kaanow/volthium_reader/hardware/datasheets/manifest.md

# Datasheet manifest

Local datasheet store for **every active BOM part** (CP1 gate, decisions D32).
Fetched via the parts-sourcing API `/datasheet` proxy where reachable; the rest
pulled manually. Read + interface-verified per D32.

| MPN | file | provider | source | sha256 (12) |
|-----|---|---|---|---|
| 0215001.MXP | 0215001.MXP.pdf (763K) | manual | user download 2026-07-01 | 6ea4fed8f791 |
| MSTBA 2,5/2-G-5,08 (1757242, J1 board header) | 1757242.pdf (1.4M) | parts-API datasheet endpoint | re-fetched 2026-07-30 (replaces the 2026-07-01 user download of the same Phoenix catalog PDF — catalog regeneration changes the hash; dims re-verified p.3: pitch 5.08, pin 1x1, hole 1.4) | 7a342188f10c |
| 2N7002LT1G (onsemi) | 2N7002_onsemi.pdf (2N7002L-D Rev 11) | digikey via API proxy 2026-07-17 | https://www.onsemi.com/pub/Collateral/2N7002L-D.PDF — **F51 fix: the prior 2N7002.pdf was Diotec's (wrong manufacturer for the ordered onsemi SKU); part re-pinned to the exact orderable 2N7002LT1G** (Mouser 863-2N7002LT1G, 76k stock, API 2026-07-17; DK LT1G variants zero-stock same query). IDSS ≤1.0 µA @ TJ=25 °C / ≤500 µA @ TJ=125 °C (60 V, VGS=0) — **25 °C is a test point, not a full-range max** | 11eb3cde5ed5 |
| 615008145521 | 615008145521.pdf (844K) | digikey | https://www.we-online.com/components/products/datasheet/615008145521.pdf | da03e4ed6257 |
| AP2112K-3.3TRG1 | AP2112K-3.3TRG1.pdf (737K) | digikey | https://www.diodes.com/assets/Datasheets/AP2112.pdf | ef8d376f2ec3 |
| B8B-PH-K-S | B8B-PH-K-S.pdf (100K) | digikey | https://www.jst-mfg.com/product/pdf/eng/ePH.pdf | 447624f4f2f7 |
| ESP32-S3-WROOM-1-N16R8 | ESP32-S3-WROOM-1-N16R8.pdf (1250K) | digikey | https://www.espressif.com/sites/default/files/documentation/esp32-s3-wroom-1_wroom-1u_datasheet_en.pdf | 27d71971da07 |
| LM5166YDRCR | LM5166YDRCR.pdf (3436K) | digikey | https://www.ti.com/lit/ds/symlink/lm5166.pdf?ts=1782455459808&ref_url=https%253A%252F%252Fwww.ti.com | 1817a5b4f779 |
| MF-R025 | MF-R025.pdf (1059K) | digikey | https://www.bourns.com/docs/product-datasheets/mf-r.pdf | ad20425ca080 |
| R-78E3.3-0.5 | R-78E3.3-0.5.pdf (628K) | digikey | https://recom-power.com/pdf/Innoline/R-78E-0.5.pdf | d3855b950078 |
| R-78HB12-0.5 | R-78HB12-0.5.pdf (1836K) | digikey | https://recom-power.com/pdf/Innoline/R-78HB-0.5.pdf | 457ccbb2825f |
| RJHSE-5380 | RJHSE-5380.pdf (102K) | digikey | https://cdn.amphenol-cs.com/media/wysiwyg/files/drawing/rjhsex380.pdf | 3254d85eaaa6 |
| RV-3028-C7 | RV-3028-C7.pdf (830K) | manual | user download 2026-07-01 | fb5a01874b3e |
| SMAJ12CA-13-F | SMAJ_Diodes.pdf (116K) | mouser (API proxy) | https://www.mouser.com/catalog/specsheets/ds19005.pdf — Diodes DS19005; p.1 ordering row names SMAJxxx(C)A-13-F (iter-23 F20: non-F variants Obsolete); p.2 device table VC 19.9 V @ 20.1 A | 70bd31105424 |
| SMAJ15A-13-F | SMAJ_Diodes.pdf (same file) | " | " — p.2 device table VC 24.4 V @ 16.4 A, matches D19/DR-15 coordination | 70bd31105424 |
| SMAJ33CA-13-F | SMAJ_Diodes.pdf (same file) | " | " — p.2 device table VC 53.3 V @ 7.5 A, matches the ~53 V clamp coordination (SS26 60 V, R-78HB12 72 V) | 70bd31105424 |
| THVD1400DR | THVD1400DR.pdf (1447K) | digikey | https://www.ti.com/lit/ds/symlink/thvd1400.pdf | 5ba9785d9fb8 |
| SS26-E3/52T | SS26-E3_52T.pdf (151K) | digikey | https://www.vishay.com/docs/88748/ss22.pdf | 4bcd8bc129f3 |
| TPS2116DRLR | TPS2116DRLR.pdf (2855K) | digikey | https://www.ti.com/lit/ds/symlink/tps2116.pdf | 5babd88afb84 |
| TPS3808G01DBVR | TPS3808G01DBVR.pdf (2034K) | digikey | https://www.ti.com/lit/ds/symlink/tps3808.pdf | 682abbc06a0c |
| USBLC6-2SC6Y | USBLC6-2SC6Y.pdf (117K) | manual | user download 2026-07-01 | c0352261dede |
| USB4085-GF-A | USB4085-GF-A.pdf (371K) | API proxy 2026-07-27 (display CP2 — battery J3 + display J-USB USB-C pinned to this GCT SKU) | https://gct.co/files/specs/usb4085-spec.pdf — **FAMILY-level product spec** (electrical/mechanical performance; contains no ordering grid, so it does NOT establish the -GF-A object by itself — F13; see the drawing row below for exact-object identity). VBUS = A4/A9/B4/B9 (5 A collective), GND = A1/A12/B1/B12 — matches the USB_C_16P symbol map | e5e6f4f67cca |
| USB4085-GF-A (exact drawing) | USB4085_drawing.pdf (197K, 3 pp) | direct fetch 2026-07-28 (F13 — browser-UA curl; gct.co serves HTML to bare curl) | https://gct.co/files/drawings/usb4085.pdf — GCT official part drawing WITH ordering grid: **"Dip Type, PCB Top Mount" (through-hole — the BOM's earlier "SMD" cell was wrong, F13), suffix decode GF = Gold Flash (Standard), A = Tape & Reel** → USB4085-GF-A fully identified. Matches the KiCad footprint (20 THT pads, 0 SMD) | 39afb82c5104 |
| NTR4171PT1G | NTR4171P_onsemi.pdf (NTR4171P/D Rev 3, Feb 2026) | digikey via API proxy 2026-07-17 | https://www.onsemi.com/pdf/datasheet/ntr4171p-d.pdf — **3V3-domain switches ×3 (2× channel + Q_exp; F61 replacement: DMG3415U was NRND)**: −30 V, −2.2 A; **RDS(on) max 150 mΩ @ −2.5 V / 75 mΩ @ −10 V** (the −2.5 V guaranteed row qualifies the direct 3.3 V GPIO drive); **VGS ±12 V** (≫ our 3.3 V drive); VGS(th) −0.7…−1.15 V; **IDSS ≤1 µA @ 25 °C / ≤5 µA @ 85 °C** (VDS −24 V — has an elevated-temp row, pessimistic at our −3.3 V). Lifecycle: onsemi page shows **Active** (WebSearch of the mfr page 2026-07-17; onsemi.com WAF-blocks the fetcher — Rev 3 Feb-2026 datasheet + onsemi-channel stock 11k/30k corroborate) | 9ce711ff393d |
| AQY212EH | AQY212EH_Panasonic.pdf (Panasonic GE DIP4 1-Form-A catalog, doc ASCTB126E, 2026.1) | **user upload 2026-07-18 (manufacturer-direct — replaced the octopart mirror; Panasonic host WAF-blocks the proxy)** | Panasonic Industry GE DIP4 1 Form A | — **Display-feed load switch SSR (F76)**: 1-Form-A, **load 60 V / 550 mA**, 5000 Vrms I/O isolation, Ron **0.85 Ω typ / 2.5 Ω max** (AQY212EH row, corrected iter-50 F79 — 0.25 Ω was the AQY211EH sibling), **off-state leakage ≤1 µA @ 25 °C only** (datasheet publishes NO hot max — 85 °C is an engineering estimate gated by a State-4 acceptance test, F83; non-amplifying), LED operate 1.2 mA typ / 3 mA max / turn-off min 0.4 mA, peak load 1.5 A/100 ms one-shot, rated −40…+85 °C. **AQY212EH = through-hole DIP4** (AQY212EHA is the SMD variant). DK 255-2963-ND / Mouser 769-AQY212EH, Active | d329b9729322 |
| MSTB 2,5/2-ST-5,08 (1757019) | 1757019.pdf (2400K) | manual | user upload 2026-07-01 | d849479aae64 |
| LCD1 Waveshare 4.2" e-Paper Module (B) | Waveshare-4.2-ePaper-B.pdf (3.9M — **subordinate bare-panel V2 manual only**, sha 32b126146869: SPI timing, panel specs, active area 84.8×63.6 mm; its p.7 shows the raw 24-contact FPC panel, not the ordered Module). **Module-object evidence (iter-23 F21):** Waveshare-42B-Module-productpage-2026-07-14.html (sha 077451eb4f2f, captured 2026-07-14 from https://www.waveshare.com/4.2inch-e-paper-module-b.htm — "What's on board" + box-contents list **"PH2.0 20cm 8Pin x1"**) + Waveshare-42B-Module-wiki-2026-07-14.html (sha e861c86f6e9f, captured 2026-07-14 from https://www.waveshare.com/wiki/4.2inch_e-Paper_Module_(B)_Manual — 8PIN pin-correspondence tables **VCC/GND/DIN/CLK/CS/DC/RST/BUSY**; FAQ caps cable extension at 20 cm). **Verify at ordering:** the in-box PH2.0 cable's far-end termination — the PH↔PH module↔board cable is a separate BOM purchase (ASPHSPH24K102-class) | 077451eb4f2f / e861c86f6e9f / 32b126146869 |
| 8125SHZBE (BTN1 battery override) | CK_8020_series.pdf (29 pp) | littelfuse via API proxy | https://www.littelfuse.com/assetdocs/littelfuse-c-k-pushbutton-8020-series-datasheet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 — Contact Rating: "B contact material (8X25 Models): 0.4 VA max. @ 20 V AC or DC maximum"; function table 8125 = ON MOM., terminals 1-3 rest / 1-2 pressed; S=plunger, H=0.250" flat bushing, Z=solder lug, E=epoxy seal | 8e748f0b8502 |
| 3517 | Keystone_3517.pdf (170K) | manual | https://www.keyelco.com/userAssets/file/K75p52.pdf | 441b810381ac |
| 970050354 | Wurth_970050354_standoff.pdf | digikey (API proxy) | https://www.we-online.com/components/products/datasheet/970050354.pdf — WA-SBRII brass spacer stud, M3 inner thread, L 5 mm, SW5, nickel | 5530b6984184 |
| 53398-0871 | Molex_53398-0871_PicoBlade_vert.pdf | molex (API proxy) | https://www.molex.com/pdm_docs/sd/533980871_sd.pdf — PicoBlade 1.25 mm, 8-ckt, SMT vertical, tin. **The drawing carries no current rating** — rating comes from the header-system product spec **PS-51021-024** (row below; F53 fix — PS-51021-009 is the wire-to-wire sibling and does not list 53398). R/A alt 53261-0871 (Molex_53261-0871_PicoBlade_RA.pdf, sha 6e1b0968c9ed) | 642bc09ea605 |
| 53398/53261 + 51021/50079/50058 system | Molex_PS-51021-024_PicoBlade_WB_system_spec.pdf (Rev AD, 2022-06-03) | user upload 2026-07-17 | official URL (F59, full): https://www.molex.com/content/dam/molex/molex-dot-com/products/automated/en-us/productspecificationpdf/510/51021/PS-51021-024-001.pdf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 (reviewer-opened iter-35; direct fetch WAF-blocked from this host, hence owner upload) — **PRODUCT SPECIFICATION FOR PICOBLADE 1.25 W/B SMT** (F53): scope p.1 lists terminals 500588\*00/500798\*00, housing 51021\*\*00, **vertical headers 53398\*\*71** (natural; ours) /\*\*76, r/a 53261\*\*71/\*\*27. Ratings p.2: **1.0 A max AWG 26/28/30, 0.8 A AWG 32; 125 V; −40…+105 °C**; 8-ckt derating reference 1.5 A (AWG 26/28) / 1.0 A (AWG 30/32) @ 30 °C rise, marked REFERENCE ONLY | b7d3ec9b74b9 |
| CRCW120675R0FKEAHP | Vishay_CRCW_HP.pdf (150K, doc 20043 rev 17-Mar-2026) | vishay (API proxy 2026-07-19) | https://www.vishay.com/docs/20043/crcwhpe3.pdf — **Pulse-Proof, High Power** thick-film chip R. p.1: 1206-HP rated **P70 = 0.75 W** (the separate 1.5 W is only at terminal-part temp 105 °C), Umax 200 V. p.8 **§8.1 short-term-overload uses P70**: 2.5·√(P70·R)/5 s → **4.69 W/5 s** guaranteed. p.5 single-pulse curve. **R_inrush = 2× 75 Ω in series (F86): 2.87 W each < 4.69 W** (a single 150 Ω 1206-HP would see 5.74 W). | bdd4e4b9b924 |
| 0451.080MRL | Littelfuse_451_453.pdf (480K, rev 12/01/25) | littelfuse (API proxy 2026-07-19) | https://www.littelfuse.com/assetdocs/littelfuse-fuse-451-453-datasheet — 451/453 Nano2® SMF **Very-Fast-Acting** fuse. p.1: 200%→**5 s max** opening. p.2 (**.080 row**): **125 V**, **50 A @125 VDC** interrupt, Rcold 4.05 Ω, **nominal melting I²t 3.3e-4 A²s**. **F2 switched-branch fault clear (80 mA, F87 — 62 mA's pulse I²t ratio was too high).** | 399d3cc9da99 |

## Still needed (CP1 datasheet gate)

**Gate re-opened 2026-07-14 (user audit): the 2026-07-01 "CLOSED — every
active part" claim was false.** RP3502MABLK (BTN1) had no stored
datasheet; when fetched and read it exposed the dry-circuit gap that
reviewer iter-23 F22 then escalated — the part is **superseded by C&K
8125SHZBE** (gold contacts, published 0.4 VA @ 20 V logic-level rating;
see the active-table row). D-OPEN-13 is moot with the supersession
(unsealed accepted for the IP5x indoor enclosure).

Remaining gaps (parts with a chosen MPN but no stored datasheet): none.

- ~~5×20 mm fuse clip~~ — **resolved 2026-07-14 (user-caught).** The BOM's
  SKUs "DK F1465-ND / Mouser 530-31MJ005H" were **phantoms** — zero hits on
  Mouser, DigiKey *and* Octopart via the parts API, and nothing on the
  retailers' own sites (user check). Replaced with **Keystone 3517**
  (5 mm/3AG PC-mount snap-in clip w/ end stops, tin-plated brass,
  UL E354010): DK **36-3517-ND** (85,711 in stock, Active) / Mouser
  **534-3517** (54,324 in stock), ~CA$0.48 ea. Datasheet fetched, read,
  verified: 5 mm fuse diameter ✓ (fits the 5×20 0215001.MXP body), THT
  snap-in legs, end stops (with-end-stop parts are the UL-recognized
  ones), rated ≥ 6.3 A ≫ 1 A fuse. Optional cover = 3517C.

Parts still at `_verify_` (MPN not yet chosen — D32 applies when chosen):
L1 buck inductor, USB-C receptacles (J3 battery / J-USB display),
display tactile buttons BTN1–3 (plunger height locked at CP3/CP5).

## Proposed CP1-delta additions (D36/D37) — datasheets on file, fold into the active table at CP2

Not yet in the active table above (these parts are in the RS-485 /
expansion design docs, pending the CP1-delta review; they move to the
active table + `cp1_bom.md` when CP2 folds them in). Datasheets stored,
read, and interface-verified now so the D32 gate closes when they land.

| MPN | file | provider | source | sha256 (12) | read-verified |
|-----|---|---|---|---|---|
| ADM2587EBRWZ | ADM2582E_2587E.pdf (1291K) | user upload 2026-07-16 | analog.com/media/en/technical-documentation/data-sheets/adm2582e-2587e.pdf (Rev H) | 77a52a9e6036 | 2500 Vrms iso (1 min); CMTI >25 kV/µs; ±15 kV ESD on bus pins; open/short fail-safe RX (external bias unnecessary, p.15); 3.3 V op; **ADM2587E = 500 kbps** slew-limited; **ICC 90 mA @ 3.3 V/100 Ω** (72 mA is the 5 V row — iter-30 F28 fix); supplies ~15 mA on VISOO; isoPower support net p.8/p.17 → design §3 |
| SM712.TCT (Semtech) | SM712_Semtech.pdf (557K) | user upload 2026-07-16 | Semtech SM712 Final Rev 6.0 (semtech.com) | 6deb75310ebe | **F29 CLOSED 2026-07-16 — correct-manufacturer Semtech doc** (was briefly SMC's, wrong mfr). VRWM 12/7 V; VBR 13.3/7.5 V; **VC 20 V/10 V @ 5 A** (26 V @ 21 A); SOT-23, asymmetric RS-485 (−7/+12). Matches ordered 947-SM712.TCT / SM712CT-ND. **DNP — port intentionally unprotected (F44):** VC 20 V > ADM2587E +14 V abs-max and no published injection rating exists to size a series R against; no coordinated network is claimed |
| 51021 wire-to-wire system (scope: 51021 housing + 50079/50058 terminals + 51047 plug — **does NOT list 53398**) | Molex_PS-51021-009_PicoBlade_product_spec.pdf (393K) | digikey via API proxy 2026-07-16 | https://www.molex.com/pdm_docs/ps/PS-51021-009.pdf | 1213f6f54215 | **Wire-to-WIRE product spec** (F53 scoping: retained only for what it covers — the 51021/50079 mate side as used in cable assemblies; the header-system claims cite PS-51021-024 above). §3 ratings 1.0 A max (AWG 26/28/30), 0.8 A (AWG 32), 125 V, −40…+85 °C |
| TCAN332DR | TCAN332.pdf (1645K, SLLSEQ7F Rev May 2025) | parts-API /datasheet proxy 2026-07-22 | https://www.ti.com/lit/ds/symlink/tcan332.pdf | aeda66d5fca9 | U7 Xanbus CAN transceiver (DR-31); pinout + supply-current + unpowered-high-Z interface-verified (pp.1/4/6); **p.5 abs-max V(BUS) ±14 V + on-chip bus ESD ±25 kV HBM / ±12 kV IEC contact (F03 basis)** |
| NUP2105LT1G (onsemi) | NUP2105L_onsemi.pdf (13 pp, Rev 12 June 2026) | parts-API /datasheet proxy 2026-07-24 | https://www.onsemi.com/pdf/datasheet/nup2105l-d.pdf | bf93369469d4 | D2 candidate CAN TVS, **now DNP (CP2 F03)**: p.2 V_RWM 24 V, V_BR 26.2–32 V, V_C 40/44 V max @5/8 A — cannot bracket TCAN332's ±14 V; kept on file as the evidence for the DNP call. (Note: the bare "NUP2105L" MPN resolves to a Diotec second-source PDF at DigiKey — query the orderable NUP2105LT1G for the onsemi doc) |
| ESP-Prog (tool, not BOM) | ESP-Prog_SCH_V2.1.pdf (609K, SCH_ESP32-PROG_V2.1_20190709) | espressif direct 2026-07-24 | https://dl.espressif.com/dl/schematics/SCH_ESP32-PROG_V2.1_20190709.pdf | ab1f074c7b6c | J5 Program-pinout ground truth (F01): J3/J5 2×3 = 1 ESP_EN / 2 VDD / 3 ESP_TXD0 / 4 GND / 5 ESP_RXD0 / 6 ESP_IO0; **FT_TXD→0R→ESP_RXD0, FT_RXD→0R→ESP_TXD0** (names are target-perspective — pin 3 takes the target's TXD) |
| MPZ2012S601AT000 | TDK_MPZ2012S601AT000.pdf (MPZ2012 type catalog, 20190424) | parts-API /datasheet proxy 2026-07-24 | https://product.tdk.com/system/files/dam/doc/product/emc/emc/beads/catalog/beads_commercial_power_mpz2012_en.pdf | c8b428baaacf | L10–L13 iso beads. p.1 table: S601A = 600 Ω ±25 % @100 MHz, DCR 0.100 Ω max, **rated 2 A** (derates above 85 °C). p.2 Z/f curve (S601A): **~600 Ω near the 150–200 MHz peak, falling to ~300–400 Ω by ~400 MHz** — DR-30 bead-impedance data: no MPZ2012 reaches the ADM2587E p.17 "~2 kΩ" guidance (family max = S102A 1 kΩ/1.5 A/0.15 Ω, an available same-size step-up at BOM-lock) |
| C1206C102KDGACTU | KEMET_C1206C102KDGACTU.pdf (KEM_C1009 C0G HV SMD, 12/16/2024) | parts-API /datasheet proxy 2026-07-24 | https://yageogroup.com/content/datasheet/asset/file/KEM_C1009_C0G_HV_SMD | 46031e2efdb6 | C28/C38 C_stitch. High-Voltage C0G series doc: 500 V–10 kV DC ratings incl. **1 kV 1206**, −55…+125 °C, ±30 ppm/°C — the 1 kV/C0G claims in the BOM row are this doc's |
| 61200621621 | Wurth_61200621621.pdf (WR-BHD male box header drawing, rev 002.001 2026-07-07) | parts-API /datasheet proxy 2026-07-24 | https://www.we-online.com/components/products/datasheet/61200621621.pdf | 6474a7ec48fc | J5 ESP-Prog Program header (F01): 6-pin 2.54 mm shrouded/keyed box header, **standard IDC odd/even numbering (1/3/5 one row, 2/4/6 other — matches Conn_02x03_Odd_Even + the ESP-Prog ribbon 1:1)**, THT, hole pattern p.1. **CP3 note: set key-notch orientation at placement so ribbon pin 1 = our pin 1** |

## Retired (in store history, not used)

- SI2309CDS_Vishay.pdf (feb0974dd371), MMBT5551_onsemi.pdf (3ae47cf6f802),
  BZX84C12LT1G.pdf (f9818d9dfc03) — retired iter-48 (F76): the discrete
  Q1 P-FET + Q2 BJT gate-driver + Zener were replaced wholesale by the
  AQY212EH PhotoMOS SSR (no discrete driver could be datasheet-guaranteed
  OFF at temperature — see decisions.md D19). PDFs kept as F57/F68/F72
  evidence; can be removed at the next housekeeping pass.

- ZXMP6A13FTA.pdf (bb474f827be4) — retired iter-38 (F56/F57): part NRND,
  no guaranteed RDS(on) at a 3.3 V gate drive → Si2309CDS (Q1) +
  DMG3415U (3V3 switches).
- DMG3415U_Diodes.pdf (3863b974014c) — retired iter-40 (F61): Diodes
  marks it **NRND** despite live distributor stock (the distributor
  "Active" field is stale — G3 lesson) → onsemi **NTR4171P** for the
  three 3V3-domain switches. Q1's Si2309CDS is unaffected.

- **RP3502MABLK** (BTN1) — retired at reviewer iter-23 F22 (2026-07-14):
  AC power switch (3 A @ 120 VAC) with **no published dry-circuit /
  minimum-load rating**; unqualifiable for the 3.3 V/µA override input,
  and the C11 100 nF discharge (0.54 µJ) is not a vendor wetting
  qualification. Superseded by **C&K 8125SHZBE** (explicit "0.4 VA max
  @ 20 V" low-level rating, gold contacts). PDF removed.

- **SMAJ12CA.pdf (Bourns) / SMAJ15A.pdf + SMAJ33CA.pdf (one Littelfuse
  family PDF stored under two names — identical sha)** — retired
  2026-07-14 audit: the datasheets on file were from manufacturers we
  don't order (BOM DK SKUs are **Diodes Inc** SMAJxxCA-13). Replaced by
  the single Diodes DS19005 family datasheet matching the orderable
  parts; per-variant VC values re-read from it and confirmed identical
  to the values used in the D19 coordination analysis. PDFs removed.

- **1727010** (Phoenix MKDS 1/2-3,81) — was mistakenly specced as the J1 plug; it's a 3.81 mm board-mount screw terminal, wrong series/pitch. Replaced by 1757019 (2026-07-01, D32 catch). PDF removed.
- **TPS389030DSER** (U4 UVLO supervisor) — WSON 1.5×1.5 leadless; repackaged to **TPS3808G01DBVR (SOT-23-6, leaded)** for hand-assembly (2026-07-01, D33/DR-24). Functional superset at ~same Iq. PDF removed.
- **SN65HVD3082EDR** (U2/U3 RS-485 transceiver) — was a 5 V part being run outside its recommended VCC = 4.5–5.5 V window on V3V3 (reviewer iter-8 F05). Superseded by **THVD1400DR** (D34, revised iter-10 F08). PDF retained temporarily in `hardware/datasheets/SN65HVD3082EDR.pdf` as the record of the F05 evidence — can be removed at the next housekeeping pass once the review record is archived.
- **ISL3175EIBZ** (U2/U3 RS-485 transceiver) — iter-8 first-cut replacement for SN65HVD3082E, but iter-10 F08 correctly caught that its 10 nA shutdown Iq was *typical* and the maximum is 12 µA (1200× higher). Superseded by **THVD1400DR** on max-to-max comparison. PDF retained temporarily in `hardware/datasheets/ISL3175EIBZ.pdf` as the record of the iter-10 max-to-max evidence — can be removed once the review record is archived.
