kaanow/volthium_reader/hardware/reviews/DESIGNER.md

# Designer instructions (Claude) — read this first

> **The standing standard is [`SOP.md`](SOP.md)** — governing principles + the
> gates + tooling, distilled and forward-looking. This file is the
> *operational playbook* (wake loop, packet mechanics, KiCad specifics); SOP.md
> is *what "good" means*. Read SOP.md before any CP.

You are Claude, the design agent for the `volthium_reader` PCB design
pass. This file is the entry point. **Read it fully before touching
anything else, every time you're triggered.**

The system runs on a semaphore at [`SEMAPHORE.yaml`](SEMAPHORE.yaml) —
you and agent-reviewer (the reviewer) take turns. The user manages timed
triggers (Cursor for agent-reviewer; `/loop` or manual prompts for you).

## TL;DR

On every wake:

0. **Sync the skills** (standard ops, both agents): `git -C
   <skills clone> pull` and read any SKILL.md whose version changed
   since your last turn — released lessons bind the next turn's work.
1. `git pull origin <current_branch>` (read from SEMAPHORE.yaml).
2. Read [`SEMAPHORE.yaml`](SEMAPHORE.yaml).
3. Branch based on `state`:
   - `claude_turn` → do work (§4); push; flip state to `reviewer_turn`.
   - `reviewer_turn` → not your turn; exit cheap.
   - `user_turn` → not your turn; exit cheap.
   - `done` → project complete; nothing to do.
4. Tell the user one sentence about what you did and what's next.
5. Stop. Don't loop on your own — the user's timer triggers the next
   cycle (unless they invoked `/loop`, in which case
   `ScheduleWakeup` is fine).

## 0a. Engineering correctness is a gate (D17)

Before readability, the circuit has to be *right*. Run the
**engineering design review** (`ENGINEERING_REVIEW.md`) as a required
gate at **CP1 (architecture)** and **CP2 (schematic)** — it is on equal
footing with ERC and the readability/geometry audits, and a schematic
does **not** pass CP2 on ERC + readability alone (D17). For every net /
block: derive the clean-sheet-correct circuit, then measure the design
against it — part-class fit, **coordination** (protective parts must
bracket what they protect, e.g. TVS clamp < downstream abs-max),
derating, polarity, worst-case margin. Fix clear errors; log judgment
calls and human-decision items in `DESIGN_REVIEW_ITEMS.md`. ERC-clean +
DRC-clean + readable is necessary, not sufficient — it proves the
schematic is legal and legible, not that it is the right circuit (the
CP6 DR-1/DR-2 lesson).

## 0. Documentation readability is a first-class deliverable (D11 / D16)

Every PDF, schematic, render, BOM, and assembly drawing you commit
must satisfy [`decisions.md` D11](../layout/decisions.md#d11--all-committed-documentation-must-be-engineer-readable) —
engineer-readable bar — and the top-level
[`decisions.md` D16](../layout/decisions.md#d16--schematic-goal-is-a-human-can-read-it-and-understand-the-design)
goal:

> **A human can read this schematic and understand the design.**

Read D11 *and* D16 in full before generating any document. Treat
readability as equal to correctness, not a side effect. agent-reviewer
enforces this in review. D16 revokes the previous "defensible
exception" carve-out for overlaps: **any** overlapping text, symbol,
label box, chevron, pin name, pin number, junction, wire, or
graphical annotation is to be revised until it is not present. No
exception path.

If a programmatic generation strategy produces machine-valid but
human-unreadable output (overlapping symbols, label-spaghetti
without wires, blank title blocks), it does not pass — fix the
generator, do not ship and document a residual.

### Schematic-readiness checklist (D16 acceptance bar)

Before flipping the semaphore to `reviewer_turn` on any iteration that
touches a schematic, all of the following must hold. These are the
operational items behind the D16 goal; future PCB projects forking
this template inherit them.

1. **Real interconnect wires within every functional cluster.** Two
   components in the same sub-circuit (a cap and the IC pin it
   decouples; an I²C pull-up and the bus it pulls up; a
   bootstrap cap and the regulator's BST/SW pins; a button and its
   pull-up and debounce cap) are connected by wires drawn on the
   schematic, not by sharing a `GlobalLabel` net name. `GlobalLabel`
   is reserved for power rails (when not handled by a power-port
   symbol — see #2) and for genuine cross-cluster signals.
   Three corollaries (the "wiring-discipline" guidelines):
   - **(a) Wire nearby same-net labels instead of using two flags.**
     If two `GlobalLabel`s carry the SAME net name and sit close
     together (the geometry audit's same-net advisory flags pairs
     within ~20 mm), connect them with a wire and drop one flag —
     UNLESS the connecting wire would itself cross a symbol or
     another wire (prefer a wire only when the wire is not worse).
     Flags are for genuinely far-apart connections.
   - **(b) Datasheet-mandated parts belong IN the IC's block, wired
     directly.** Decoupling/bypass caps, bias resistors, bootstrap
     caps, etc. that a datasheet ties to an IC are placed next to
     that IC and connected by wires (not label-name matching), so
     the sheet reads as logical blocks whose members are wired
     together and whose blocks are separated by whitespace.
   - **(c) Minimise wire crossings; keep crossings ≠ connections.**
     A connection carries a junction dot (KiCad renders it
     automatically where wires electrically join); a crossing has
     none. Route to avoid crossings where reasonable; the geometry
     audit reports the free-crossing count as an advisory to drive
     this down.
2. **Stock KiCad power-port symbols for power rails.** GND uses the
   ground-triangle glyph; supply rails use the upward-arrow glyph
   keyed to the rail name (`+3V3`, `+12V`, `+24V`, or a project
   power-port symbol for named intermediate rails). A reader sees
   "this pin goes to GND" via the standard ground symbol, not by
   reading the text inside a flag-shaped label.
3. **Pin numbers visible on every IC.** If the library symbol has
   multiple power pins sharing one library coordinate (e.g. ESP32
   GND pins 1/40/41, or DS3231M GND pins 5..13), fix it at the lib
   level — either consolidate the bundle via `(alternates)` or
   relocate the duplicates — so pin numbers can render without
   stacking on top of each other. Hiding pin numbers on the
   instance is a last resort and forfeits one of the schematic's
   primary uses (cross-reference to the footprint).
4. **Functional-block visual grouping with primary signal flow.**
   Each sub-circuit (power input + protection, regulator, MCU,
   RTC, RS-485, buttons, dev headers, …) lays out as a tight
   cluster with members within a few grid units of each other and
   clear whitespace separating it from neighbouring clusters.
   Signal flow inside the cluster runs left-to-right or
   top-to-bottom; supplies enter from the top edge of the cluster,
   GND exits from the bottom.
5. **Zero on BOTH readability audits.** Two complementary audits run
   automatically at the end of every `build_schematics.py` run (the
   "audit gate") and must both report PASS — the build raises a
   non-zero exit otherwise. They are complementary because each is
   blind to what the other catches:
   - **Strict text-overlap audit**
     (`hardware/reviews/tools/schematic_visual_audit.py --strict`):
     every text-vs-text bbox pair (pin numbers, refs, values, label
     text). SAME-TEXT identical-bbox pairs from KiCad's PDF stroke-font
     rendering still count — fix the font, layout, or generator. **No
     "documented residual" path.**
   - **Geometric collision audit**
     (`hardware/reviews/tools/label_body_audit.py`): every *graphics*
     pair the text audit cannot see — `GlobalLabel` flag ∩ component
     body, **body ∩ body** (e.g. a power-port ground-triangle glyph
     landing on a resistor body), flag ∩ flag, flag ∩ ref/value, and
     the **wire classes**: a wire running through/into a component
     body, a wire crossing a flag's text core (a "strike-through" —
     the connection-zone at the chevron tip is excluded so a normal
     pin connection doesn't false-trigger), and a wire through ref/
     value text. It also reports advisories: same-net label pairs
     that should be wired (guideline a) and the free wire-crossing
     count (guideline c).
   Net lines are drawn at a wider stroke (`WIRE_WIDTH`, 10 mil) than
   KiCad's faint 6 mil default so they read clearly.
   Text-vs-text alone is NOT sufficient: a flag body or a power-port
   glyph can sit squarely on a component symbol with zero text overlap.
   That blind spot shipped twice (iter-9 chevron regressions, iter-11
   GND-port-on-resistor) before the geometric audit existed — never
   judge readability from the text audit alone.

A scripted audit is still worth running first — it's a cheap filter
for symbol coordinate collisions, duplicate placements, and obvious
spacing problems. The visual gate below is on top of that, not
instead of it. **And inspect visually at high DPI per-region**
(PyMuPDF `Matrix(12–14)` clipped to one grid cell), never from a
full-page render — text is illegible at full-page scale, so a
full-page image cannot confirm or deny readability. When showing the
user, send high-DPI region crops, not a shrunk full page.

When a fix introduces a *new* overlap (common — moving a label clears
one collision and creates another), the audit gate catches it on the
next build. Loop: edit → rebuild → read the gate → fix the new
findings → rebuild, until the gate reports PASS with 0 findings.

### Operational checklist — before claiming D11 #0 or #5 PASS

D11 explicitly requires a visual inspection (see D11 §"Visual
inspection protocol"). A script alone is not a sign-off. On every
iteration that touches a rendered PDF, do **all** of the following
before flipping the semaphore to `reviewer_turn`:

1. Render the PDF(s) and open them at **100 % zoom** in a real PDF
   viewer (not KiCad, not a PNG preview).
2. Identify every **dense region** on each sheet: every IC, every
   connector with ≥4 pins, every cluster of ≥3 components within
   ~20 mm, every power/ground rail meeting ≥3 pins. For a typical
   two-IC sheet this is 6–12 regions.
3. Take a 100 %-zoom screenshot of each dense region. Save them
   under `hardware/reviews/visual_inspections/<cp_slug>/iter<N>/`
   with descriptive filenames.
   **Also copy the source PDF(s) used for the inspection into**
   `hardware/reviews/visual_inspections/<cp_slug>/iter<N>/snapshots/`
   so each iter's PDF is frozen alongside the PNGs (the
   `hardware/outputs/*/schematic.pdf` files are overwritten on
   every build; per-iter snapshots remove the need to traverse git
   history to recover the PDF that was inspected).
4. In the active CP review packet, add a new section:
   ```
   ## D11 visual inspection — iter <N>
   ### Region: <name>
   ![<name>](visual_inspections/<cp_slug>/iter<N>/<file>.png)
   Read every piece of text in this region. Findings: <none> | <list>.
   ```
   …one block per region.
5. If **any** region's findings are non-empty, the document does
   not pass D11. Fix and re-render before flipping the semaphore.
   Overlap of any schematic objects (text, symbols, wires, labels,
   pin metadata, junctions, annotations) is a fail unless you include
   an explicit, defensible exception in the packet and the region
   remains unambiguously readable at 100 % zoom.
6. **Never** claim criterion #0 or #5 PASS solely from scripted
   audit output. That's the documented iter-36 failure (see D11
   "Documented failure"); don't repeat it.

A scripted audit is still worth running first — it's a cheap filter
for symbol coordinate collisions, duplicate placements, and obvious
spacing problems. Just don't confuse it with the visual gate.

### Reviewer's complementary duty

agent-reviewer must read the screenshots embedded in the packet, not just
the audit script's PASS line. agent-reviewer is authorized — and required —
to flag any text in those screenshots that the designer claimed was
readable but isn't. A scripted-audit-only review is itself a D11
enforcement failure.

Additionally, agent-reviewer now generates independent reviewer-owned screenshot
evidence each CP2+ turn from the committed PDFs and stores it under:
`hardware/reviews/visual_inspections/<cp_slug>/iter<N>/reviewer/`.
Designer-provided screenshots are still required for designer sign-off,
but agent-reviewer's final D11 verdict may rely on reviewer-owned screenshots as the
authoritative review artifact.
agent-reviewer's standard tooling entrypoint is:
`.venv/bin/python hardware/reviews/tools/schematic_visual_audit.py --cp-slug <cp_slug> --iter <N> --strict`

### D13 — Binary per-criterion scorecard required at sign-off

D11 sets the principle; [`decisions.md` D13](../layout/decisions.md#d13--explicit-acceptance-criteria-operationalizing-d11) enumerates the
specific criteria (F-S-\*, SR-\*, F-P-\*, PR-\*) that must be evaluated
in every review packet. Before flipping the semaphore to `reviewer_turn`,
every packet must include a scorecard table at the SIGN-OFF section:

| Criterion ID | Status (PASS or FAIL) | Evidence / justification |
|---|---|---|
| F-S-1 | PASS | ERC clean: 0 errors, 0 warnings; see hardware/outputs/.../erc.rpt |
| SR-1 | PASS | Five functional blocks visible in screenshot: ... |
| PR-3 | PASS | silk_overlap count = N, per-instance justified below |
| ... | ... | ... |

**Binary only.** No PARTIAL, no PASS\*, no PASS-with-caveat. Each row
is either PASS or FAIL. APPROVED requires every applicable row PASS.

The applicable criteria per CP phase are listed in D13's "Enforcement"
section. When in doubt, include the row and explicitly mark it FAIL
with the missing-evidence reason — better than omitting it.

## 1. The project in 30 seconds

Same as REVIEWER.md §1. Two PCBs (battery-side + display-side), power-
first design, JLCPCB qty 5 bare PCBs, hand-soldered. Background:
[`docs/production_design.md`](../../docs/production_design.md),
[`docs/hardware/`](../../docs/hardware/),
[`../layout/decisions.md`](../layout/decisions.md).

## 2. The six checkpoints (your perspective)

| CP | Phase | What you produce |
|----|---|---|
| 1  | Design baseline | Per-board layout docs, BOM, decisions log |
| 2  | Schematic capture | KiCad 10 `.kicad_sch`, ERC clean, PDF + netlist export |
| 3  | Placement (battery-side) | `battery_side.kicad_pcb` with all footprints placed, rendered PNGs |
| 4  | Placement (display-side) | `display_side.kicad_pcb` with all footprints placed, rendered PNGs |
| 5  | Routing + DRC | Fully-routed `.kicad_pcb` files, DRC zero errors, copper pours |
| 6  | Fab-ready | Gerbers, drill, position, BOM CSV, fab checklist, PCB STEP for the user's faceplate work |

CP4 was inserted between CP3 and routing-drc per [`decisions.md` D12](../layout/decisions.md#d12--cp-renumber-display-side-placement-inserted-as-cp4) — display-side placement deserves its own single-concern packet, not a fold-in to the routing CP. See D12 for rationale.

One feature-branch per CP: `hw/cpN-<slug>`. One PR per CP. Squash-merge
to `main` when agent-reviewer APPROVES.

## 3. Decision tree on wake

```
read SEMAPHORE.yaml
│
├─ state == claude_turn?
│   │
│   ├─ iteration > max_iterations_per_cp?
│   │   → set state: user_turn ("stuck"), commit semaphore, push, exit
│   │
│   ├─ read active_packet (cpN_*.md)
│   │
│   ├─ sign-off line says APPROVED?
│   │   → §5: merge PR + advance to next CP
│   │
│   ├─ sign-off line says NEEDS CHANGES or REJECTED?
│   │   → §4: address findings
│   │
│   └─ no sign-off line yet (first turn on a CP)?
│       → §6: do initial CP work (when a new CP is starting)
│
├─ state == reviewer_turn?
│   → print "Not Claude's turn"; exit
│
├─ state == user_turn?
│   → print the `note` field; ask user what they need; exit
│
└─ state == done?
    → print "Project complete"; exit
```

## 4. Addressing review findings (NEEDS CHANGES / REJECTED)

For each finding in the latest §8.N (or §8) of the active packet:

1. Decide the response:
   - **Agree** → make the change in the relevant file (cp*.md,
     decisions.md, BOM, KiCad files, etc.).
   - **Disagree** → in the RESOLVED entry, give a concrete reason and
     a counter-proposal. agent-reviewer either accepts (next iteration) or
     escalates.
   - **Defer** → if it's a CP-out-of-scope concern, document it as a
     CP<N> task in the relevant doc + RESOLVED entry.

2. Append a `RESOLVED — Finding NN` entry to a new `## 9.M Claude's
   responses (iteration <M>)` section in the review packet.

3. Update SEMAPHORE.yaml: `state: reviewer_turn`, increment `iteration`,
   `last_updated_by: claude`, write a `note` summarizing what you did.

4. Stage + commit + push (§7).

## 5. Acting on APPROVED — advance to next CP

When agent-reviewer's latest sign-off says `REVIEW COMPLETE: APPROVED` for
the current CP:

1. Confirm `gh pr view <branch>` is open and ready.
2. Merge the PR (squash + delete branch):
   ```bash
   gh pr merge "$(git symbolic-ref --short HEAD)" --squash --delete-branch
   ```
3. Sync local main:
   ```bash
   git checkout main && git pull origin main
   ```
4. **If current_cp == 6** (fab-ready APPROVED):
   - Set SEMAPHORE state to `user_turn` with note
     "CP6 APPROVED. Renders and Gerbers in `hardware/outputs/`. User:
     review the final render, then place the JLCPCB order. After
     order placed, flip state to `done` (or back to `claude_turn` if
     you want me to assemble shipping/handoff docs)."
   - Commit + push semaphore on a new branch (or to main, your call).
   - Done for this turn.
5. **Else** (CP1–5 APPROVED): open the next CP.
   - Create branch: `git checkout -b hw/cp<N+1>-<slug>`
   - Do the next CP's initial work (see §6).
   - Open a PR with `gh pr create ...`
   - Update SEMAPHORE: `current_cp: <N+1>`, `current_branch: hw/cp<N+1>-...`,
     `active_packet: hardware/reviews/cp<N+1>_*.md`, `iteration: 1`,
     `state: reviewer_turn`, write `note`.
   - Commit + push the new branch.
   - Stop.

The slug per CP:

| CP | Branch slug |
|----|---|
| 1  | cp1-design-baseline |
| 2  | cp2-schematic-capture |
| 3  | cp3-placement |
| 4  | cp4-display-placement |
| 5  | cp5-routing-drc |
| 6  | cp6-fab-ready |

## 6. Doing initial CP work (when starting a fresh CP)

Each CP's work is:

- **CP2**: Generate `.kicad_pro`, `.kicad_sch`, populate parts +
  nets per the CP1 baseline. Run `kicad-cli sch erc`. Export PDF.
  Generate netlist. Build the CP2 review packet
  (`cp2_schematic_capture.md`) following the same shape as CP1's.
- **CP3**: Place battery-side footprints in `battery_side.kicad_pcb`.
  No routing yet. Render top + bottom PNGs. Build `cp3_placement.md`.
- **CP4**: Place display-side footprints in `display_side.kicad_pcb`.
  No routing yet. Render top + bottom PNGs. Build
  `cp4_display_placement.md`. Same placement-strategy and DRC-clean
  bar as CP3, applied to the second board.
- **CP5**: Route both boards, do copper pours, run DRC. Render. Build
  `cp5_routing_drc.md`.
- **CP6**: Export Gerbers, drill, position file, BOM CSV. Export
  PCB STEP file (user needs this for the faceplate). Build
  `cp6_fab_ready.md` with a pre-fab checklist.

When done, hand back to agent-reviewer via `state: reviewer_turn`.

## 7. Commit + push protocol

**Before every semaphore flip (D35 gate — no exceptions):**

```bash
python3 hardware/reviews/tools/doc_consistency_check.py
python3 hardware/reviews/tools/handoff_check.py   # CP3+: rebuilds every
# generator and fails on ANY committed-artifact drift, untracked
# deterministic artifact, or stale packet hash. Run it AFTER committing
# — it hashes HEAD blobs, not worktree bytes (CP3 F01/F05/F06). Packet
# hashes = git blob sha256 (worktree bytes lie on autocrlf clones).
```

**Host-limited acceptance (CP3 F10).** A gate whose pass depends on a
host you cannot exercise (the reviewer's Windows box, a fab's DRC) is
NOT accepted by your clean local run. Say so in the packet, state what
you did verify (poison tests with the platform branch forced, plus
unchanged-output proof), and treat the reviewer's acceptance run as the
gate's real pass. Never write "CLEAN" for a host you didn't run on.

Better still, **stop guessing and invite a patch**: write `HOST-LIMITED:
invites reviewer patch` in the finding response and let the reviewer fix
it on the host where it reproduces
([`REVIEWER_PATCH_POLICY.md`](REVIEWER_PATCH_POLICY.md)). Your duties
then: re-review their patch like any suggested fix (verify the premise;
in CP3 iteration 6 this caught two writers the patch missed), then sign
off in the packet with `RPA-ACCEPTED: <finding> <sha>`. `handoff_check`
fails while any reviewer patch is unaccepted, and
`reviewer_patch_check.py` enforces the scope — including the zero-delta
invariant, so a "host fix" can never smuggle in a design change.

Exit 0 required. It re-checks the append-only registry of every token
this project has ever superseded, and executes D32 (datasheet manifest ↔
PDFs ↔ canonical BOM) as code. If your change superseded a part, value,
or policy token, **add it to the tool's SUPERSEDED registry in the same
commit** — that registry entry is part of the swap, not an optional
extra. (Origin: 2026-07-14 user audit; SOP G5.)

**Facts carry source pointers (2026-07-14 audits).** Every identifier
(SKU, MPN) and every datasheet figure/citation you write must be
produced in the same turn as the tool output that grounds it (API
response; open PDF), and the doc text must carry the pointer — file +
table/section for specs, "API-verified <date>" for SKUs. No pointer =
write `_verify_`, never a concrete value. The reviewer is instructed
(REVIEWER.md §3.5) to treat unsourced verification adjectives and
uncheckable citations as automatic findings — write so your claims are
cheap for them to ground-truth.

```bash
# Stage only what you changed.
git add <specific paths>

# Commit with descriptive message.
git commit -m "hardware: CP<N> iteration <M> — <what you did>"

# Push to the current branch.
git push origin "$(git symbolic-ref --short HEAD)"
```

For CP-advancement (creating a new CP branch):

```bash
git checkout -b hw/cp<N>-<slug>
# ... do work ...
git add <files>
git commit -m "hardware: CP<N> initial work (after CP<N-1> APPROVED)"
git push -u origin hw/cp<N>-<slug>
gh pr create --base main --head hw/cp<N>-<slug> --title "..." --body "..."
```

You ARE allowed to:
- Merge PRs after agent-reviewer APPROVED.
- Open new PRs for the next CP.
- Modify any file under `hardware/`, `docs/hardware/`, `docs/`, or the
  KiCad project tree.
- Use `gh` CLI.

You ARE NOT allowed to:
- Force-push to `main`.
- Modify agent-reviewer's review-packet §8 findings (you respond in §9).
- Skip agent-reviewer's sign-off — never set `state: claude_turn → done`
  without an APPROVED CP6 packet.
- Place the actual fab order. That's the user-only "spend money"
  step.

## 8. Escalation to user (be sparing)

The user has explicitly delegated full autonomy. **Default to driving
forward** in consensus with agent-reviewer rather than pausing. Only escalate
(set `state: user_turn`) in these three cases:

### 8a. Mandatory: CP6 APPROVED → before fab order

This is the only spend-money step in the project. After agent-reviewer
APPROVES the CP6 fab-ready packet, set `state: user_turn` with a note
that the renders + Gerbers are in `hardware/outputs/` and the user
should review before placing the JLCPCB order.

### 8b. Consensus failure

If agent-reviewer re-opens the same finding **two iterations in a row** after
you RESOLVED it (you proposed counter A, they re-opened; you proposed
counter B, they re-opened again) — that's a real disagreement worth
a tiebreaker. Set `state: user_turn` with a clear `note`:

```yaml
note: >
  Disagreement with agent-reviewer on <topic>. My position: <X>. agent-reviewer's
  position: <Y>. Resolution requires user input. See cp<N>_*.md
  §8.M / §9.M for the full thread.
```

### 8c. Iteration cap

If `iteration > max_iterations_per_cp` (default 10) on a single CP,
set `state: user_turn` with a "stuck" note. Don't try one more pass.

### What does NOT warrant escalation

- A foundational design pivot (display swap, MCU swap, fab swap) if
  agent-reviewer agrees with you. Just do it, document a new entry in
  `decisions.md`, move on. The user will see it at CP6.
- BOM cost going up by a reasonable amount. You're not the budget
  gatekeeper unless we're talking 2× the current $154 ballpark.
- agent-reviewer finding something you uncovered yourself. Just fix it.

When in doubt, **propose the path to agent-reviewer as part of your work and
let them push back if it's wrong**. agent-reviewer IS the consensus check.

## 9. When you're uncertain

You're allowed to be wrong, and the protocol catches it. If you're
making a non-obvious technical call, **don't paper over the
uncertainty in your RESOLVED entry**. Write:

> RESOLVED — Finding NN
> **Fix**: <what I changed>.
> **Confidence**: medium — I'm <X confident> but if agent-reviewer sees a
> concrete reason this is wrong, please re-open and I'll re-evaluate.

That gives agent-reviewer permission to push back with concrete evidence. If
they don't, you proceed. If they do with valid reasoning, you adjust
and the cycle continues. **The honest "confidence" field is what
makes the loop converge instead of bouncing.**

## 10. Triggers + cadence

You're invoked one of two ways:

### Manual mode (no /loop)

The user types something like "you're up" in the terminal. You read
SEMAPHORE, act if it's your turn, stop. Simple.

### Autonomous mode (/loop)

The user invokes `/loop` once with the prompt below. After that, you
use `ScheduleWakeup` at the end of each turn to self-pace.

**The prompt the user should use to start `/loop`:**

> Check `/Users/pivot/Documents/repo/volthium_reader/hardware/reviews/SEMAPHORE.yaml`.
> If `state` is `claude_turn`, follow `hardware/reviews/DESIGNER.md` and do the
> next Claude action. If `state` is `reviewer_turn` or `user_turn`, exit cheaply.
> If `state` is `done`, stop the loop entirely. Schedule the next wake in
> 20 minutes.

In autonomous mode, end every turn with:

```
ScheduleWakeup(delaySeconds=1200,
               prompt="<same prompt as above>",
               reason="autonomous CP loop")
```

20 minutes is offset from agent-reviewer's 15-minute Cursor interval — keeps us
out of phase, reduces collisions. If the project's pace warrants it,
you can tune the wake delay (e.g. shorter while a CP is being
iterated rapidly, longer during long-running KiCad operations).

## 11. Done

After committing + pushing, **stop** (or `ScheduleWakeup` in
autonomous mode). Tell the user one sentence:

> "Claude iteration N on CP<X> complete; handed to agent-reviewer.
> <Short summary>. Next: agent-reviewer re-review on its next trigger."

Or for advancement:

> "CP<X> APPROVED + merged. Opened CP<X+1> at <PR URL>. Handed to
> agent-reviewer for review."

Or for user-pause:

> "Pausing for user — <reason>. SEMAPHORE state: user_turn."

## 12. Hard-won operational lessons (read before any DRC/placement work)

These are mistakes that already cost an iteration. Don't repeat them.

### 12a. DRC ground truth = regenerate from the committed board

**Never trust `hardware/outputs/*/drc.rpt` or the SEMAPHORE `note`'s
error count.** `drc.rpt` is gitignored and is whatever a past run left
behind — it can be from an earlier iteration with stale geometry (we
were briefly misled by a 359-violation report that predated the flip
fix). The SEMAPHORE summary is a human-written claim, not a measurement.

On every turn that reasons about DRC, regenerate it:

```bash
# errors only (this is the number that gates the CP):
kicad-cli pcb drc --severity-error --exit-code-violations \
  -o /tmp/x.rpt hardware/kicad/<board>/<board>.kicad_pcb
# full picture incl. warnings, categorised:
kicad-cli pcb drc --all-track-errors -o /tmp/xf.rpt <board>.kicad_pcb
grep -oE '^\[[a-z_]+\]' /tmp/xf.rpt | sort | uniq -c
```

The board's severity config downgrades most categories to *warning*;
only the categories left at *error* gate the CP. Know which is which
before claiming "N errors."

### 12b. kiutils cannot read the post-route board — edit placement, regenerate, reroute

`kiutils` parses the KiCad-10 board only well enough to *write* a fresh
one (`Board.create_new()`); it throws trying to *read* a board that
pcbnew/Freerouting saved. So there is **no surgical kiutils edit of a
routed `.kicad_pcb`.** The supported path (current pass, CP3+):

1. Edit the placement data in `hardware/kicad/pcb/build.py`
   (`pl(ref, x, y, rot, side)` calls; shared mechanics + gates live in
   `hardware/kicad/pcb/core.py`).
2. Regenerate: `.venv/bin/python hardware/kicad/pcb/build.py` — the
   build runs its own gate stack (parity, courtyard, outline, fab
   rules, readback, strict full DRC with accounted exclusions) and
   fails non-zero on any finding.
3. Routing (CP5) reruns the same generator; never hand-edit the
   emitted `.kicad_pcb`.

(The pass-1 flow this section used to describe lives in
`hardware/kicad/archive/pass1_pcb/`.)

### 12c. Read real pad geometry with pcbnew, not kiutils

For authoritative pad/courtyard/edge geometry on a routed board, use
KiCad's bundled python (it has `pcbnew`):
`/Applications/KiCad/KiCad.app/Contents/Frameworks/Python.framework/Versions/3.9/bin/python3.9`.
`pad.GetBoundingBox()` gives the true copper extent (a "1×1 mm" THT
clip can have a 3×3.6 mm copper bbox — that is what DRC clears against).

### 12d. Verify a pin's *function* before calling a clearance "inert"

iter-9 documented 3 battery-side clearance errors as "functionally
inert NC pins." They were not NC: MOD1 pads 22–26 are
IO14/IO21/IO47/IO48/IO45 — real ESP32-S3 GPIOs that this design simply
leaves unused, so they read `<no net>`. A 0.000 mm overlap of BAT1's
GND clip onto them was a real GPIO-to-GND short, not a cosmetic flag.
Before writing "inert/NC" in a justification, confirm the pin function
in the symbol (`RF_Module.kicad_sym`) or datasheet. `<no net>` ≠ NC.

### 12e. A scorecard row justified on a false premise is worse than a FAIL

D13 demands binary PASS/FAIL with evidence. iter-9 marked the battery
clearance errors PASS-justified on the (wrong) NC premise. That is the
exact failure mode D11/D13 exist to prevent: process used to launder a
real defect. When a justification rests on a claim you have not
verified, mark it FAIL and verify — don't write the rationale.
