kaanow/volthium_reader/docs/firmware/architecture.md

# Firmware architecture

Two ESP32-S3 firmwares sharing a common-code library. Both built with
ESP-IDF (not Arduino — we want fine-grained light/deep sleep control and
proper FreeRTOS tasking).

## Repo layout (proposed)

```
firmware/
├── common/                 # shared between both nodes
│   ├── volthium_lib/
│   │   ├── ej_bms.{h,c}         # port of volthium/pack.py BMS decoder
│   │   ├── estimator.{h,c}      # port of volthium/estimator.py
│   │   ├── wire_protocol.{h,c}  # port of volthium/wire_protocol.py
│   │   └── crc16.{h,c}
│   └── components/
├── bms-link/               # battery-side firmware (ESP-IDF app)
│   ├── main/
│   │   ├── main.c               # FreeRTOS task setup
│   │   ├── ble_task.c           # BLE central, BMS reads
│   │   ├── tx_task.c            # RS-485 frame transmit
│   │   ├── power_task.c         # SOC-tier state machine, ULP, MOSFET ctrl
│   │   └── adc_task.c           # 24V sense
│   ├── ulp/
│   │   └── voltage_monitor.S    # ULP-RISC-V routine for hard-cut state
│   ├── partitions.csv
│   ├── sdkconfig.defaults
│   └── CMakeLists.txt
└── display/                # display-side firmware (ESP-IDF app)
    ├── main/
    │   ├── main.c
    │   ├── rx_task.c            # RS-485 frame receive + decode
    │   ├── render_task.c        # e-paper rendering
    │   ├── input_task.c         # button handling
    │   └── ble_release.c        # button → RS-485 release command
    ├── components/
    │   └── epd_4in2b_v2/        # Waveshare driver (well-documented)
    ├── partitions.csv
    ├── sdkconfig.defaults
    └── CMakeLists.txt
```

## Battery-side tasks (FreeRTOS)

| Task | Priority | Period / event | Notes |
|---|---|---|---|
| `ble_task` | 5 | event-driven; runs while connected | Holds persistent BLE central to both BMS. Handles polite-disconnect on `release` event from RS-485. |
| `tx_task` | 4 | every 30 s (state 1) / 60 s (state 2) | Builds WireFrame from latest BLE samples, emits RS-485 frame |
| `power_task` | 6 | every 5 s + on SOC threshold crossings | Implements the 4-tier state machine; commands the SSR1 load switch; manages light/deep sleep. **Graceful display shed (D30):** before opening SSR1 at low SOC, send the RS-485 "sleeping" frame, wait ~1 frame for the display to render it, *then* open SSR1 — the e-paper holds the "sleeping" message after power is cut. **Heartbeat (D30):** track the display's RS-485 acks; on heartbeat loss flag "display dead" in the WiFi log-push (D25). |
| `adc_task` | 3 | every 2 s | Reads 24V sense; provides voltage-based SOC fallback when BLE is down |
| `cli_task` | 2 | USB serial available | Optional debug shell over native USB-C (D22) |

Inter-task communication: FreeRTOS queues with the latest `BMSSample`,
`PackReading`, and `Estimate` structs. Queue depth of 1 (mailbox style)
because newer readings supersede older ones.

## Display-side tasks

| Task | Priority | Period / event | Notes |
|---|---|---|---|
| `rx_task` | 5 | RS-485 frame arrived | Validates CRC, parses WireFrame, posts to render queue |
| `render_task` | 4 | on new frame OR button press OR 30 s tick | Decides what to draw, kicks e-paper. **Always renders a "last updated HH:MM" timestamp (D30)** — a frozen e-paper showing a stale time is the primary "display is dead" tell (covers both comms-loss and power-loss, since the bistable image keeps the old time). |
| `input_task` | 3 | GPIO interrupts (debounced) | Maps buttons to events; sends "release BLE" over RS-485 |
| `watchdog_task` | 2 | every 10 s | If no frame in 90 s, draws "LINK DOWN" overlay (D30 mode-a: comms dead, display powered). Also handles the **"sleeping" frame**: on a low-battery/shutdown command from the battery side, render "Monitor sleeping — low battery" so the bistable screen holds that correct message after the battery opens SSR1 (D30 graceful pre-shed). |

## State machine (battery-side `power_task`)

Formal spec with hysteresis tables and SOC-source rules per state is
in **[`docs/firmware/state_machine.md`](state_machine.md)**. Diagram
inlined below for orientation:

```
            ┌──────────┐
            │  NORMAL  │  (>25%)  ── persistent BLE, 30s tx
            └────┬─────┘
                 │ SOC ≤ 25 % for 1 s
                 ▼
            ┌──────────┐
            │   LOW    │  (15-25%)  ── 60s tx, "LOW PACK" flag
            └────┬─────┘
                 │ SOC ≤ 15 % for 1 s    │ SOC ≥ 27 % for 2 min
                 ▼                        ▲
            ┌──────────┐                  │
            │ DEEPSLEEP│  (10-15%)        │
            └────┬─────┘  ── BLE disconnect, ULP wake 10 min
                 │ SOC ≤ 10 %    │ ULP-read SOC ≥ 18 % for 2 consec wakes
                 ▼                ▲
            ┌──────────┐          │
            │ HARDCUT  │          │
            └──────────┘──────────┘
              ULP only; MOSFET off
              wake on ULP voltage threshold or override-button
```

Hysteresis on up-transitions (2 min sustained above the threshold)
prevents flapping when load cycles.

## RS-485 framing (already specified)

See `volthium/wire_protocol.py` (Python reference impl) and
`tests/test_wire_protocol.py` for vectors. C port in
`firmware/common/volthium_lib/wire_protocol.{h,c}` will match byte-for-byte.

CRC-16/CCITT-FALSE test vector: `"123456789"` → `0x29B1`.

**Protocol additions for D30 (display deadness detection):** two new frame
types to add to `wire_protocol` at CP-firmware: (1) a **battery→display
"sleeping"/shutdown** command (triggers the pre-shed render before Q1 opens);
(2) a **display→battery heartbeat/ack** so the battery side can detect a dead
display and surface it via the WiFi push. Both are small additions to the
existing framing; spec the byte layout + add test vectors when the C port
lands.

## Estimator port

The Python `Estimator` (in `volthium/estimator.py`) is ~80 lines of
arithmetic + a `deque(maxlen=20)`. Direct C port: a ring buffer plus
two EMA accumulators. State persists across deep-sleep via NVS so we
don't reset the smoothing when waking.

## BLE flap recovery

See [`ble_flap_recovery.md`](ble_flap_recovery.md) for observed flap
behavior (5 events captured in the first 5 h of dev logging), root
cause hypothesis, expected firmware retry policy (backoff 500 ms →
30 s), telemetry-flag escalation rules, display-side responses by
flap duration, and a regression-test sketch.

## OTA strategy

ESP32-S3 has dual app partitions. Two paths:

1. **USB-C dev port** behind the battery enclosure lid — manually flash
   when the user opens the box. Simplest, manageable for a once-a-year
   update cadence.
2. **Wi-Fi via display-side** — display side enables a temporary Wi-Fi
   AP when both buttons are held (or a hidden menu sequence). User
   browses to it, uploads firmware. Display side validates and pushes
   the new image to battery side over RS-485 in 256-byte chunks.

Recommend path 1 for v1; path 2 as a v2 feature if updates become
frequent.

## Debug visibility

Each board exposes a **keyed 2×3 ESP-Prog "Program" header** on the PCB
(battery J5 per DR-32/F01; display J3 per the display-CP2 DR-32 parity
call — both boards deep-sleep, so recovery must not depend on the USB
stack). One ESP-Prog ribbon serves both boards:

| Pin | Net | Purpose |
|-----|---|---|
| 1 | MCU_EN  | reset / auto-program |
| 2 | V3V3 | target sense |
| 3 | DBG_TXD | ESP-IDF console out (target TXD0) |
| 4 | GND | |
| 5 | DBG_RXD | console in (target RXD0) |
| 6 | BOOT | IO0 — force-download (hold low + blip EN) |

*(CP2 supersedes the original 4-pin GND/TX/RX/RESET# header described in
earlier revisions of this doc.)*

Use any FTDI cable. The console runs at 115200 8N1.

~~Optional onboard LED on GPIO15~~ — **retired (CP1):** D4 removed all
indicator LEDs (power-first), and GPIO15 is now allocated to RS-485 /RE
(D34). Status visibility comes from the e-paper timestamp (D30) and the
UART console.

## Button requirements (user-set, 2026-07-14)

Battery-side **BTN1** (panel-mount, ESP GPIO7, RTC-wake capable,
active-LOW) is a pure GPIO input — every function below is firmware,
no hardware dependency:

| Gesture | Function |
|---|---|
| Short press | Display-power override (existing function; UVLO hardware floor still wins below ~20 V pack) |
| **Long press (hold ≥ 10 s)** | **WiFi config reset to base state** — wipe stored WiFi credentials/config and return to the not-yet-designed provisioning base state. Reset target state TBD when WiFi provisioning is designed; the trigger path is a firm requirement now |

Long-press-from-deep-sleep works: GPIO7 is in the RTC wake mask, so the
press wakes the ESP and firmware then samples hold duration. The 100 ms
debounce RC is irrelevant at these timescales. Display-side BTN1–3
(GPIO12/13/14) remain fully software-defined per D7 — a parallel reset
gesture there needs no hardware change either.
