kaanow/volthium_reader/hardware/reviews/visual_inspections/cp2-schematic/display-iter1/designer/sheet_d_periph.btns.png

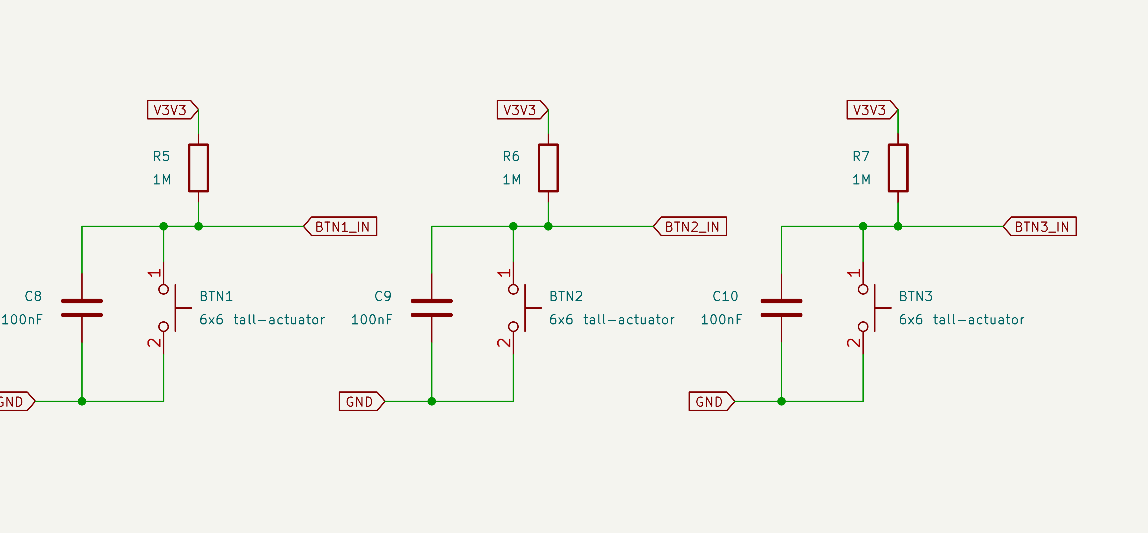
hardware/reviews/visual_inspections/cp2-schematic/display-iter1/designer/sheet_d_periph.btns.png
