kaanow/volthium_reader/hardware/reviews/visual_inspections/cp2-schematic/display-iter1/reviewer/eye_p2_grid_05.png

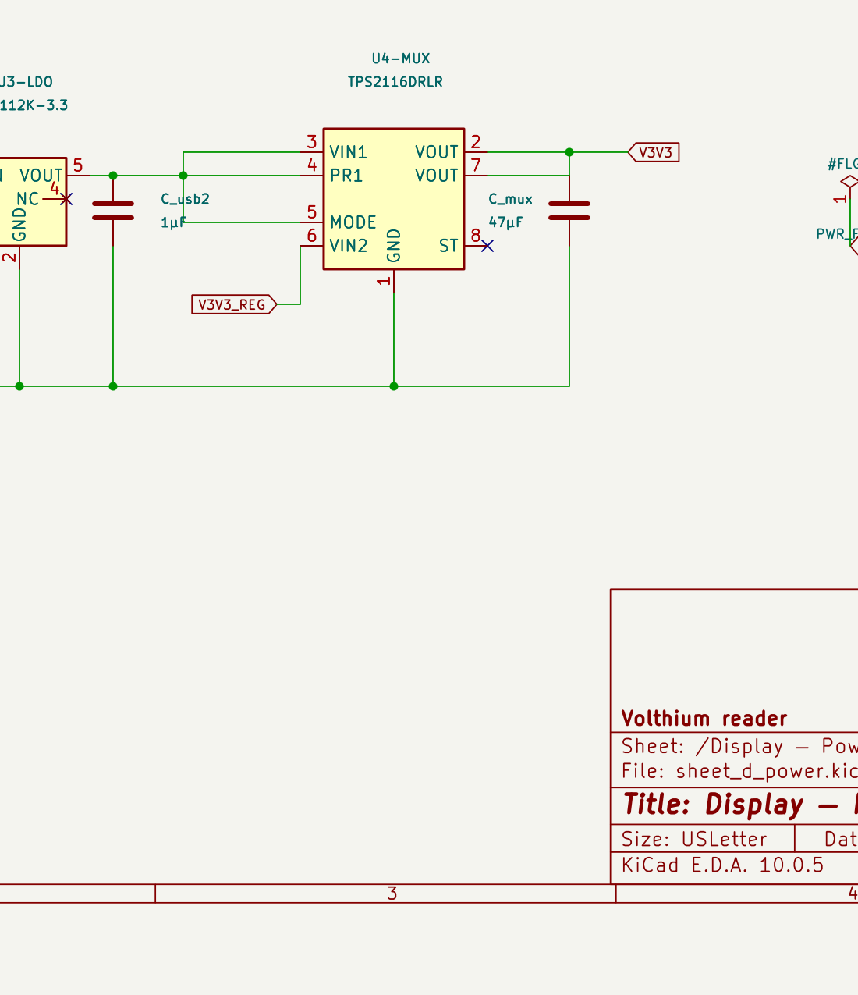
hardware/reviews/visual_inspections/cp2-schematic/display-iter1/reviewer/eye_p2_grid_05.png
