kaanow/volthium_reader/hardware/reviews/visual_inspections/cp2-schematic/display-iter1/reviewer/g9/display/iter1/reviewer/battery_p1_crop_07.png

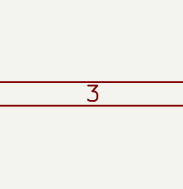
hardware/reviews/visual_inspections/cp2-schematic/display-iter1/reviewer/g9/display/iter1/reviewer/battery_p1_crop_07.png
