kaanow/volthium_reader/hardware/reviews/visual_inspections/cp2-schematic/display-iter1/reviewer/source_spotchecks/thvd1400_p4.png

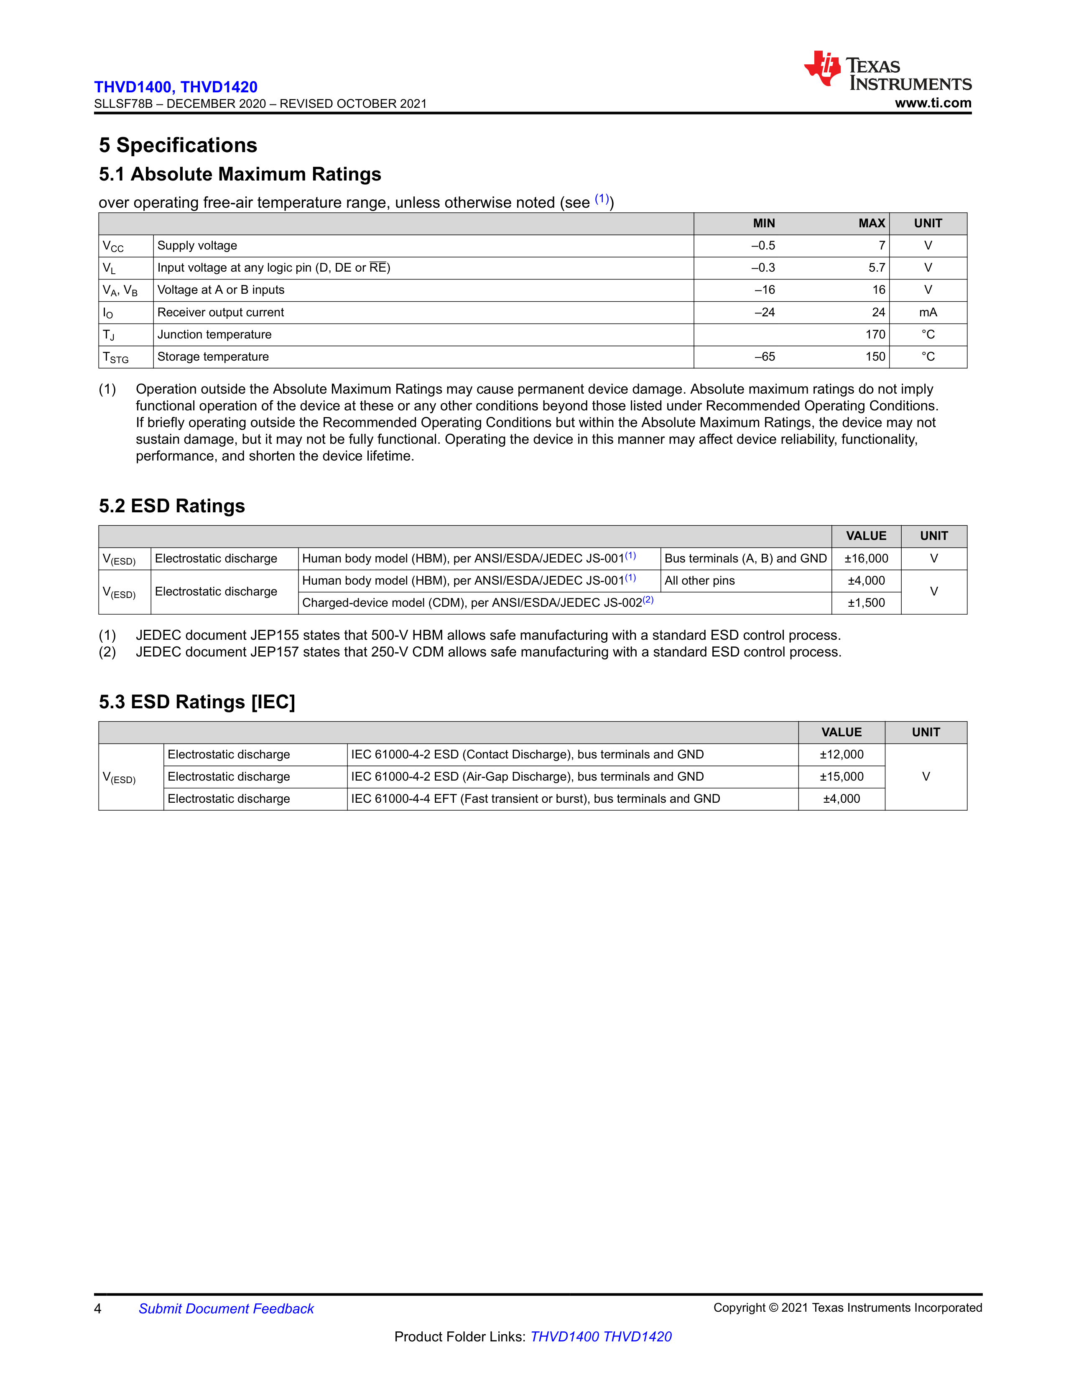
hardware/reviews/visual_inspections/cp2-schematic/display-iter1/reviewer/source_spotchecks/thvd1400_p4.png
