kaanow/volthium_reader/hardware/reviews/visual_inspections/cp2-schematic/display-iter1/reviewer/source_spotchecks/usb4085_family_spec_p2.png

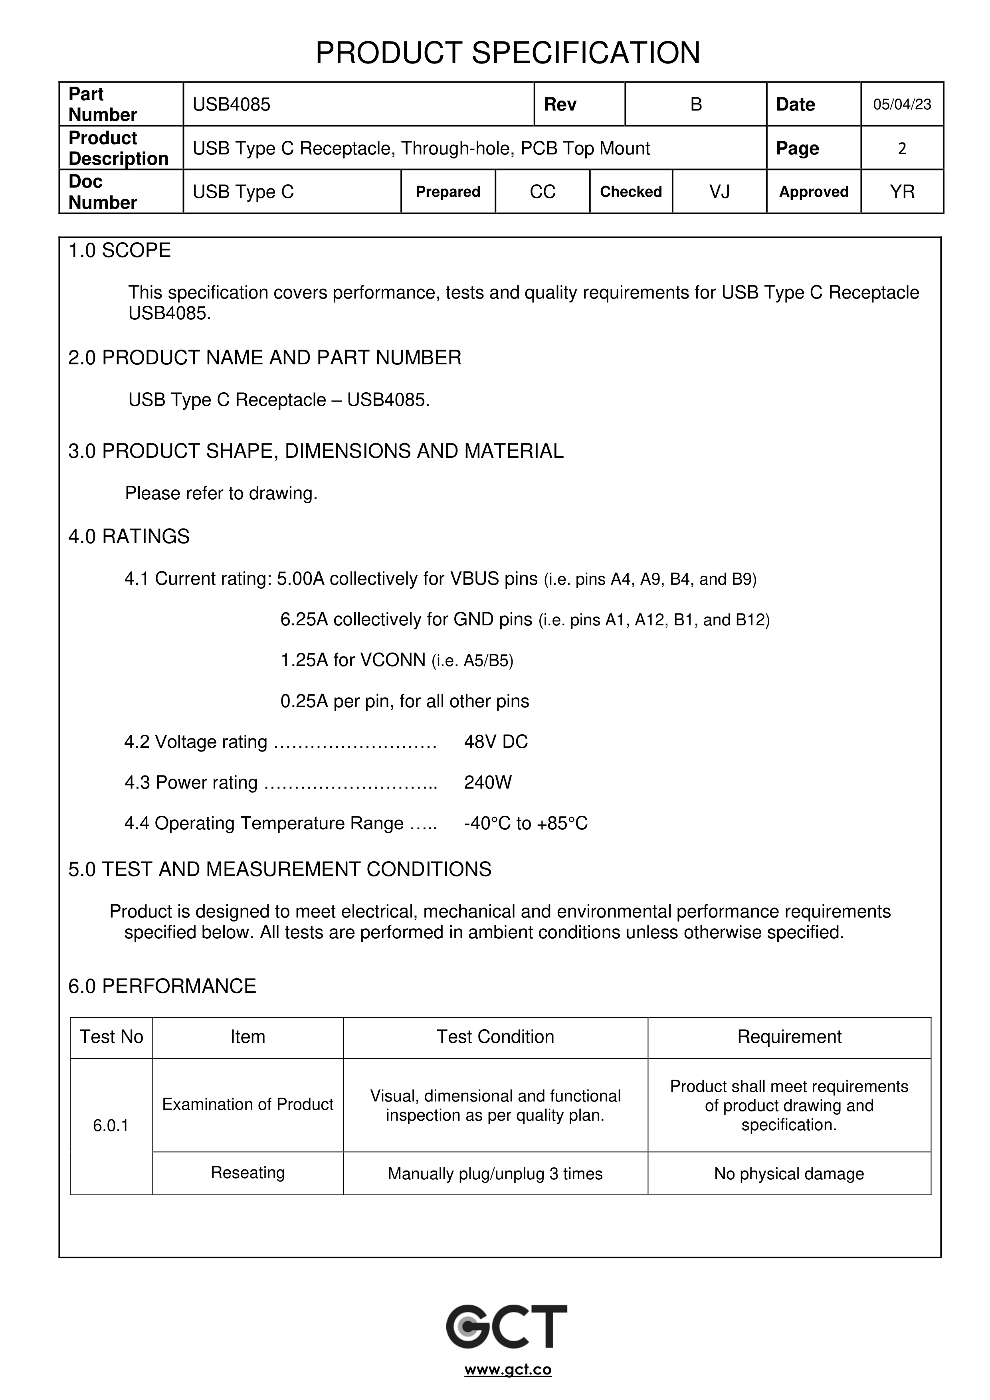
hardware/reviews/visual_inspections/cp2-schematic/display-iter1/reviewer/source_spotchecks/usb4085_family_spec_p2.png
