kaanow/volthium_reader/hardware/reviews/visual_inspections/cp2-schematic/display-iter2/reviewer/g9/cp2-schematic/iter6/reviewer/battery_p2_full_300dpi.png

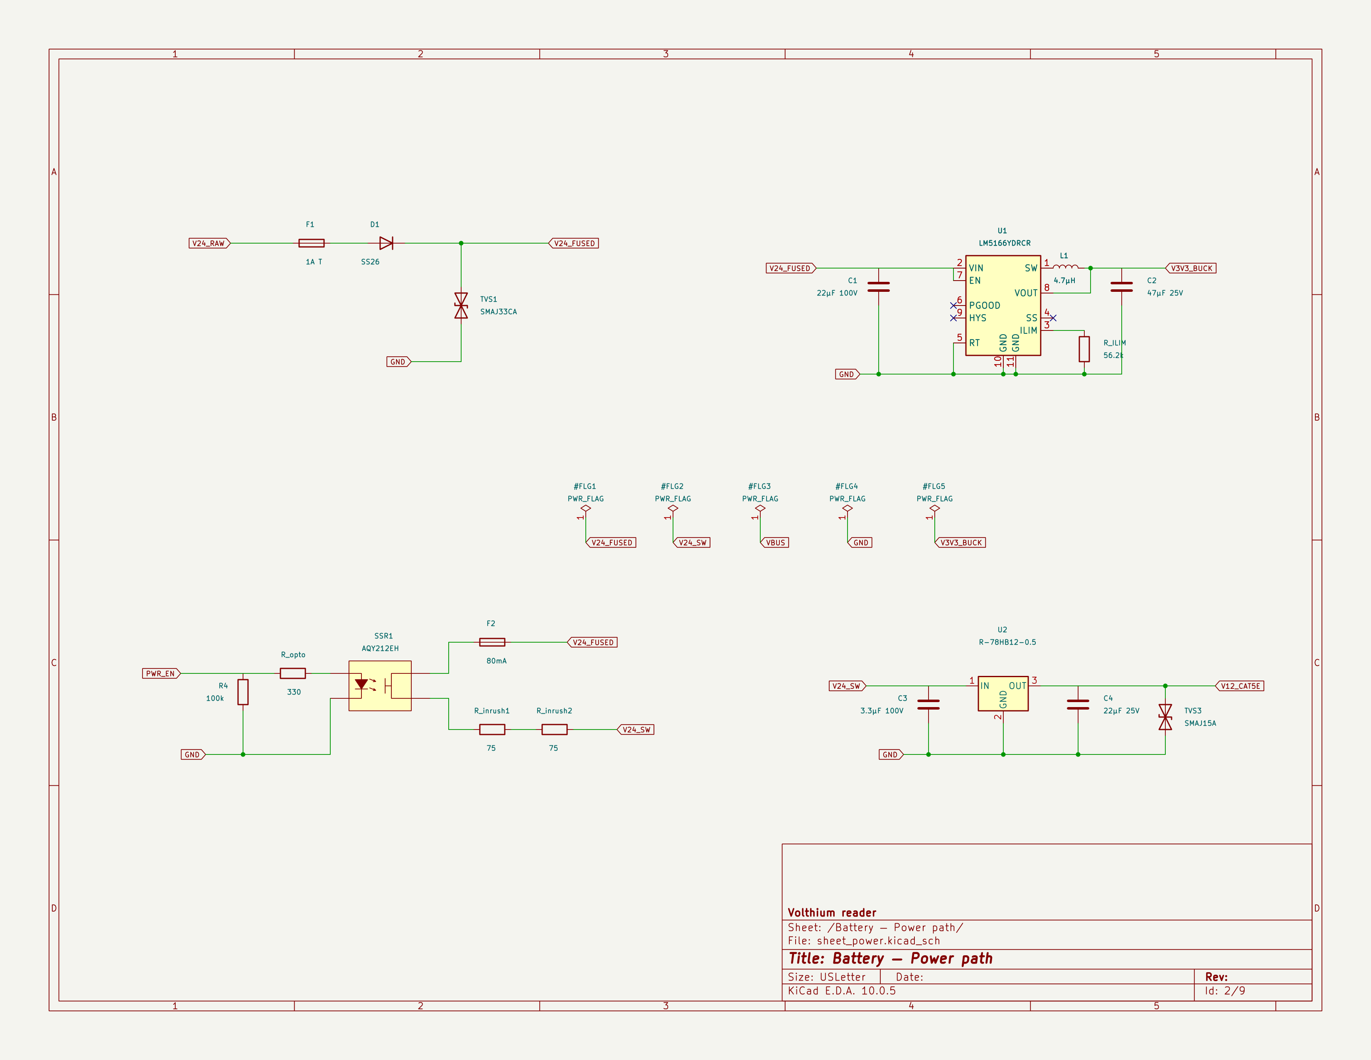
hardware/reviews/visual_inspections/cp2-schematic/display-iter2/reviewer/g9/cp2-schematic/iter6/reviewer/battery_p2_full_300dpi.png
