kaanow/volthium_reader/hardware/reviews/visual_inspections/cp2-schematic/display-iter3/reviewer/g9/cp2-schematic/iter7/reviewer/battery_p8_crop_01.png

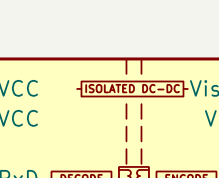
hardware/reviews/visual_inspections/cp2-schematic/display-iter2/reviewer/g9/cp2-schematic/iter6/reviewer/battery_p4_crop_01.png
