kaanow/volthium_reader/hardware/reviews/visual_inspections/cp2-schematic/display-iter4/reviewer/g9/cp2-schematic/iter8/reviewer/battery_p5_crop_05.png

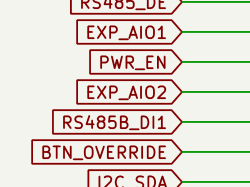
hardware/reviews/visual_inspections/cp2-schematic/display-iter4/reviewer/g9/cp2-schematic/iter8/reviewer/battery_p5_crop_05.png
