kaanow/volthium_reader/hardware/reviews/visual_inspections/cp2-schematic/display-iter4/reviewer/usb4085_drawing_p1.png

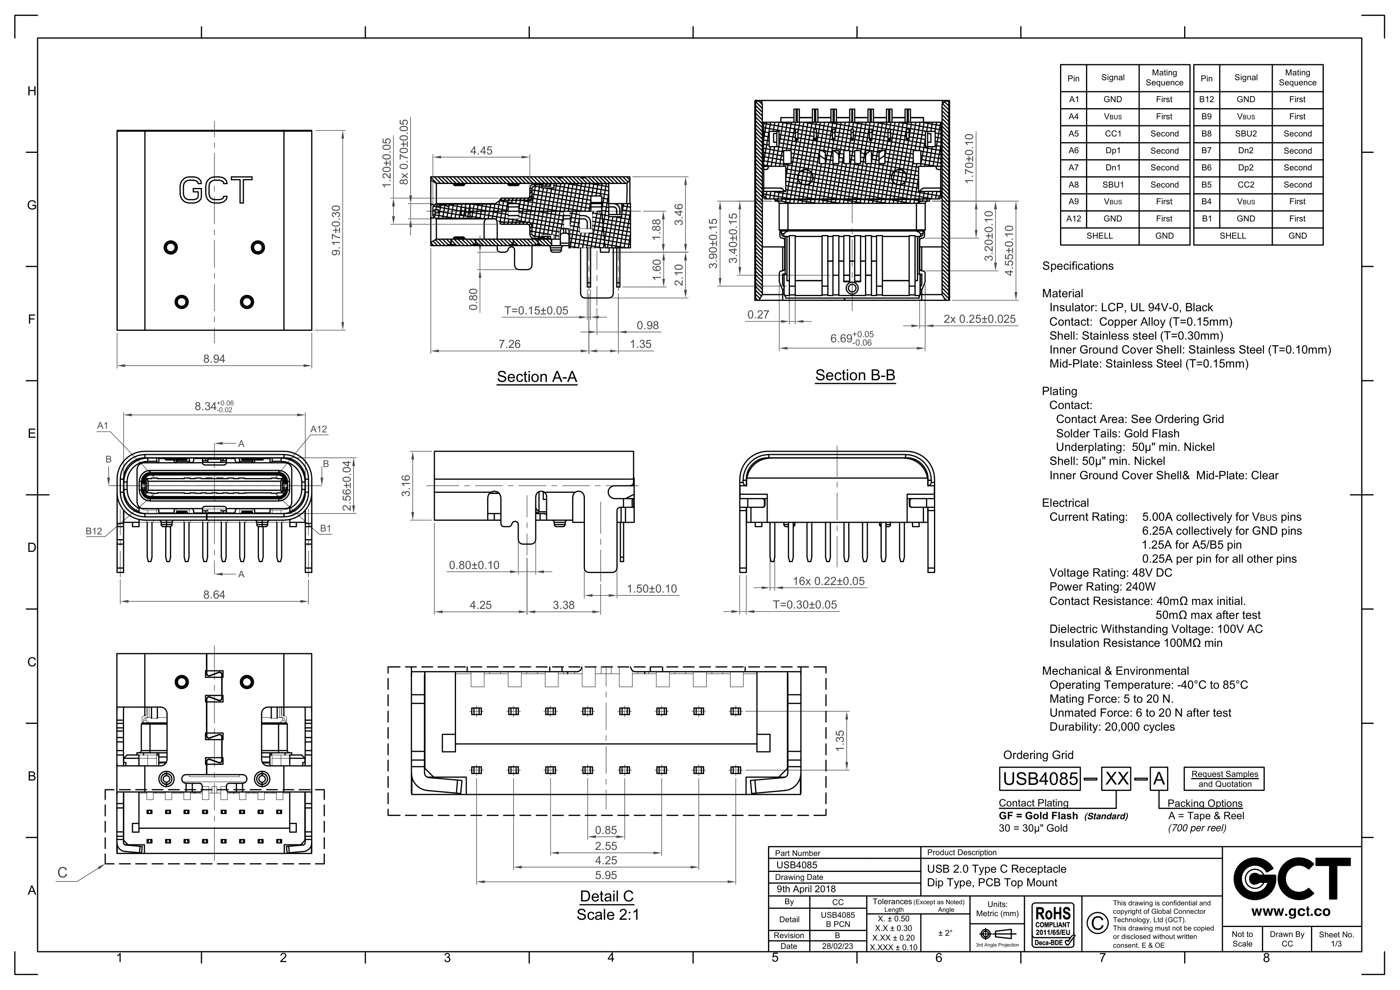
hardware/reviews/visual_inspections/cp2-schematic/display-iter4/reviewer/usb4085_drawing_p1.png
