kaanow/volthium_reader/hardware/reviews/visual_inspections/cp2-schematic/iter1/reviewer/battery_p2_eye_crop_04.png

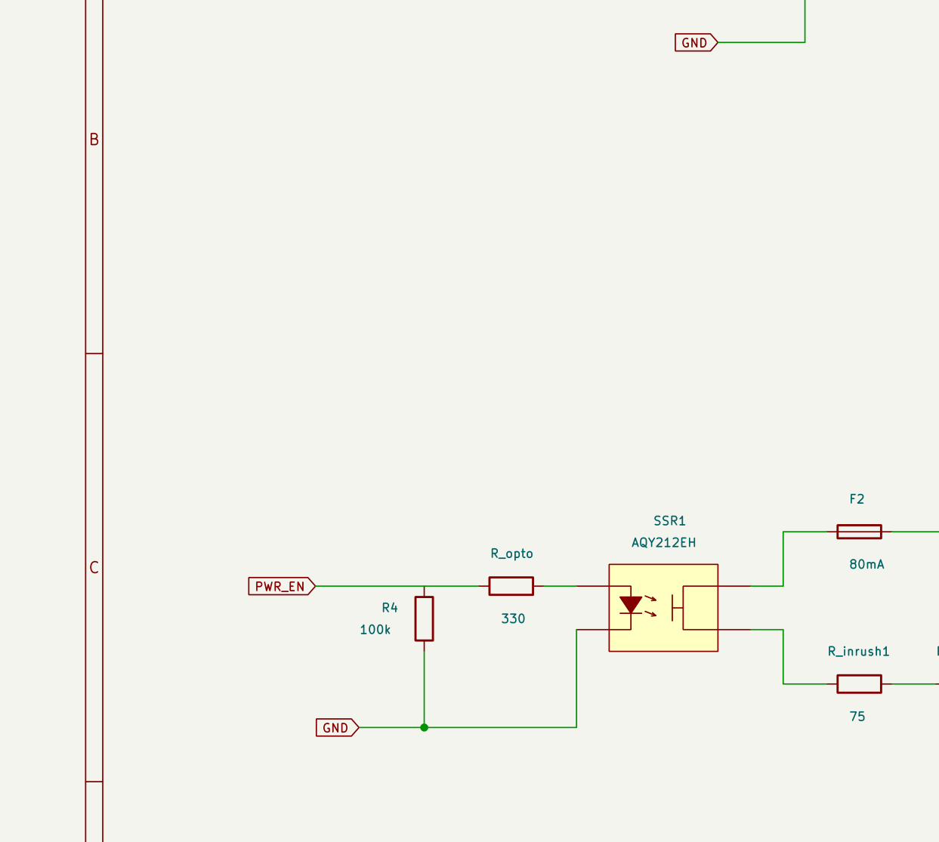
hardware/reviews/visual_inspections/cp2-schematic/iter1/reviewer/battery_p2_eye_crop_04.png
