kaanow/volthium_reader/hardware/reviews/visual_inspections/cp2-schematic/iter1/reviewer/battery_p4_eye_crop_05.png

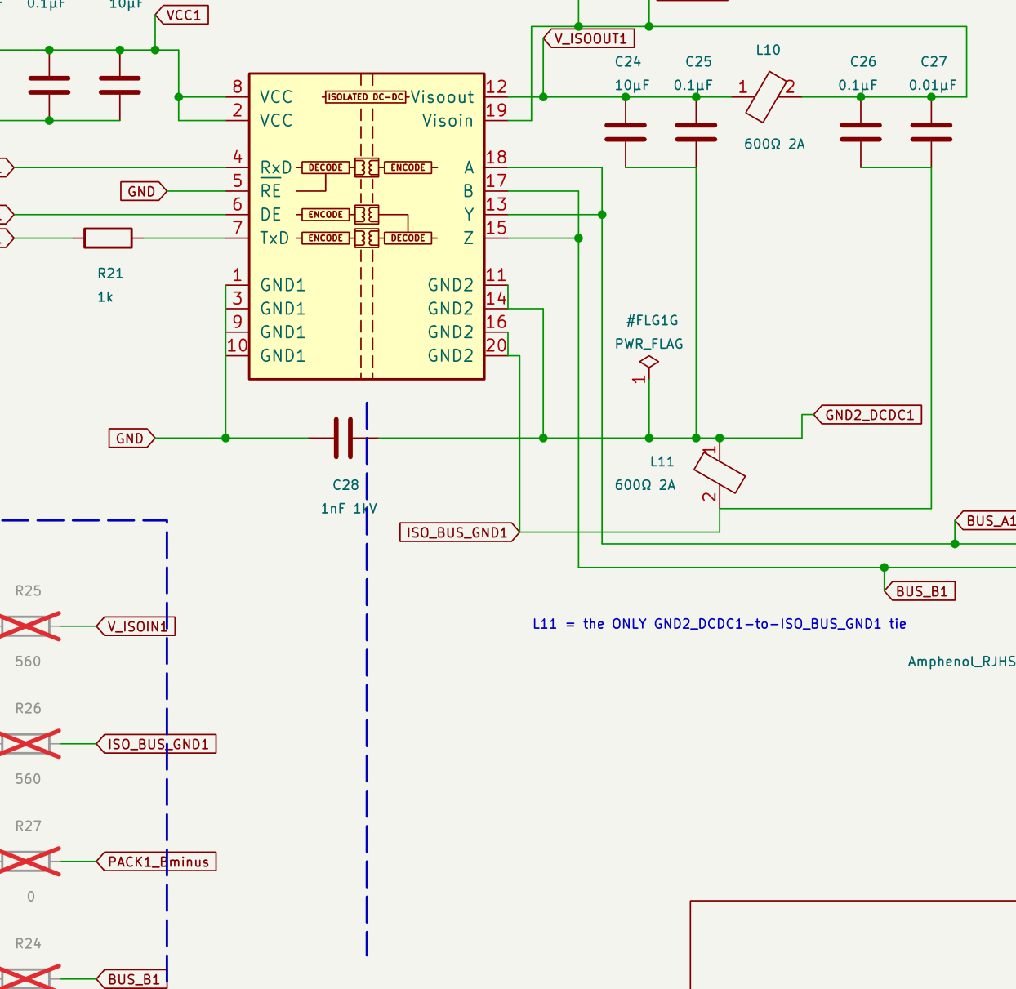
hardware/reviews/visual_inspections/cp2-schematic/iter1/reviewer/battery_p4_eye_crop_05.png
