kaanow/volthium_reader/hardware/reviews/visual_inspections/cp2-schematic/iter1/reviewer/battery_p7_eye_crop_06.png

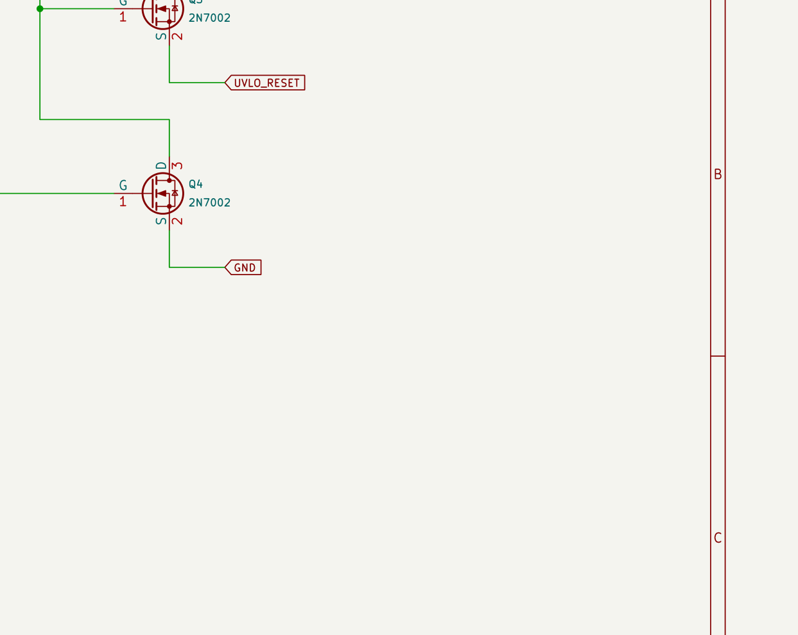
hardware/reviews/visual_inspections/cp2-schematic/iter1/reviewer/battery_p7_eye_crop_06.png
