kaanow/volthium_reader/hardware/reviews/visual_inspections/cp2-schematic/iter1/reviewer/battery_p7_full_300dpi.png

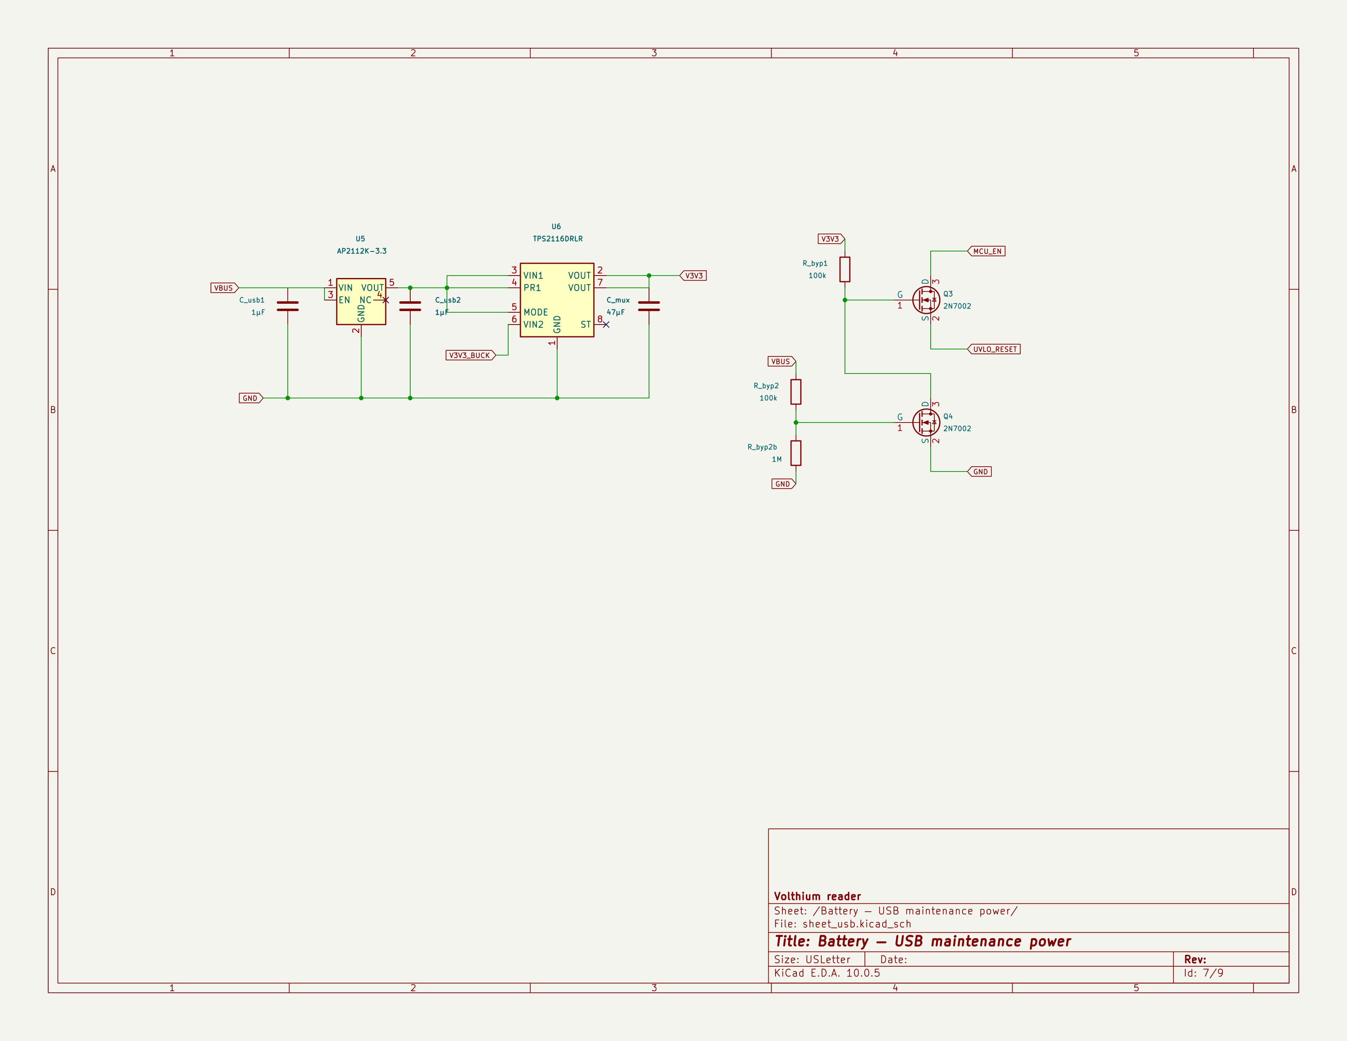
hardware/reviews/visual_inspections/cp2-schematic/iter1/reviewer/battery_p7_full_300dpi.png
