kaanow/volthium_reader/hardware/reviews/visual_inspections/cp2-schematic/iter1/reviewer/source_spotchecks/CK_8020_series_p2.png

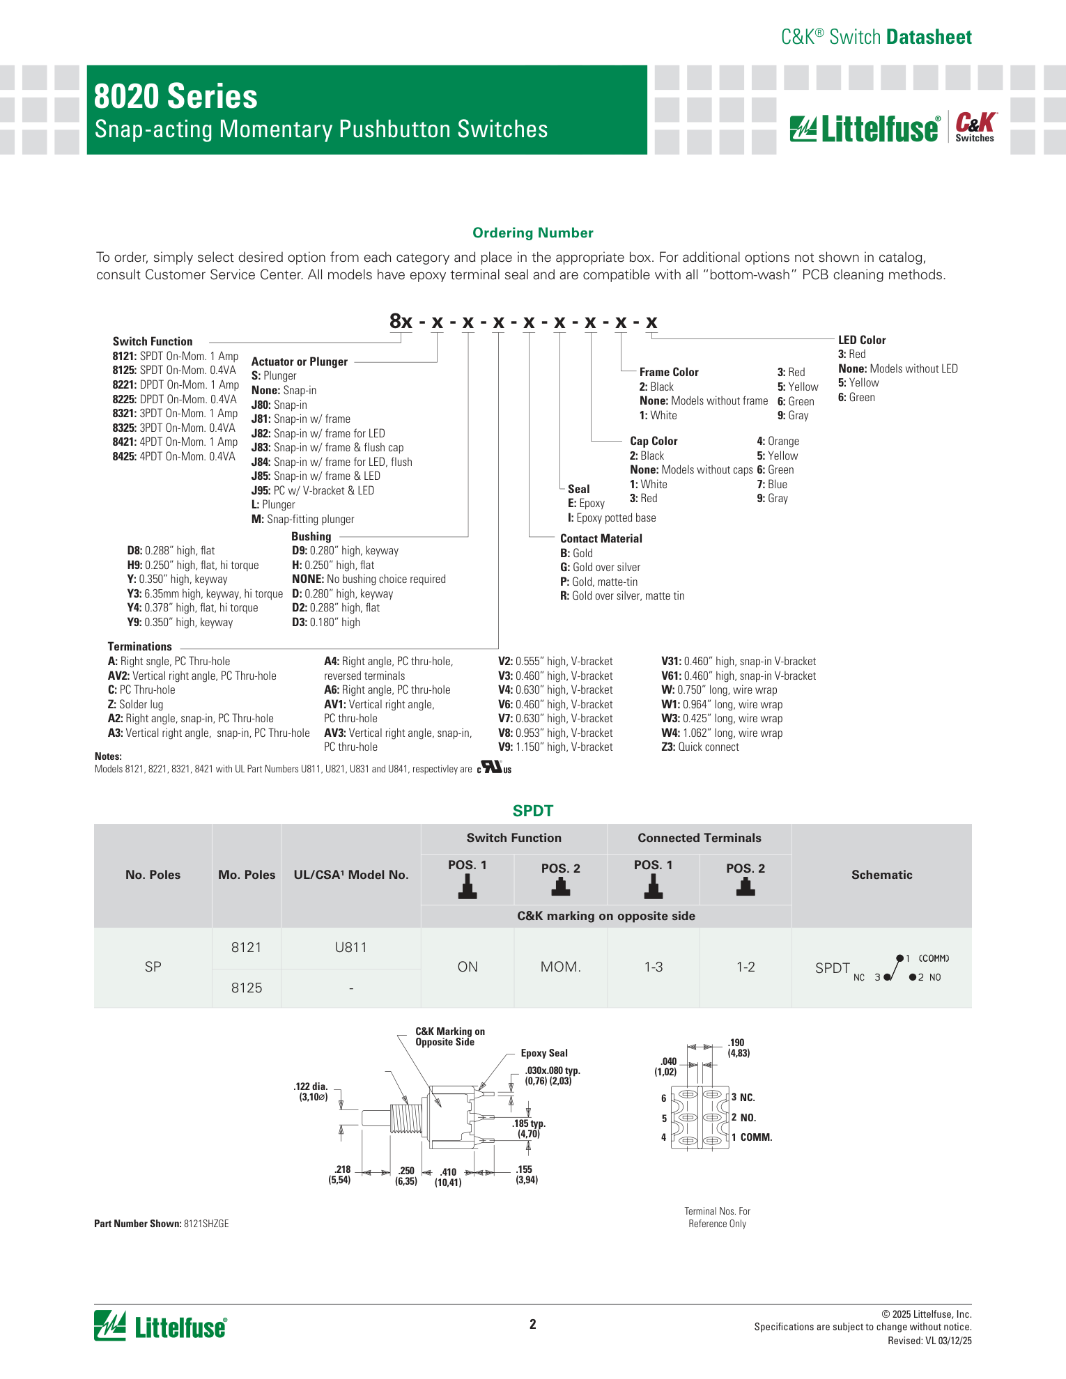
hardware/reviews/visual_inspections/cp2-schematic/iter1/reviewer/source_spotchecks/CK_8020_series_p2.png
