kaanow/volthium_reader/hardware/reviews/visual_inspections/cp2-schematic/iter1/reviewer/source_spotchecks/ESP32-S3-WROOM-1-N16R8_p13.png

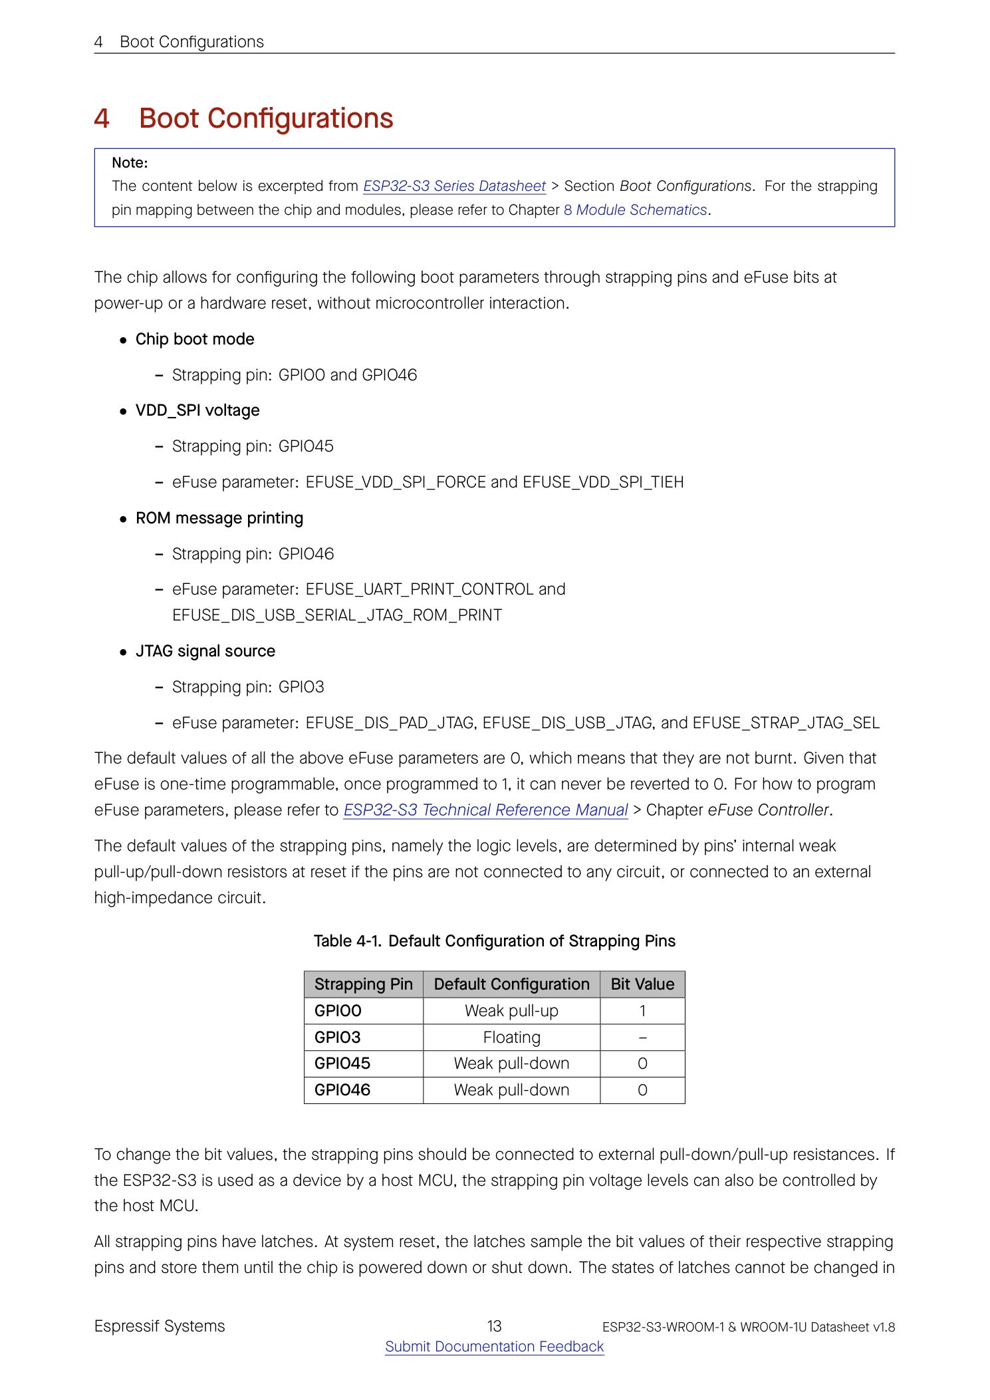
hardware/reviews/visual_inspections/cp2-schematic/iter1/reviewer/source_spotchecks/ESP32-S3-WROOM-1-N16R8_p13.png
