kaanow/volthium_reader/hardware/reviews/visual_inspections/cp2-schematic/iter1/reviewer/source_spotchecks/TCAN332_p4.png

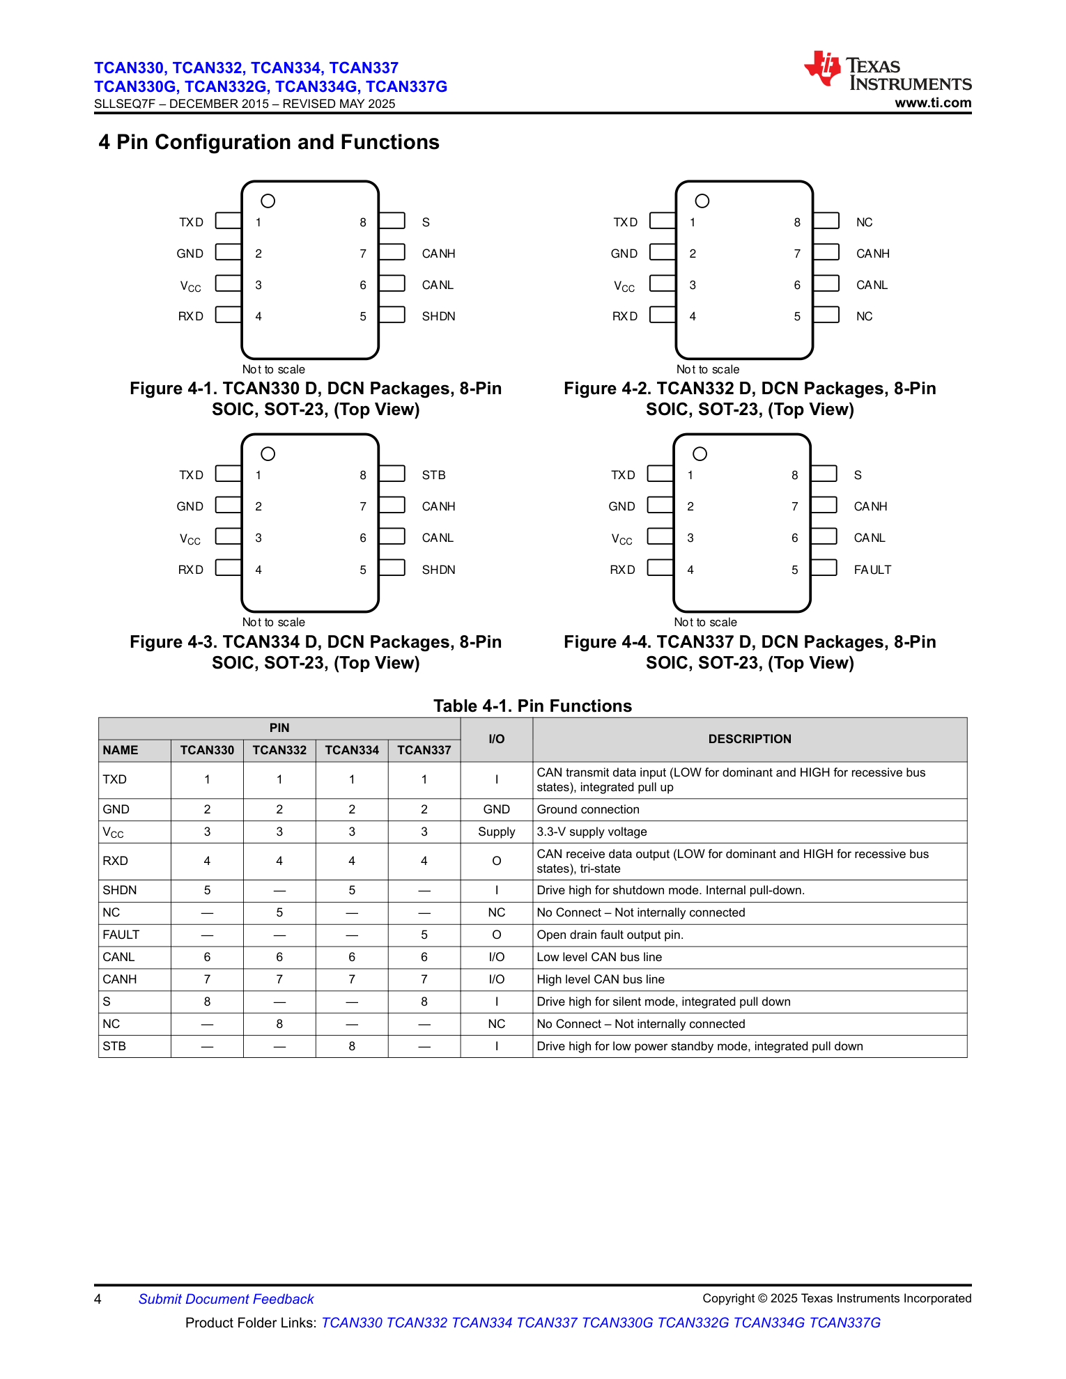
hardware/reviews/visual_inspections/cp2-schematic/iter1/reviewer/source_spotchecks/TCAN332_p4.png
