kaanow/volthium_reader/hardware/reviews/visual_inspections/cp2-schematic/iter2/designer/page-2.png

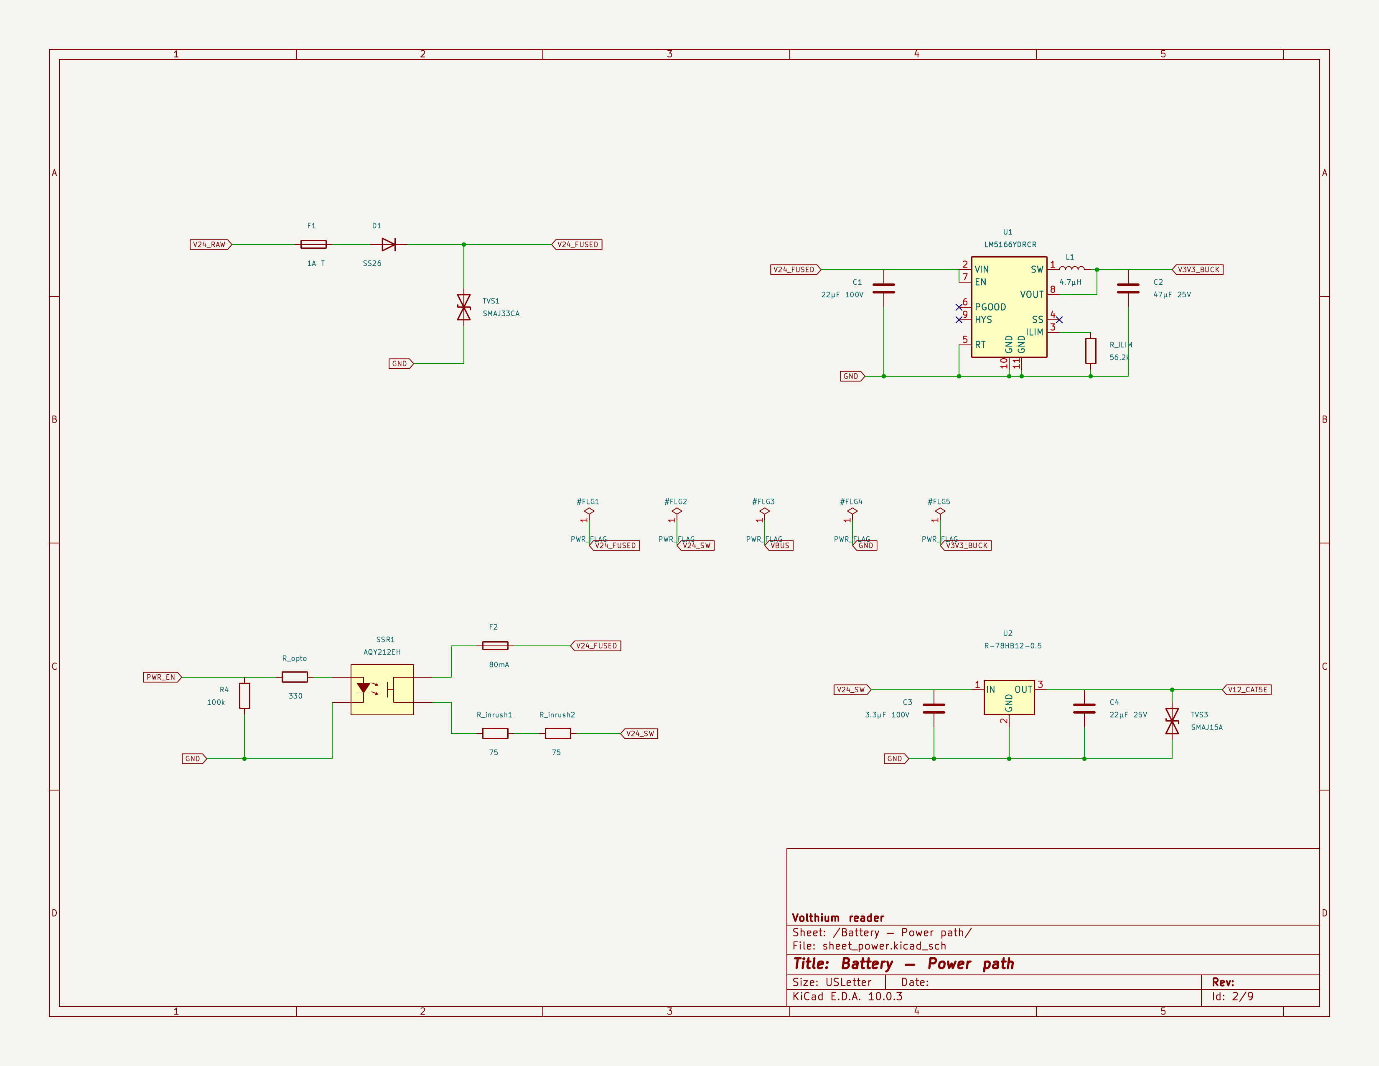
hardware/reviews/visual_inspections/cp2-schematic/iter2/designer/page-2.png
