kaanow/volthium_reader/hardware/reviews/visual_inspections/cp2-schematic/iter2/designer/periph_d2_dnp_crop.png

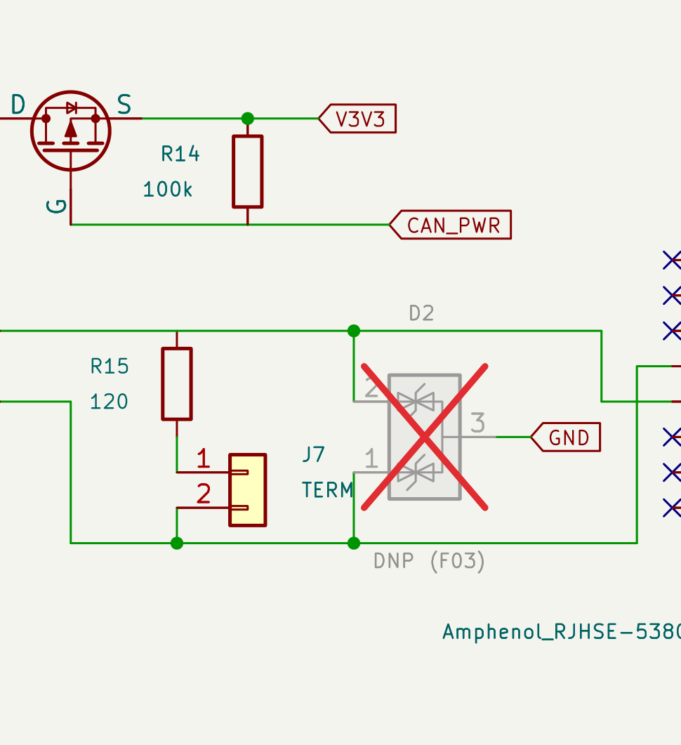
hardware/reviews/visual_inspections/cp2-schematic/iter2/designer/periph_d2_dnp_crop.png
