kaanow/volthium_reader/hardware/reviews/visual_inspections/cp2-schematic/iter2/reviewer/battery_p1_full_300dpi.png

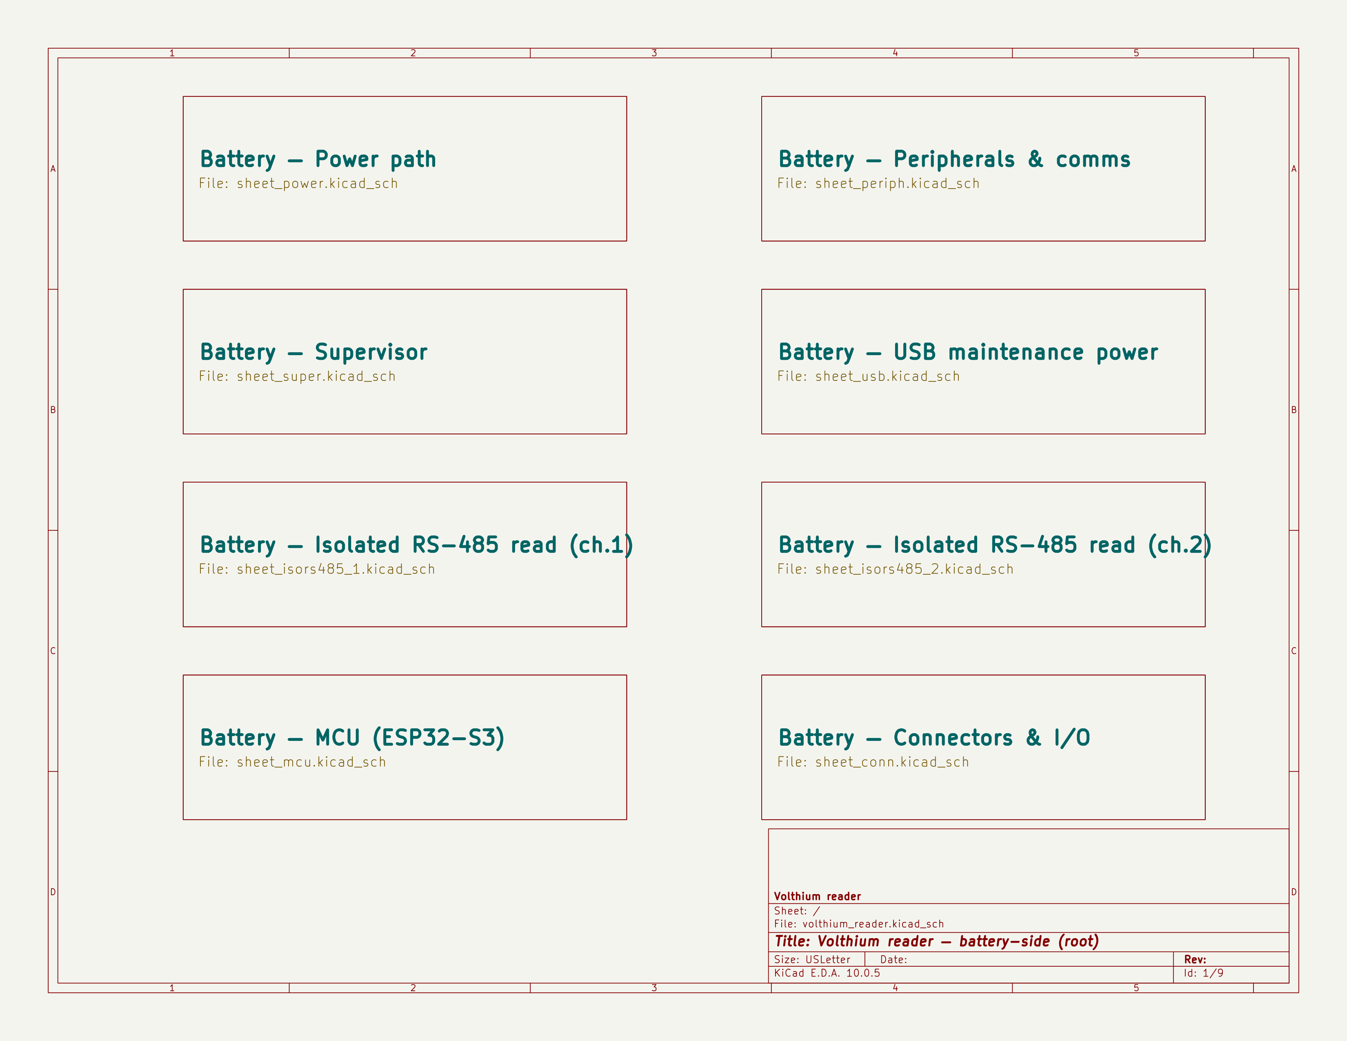
hardware/reviews/visual_inspections/cp2-schematic/iter2/reviewer/battery_p1_full_300dpi.png
