kaanow/volthium_reader/hardware/reviews/visual_inspections/cp2-schematic/iter2/reviewer/battery_p2_eye_crop_01.png

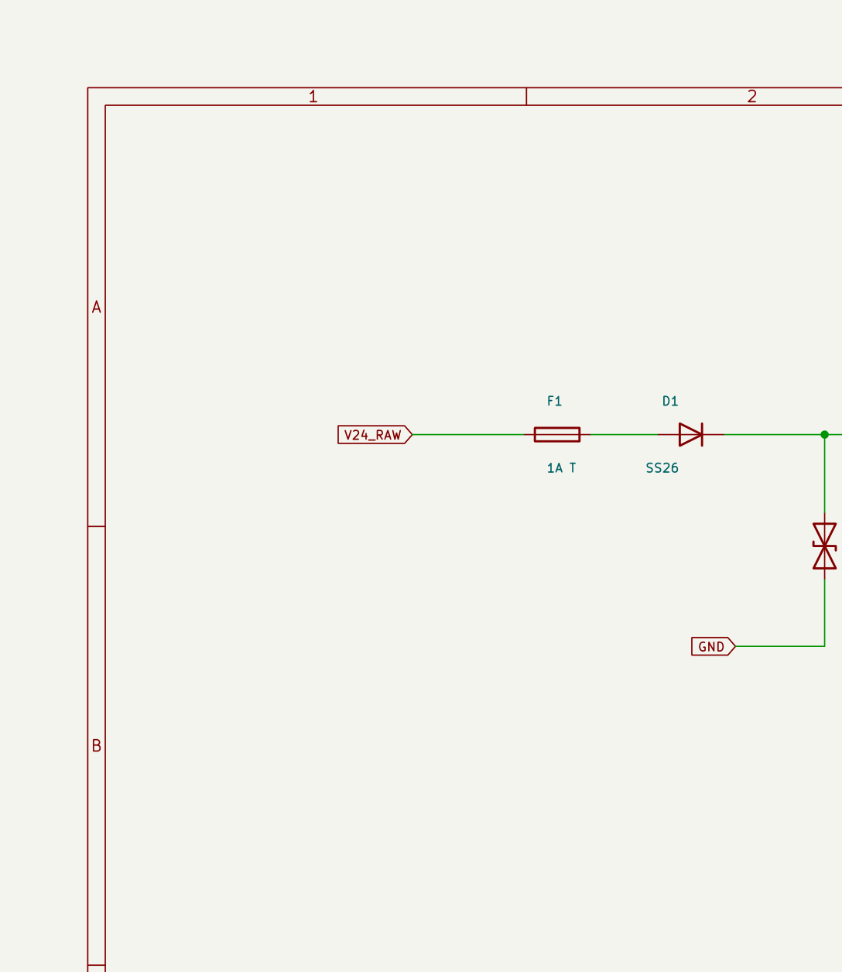
hardware/reviews/visual_inspections/cp2-schematic/iter2/reviewer/battery_p2_eye_crop_01.png
