kaanow/volthium_reader/hardware/reviews/visual_inspections/cp2-schematic/iter2/reviewer/battery_p8_eye_crop_05.png

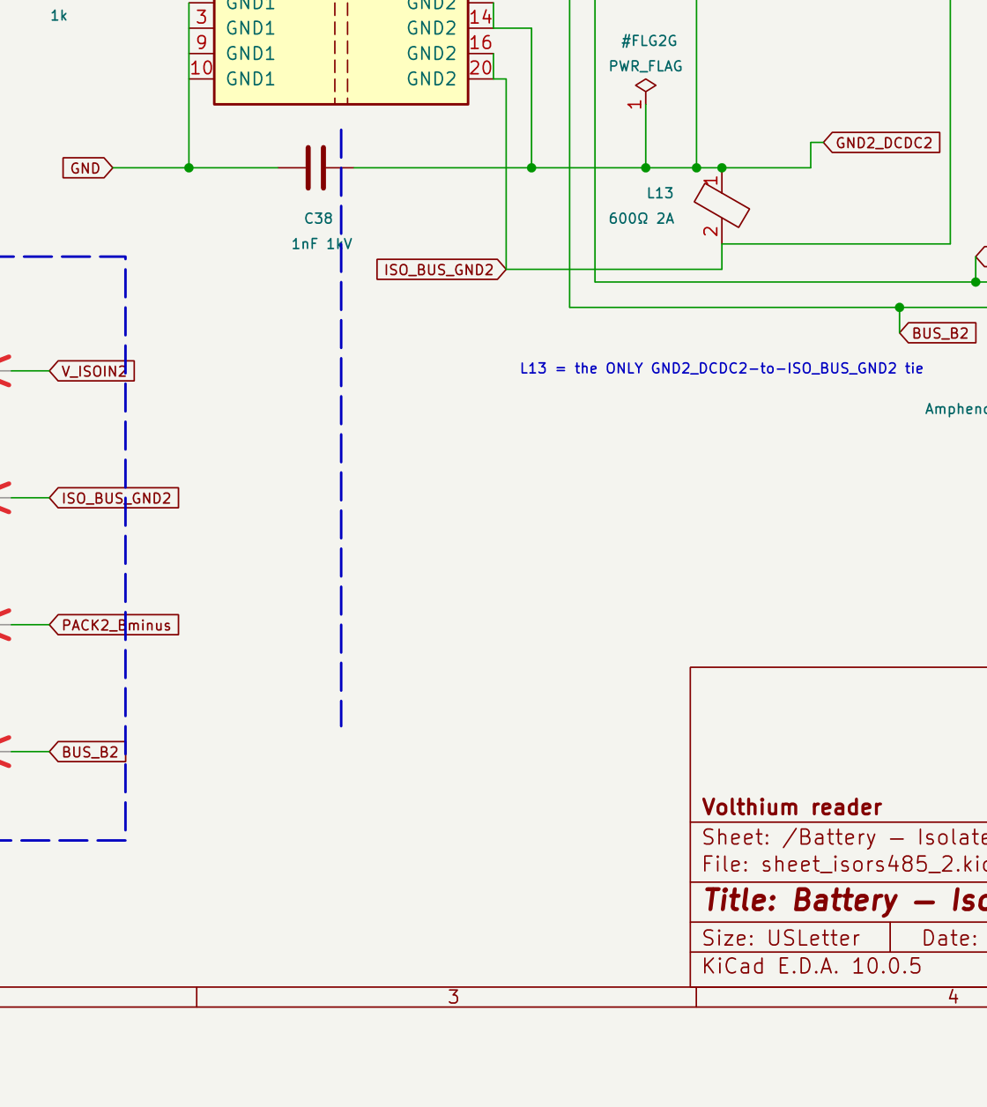
hardware/reviews/visual_inspections/cp2-schematic/iter2/reviewer/battery_p8_eye_crop_05.png
