kaanow/volthium_reader/hardware/reviews/visual_inspections/cp2-schematic/iter2/reviewer/source_spotchecks/NUP2105L_onsemi_p3.png

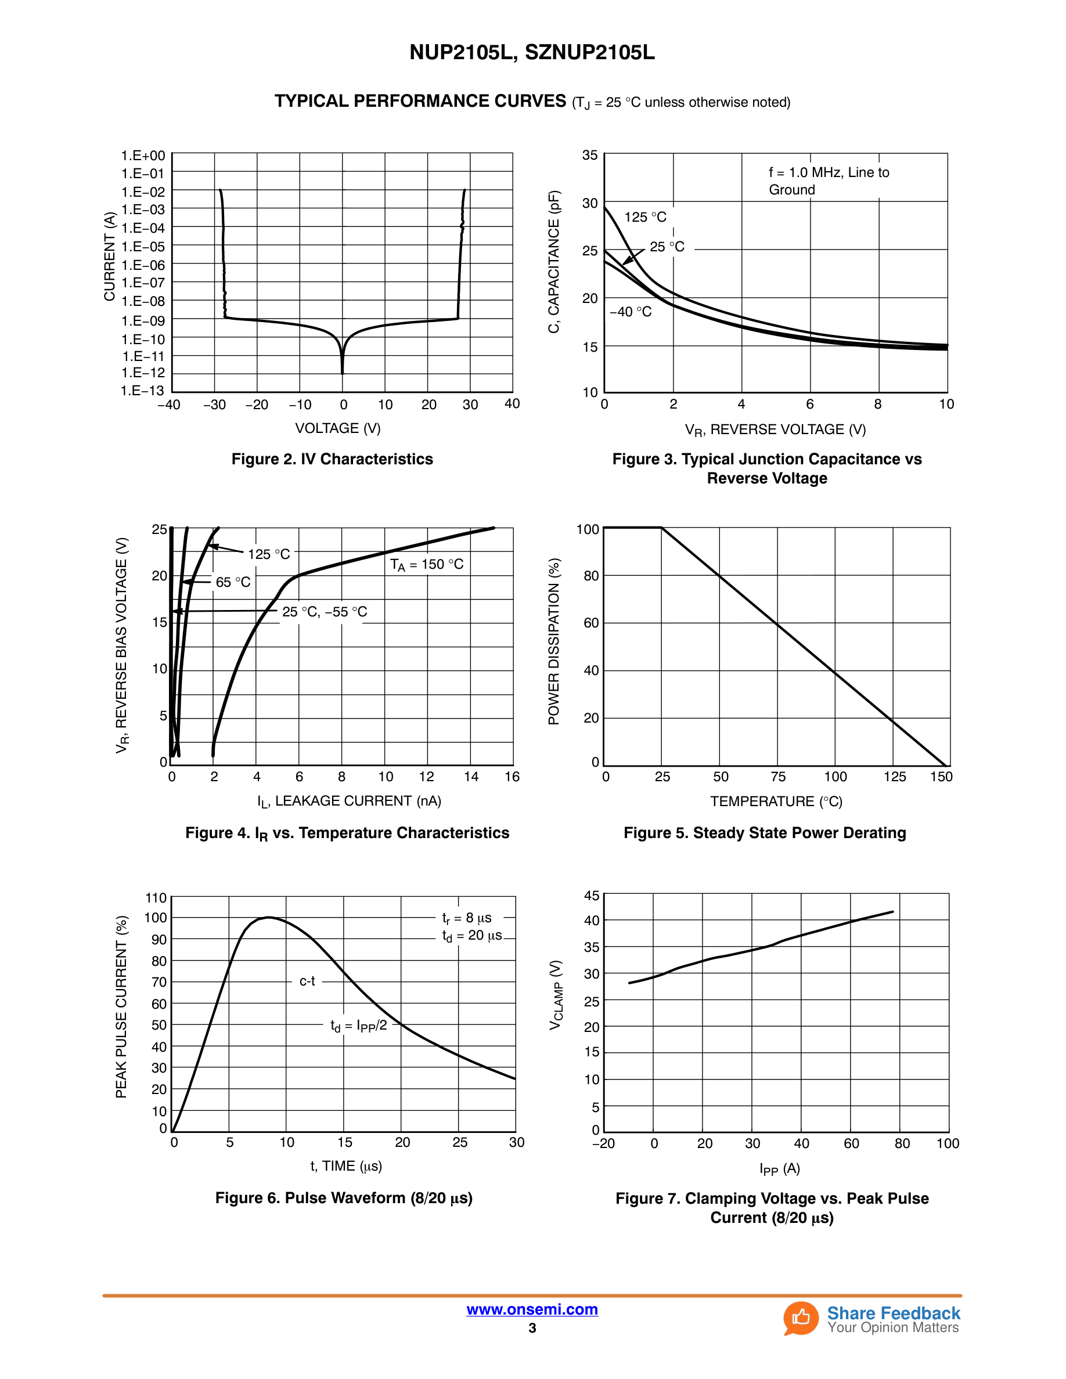
hardware/reviews/visual_inspections/cp2-schematic/iter2/reviewer/source_spotchecks/NUP2105L_onsemi_p3.png
