kaanow/volthium_reader/hardware/reviews/visual_inspections/cp2-schematic/iter2/reviewer/source_spotchecks/TCAN332_p5.png

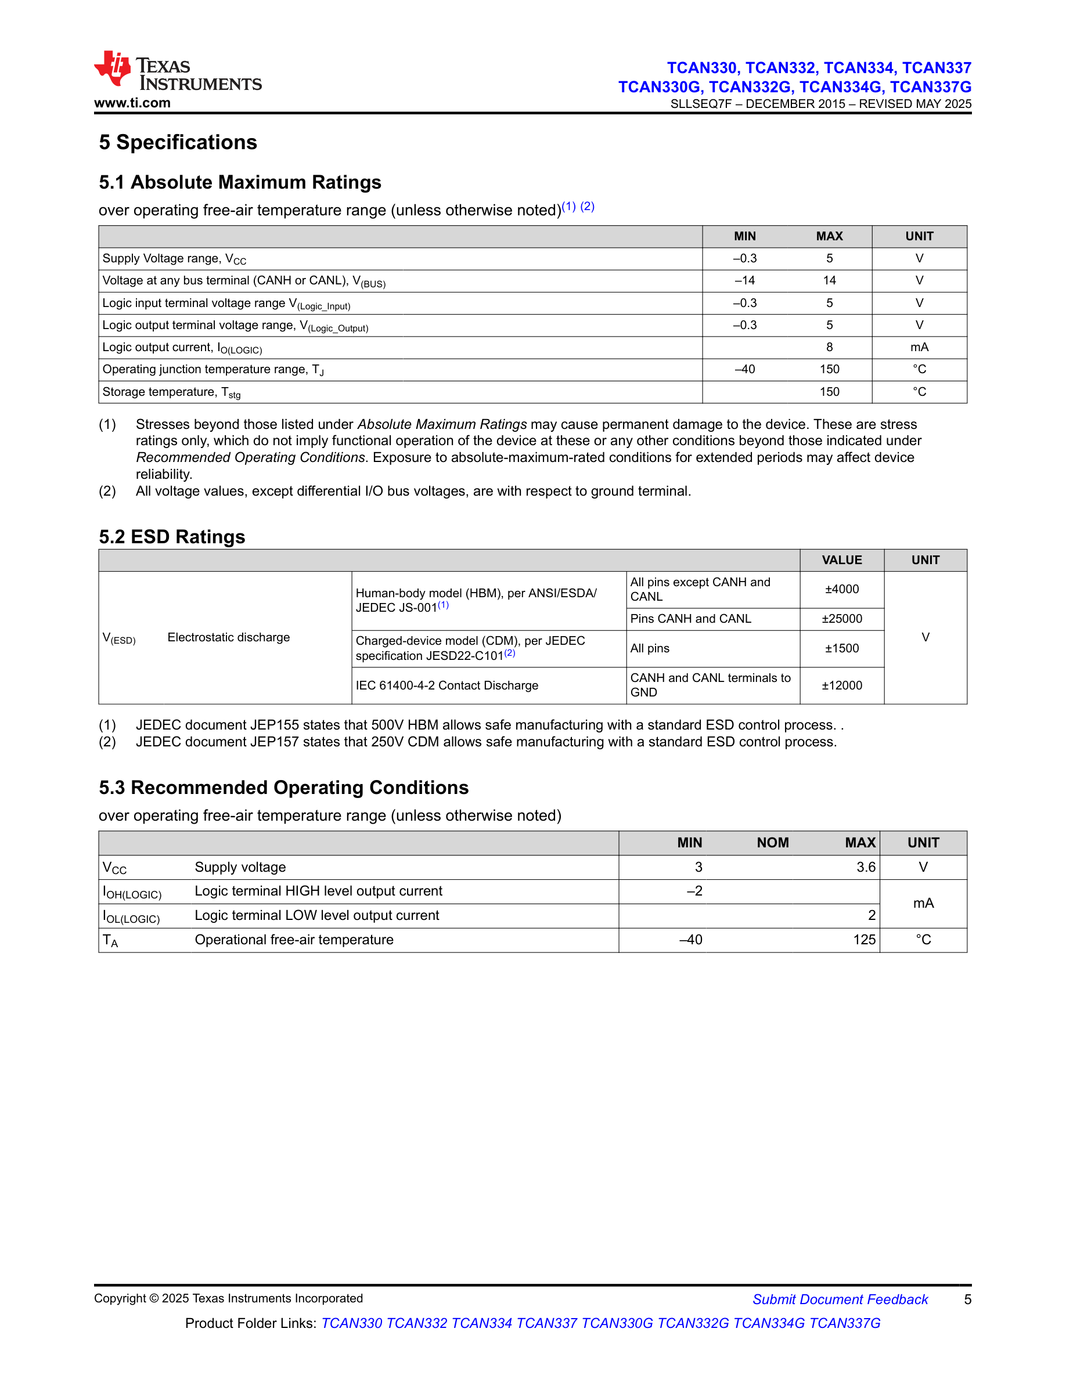
hardware/reviews/visual_inspections/cp2-schematic/iter2/reviewer/source_spotchecks/TCAN332_p5.png
