kaanow/volthium_reader/hardware/reviews/visual_inspections/cp2-schematic/iter2/reviewer/source_spotchecks/Wurth_61200621621_p1.png

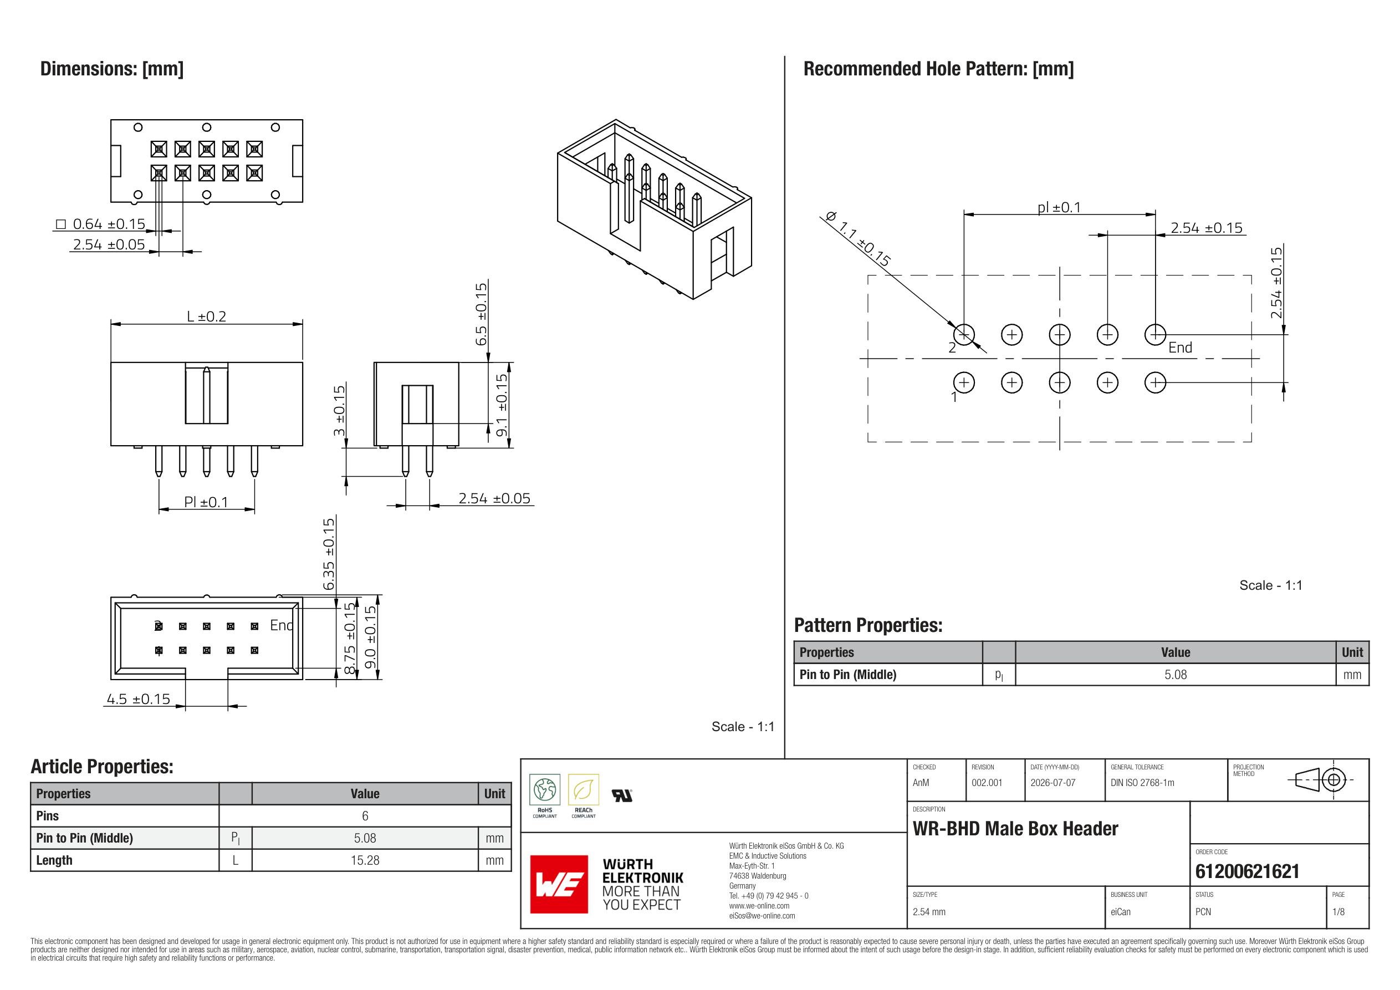
hardware/reviews/visual_inspections/cp2-schematic/iter2/reviewer/source_spotchecks/Wurth_61200621621_p1.png
