kaanow/volthium_reader/hardware/reviews/visual_inspections/cp2-schematic/iter3/designer/conn_j2_rjhse5380_crop.png

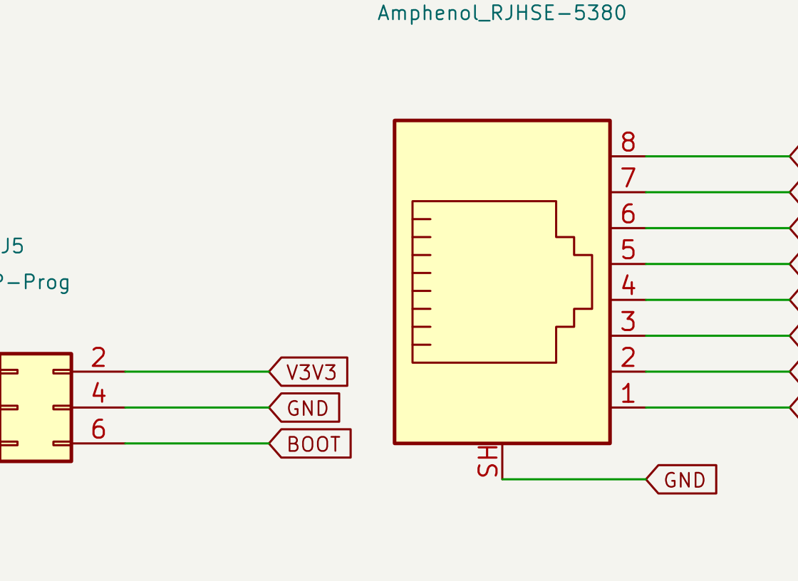
hardware/reviews/visual_inspections/cp2-schematic/iter3/designer/conn_j2_rjhse5380_crop.png
