kaanow/volthium_reader/hardware/reviews/visual_inspections/cp2-schematic/iter3/reviewer/battery_p1_eye_crop_01.png

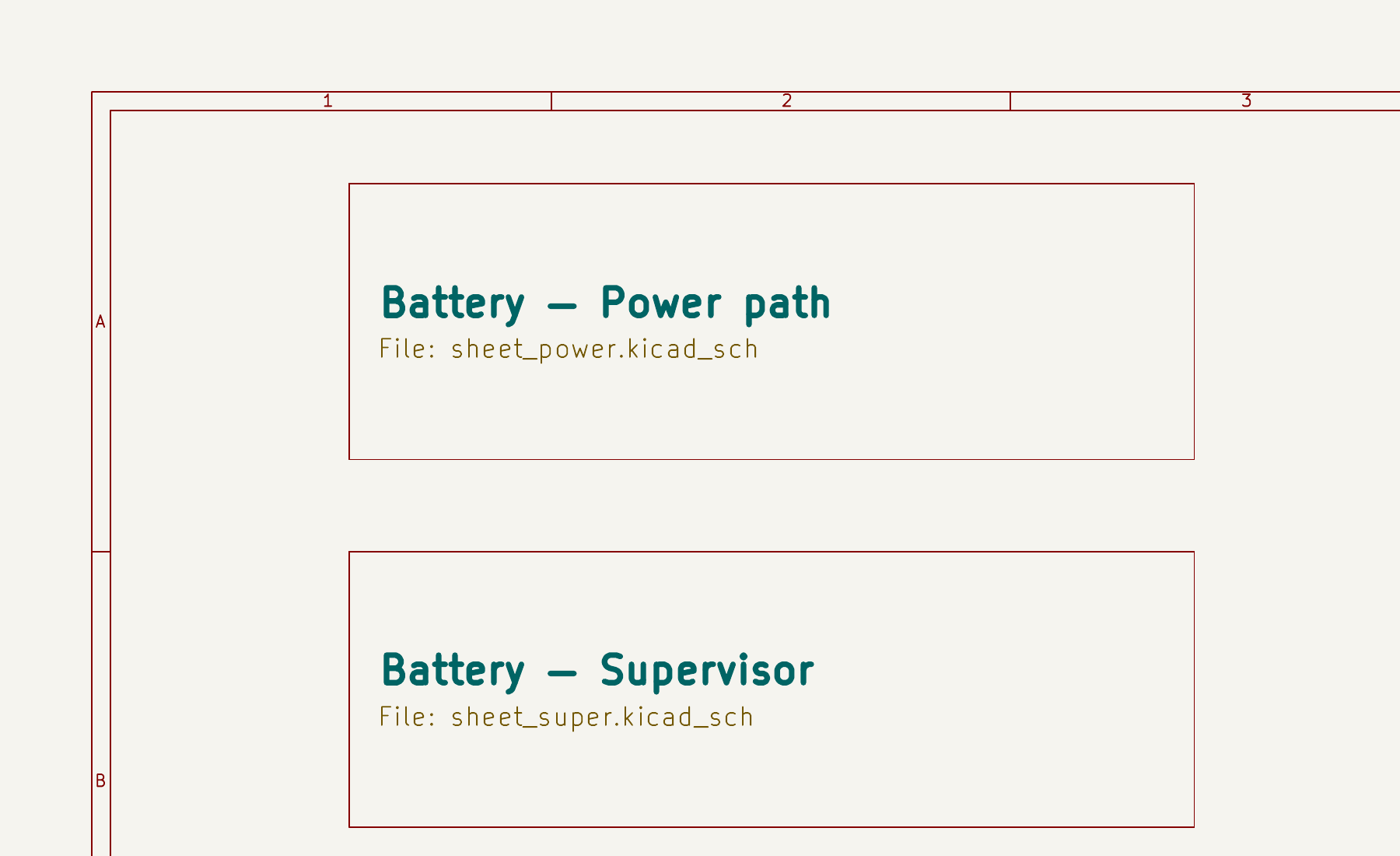
hardware/reviews/visual_inspections/cp2-schematic/iter3/reviewer/battery_p1_eye_crop_01.png
