kaanow/volthium_reader/hardware/reviews/visual_inspections/cp2-schematic/iter3/reviewer/battery_p4_full_300dpi.png

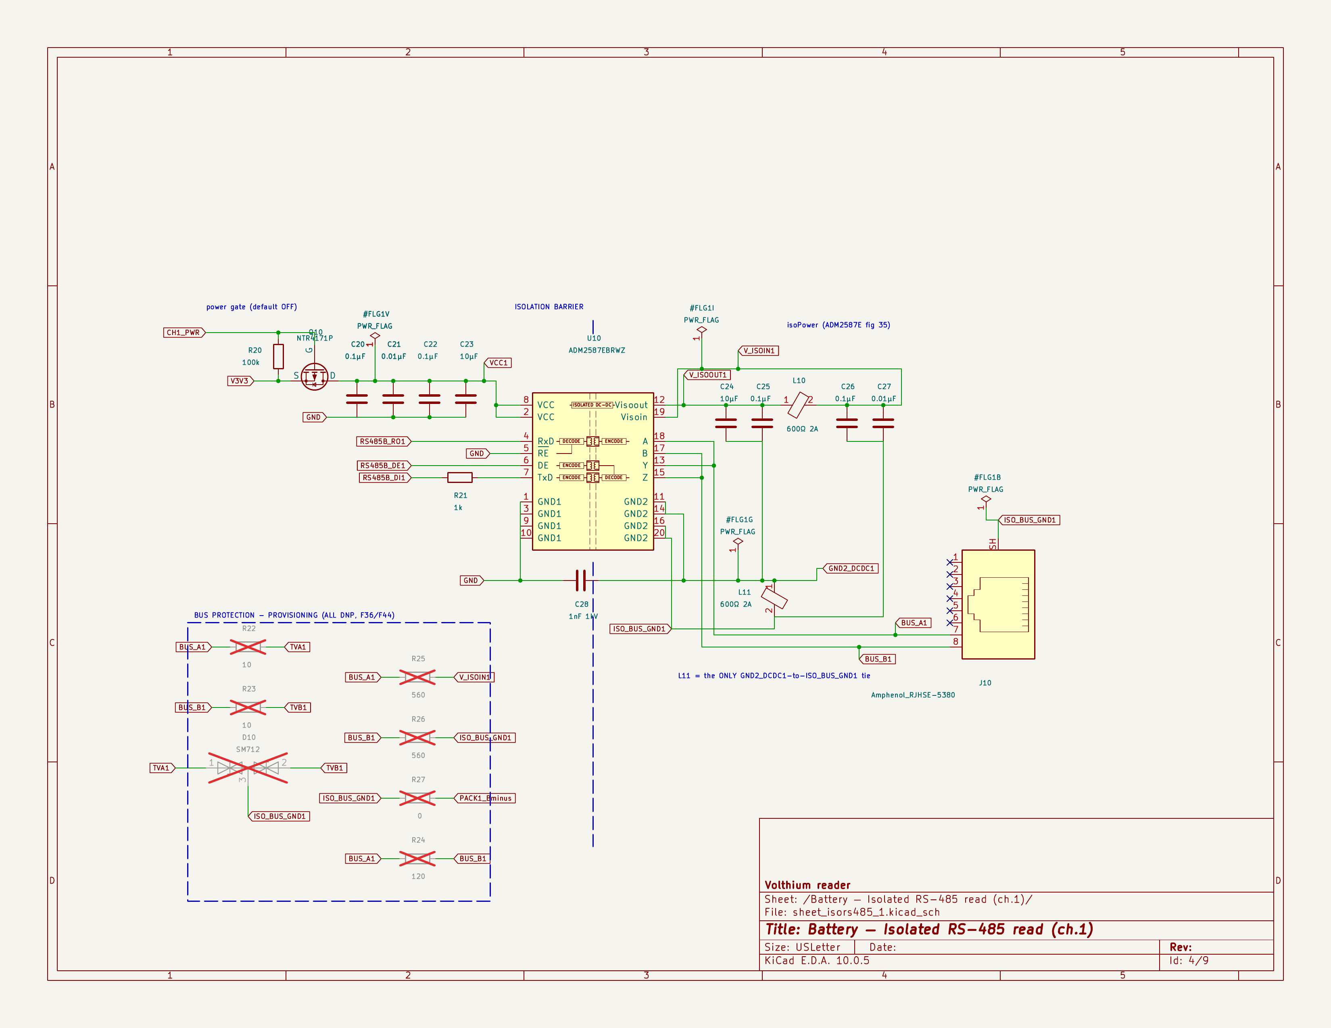
hardware/reviews/visual_inspections/cp2-schematic/iter3/reviewer/battery_p4_full_300dpi.png
