kaanow/volthium_reader/hardware/reviews/visual_inspections/cp2-schematic/iter3/reviewer/battery_p5_eye_crop_03.png

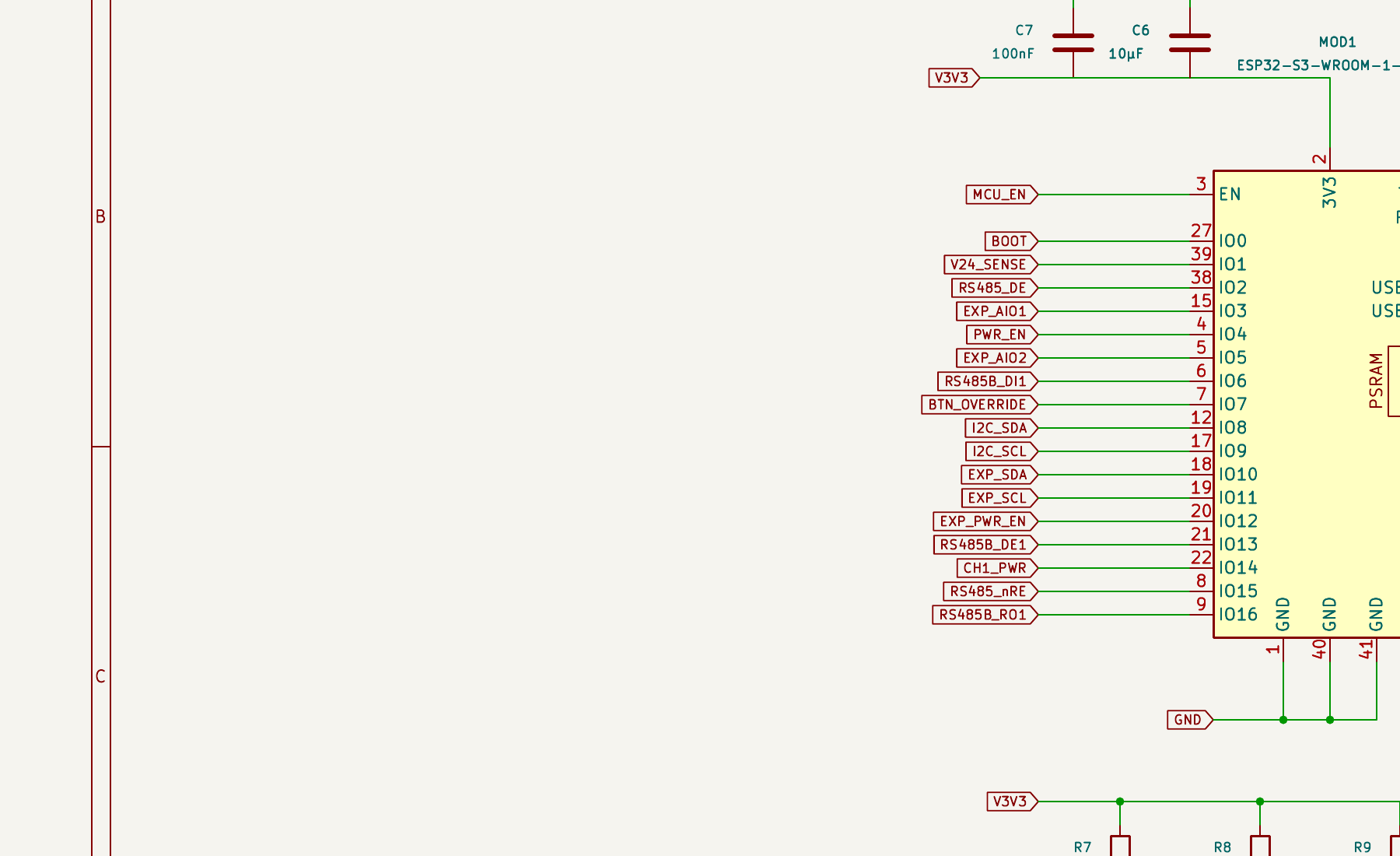
hardware/reviews/visual_inspections/cp2-schematic/iter3/reviewer/battery_p5_eye_crop_03.png
