kaanow/volthium_reader/hardware/reviews/visual_inspections/cp2-schematic/iter3/reviewer/battery_p9_eye_crop_06.png

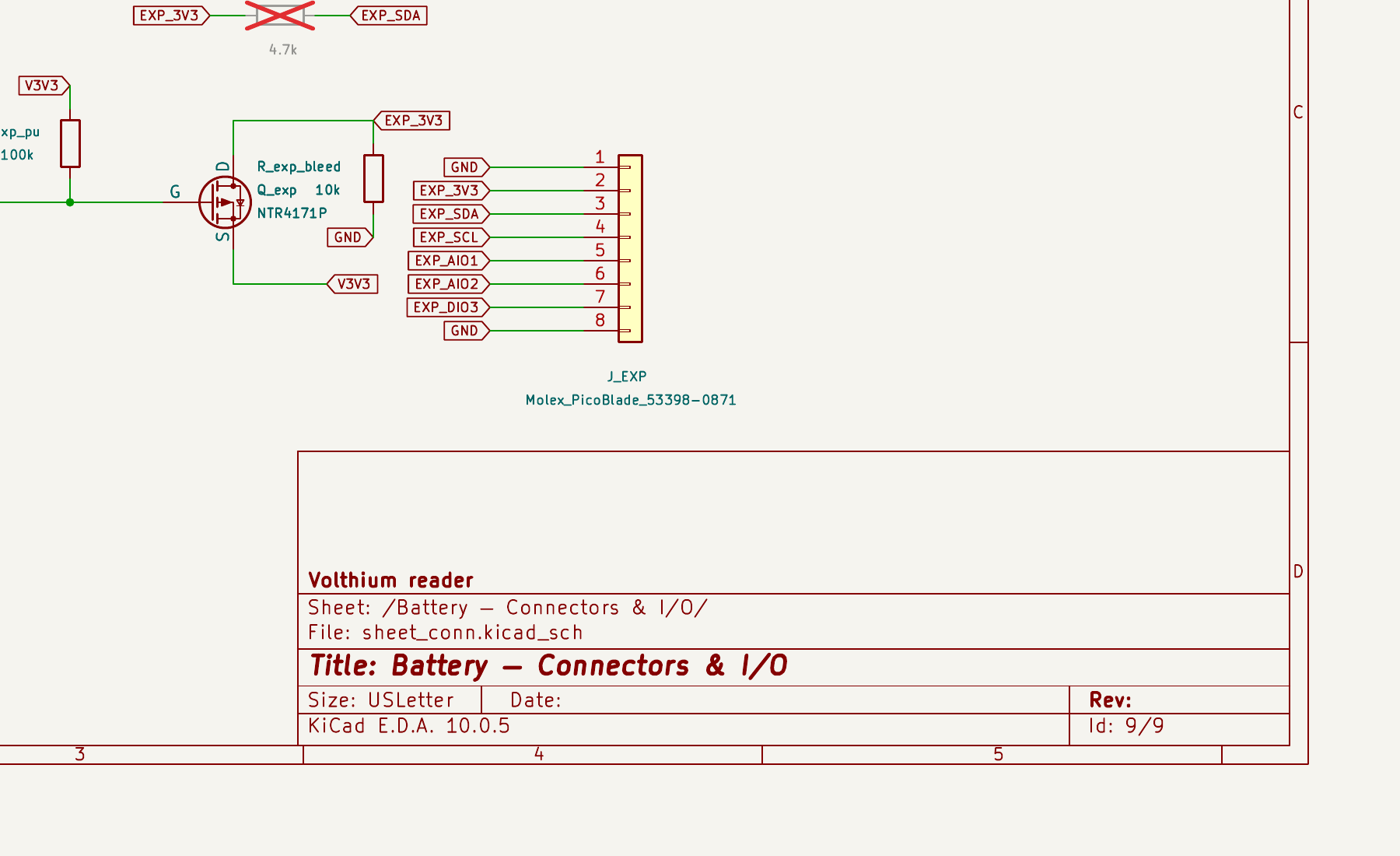
hardware/reviews/visual_inspections/cp2-schematic/iter3/reviewer/battery_p9_eye_crop_06.png
