kaanow/volthium_reader/hardware/reviews/visual_inspections/cp2-schematic/iter3/reviewer/source_spotchecks/xanbus_pdf_page_18.png

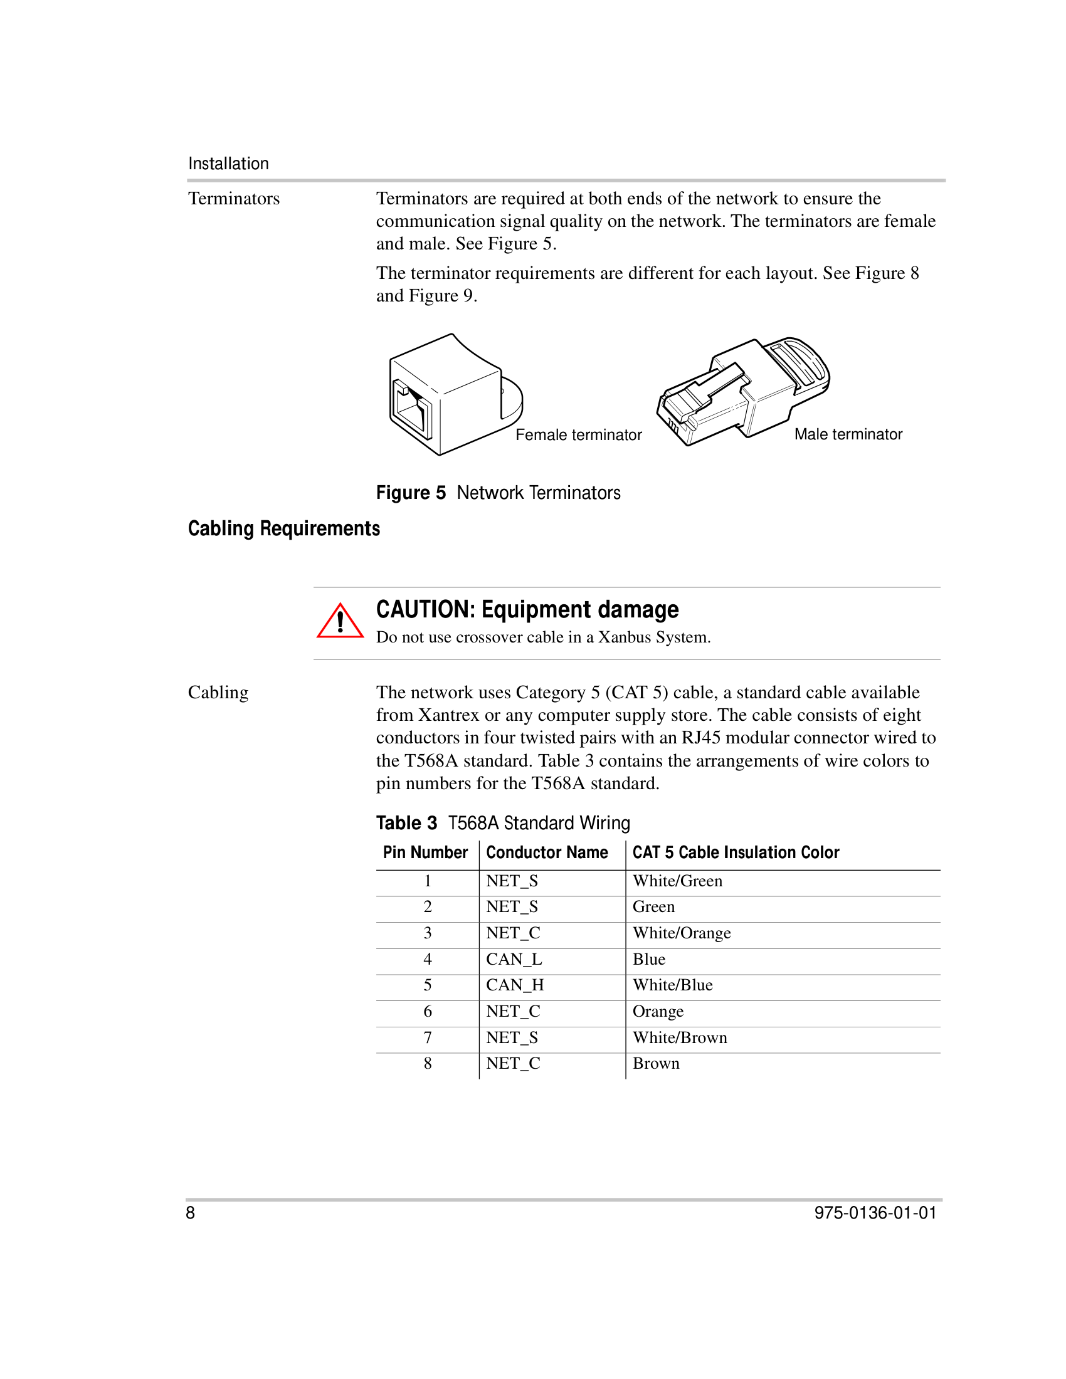
hardware/reviews/visual_inspections/cp2-schematic/iter3/reviewer/source_spotchecks/xanbus_pdf_page_18.png
