kaanow/volthium_reader/hardware/reviews/visual_inspections/cp2-schematic/iter4/reviewer/battery_p3_eye_crop_06.png

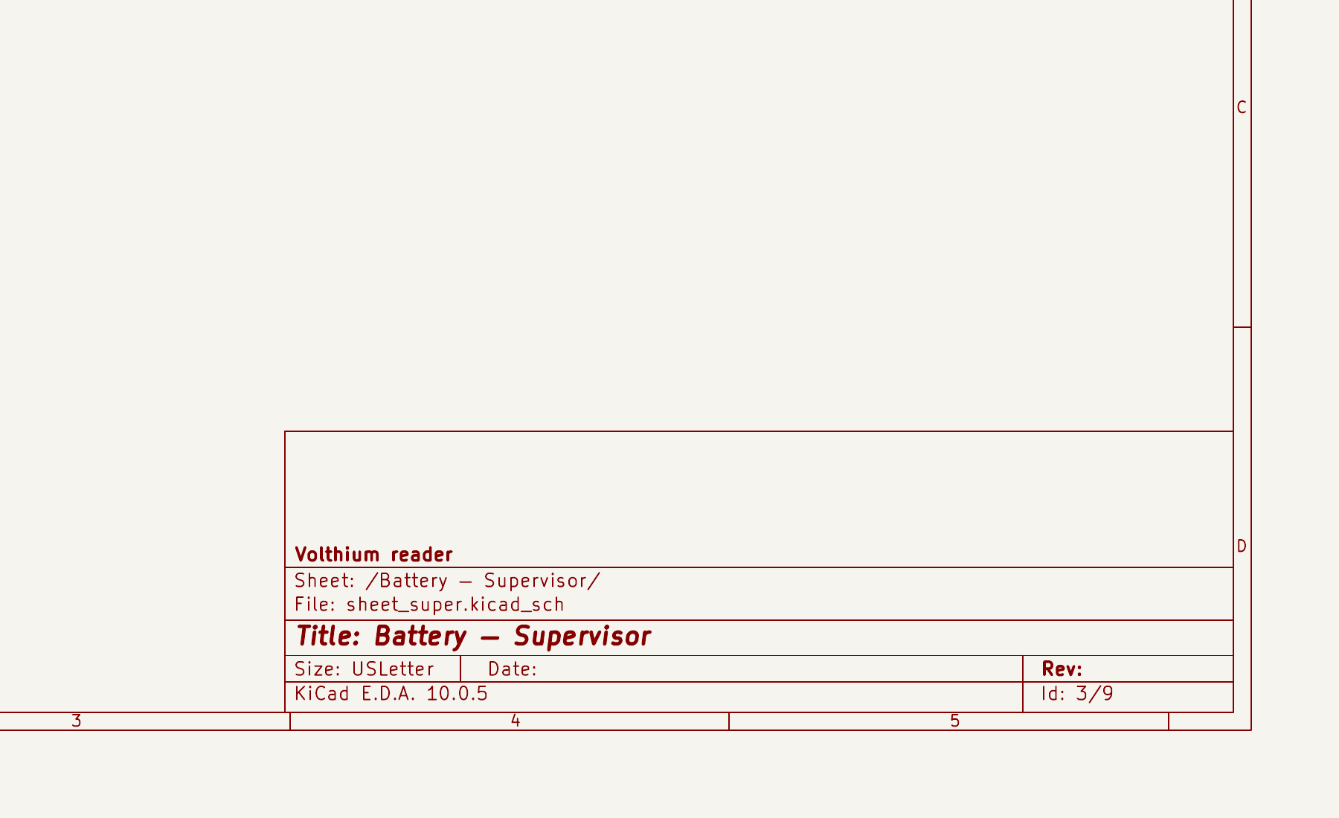
hardware/reviews/visual_inspections/cp2-schematic/iter4/reviewer/battery_p3_eye_crop_06.png
