kaanow/volthium_reader/hardware/reviews/visual_inspections/cp2-schematic/iter4/reviewer/battery_p4_eye_crop_03.png

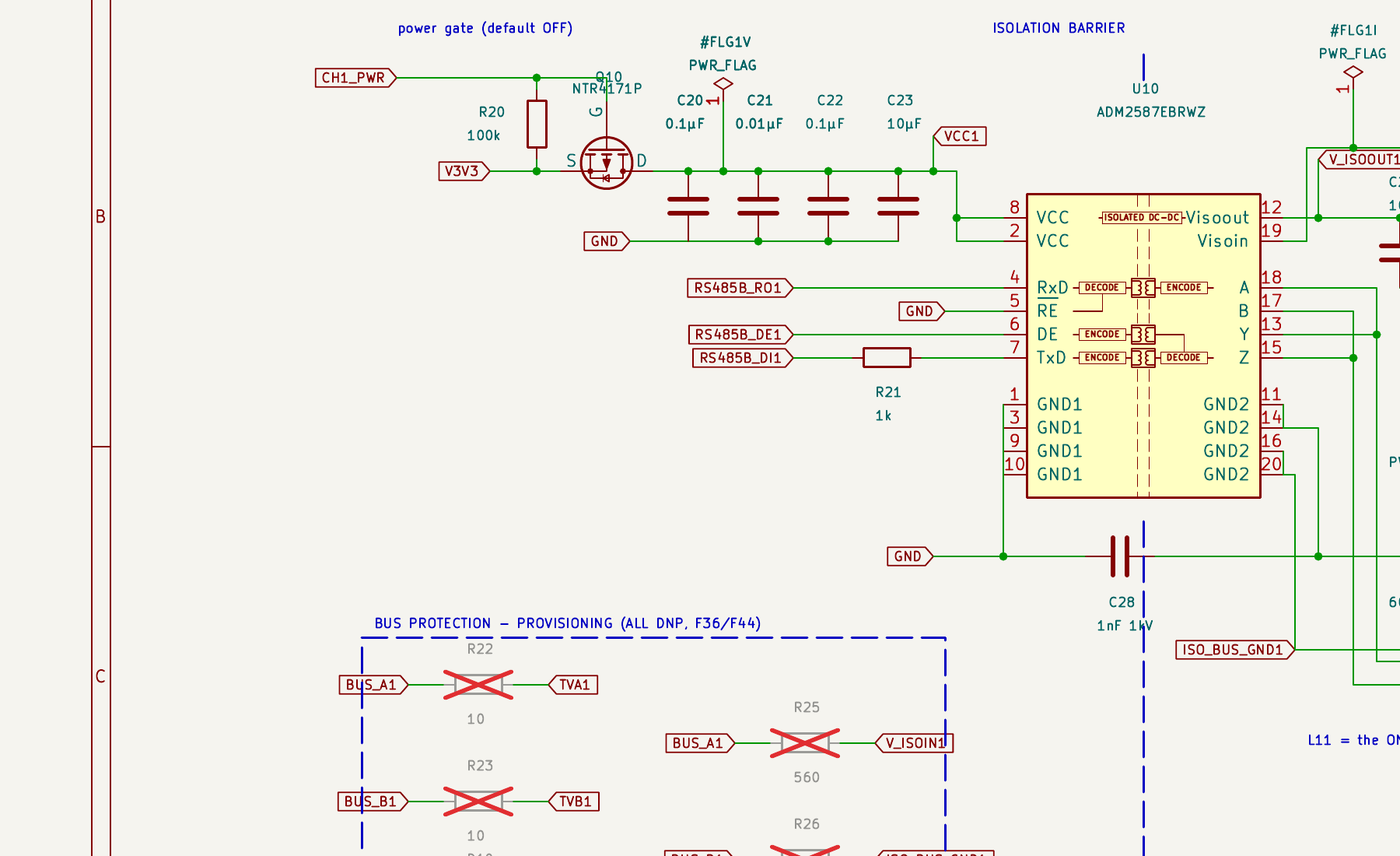
hardware/reviews/visual_inspections/cp2-schematic/iter4/reviewer/battery_p4_eye_crop_03.png
