kaanow/volthium_reader/hardware/reviews/visual_inspections/cp2-schematic/iter4/reviewer/battery_p5_eye_crop_01.png

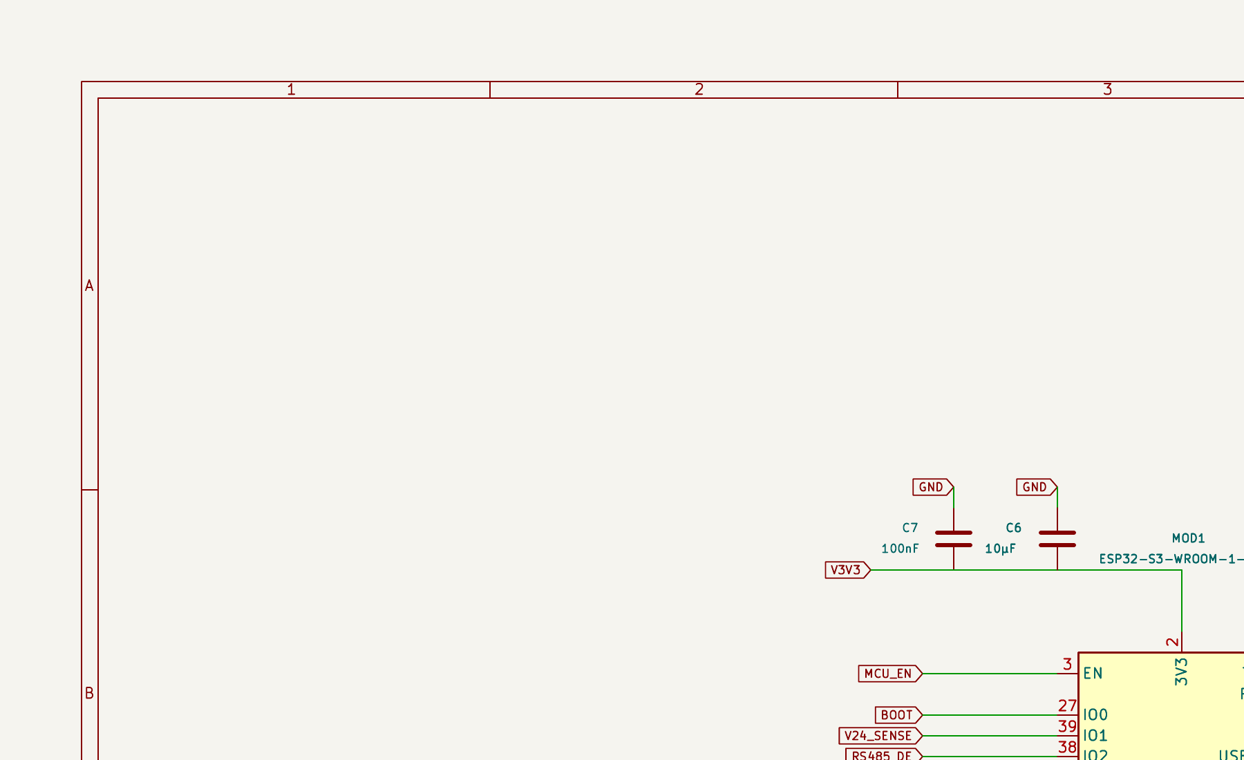
hardware/reviews/visual_inspections/cp2-schematic/iter4/reviewer/battery_p5_eye_crop_01.png
