kaanow/volthium_reader/hardware/reviews/visual_inspections/cp2-schematic/iter4/reviewer/battery_p6_eye_crop_02.png

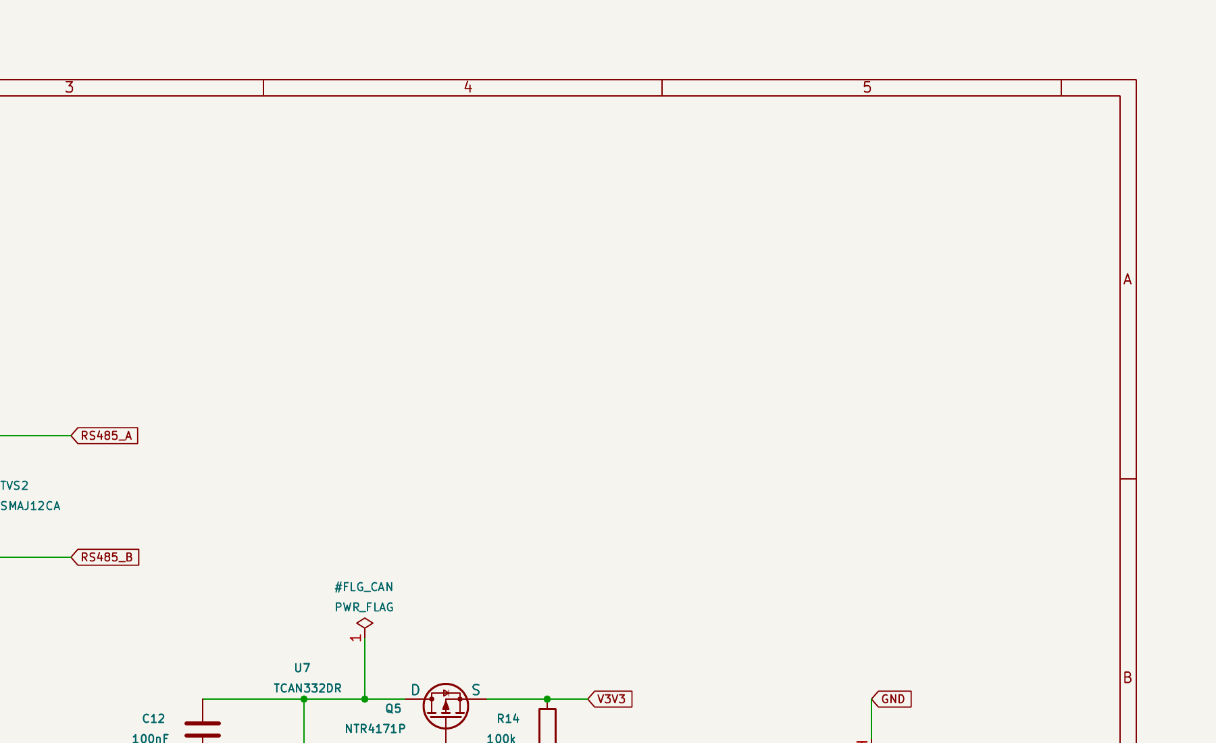
hardware/reviews/visual_inspections/cp2-schematic/iter4/reviewer/battery_p6_eye_crop_02.png
