kaanow/volthium_reader/hardware/reviews/visual_inspections/cp3-placement/iter1/reviewer/crop_iso_ch2.png

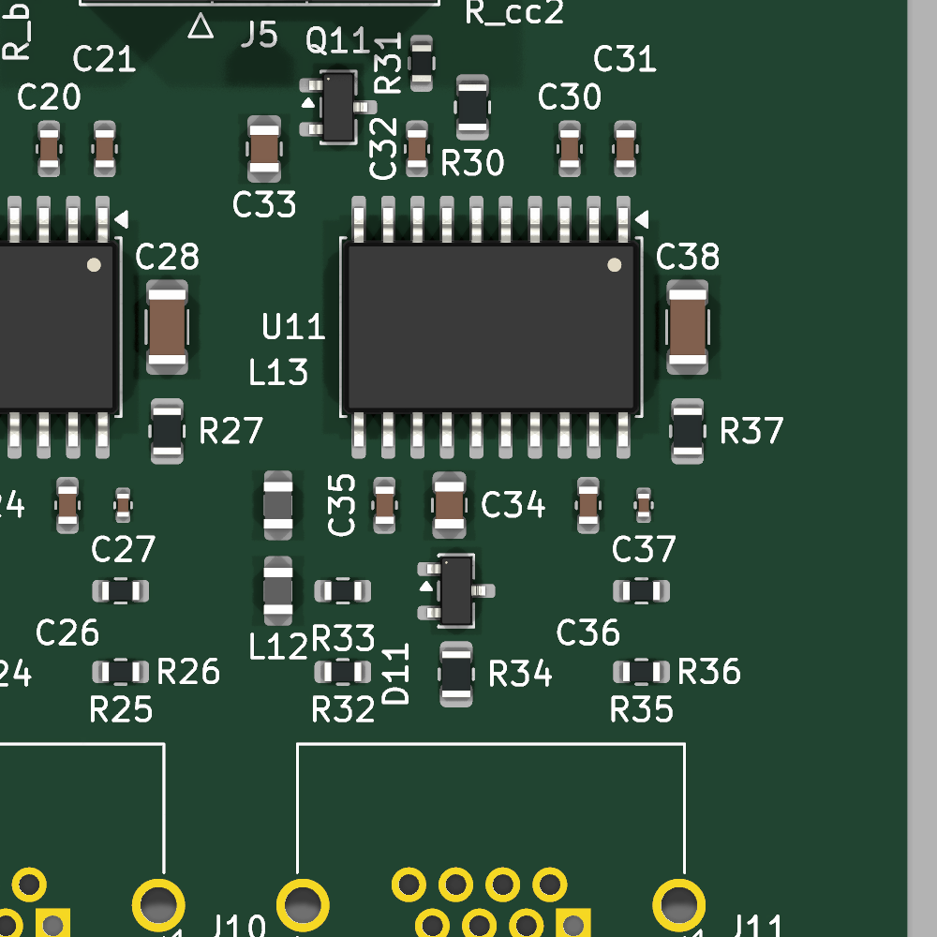
hardware/reviews/visual_inspections/cp3-placement/iter1/reviewer/crop_iso_ch2.png
