kaanow/volthium_reader/hardware/reviews/visual_inspections/cp3-placement/iter1/reviewer/crop_service_center.png

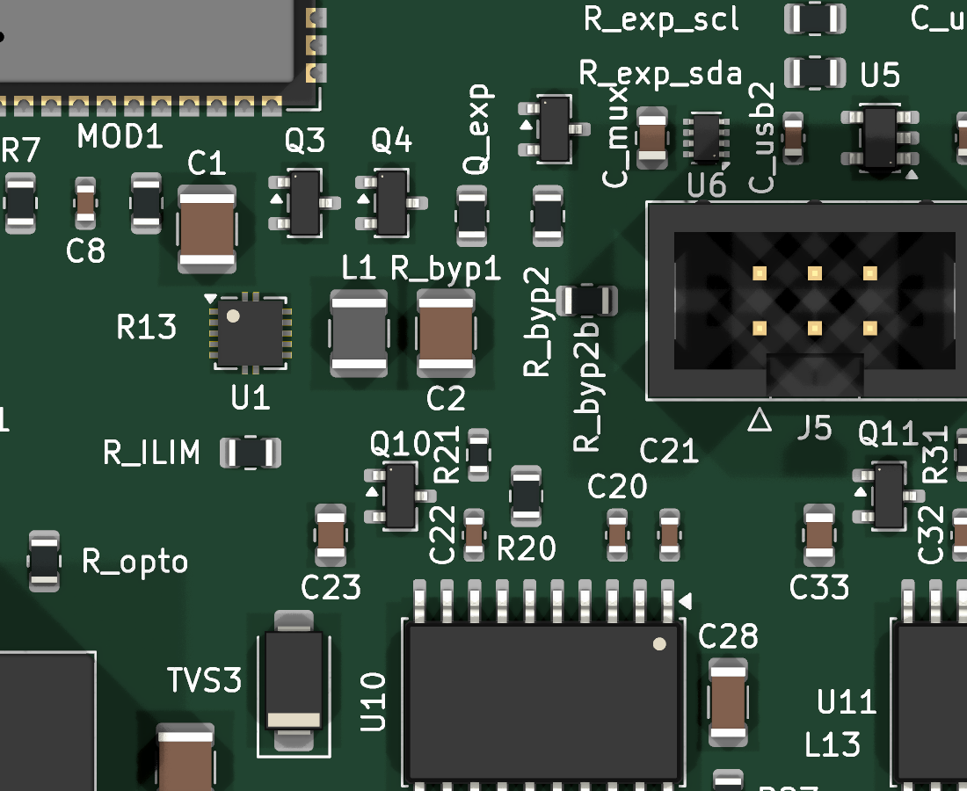
hardware/reviews/visual_inspections/cp3-placement/iter1/reviewer/crop_service_center.png
