kaanow/volthium_reader/hardware/reviews/visual_inspections/cp3-placement/iter1/snapshots/render_bottom.png

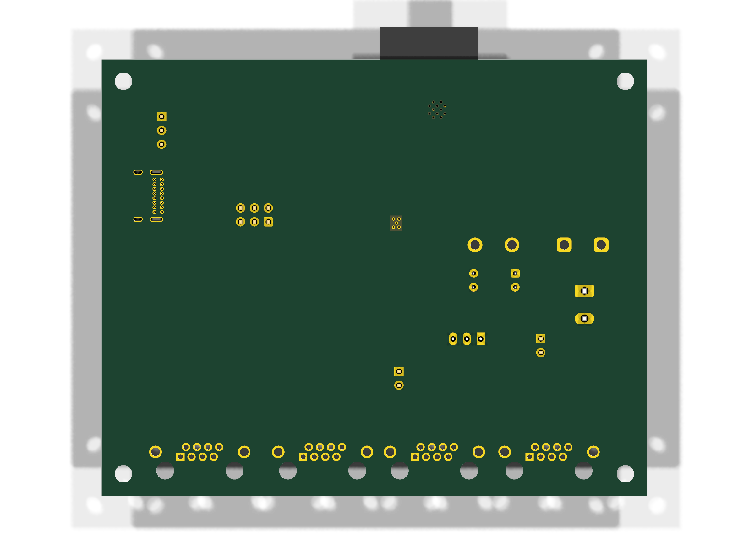
hardware/reviews/visual_inspections/cp3-placement/iter1/snapshots/render_bottom.png
