kaanow/volthium_reader/hardware/reviews/visual_inspections/cp3-placement/iter3/reviewer/crop_power_entry.png

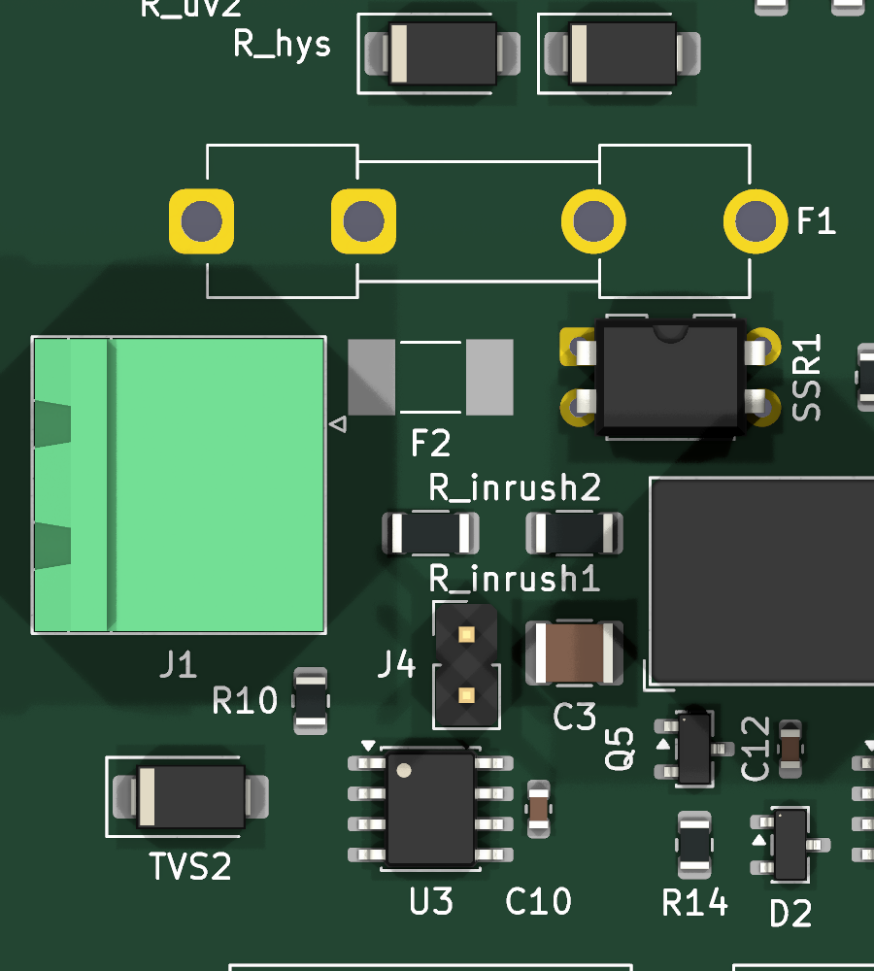
hardware/reviews/visual_inspections/cp3-placement/iter3/reviewer/crop_power_entry.png
