kaanow/volthium_reader/hardware/reviews/visual_inspections/cp3-placement/iter4/iso_ch1.png

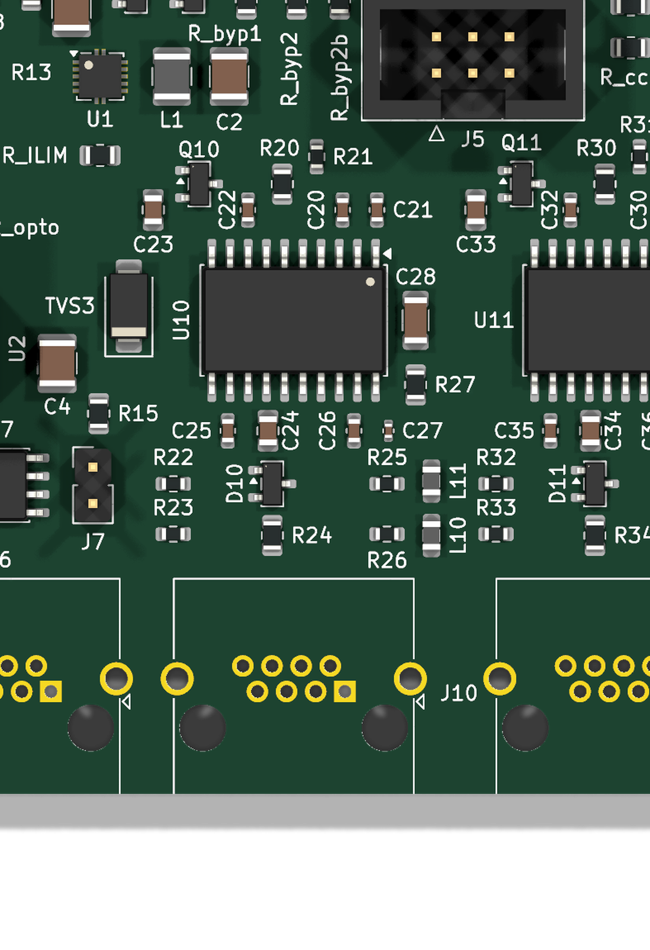
hardware/reviews/visual_inspections/cp3-placement/iter4/iso_ch1.png
