kaanow/volthium_reader/hardware/reviews/visual_inspections/cp3-placement/iter4/mod1_rtc.png

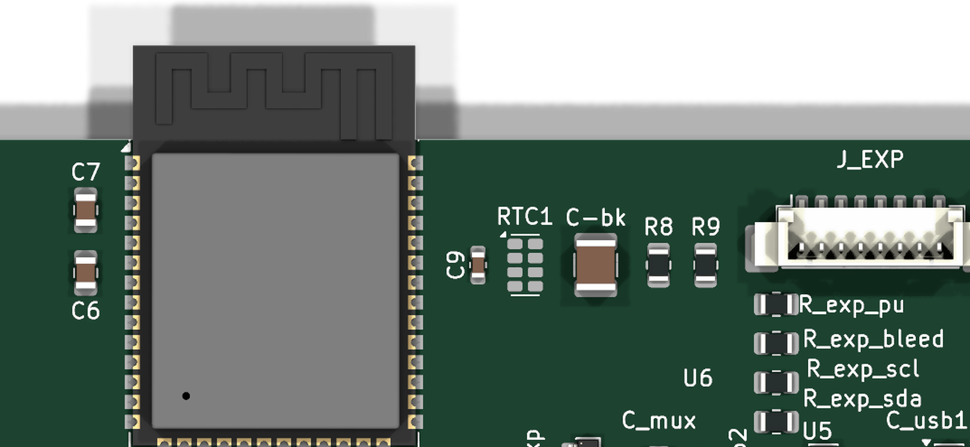
hardware/reviews/visual_inspections/cp3-placement/iter4/mod1_rtc.png
