kaanow/volthium_reader/hardware/reviews/visual_inspections/cp3-placement/iter4/usb_east.png

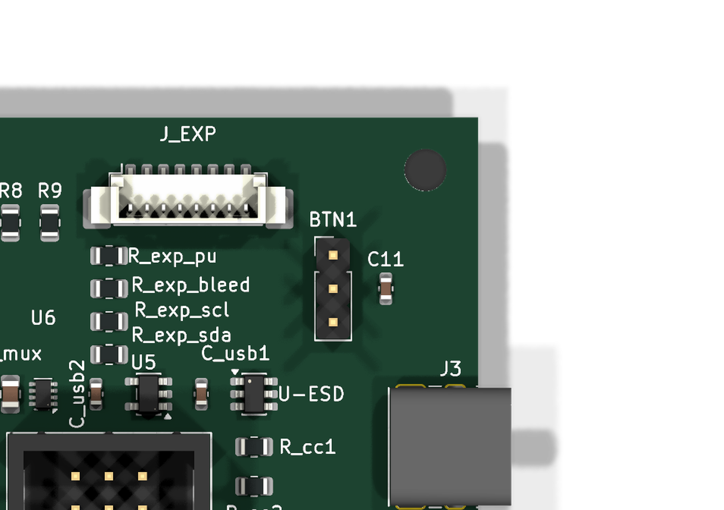
hardware/reviews/visual_inspections/cp3-placement/iter4/usb_east.png
