kaanow/volthium_reader/hardware/reviews/visual_inspections/cp3-placement/iter4/w_power_entry.png

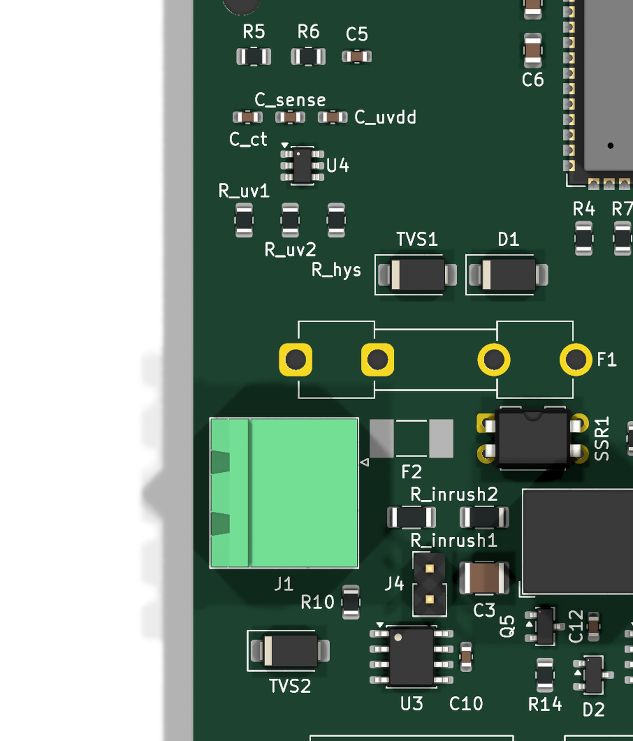
hardware/reviews/visual_inspections/cp3-placement/iter4/w_power_entry.png
