kaanow/volthium_reader/hardware/reviews/visual_inspections/cp3-placement/iter5/reviewer/crop_region_05.png

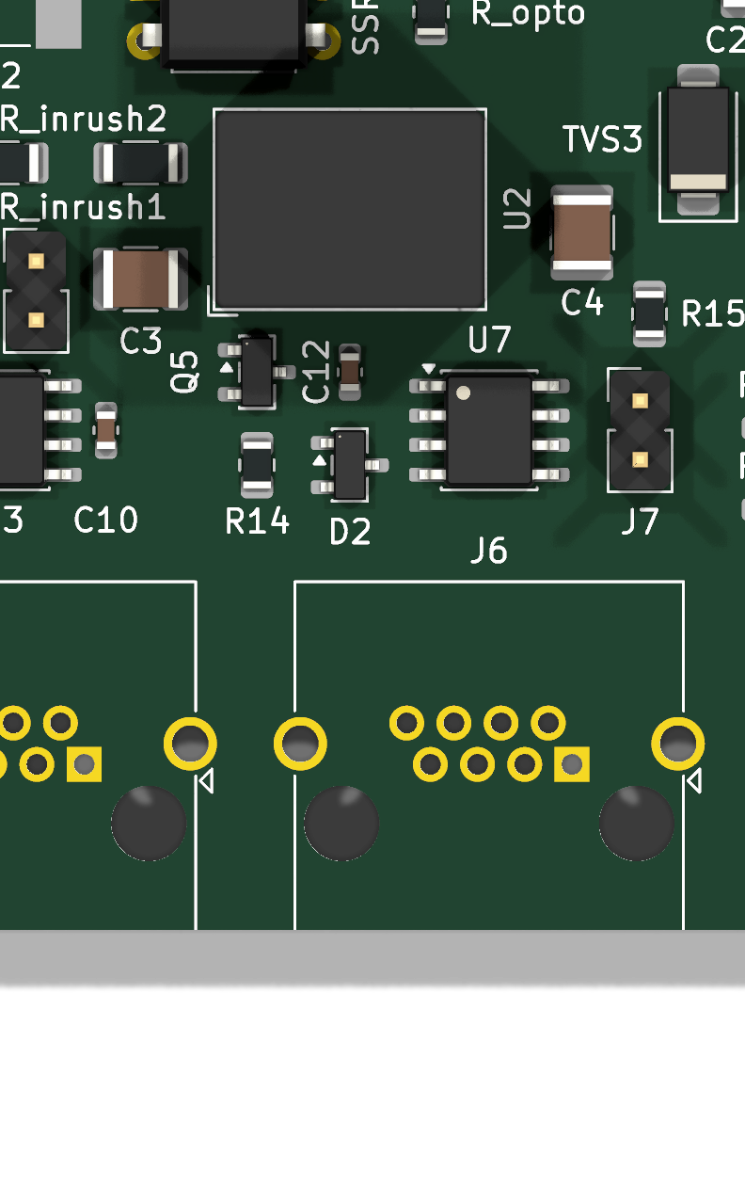
hardware/reviews/visual_inspections/cp3-placement/iter5/reviewer/crop_region_05.png
