kaanow/volthium_reader/hardware/reviews/visual_inspections/cp3-placement/iter5/reviewer/full_bottom_3d.png

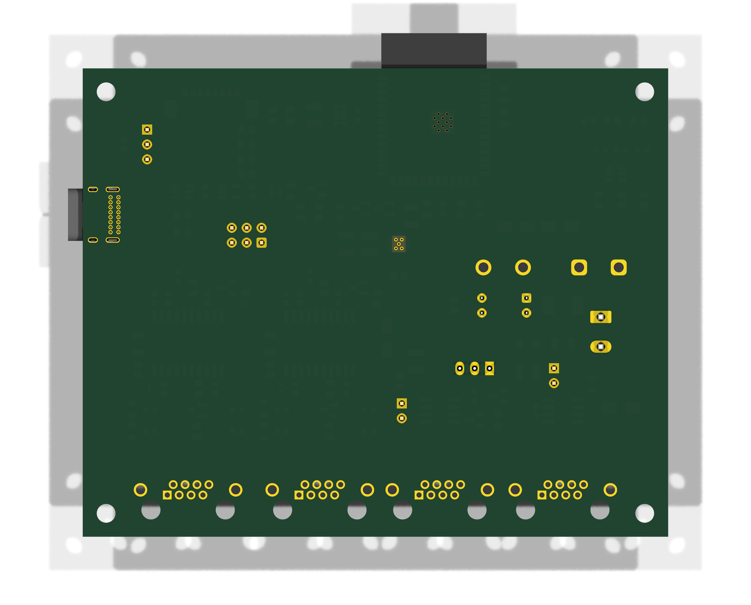
hardware/reviews/visual_inspections/cp3-placement/iter5/reviewer/full_bottom_3d.png
