kaanow/volthium_reader/hardware/reviews/visual_inspections/cp3-placement/iter9/reviewer/crop_region_01.png

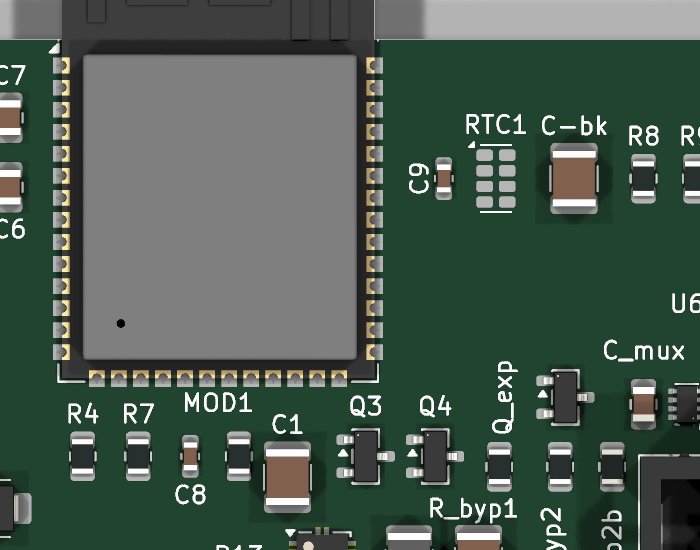
hardware/reviews/visual_inspections/cp3-placement/iter9/reviewer/crop_region_01.png
