kaanow/volthium_reader/hardware/reviews/visual_inspections/cp3-placement/iter13/reviewer/crop_contact_sheet.png

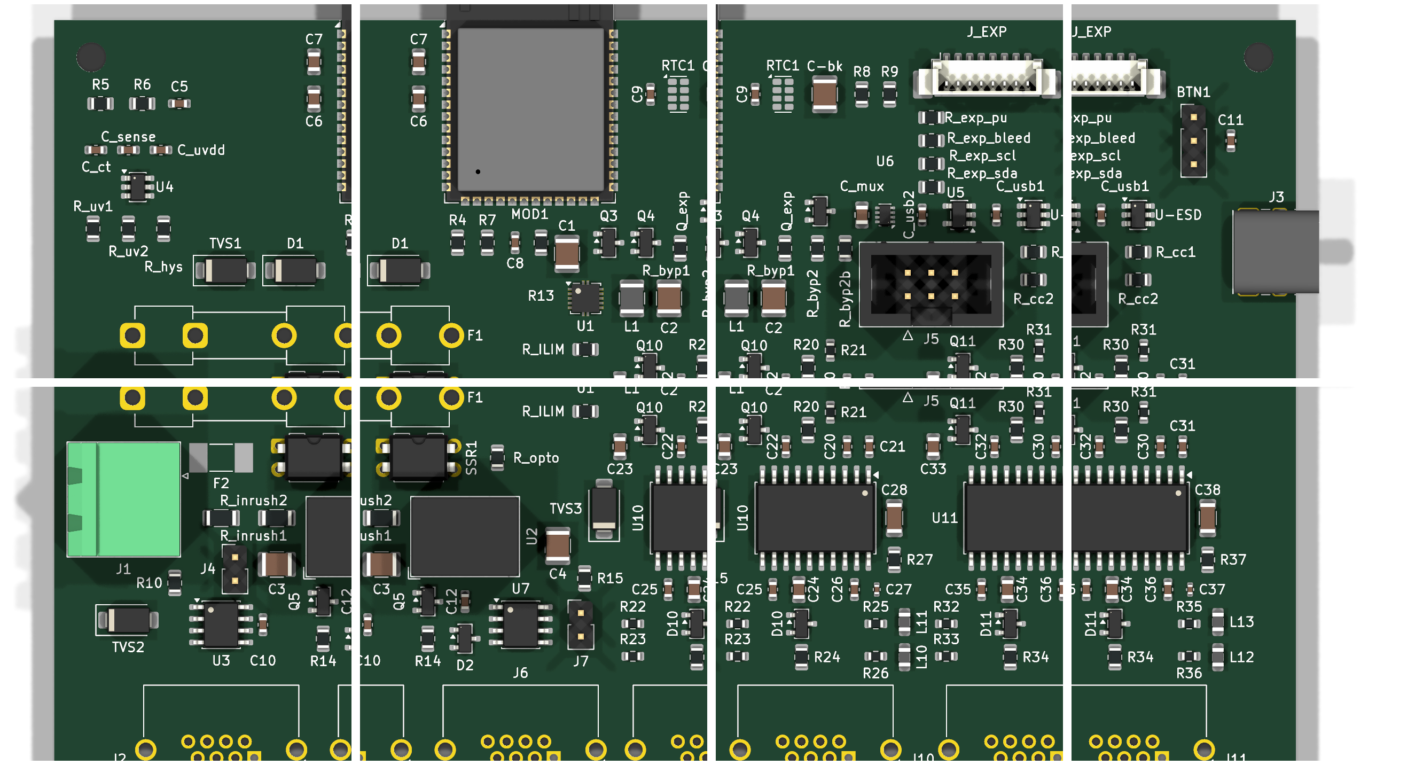
hardware/reviews/visual_inspections/cp3-placement/iter13/reviewer/crop_contact_sheet.png
