kaanow/volthium_reader/hardware/reviews/visual_inspections/cp3-placement/iter13/reviewer/crop_region_02.png

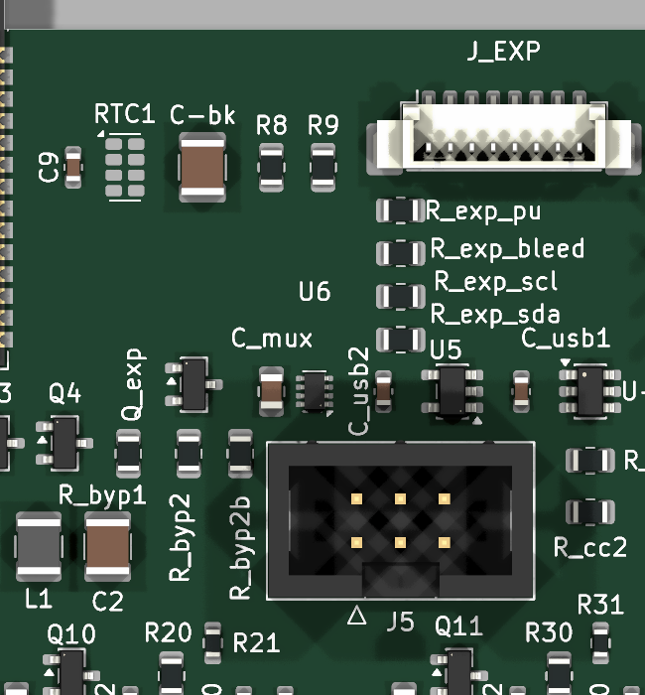
hardware/reviews/visual_inspections/cp3-placement/iter13/reviewer/crop_region_02.png
