kaanow/volthium_reader/hardware/reviews/visual_inspections/cp3-placement/iter15/reviewer/full_top_3d.png

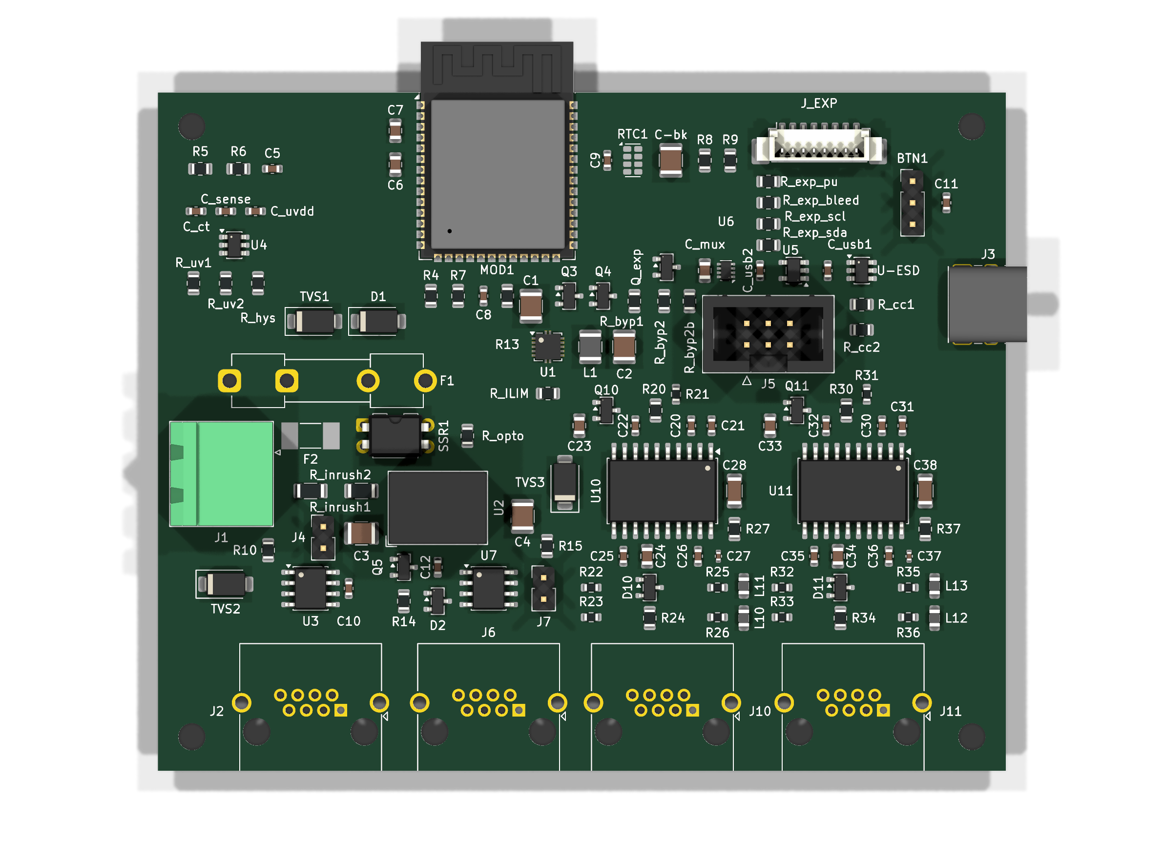
hardware/reviews/visual_inspections/cp3-placement/iter15/reviewer/full_top_3d.png
