kaanow/volthium_reader/hardware/reviews/visual_inspections/cp4-display-placement/iter2/bottom_4k.png

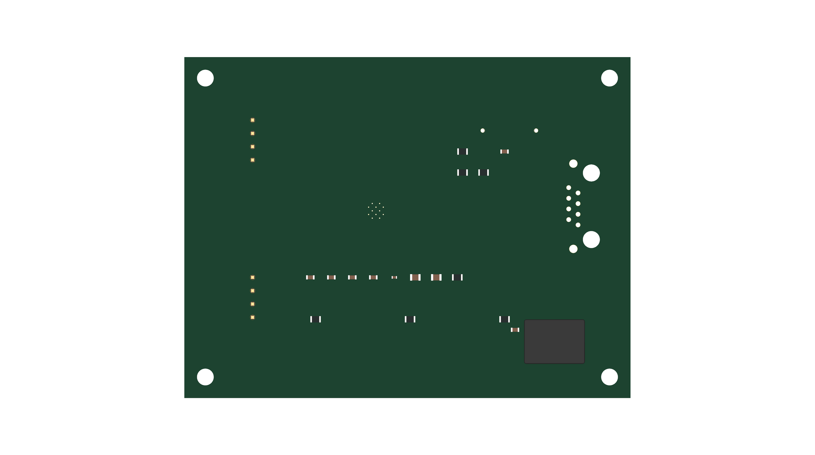
hardware/reviews/visual_inspections/cp4-display-placement/iter2/bottom_4k.png
