kaanow/volthium_reader/hardware/reviews/visual_inspections/cp4-display-placement/iter2/region_j2_ffc.png

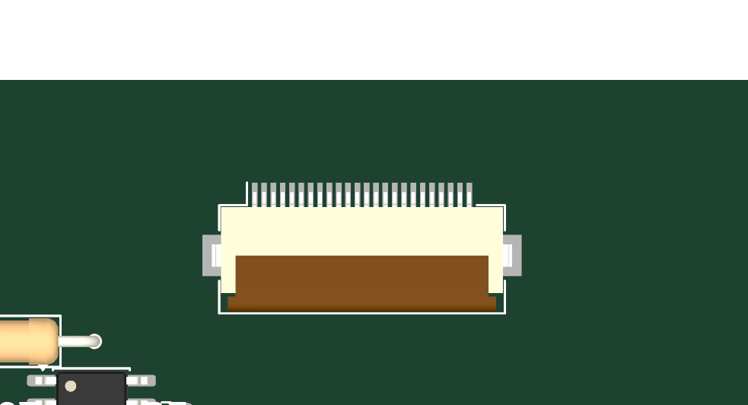
hardware/reviews/visual_inspections/cp4-display-placement/iter2/region_j2_ffc.png
