kaanow/volthium_reader/hardware/reviews/visual_inspections/cp4-display-placement/iter2/region_u1_back.png

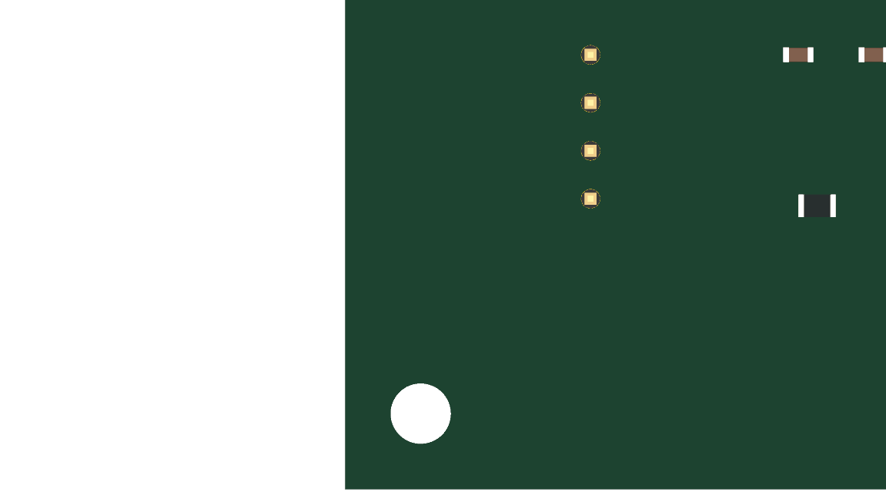
hardware/reviews/visual_inspections/cp4-display-placement/iter2/region_u1_back.png
