kaanow/volthium_reader/hardware/reviews/visual_inspections/cp4-display-placement/iter4/snapshots/top_4k.png

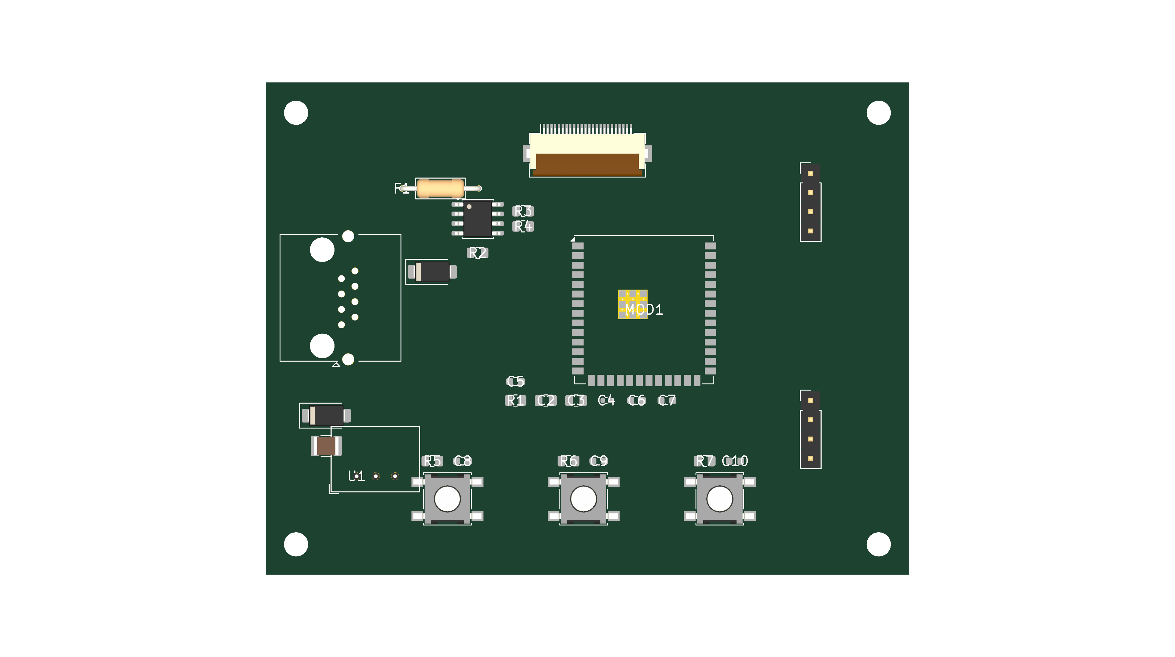
hardware/reviews/visual_inspections/cp4-display-placement/iter4/snapshots/top_4k.png
