kaanow/volthium_reader/hardware/reviews/visual_inspections/cp4-display-placement/iter6/region_btn_back.png

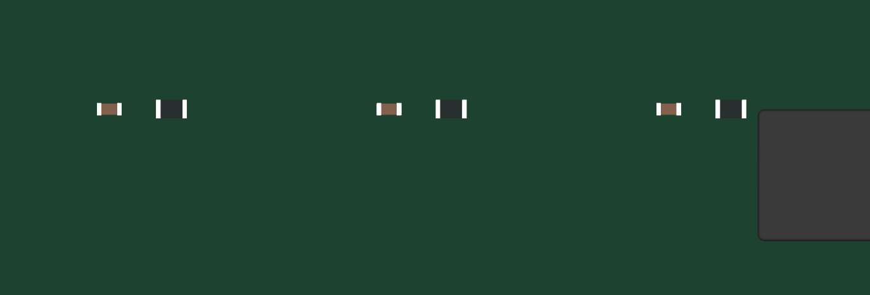
hardware/reviews/visual_inspections/cp4-display-placement/iter6/region_btn_back.png
