kaanow/volthium_reader/hardware/reviews/visual_inspections/cp4-display-placement/iter6/region_j1_rj45.png

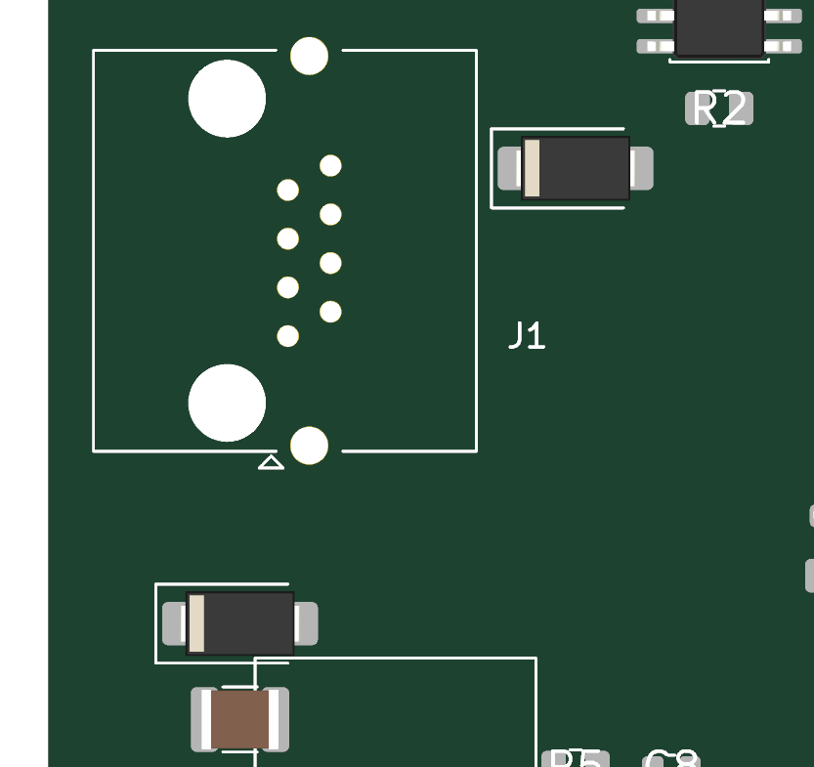
hardware/reviews/visual_inspections/cp4-display-placement/iter6/region_j1_rj45.png
