kaanow/volthium_reader/hardware/reviews/visual_inspections/cp5-routing-drc/iter11/display_bottom_4k.png

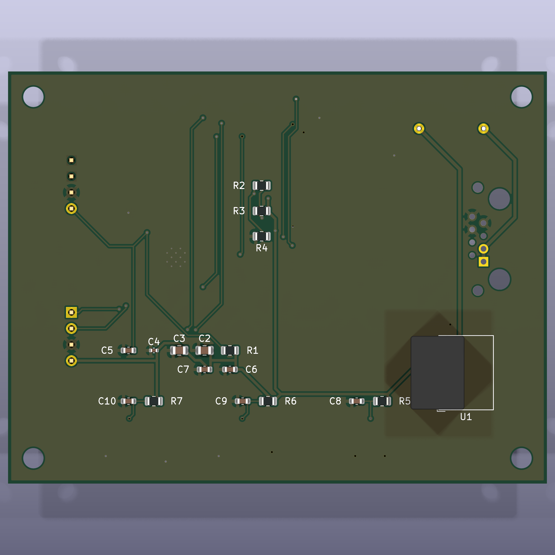
hardware/reviews/visual_inspections/cp5-routing-drc/iter11/display_bottom_4k.png
