kaanow/volthium_reader/hardware/reviews/visual_inspections/cp5-routing-drc/iter13/battery_crop_01_power_input_chain.png

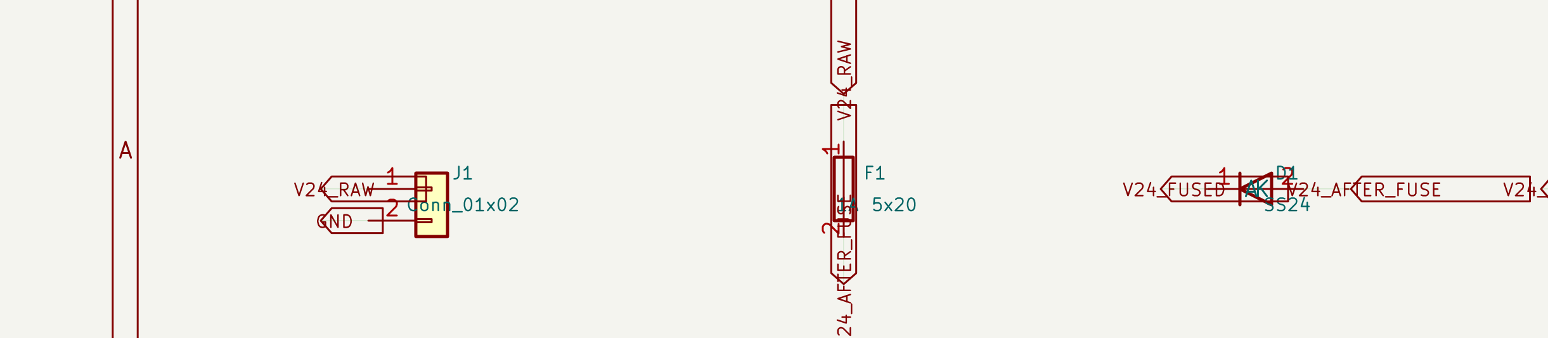
hardware/reviews/visual_inspections/cp5-routing-drc/iter13/battery_crop_01_power_input_chain.png
