kaanow/volthium_reader/hardware/reviews/visual_inspections/cp5-routing-drc/iter13/battery_crop_04_hard_cut_MOSFETs.png

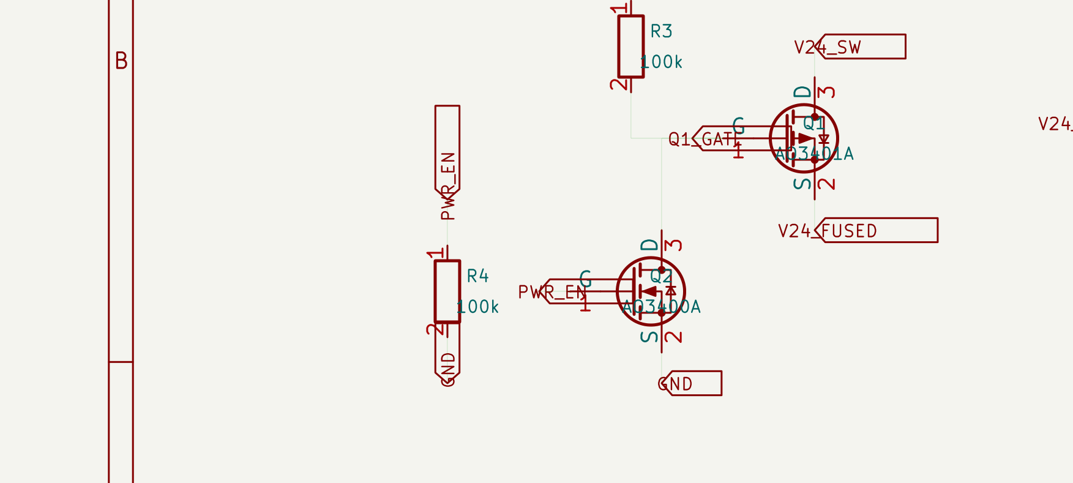
hardware/reviews/visual_inspections/cp5-routing-drc/iter13/battery_crop_04_hard_cut_MOSFETs.png
