kaanow/volthium_reader/hardware/reviews/visual_inspections/cp5-routing-drc/iter13/battery_crop_06_MOD1_left_pins.png

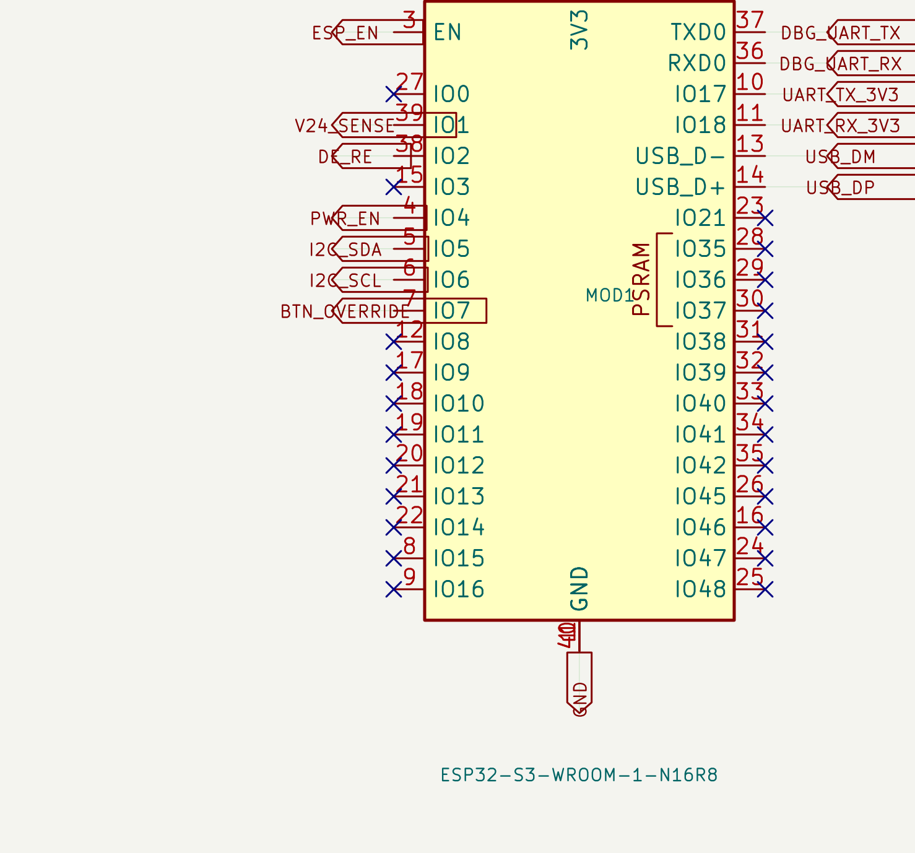
hardware/reviews/visual_inspections/cp5-routing-drc/iter13/battery_crop_06_MOD1_left_pins.png
