kaanow/volthium_reader/hardware/reviews/visual_inspections/cp5-routing-drc/iter13/battery_crop_08_MOD1_support_caps.png

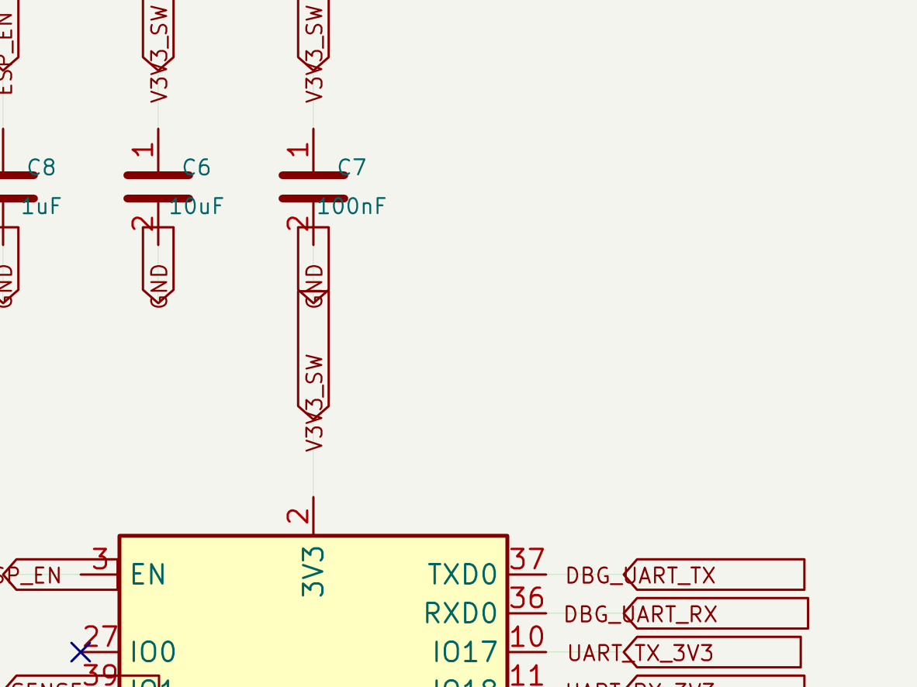
hardware/reviews/visual_inspections/cp5-routing-drc/iter13/battery_crop_08_MOD1_support_caps.png
