kaanow/volthium_reader/hardware/reviews/visual_inspections/cp5-routing-drc/iter13/display_crop_03_RS485_U2_cluster.png

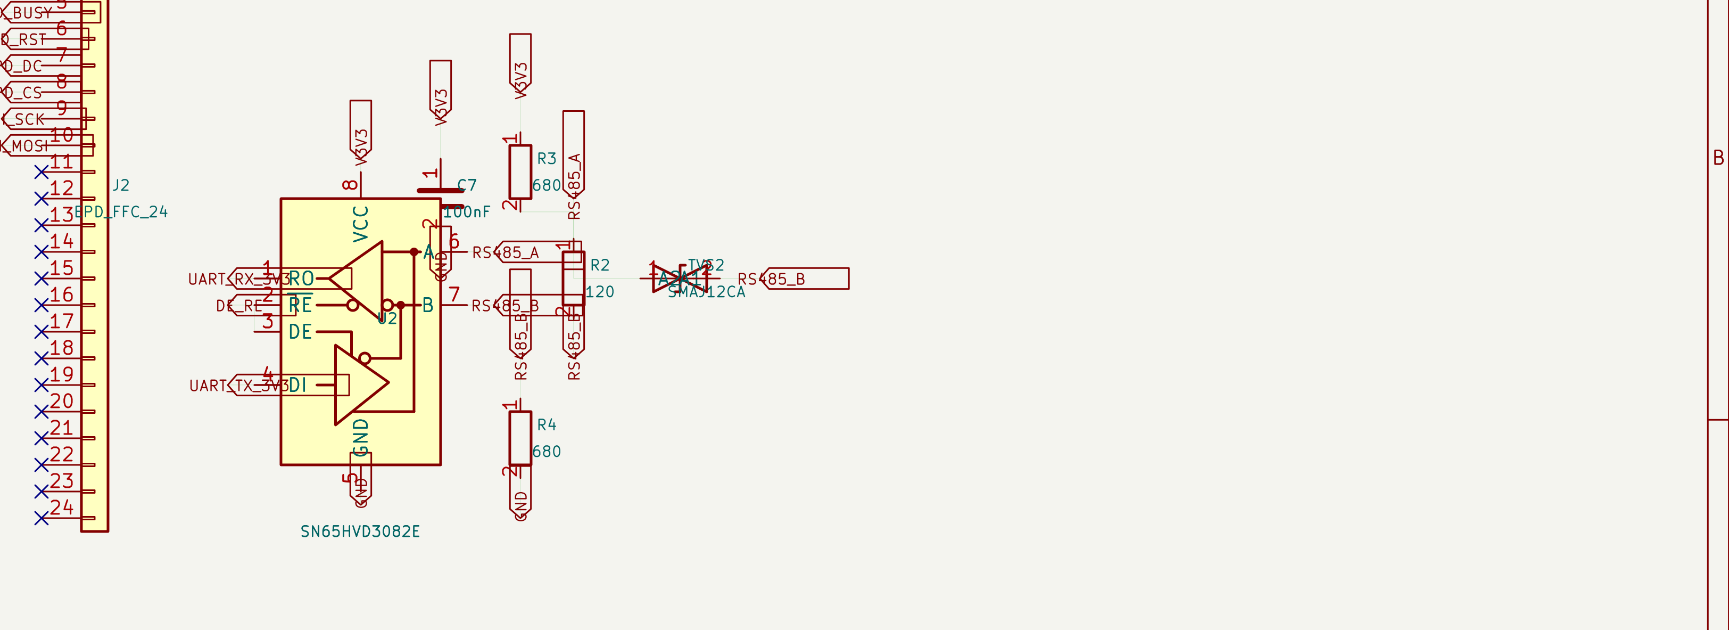
hardware/reviews/visual_inspections/cp5-routing-drc/iter13/display_crop_03_RS485_U2_cluster.png
