kaanow/volthium_reader/hardware/reviews/visual_inspections/cp5-routing-drc/iter13/display_crop_05_MOD1_right_pins.png

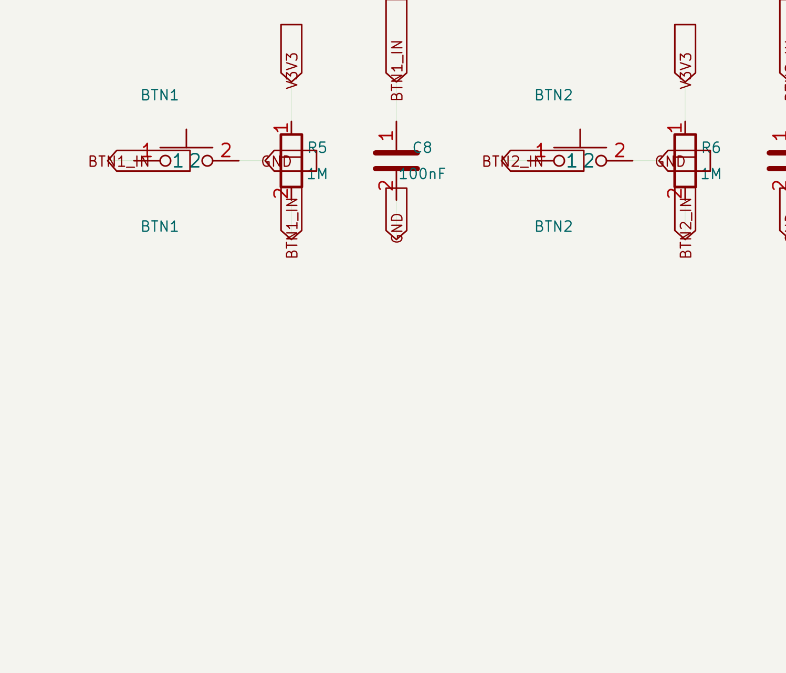
hardware/reviews/visual_inspections/cp5-routing-drc/iter13/display_crop_05_MOD1_right_pins.png
