kaanow/volthium_reader/hardware/reviews/visual_inspections/cp6-fab-ready/iter6/display_full_300dpi.png

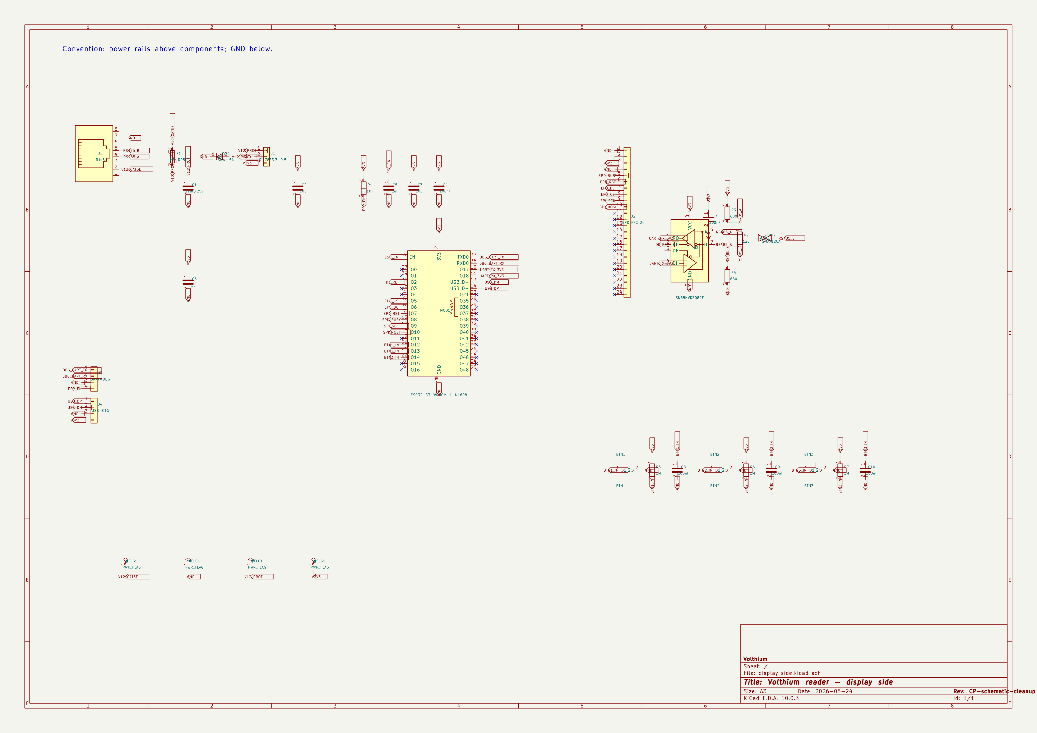
hardware/reviews/visual_inspections/cp6-fab-ready/iter6/display_full_300dpi.png
