kaanow/volthium_reader/hardware/reviews/visual_inspections/cp6-fab-ready/iter6/display_zoom_BTN_R6_C9.png

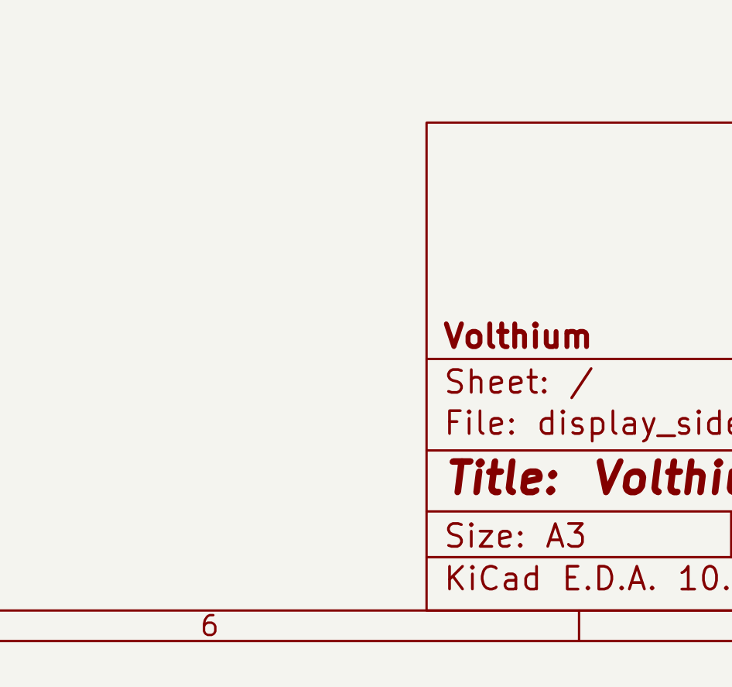
hardware/reviews/visual_inspections/cp6-fab-ready/iter6/display_zoom_BTN_R6_C9.png
