kaanow/volthium_reader/hardware/reviews/visual_inspections/cp6-fab-ready/iter7/dsp_U2_RS485_after.png

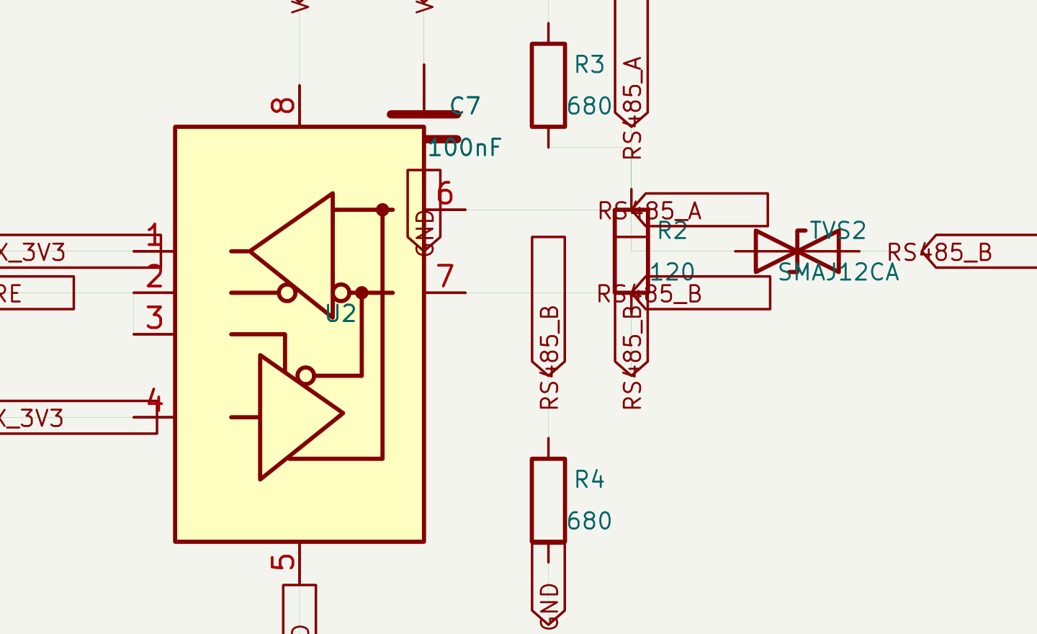
hardware/reviews/visual_inspections/cp6-fab-ready/iter7/dsp_U2_RS485_after.png
