kaanow/volthium_reader/hardware/reviews/visual_inspections/cp_schematic_cleanup/iter37/battery_side/02_power_input_row_J1_F1_D1_TVS1.png

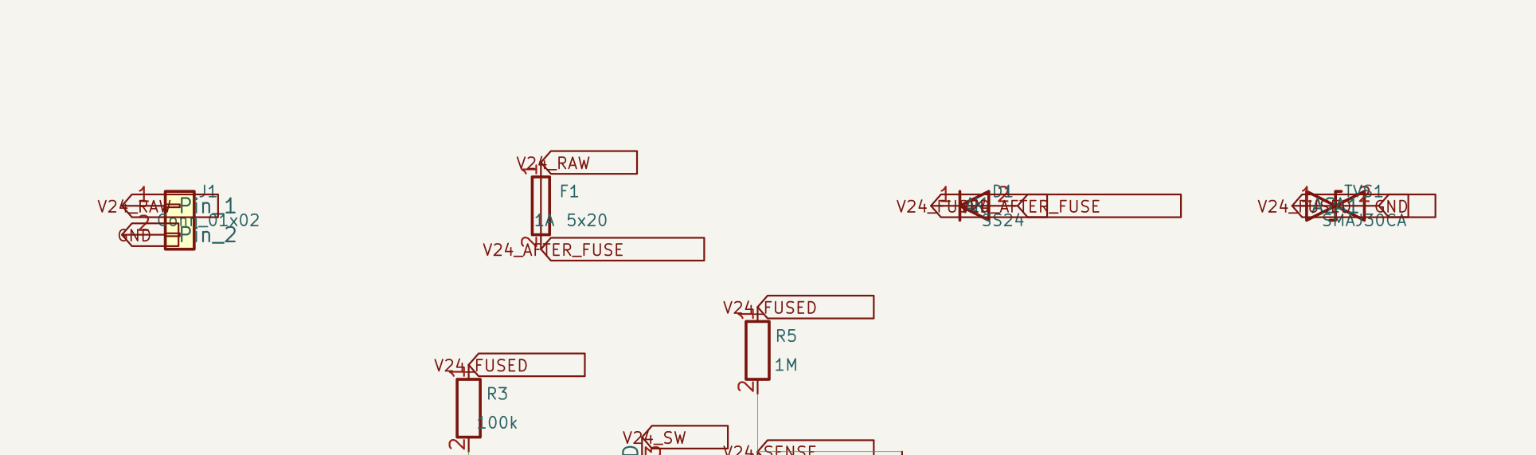
hardware/reviews/visual_inspections/cp_schematic_cleanup/iter37/battery_side/02_power_input_row_J1_F1_D1_TVS1.png
