kaanow/volthium_reader/hardware/reviews/visual_inspections/cp_schematic_cleanup/iter37/battery_side/03_sense_divider_R5_R6_C5.png

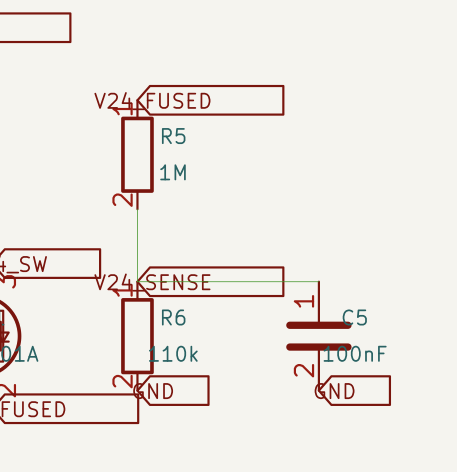
hardware/reviews/visual_inspections/cp_schematic_cleanup/iter37/battery_side/03_sense_divider_R5_R6_C5.png
