kaanow/volthium_reader/hardware/reviews/visual_inspections/cp_schematic_cleanup/iter37/battery_side/08_esp32_decoupling_row.png

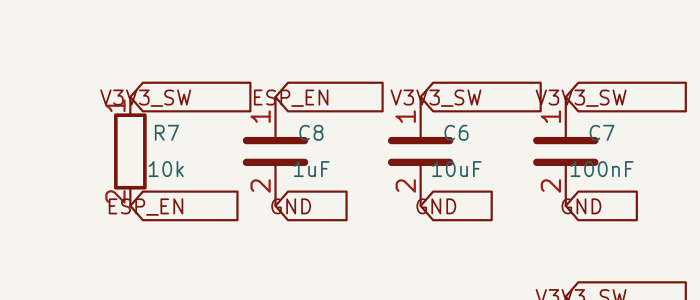
hardware/reviews/visual_inspections/cp_schematic_cleanup/iter37/battery_side/08_esp32_decoupling_row.png
