kaanow/volthium_reader/hardware/reviews/visual_inspections/cp_schematic_cleanup/iter37/display_side/09_left_edge_conns_J3_J4.png

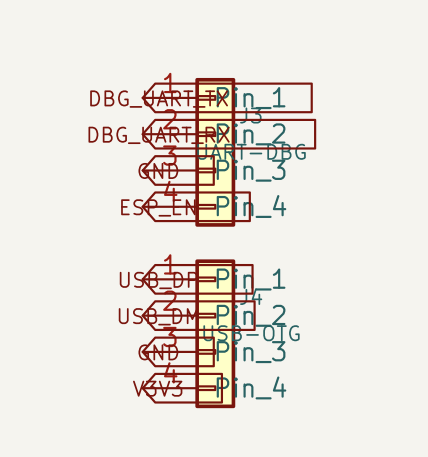
hardware/reviews/visual_inspections/cp_schematic_cleanup/iter37/display_side/09_left_edge_conns_J3_J4.png
