kaanow/volthium_reader/hardware/reviews/visual_inspections/cp_schematic_cleanup/iter40/battery_side/13_right_edge_conns_J3_J5.png

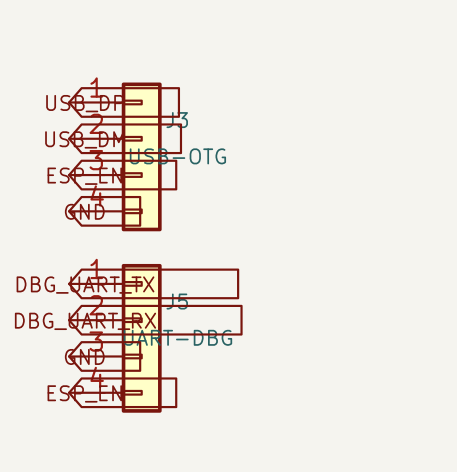
hardware/reviews/visual_inspections/cp_schematic_cleanup/iter40/battery_side/13_right_edge_conns_J3_J5.png
