kaanow/volthium_reader/hardware/reviews/visual_inspections/cp_schematic_cleanup/iter49/battery_side/10_rtc_coin_cell.png

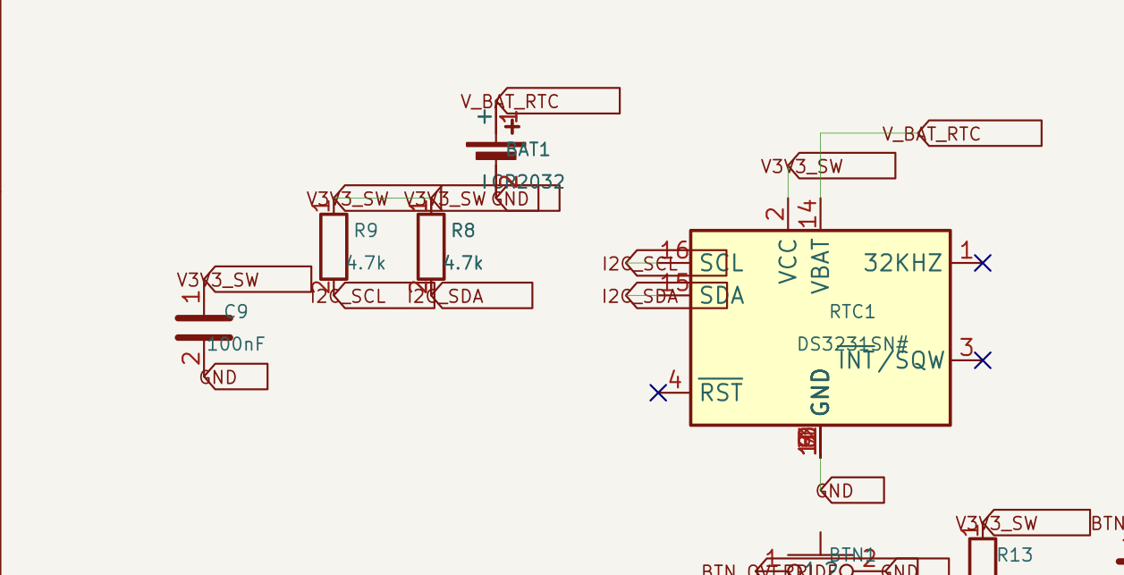
hardware/reviews/visual_inspections/cp_schematic_cleanup/iter49/battery_side/10_rtc_coin_cell.png
