kaanow/volthium_reader/hardware/reviews/visual_inspections/cp_schematic_cleanup/iter51/display_side/08_u2_rs485_transceiver.png

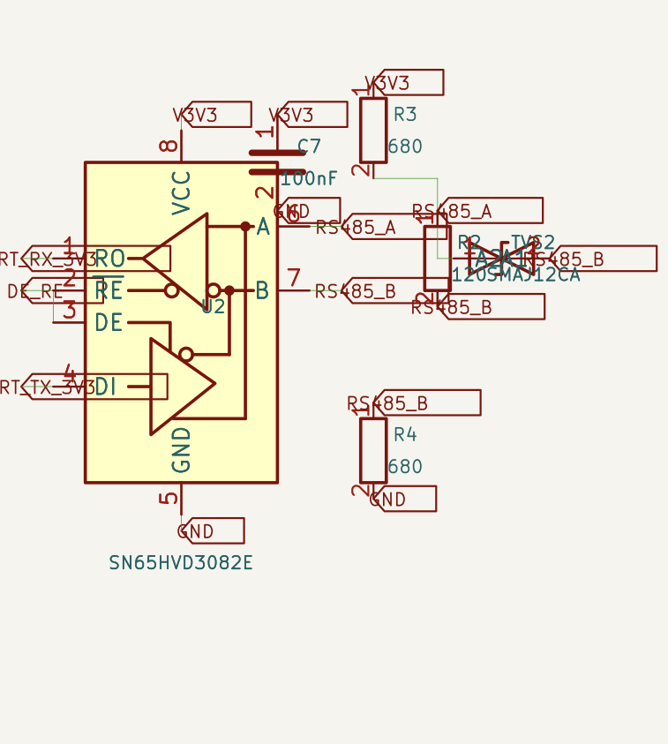
hardware/reviews/visual_inspections/cp_schematic_cleanup/iter51/display_side/08_u2_rs485_transceiver.png
