kaanow/volthium_reader/hardware/reviews/visual_inspections/cp_schematic_cleanup/iter53/battery_side/04_q1q2_hardcut.png

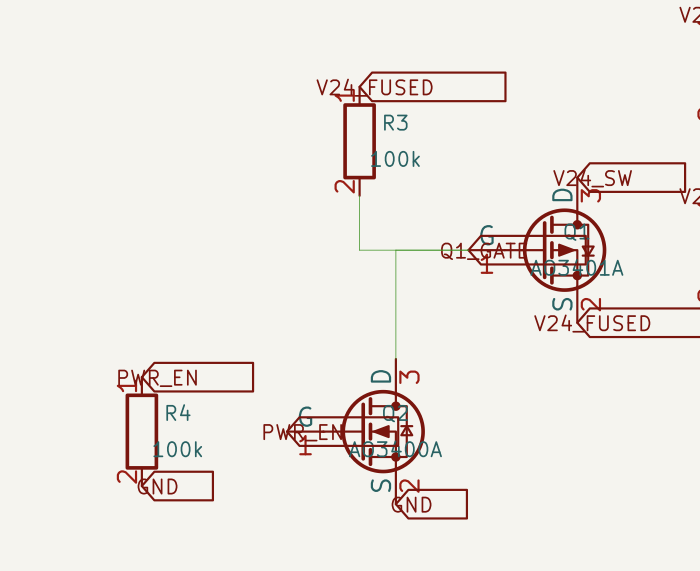
hardware/reviews/visual_inspections/cp_schematic_cleanup/iter53/battery_side/04_q1q2_hardcut.png
