kaanow/volthium_reader/hardware/reviews/visual_inspections/cp_schematic_cleanup/iter53/battery_side/05_u1_buck_U1_L1_C1_C2_CBST.png

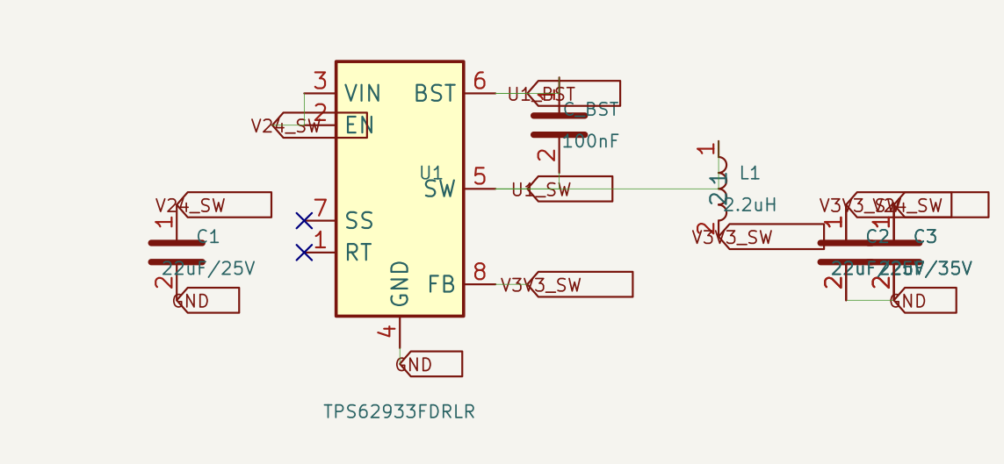
hardware/reviews/visual_inspections/cp_schematic_cleanup/iter53/battery_side/05_u1_buck_U1_L1_C1_C2_CBST.png
