kaanow/volthium_reader/hardware/reviews/visual_inspections/cp_schematic_cleanup/iter53/display_side/06_c6_isolated.png

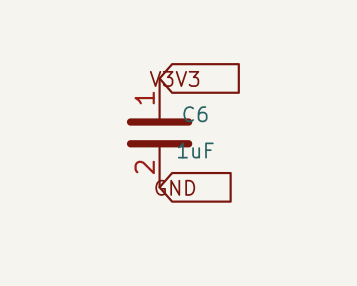
hardware/reviews/visual_inspections/cp_schematic_cleanup/iter53/display_side/06_c6_isolated.png
