kaanow/volthium_reader/hardware/reviews/visual_inspections/cp_schematic_cleanup/iter57/battery_side/06_u2_r78e12_reg.png

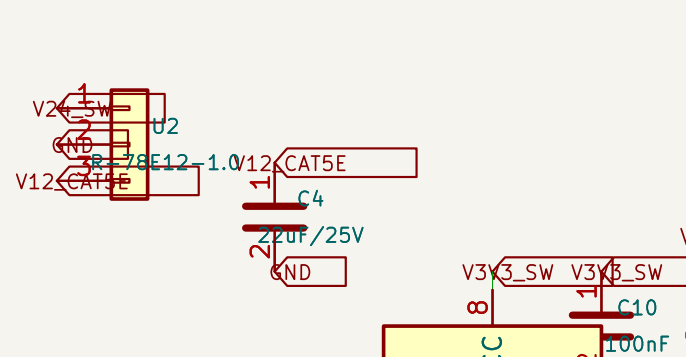
hardware/reviews/visual_inspections/cp_schematic_cleanup/iter57/battery_side/06_u2_r78e12_reg.png
