kaanow/volthium_reader/hardware/reviews/visual_inspections/cp_schematic_cleanup/iter57/battery_side/07_u3_rs485_transceiver.png

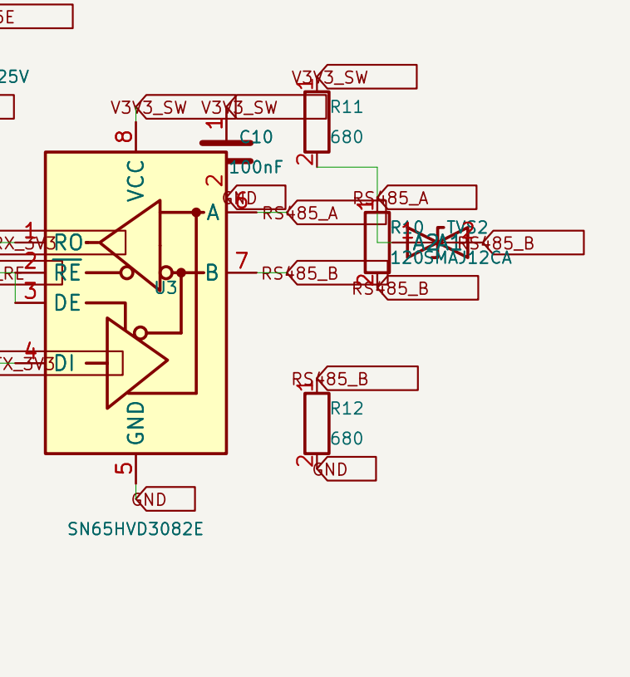
hardware/reviews/visual_inspections/cp_schematic_cleanup/iter57/battery_side/07_u3_rs485_transceiver.png
