kaanow/volthium_reader/hardware/reviews/visual_inspections/cp_schematic_cleanup/iter57/battery_side/09_esp32_mod1.png

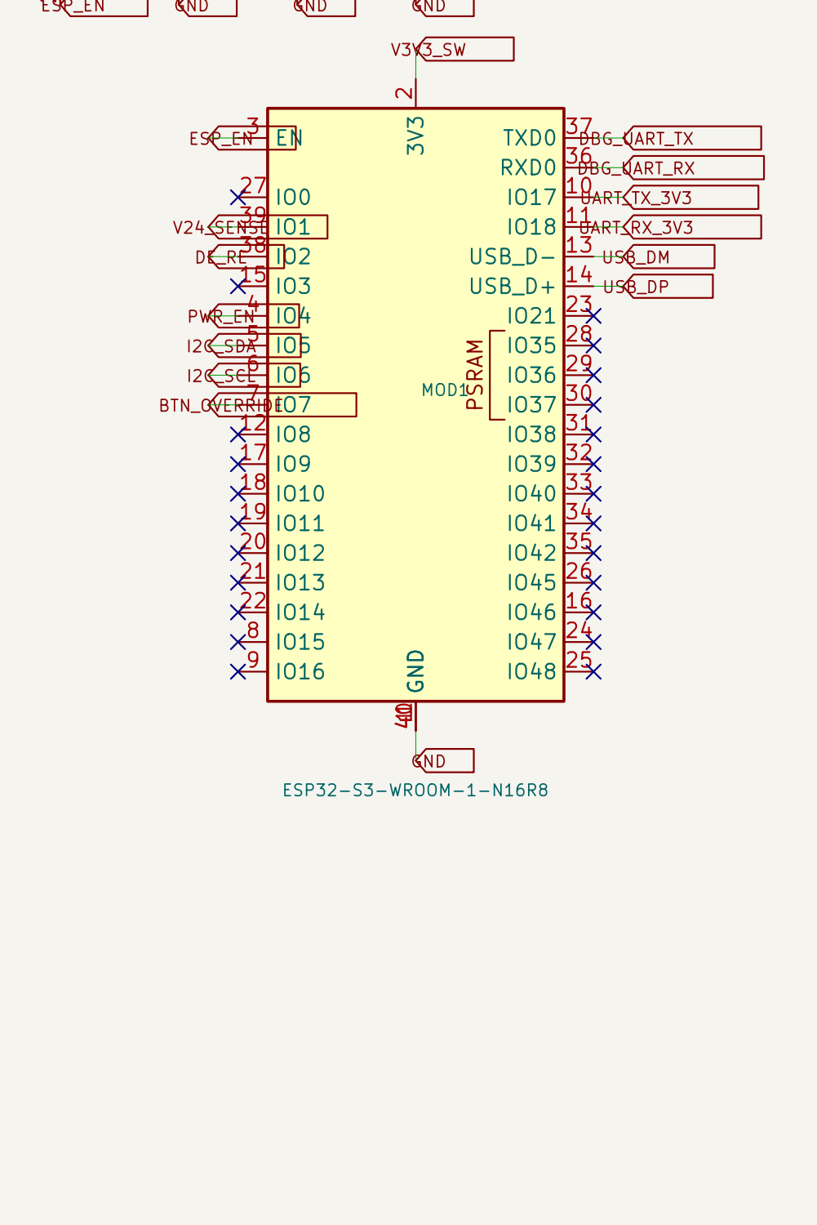
hardware/reviews/visual_inspections/cp_schematic_cleanup/iter57/battery_side/09_esp32_mod1.png
