kaanow/volthium_reader/hardware/reviews/visual_inspections/cp_schematic_cleanup/iter57/display_side/02_rj45_input_J1_F1_TVS1.png

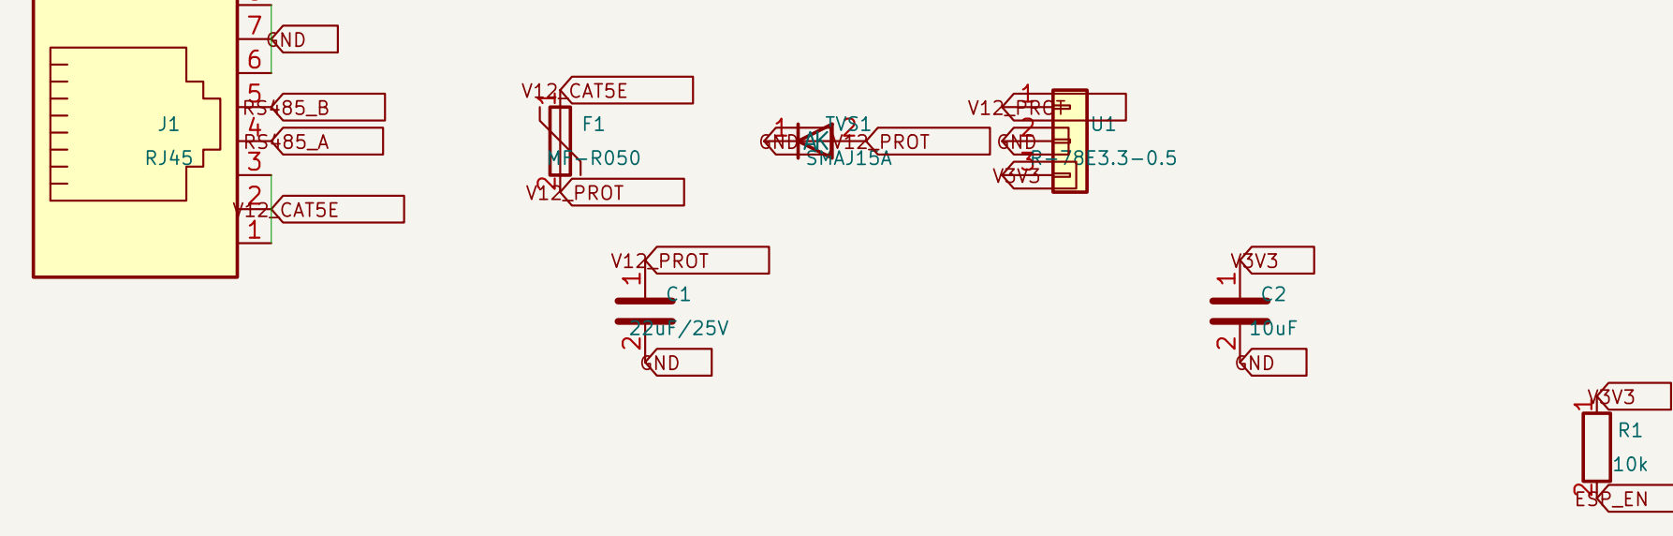
hardware/reviews/visual_inspections/cp_schematic_cleanup/iter57/display_side/02_rj45_input_J1_F1_TVS1.png
