kaanow/volthium_reader/hardware/reviews/visual_inspections/cp_schematic_cleanup/iter57/display_side/03_u1_r78_3v3_reg.png

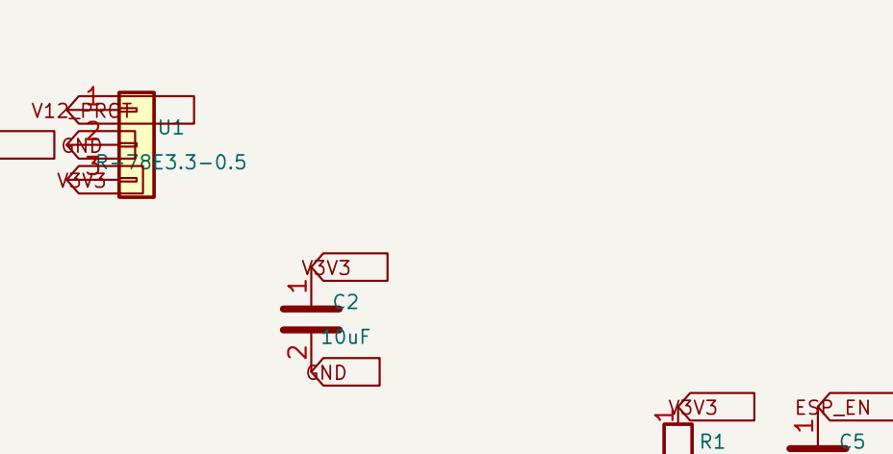
hardware/reviews/visual_inspections/cp_schematic_cleanup/iter57/display_side/03_u1_r78_3v3_reg.png
