kaanow/volthium_reader/hardware/reviews/visual_inspections/cp_schematic_cleanup/iter57/display_side/10_lower_middle_button_zone.png

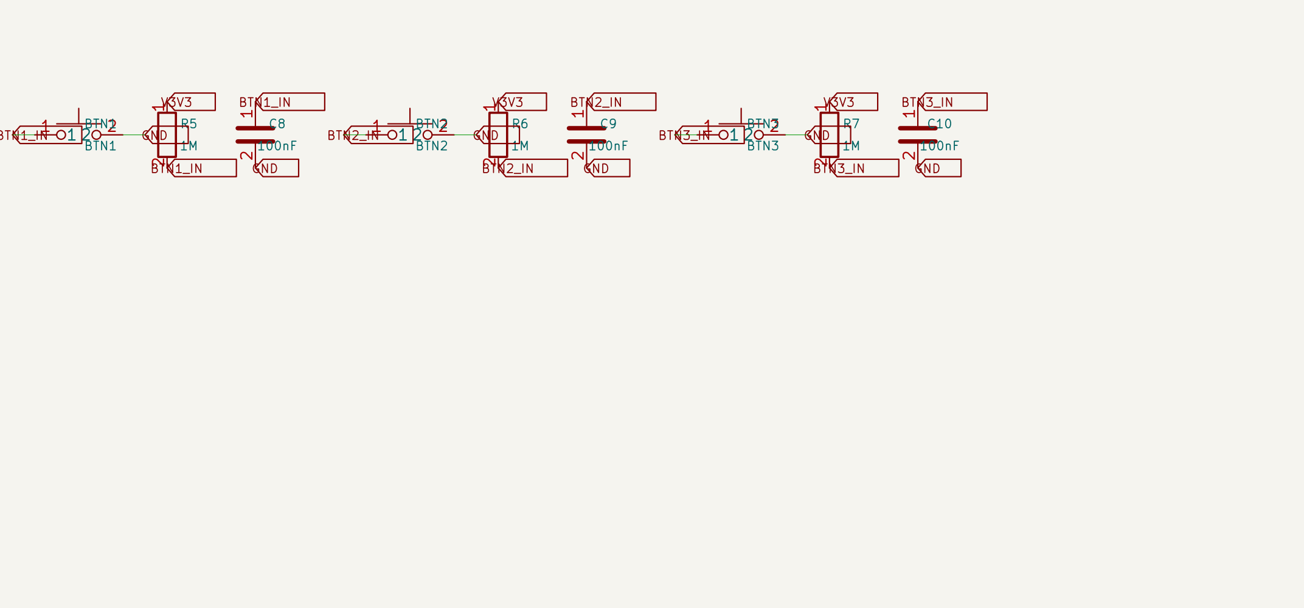
hardware/reviews/visual_inspections/cp_schematic_cleanup/iter57/display_side/10_lower_middle_button_zone.png
