kaanow/volthium_reader/hardware/reviews/visual_inspections/cp2-schematic/display-iter4/reviewer/rebuild_battery.txt

[env] KiCad share: C:\Users\kaanw\AppData\Local/Programs/KiCad/10.0/share/kicad
[env] KiCad CLI: C:\Users\kaanw\AppData\Local\Programs\KiCad\10.0\bin\kicad-cli.exe
[selftest] probing export contract (the next [pdf-export] FAILED line is the INTENTIONAL probe, not a build error):
[pdf-export] FAILED for no_such_schematic.kicad_sch: rc=3, exists=False — stale/absent PDF must not be judged
[selftest] gate self-tests: pdf-text fixtures 2+2, export contract rejects stale — clean
[sheet_power] readability gate: clean
[sheet_power] pdf-text gate: clean
[sheet_power] PNG written
[sheet_periph] readability gate: clean
[sheet_periph] pdf-text gate: clean
[sheet_periph] PNG written
[sheet_super] readability gate: clean
[sheet_super] pdf-text gate: clean
[sheet_super] PNG written
[sheet_usb] readability gate: clean
[sheet_usb] pdf-text gate: clean
[sheet_usb] PNG written
[sheet_isors485_1] readability gate: clean
[sheet_isors485_1] pdf-text gate: clean
[sheet_isors485_1] PNG written
[sheet_isors485_2] readability gate: clean
[sheet_isors485_2] pdf-text gate: clean
[sheet_isors485_2] PNG written
[sheet_mcu] readability gate: clean
[sheet_mcu] pdf-text gate: clean
[sheet_mcu] PNG written
[sheet_conn] readability gate: clean
[sheet_conn] pdf-text gate: clean
[sheet_conn] PNG written
[NETLIST gate] generator intent == kicad-cli netlist: clean
[ROOT ERC strict] rc=5; 2 message(s), 2 accepted (ERC_ACCEPTED), 0 unaccounted
[ROOT] wrote volthium_reader.kicad_sch + .kicad_pro + full volthium_reader.pdf
