kaanow/volthium_reader/hardware/kicad/schematic/build_display/sheet_d_mcu.pdf

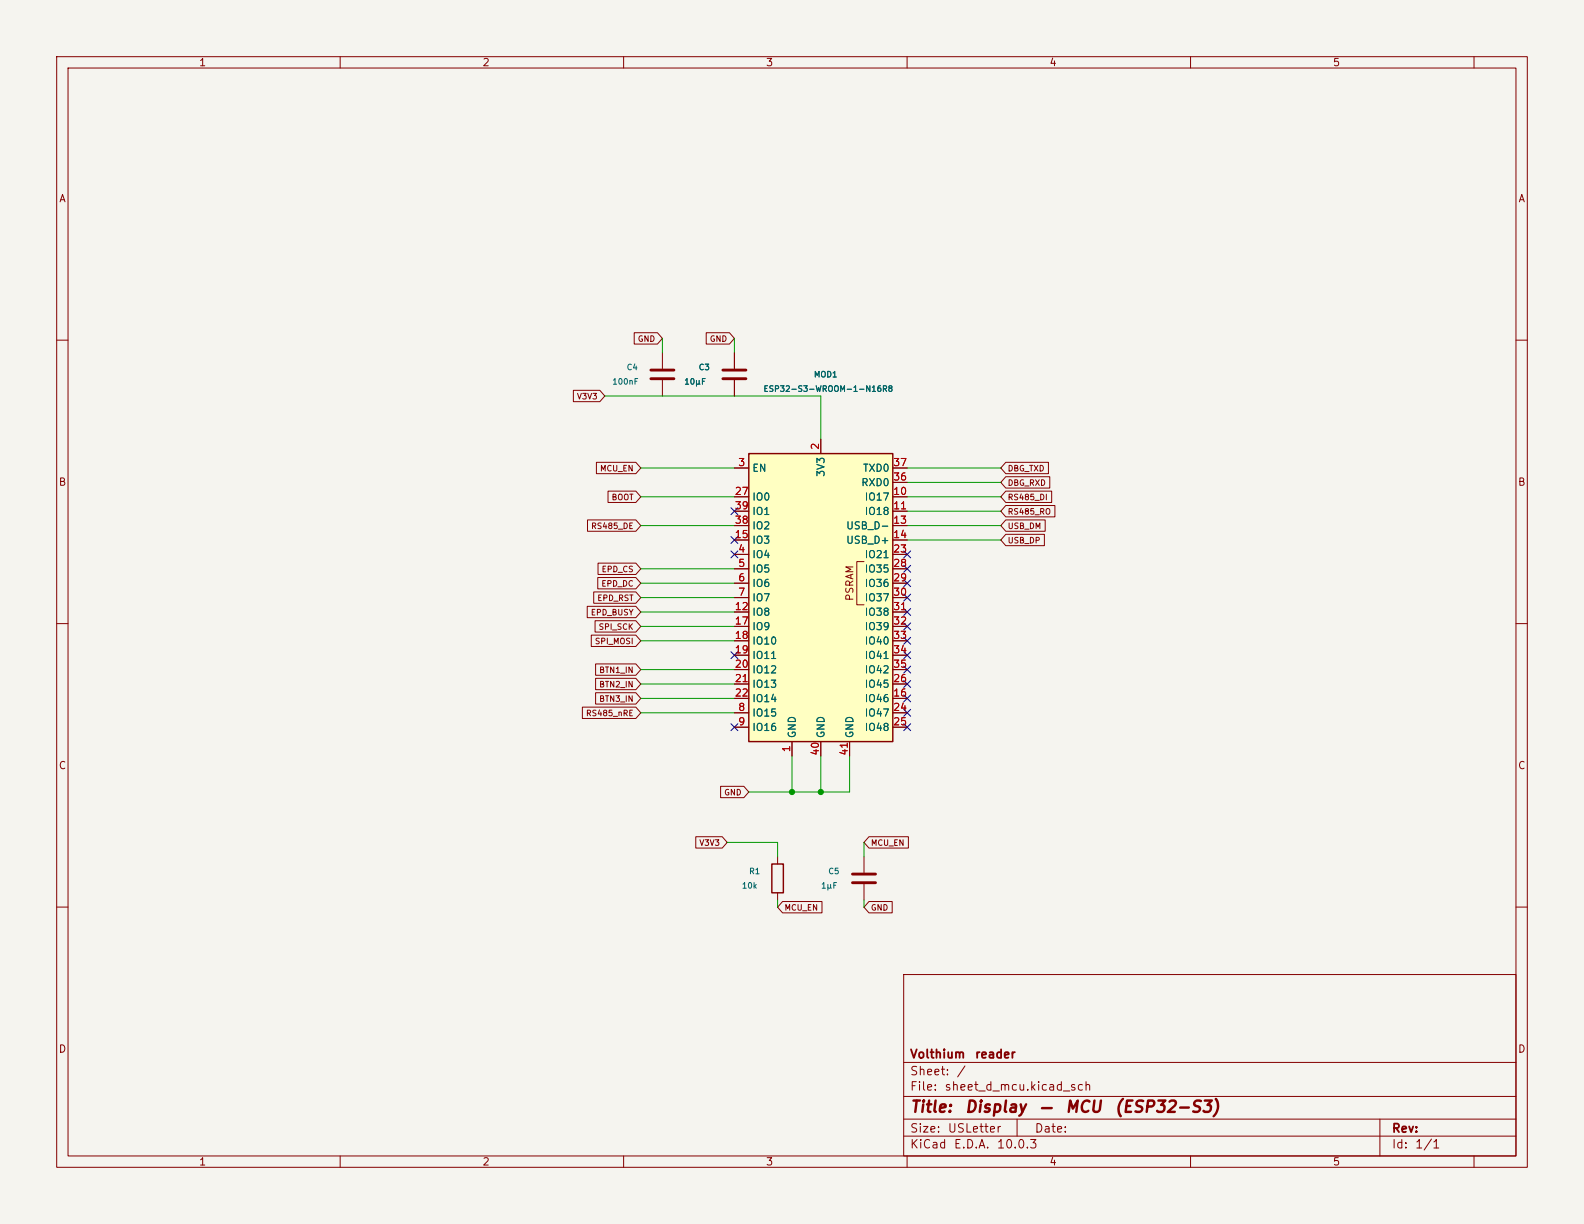
[picture p225: page 1]

Size: USLetter | Rev:
KiCad E.D.A. 10.0.3 | Id: 1/1
