kaanow/volthium_reader/hardware/kicad/schematic/build_display/sheet_d_periph.pdf

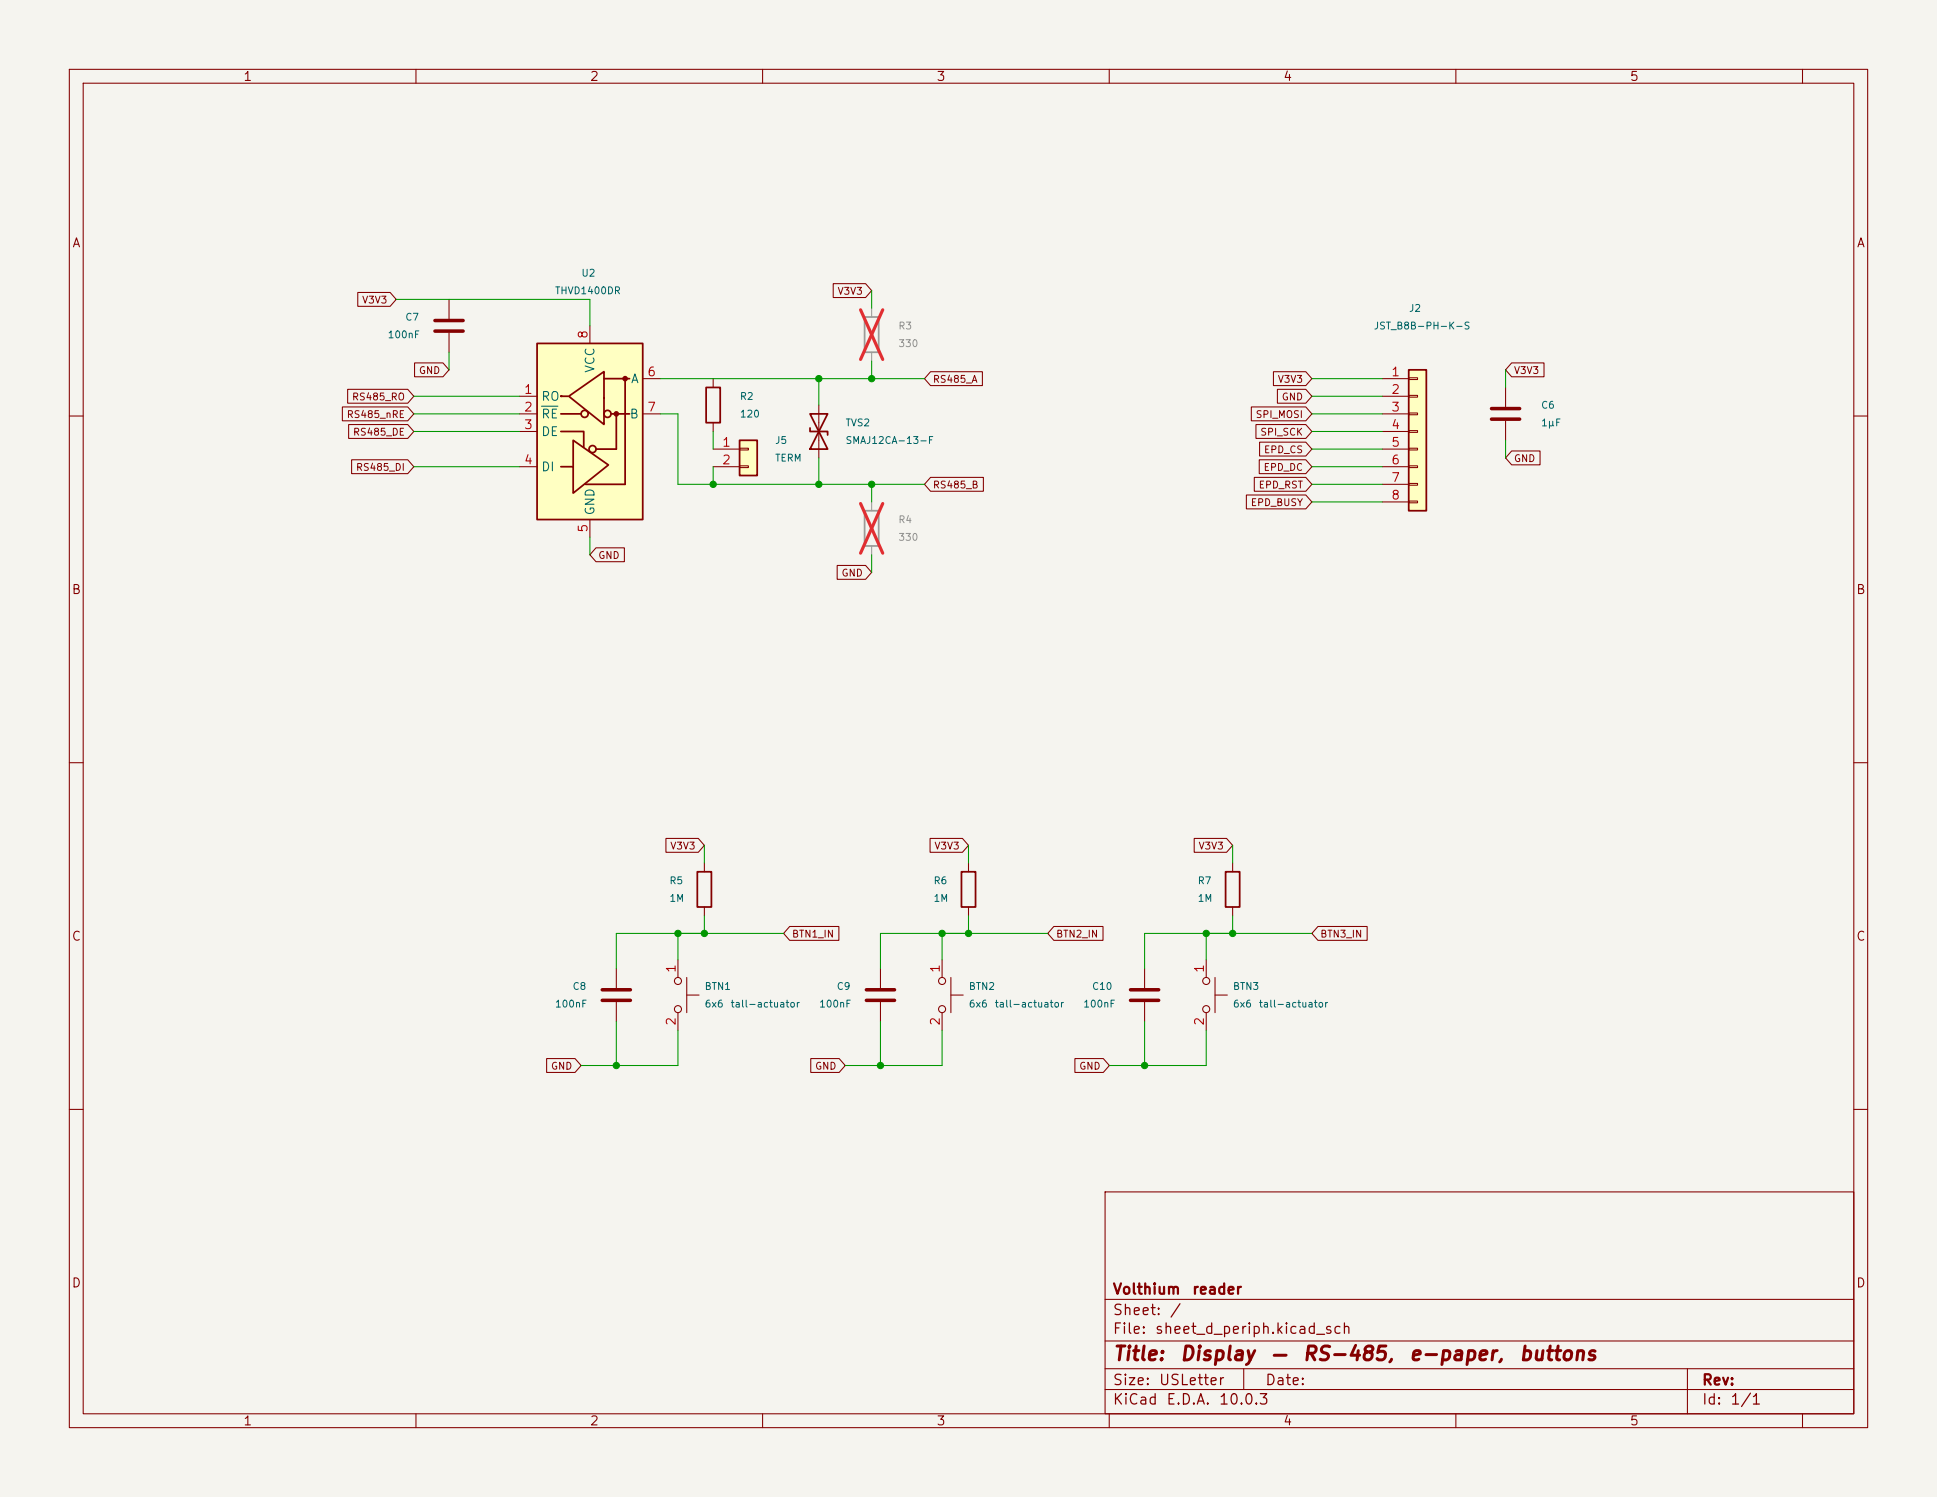
[picture p226: page 1]

Volthium reader
Sheet: /
File: sheet_d_periph.kicad_sch
Title: Display — RS-485, e-paper, buttons

Size: USLetter | Rev:
KiCad E.D.A. 10.0.3 | Id: 1/1
