kaanow/volthium_reader/hardware/kicad/schematic/build_display/sheet_d_power.pdf

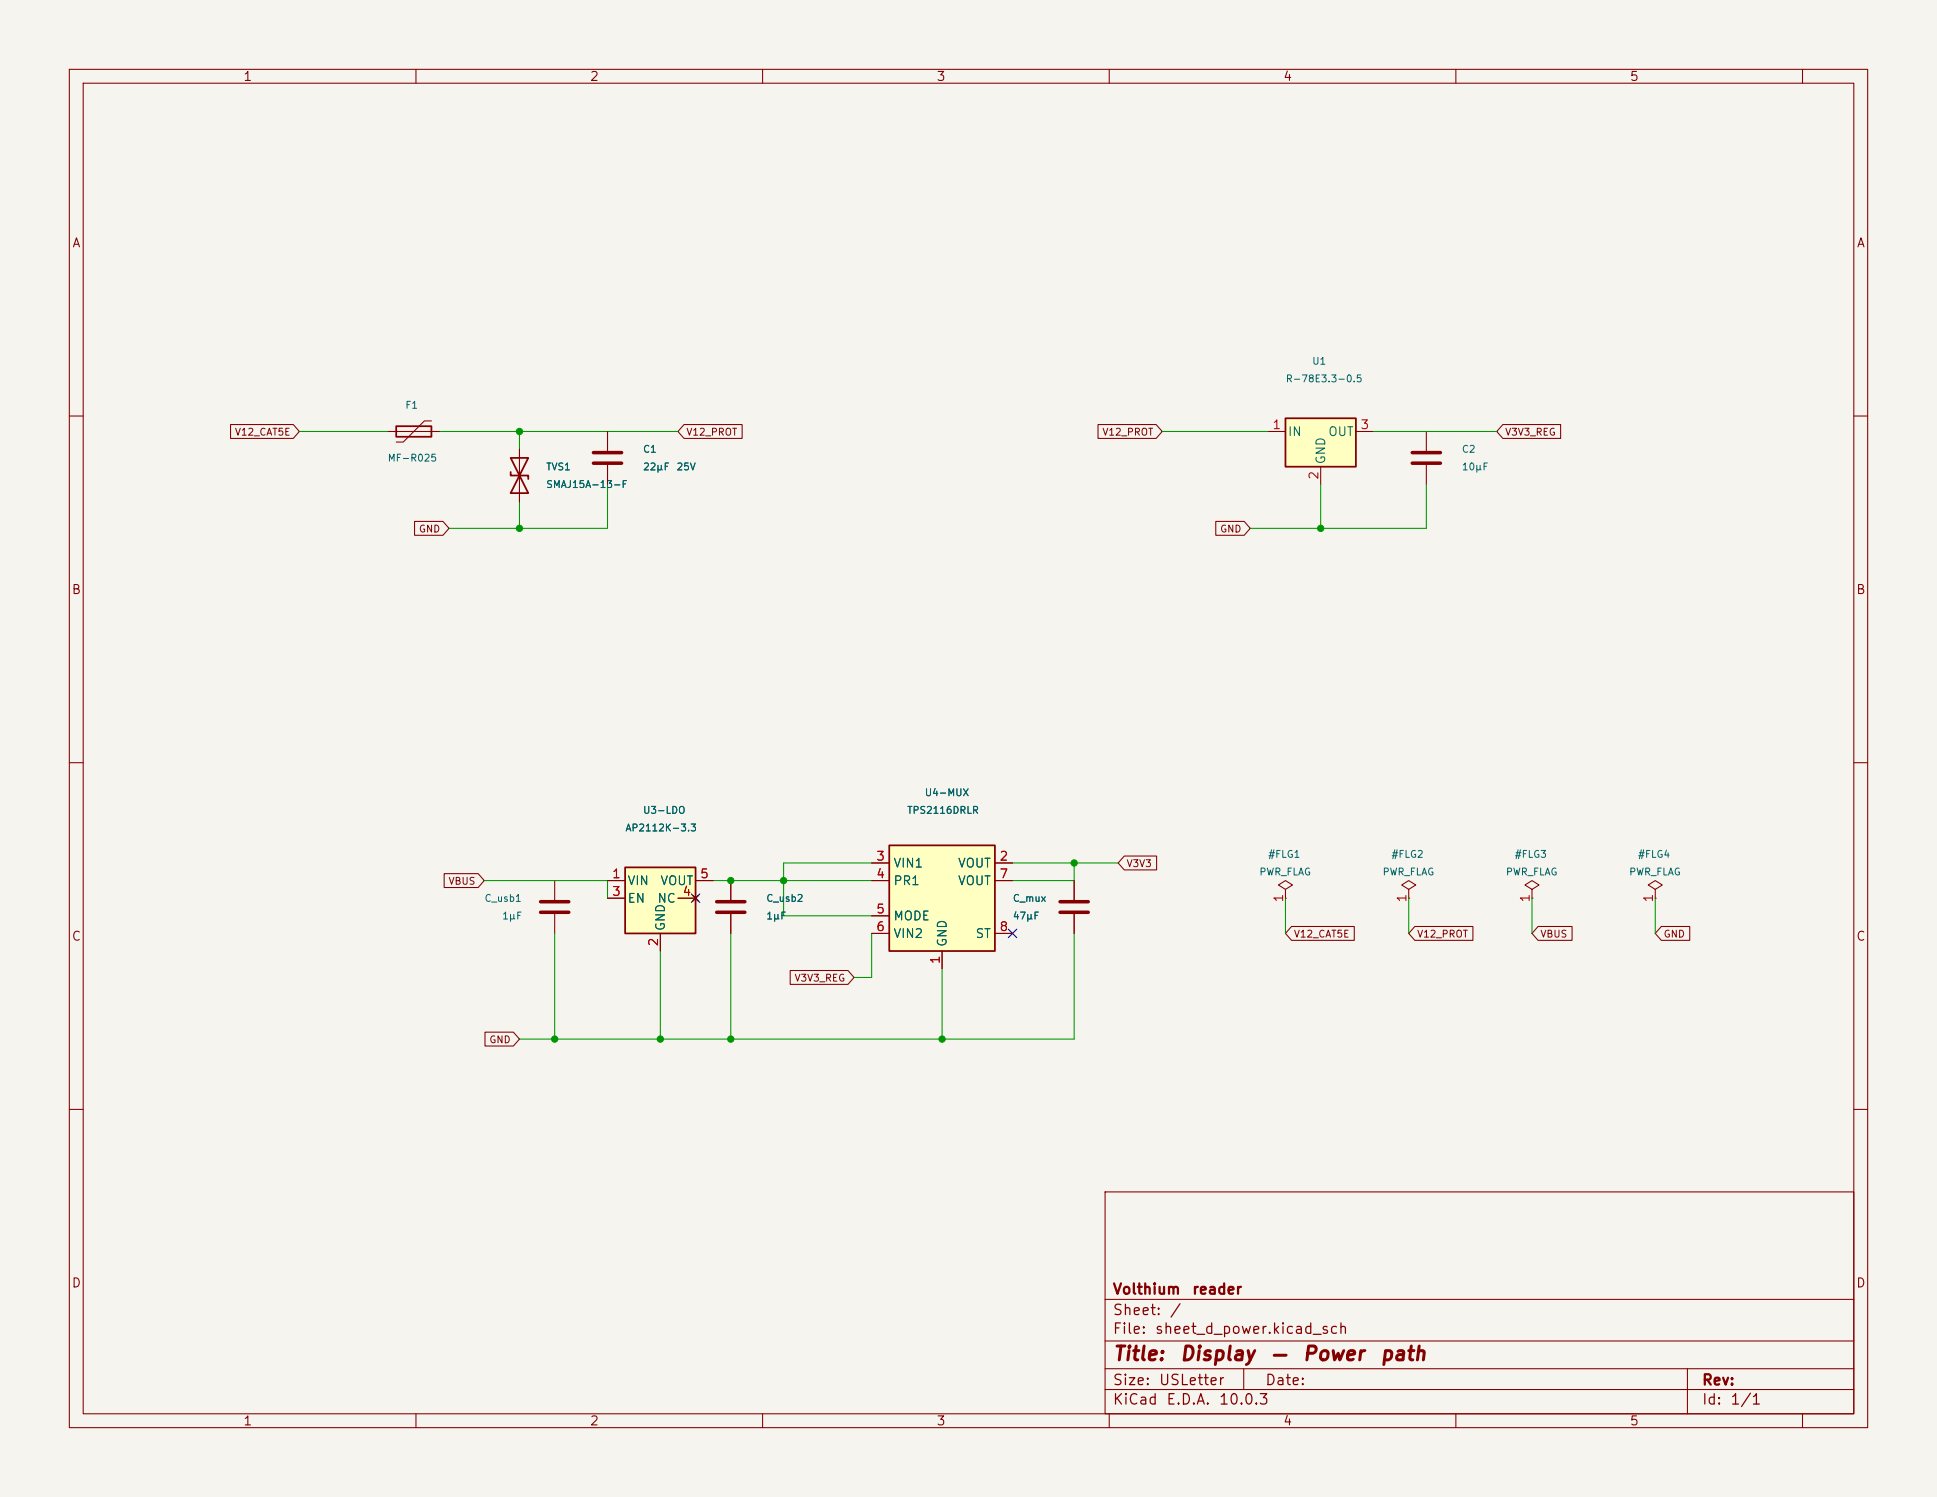
[picture p227: page 1]

Sheet: /
File: sheet_d_power.kicad_sch
Title: Display — Power path

Size: USLetter | Rev:
KiCad E.D.A. 10.0.3 | Id: 1/1
