kaanow/volthium_reader/hardware/kicad/schematic/build_display/volthium_display.pdf

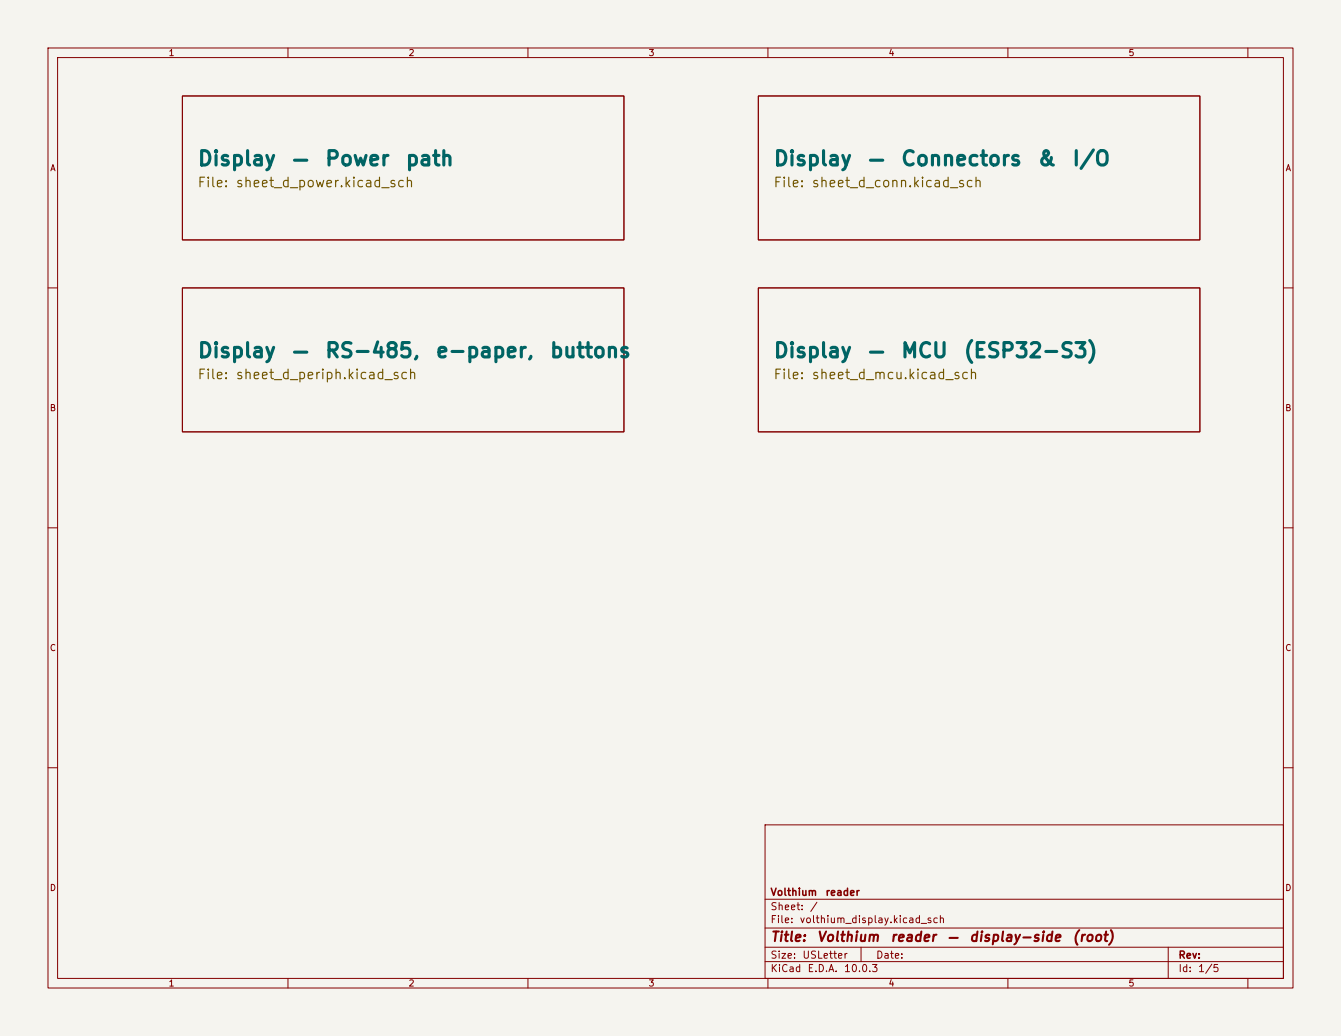
[picture p228: page 1]

Display — RS-485, e-paper, buttons

Volthium reader
Sheet: /
File: volthium_display.kicad_sch
Title: Volthium reader — display-side (root)

Size: USLetter | Rev:
KiCad E.D.A. 10.0.3 | Id: 1/5

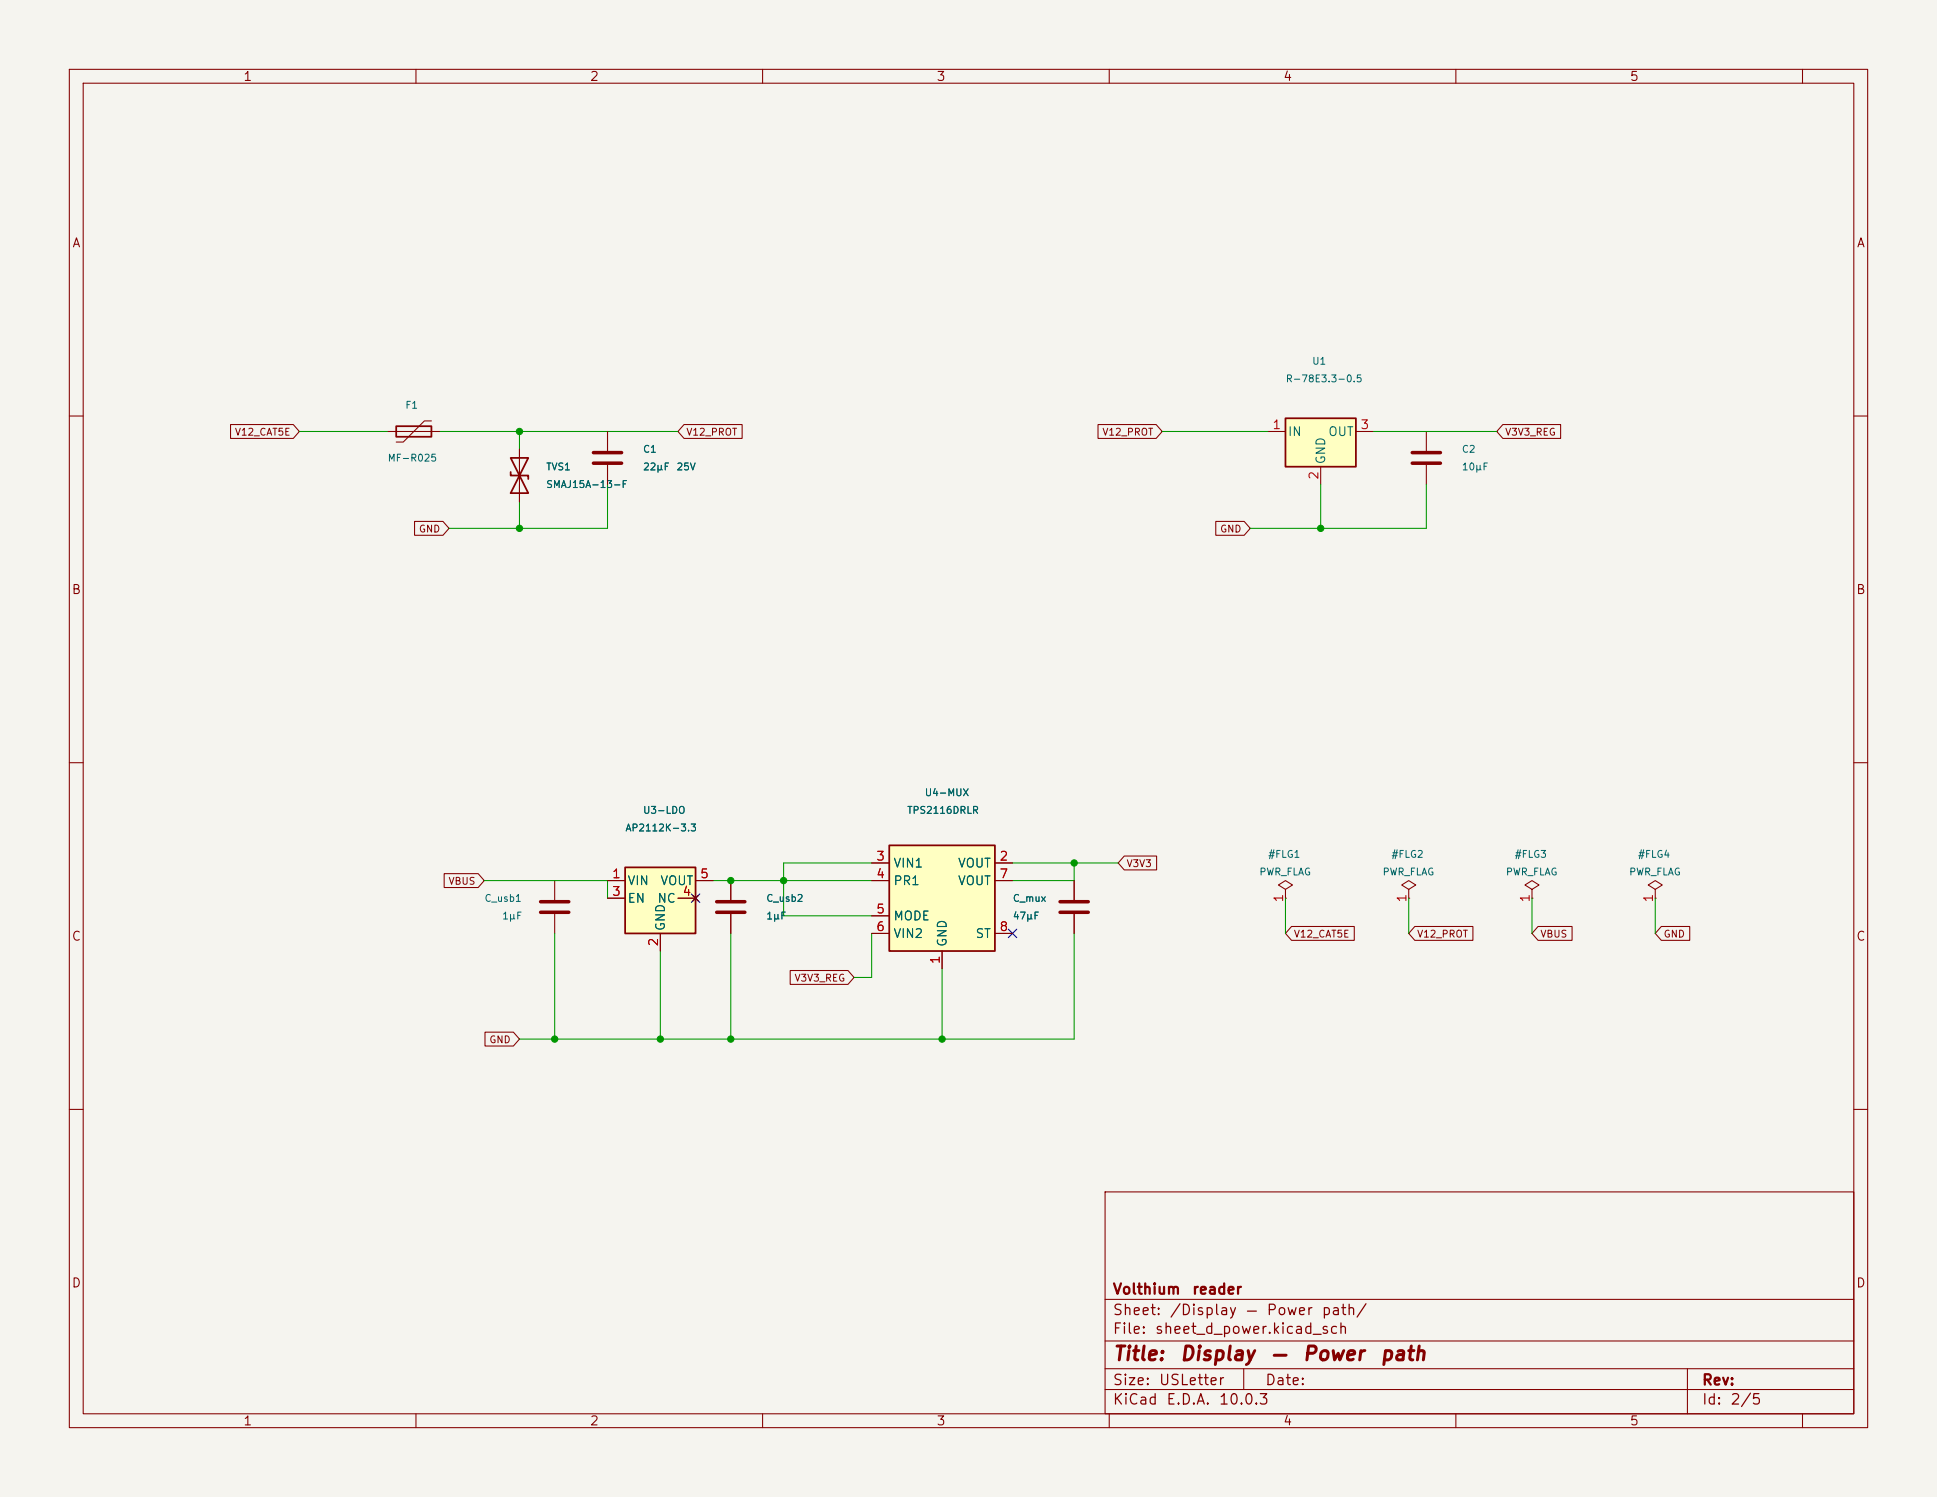
[picture p229: page 2]

Sheet: /Display — Power path/
File: sheet_d_power.kicad_sch
Title: Display — Power path

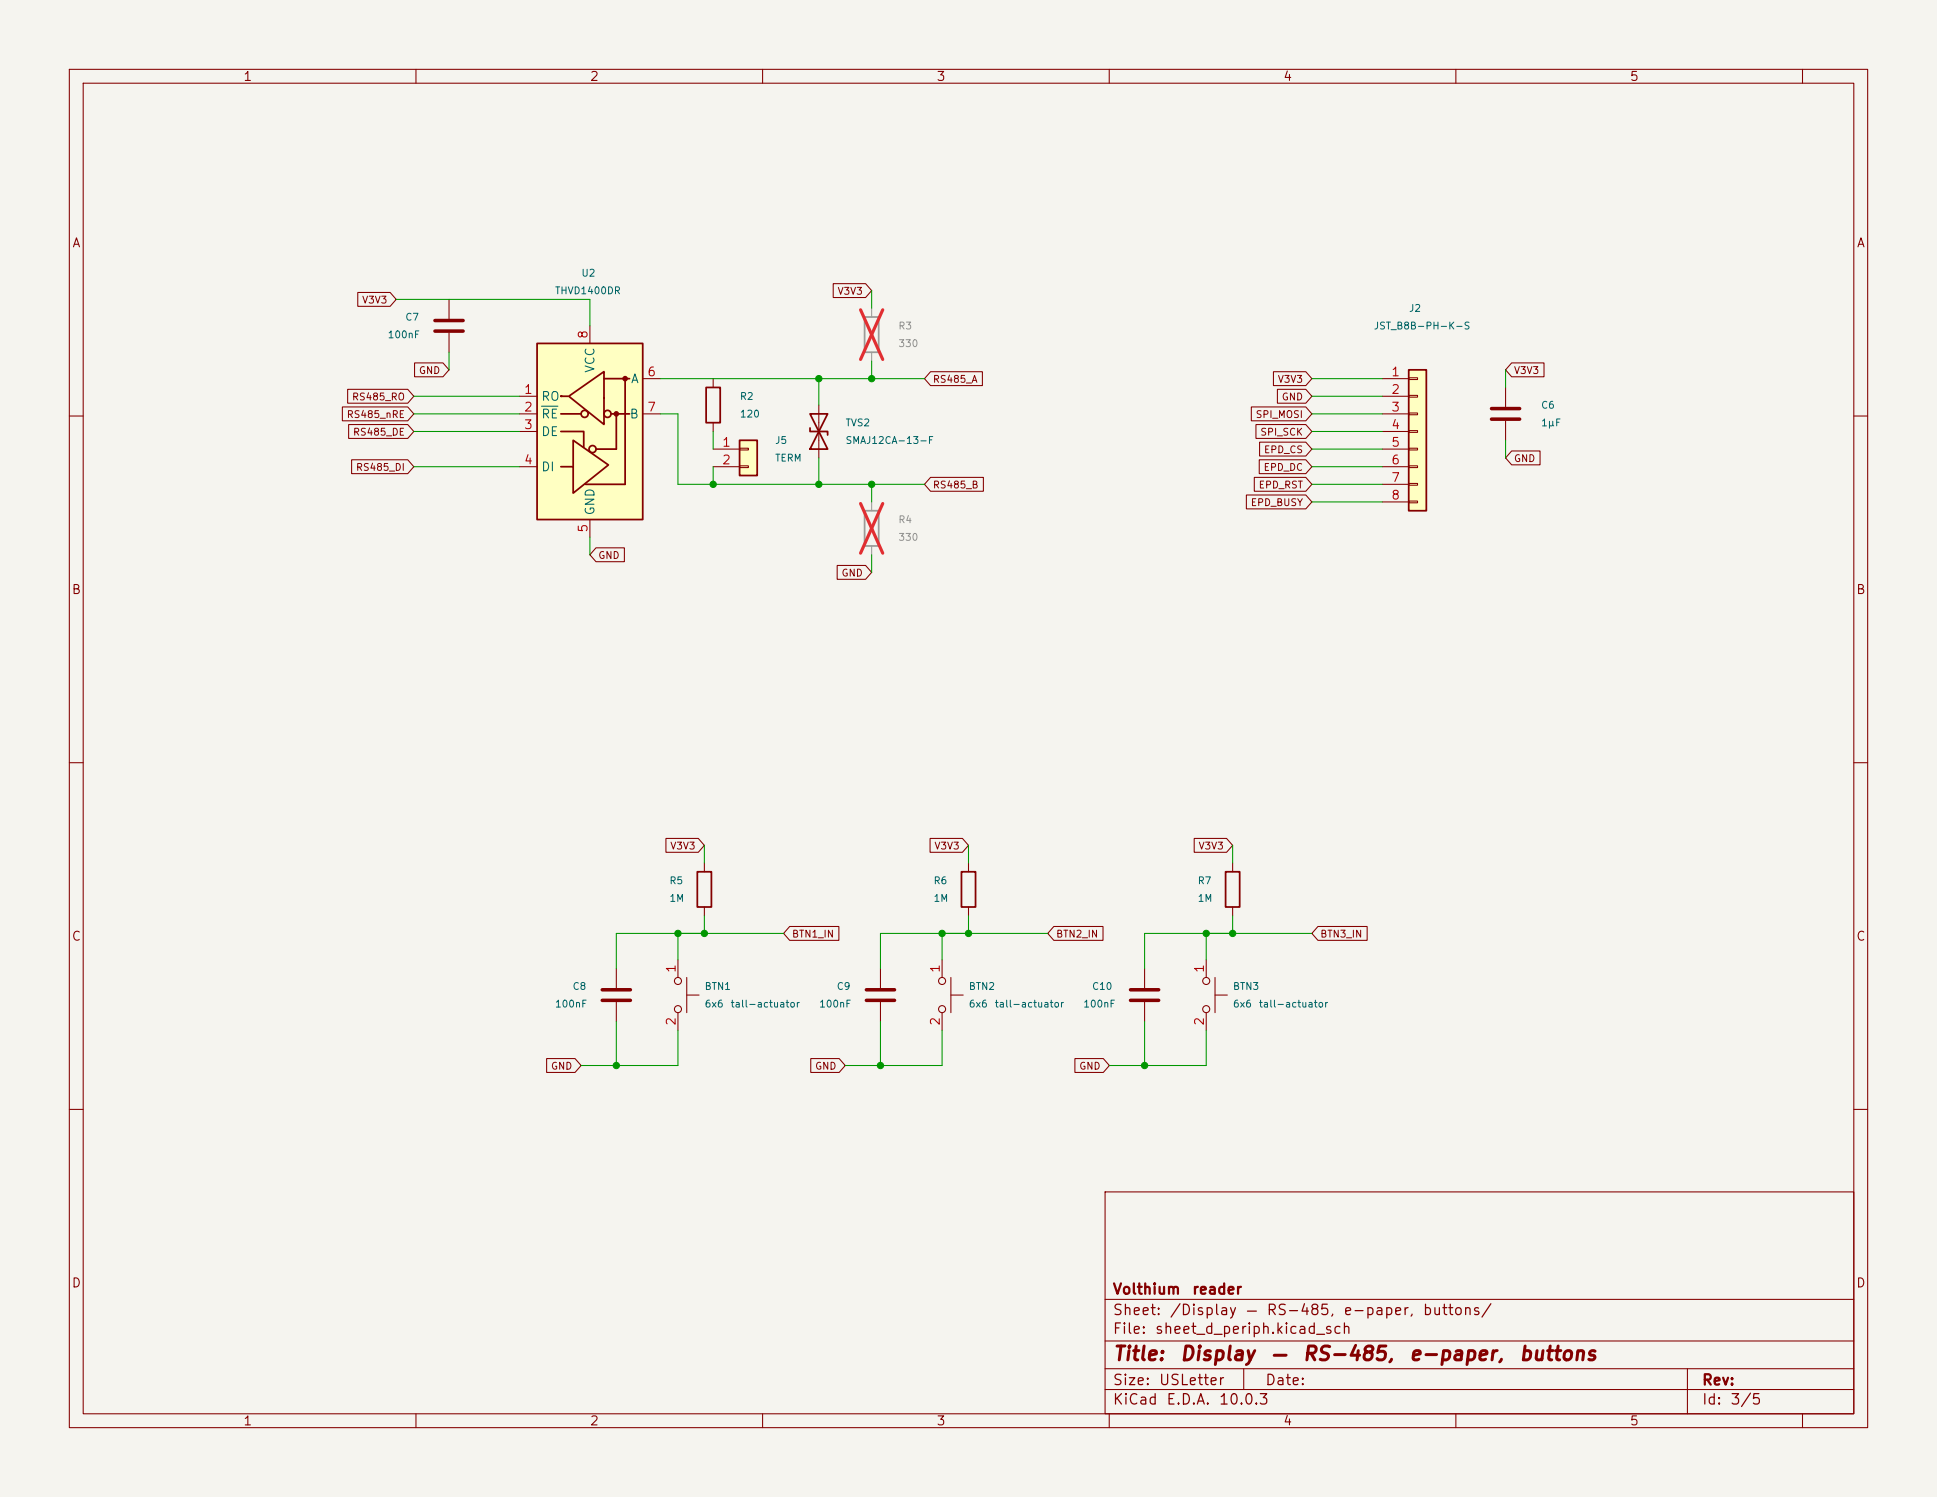
[picture p230: page 3]

Volthium reader
Sheet: /Display — RS-485, e-paper, buttons/
File: sheet_d_periph.kicad_sch
Title: Display — RS-485, e-paper, buttons

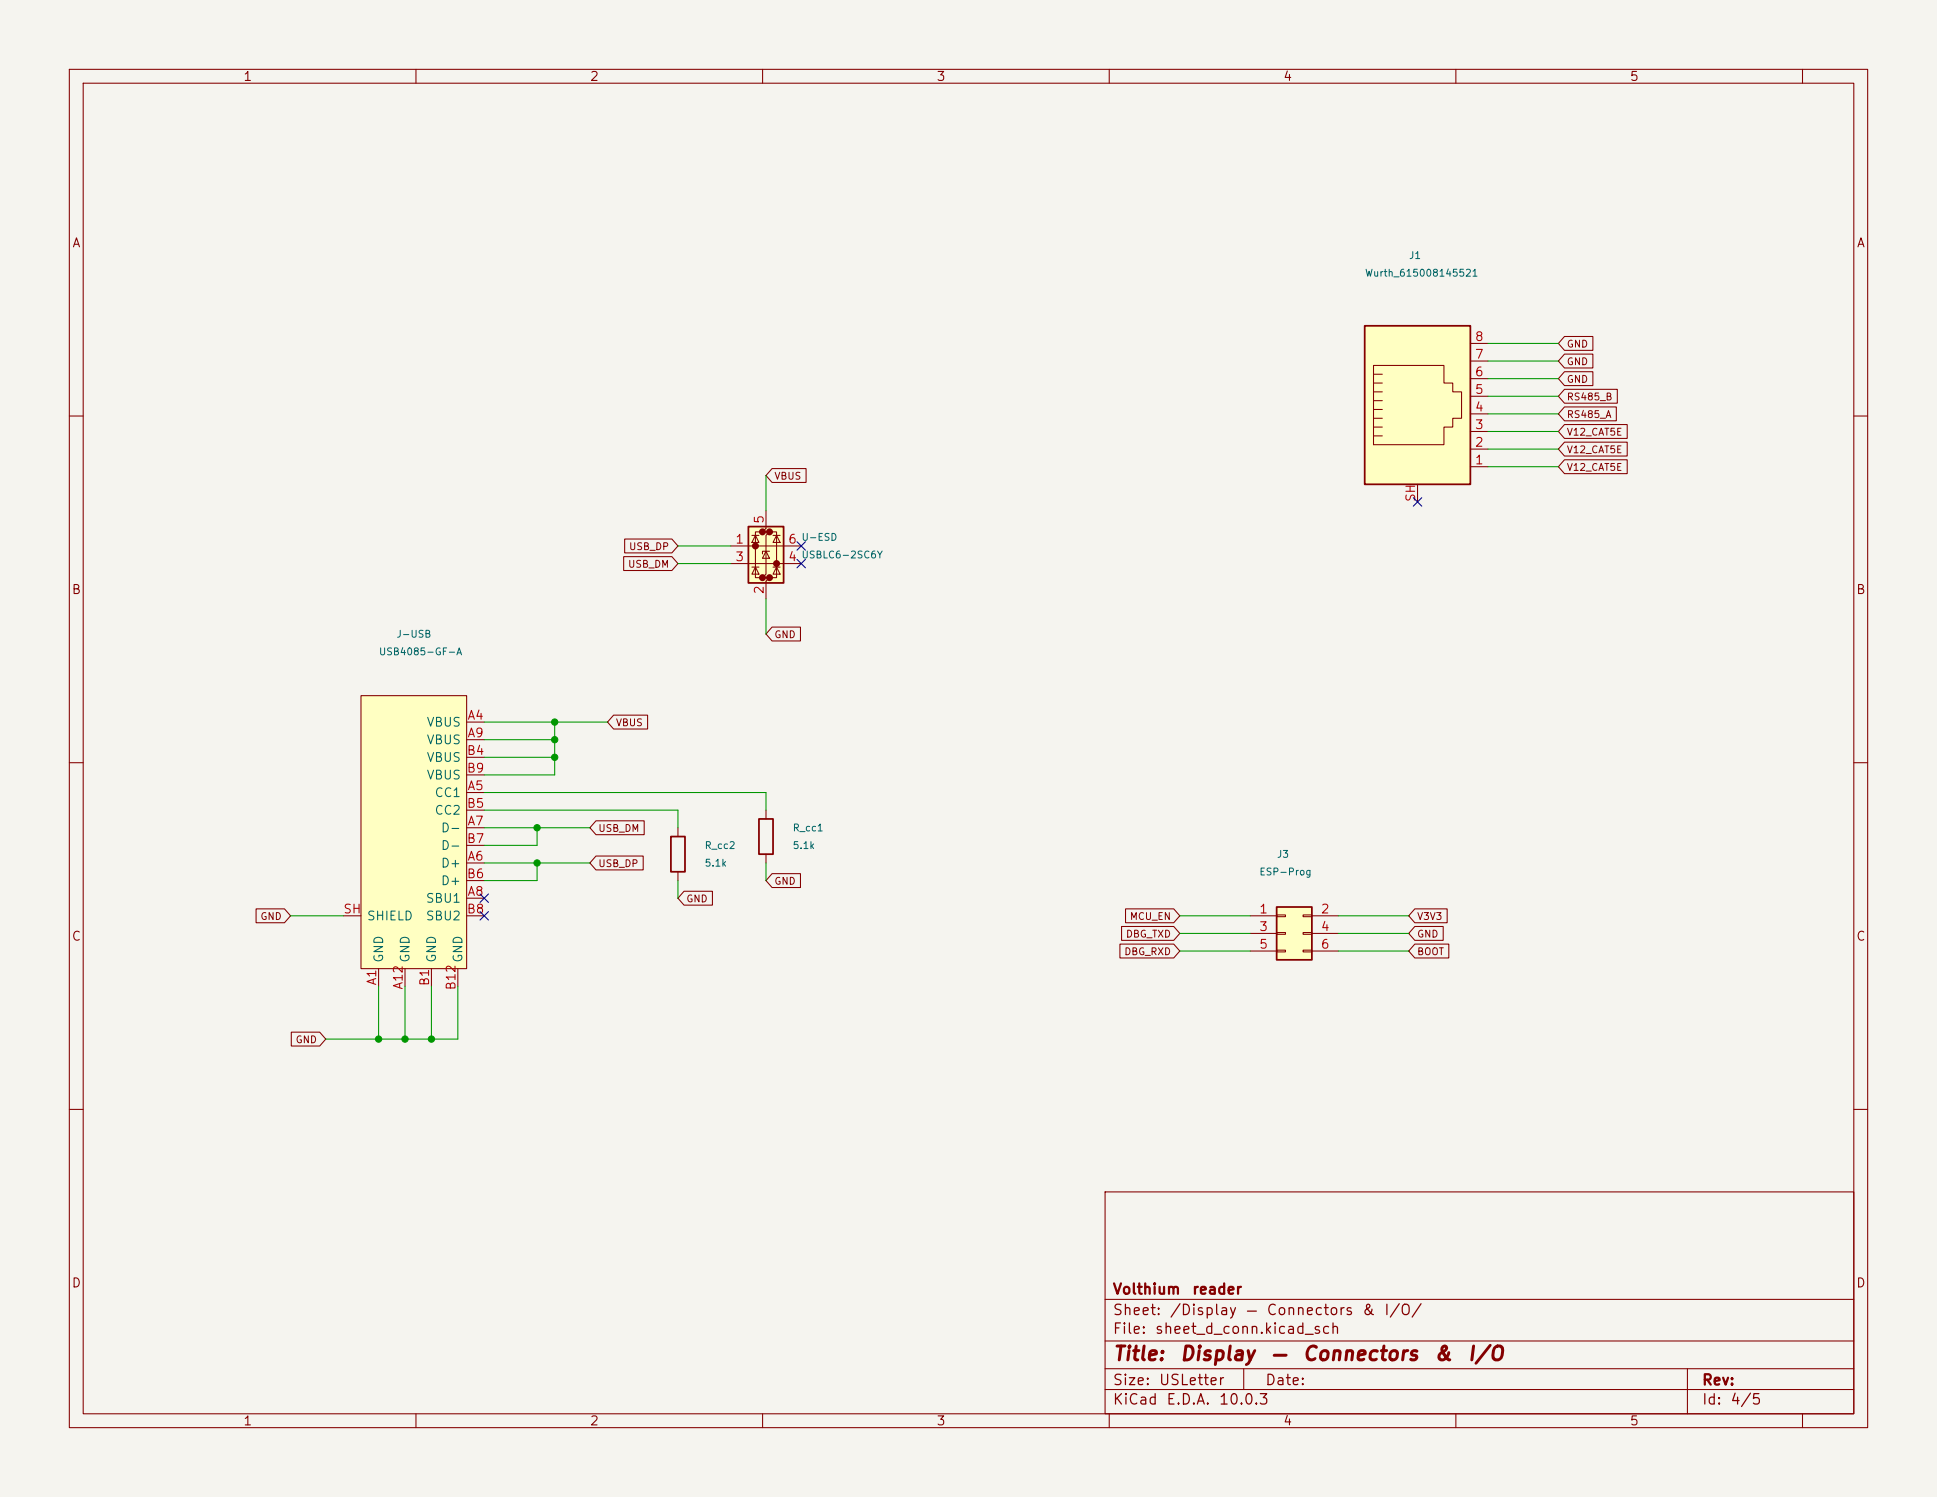
[picture p231: page 4]

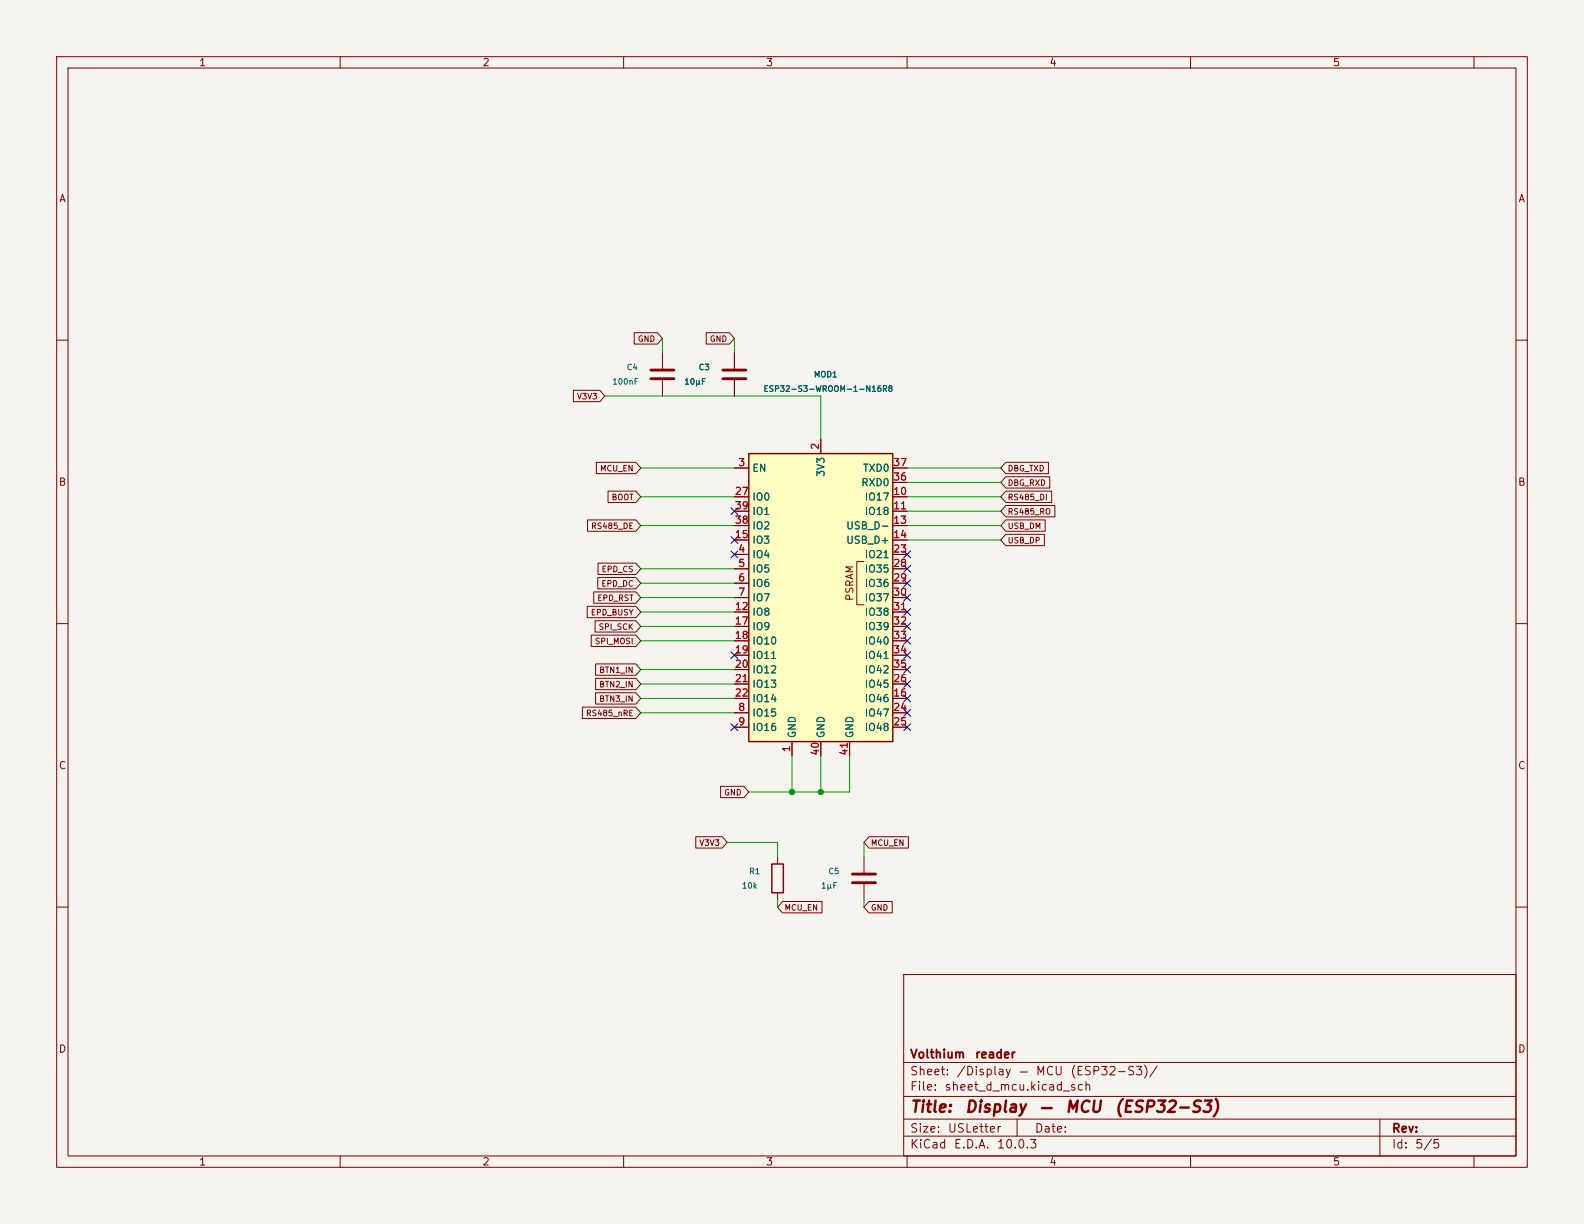
[picture p232: page 5]
