kaanow/volthium_reader/hardware/kicad/schematic/testdata/poison_pdf_battery_sheet_conn.pdf

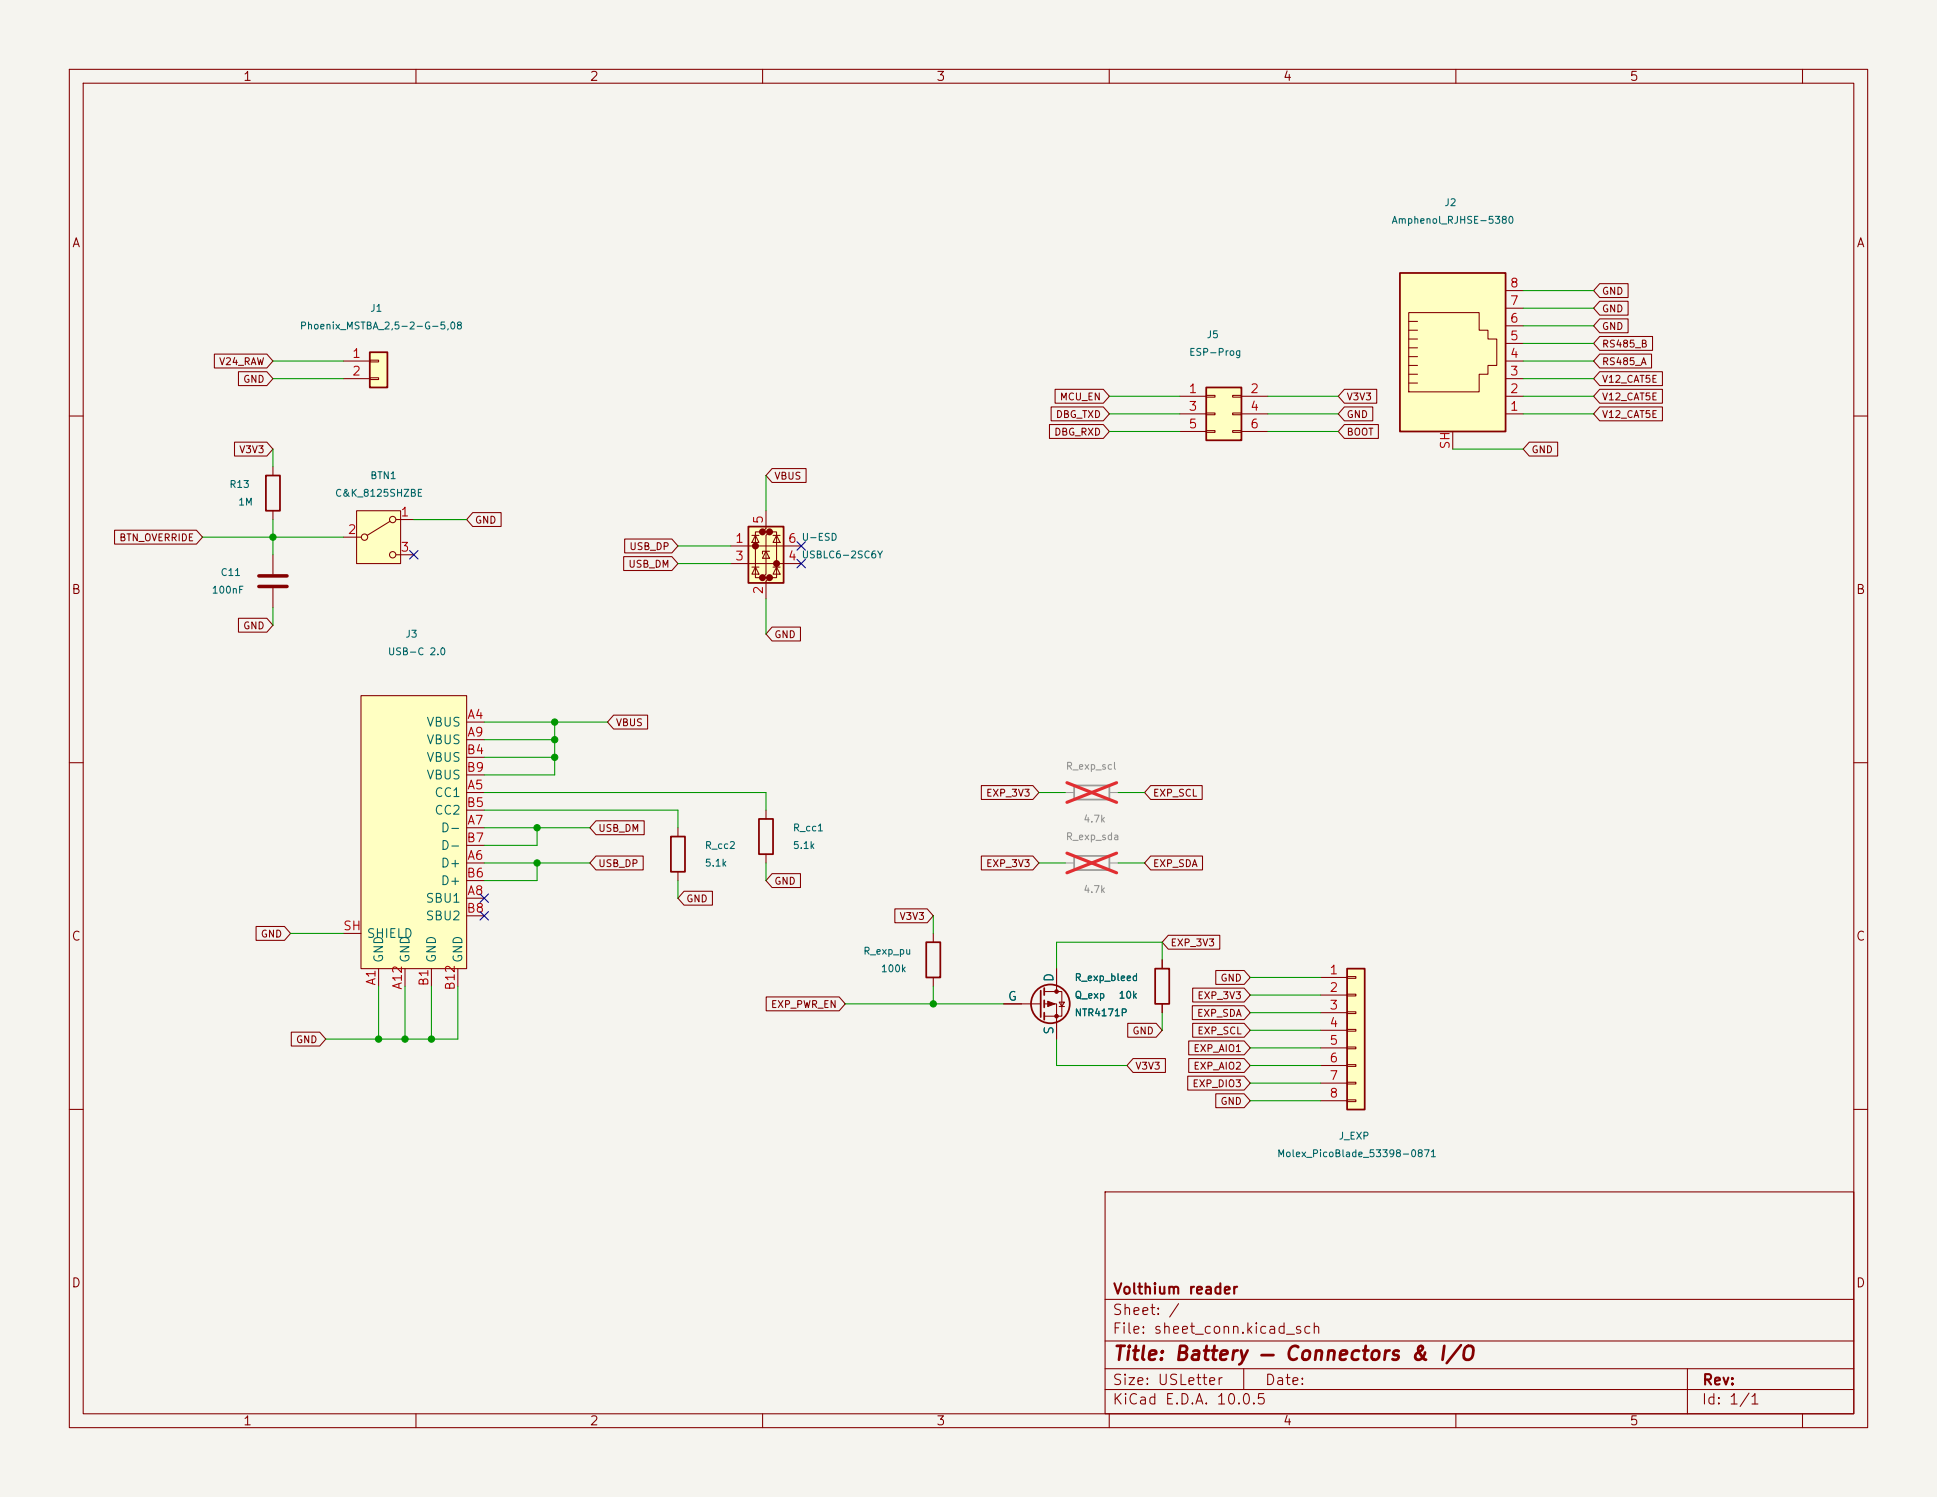
[picture p233: page 1]

Size: USLetter | Rev:
KiCad E.D.A. 10.0.5 | Id: 1/1
