kaanow/volthium_reader/hardware/kicad/schematic/testdata/poison_pdf_display_sheet_d_conn.pdf

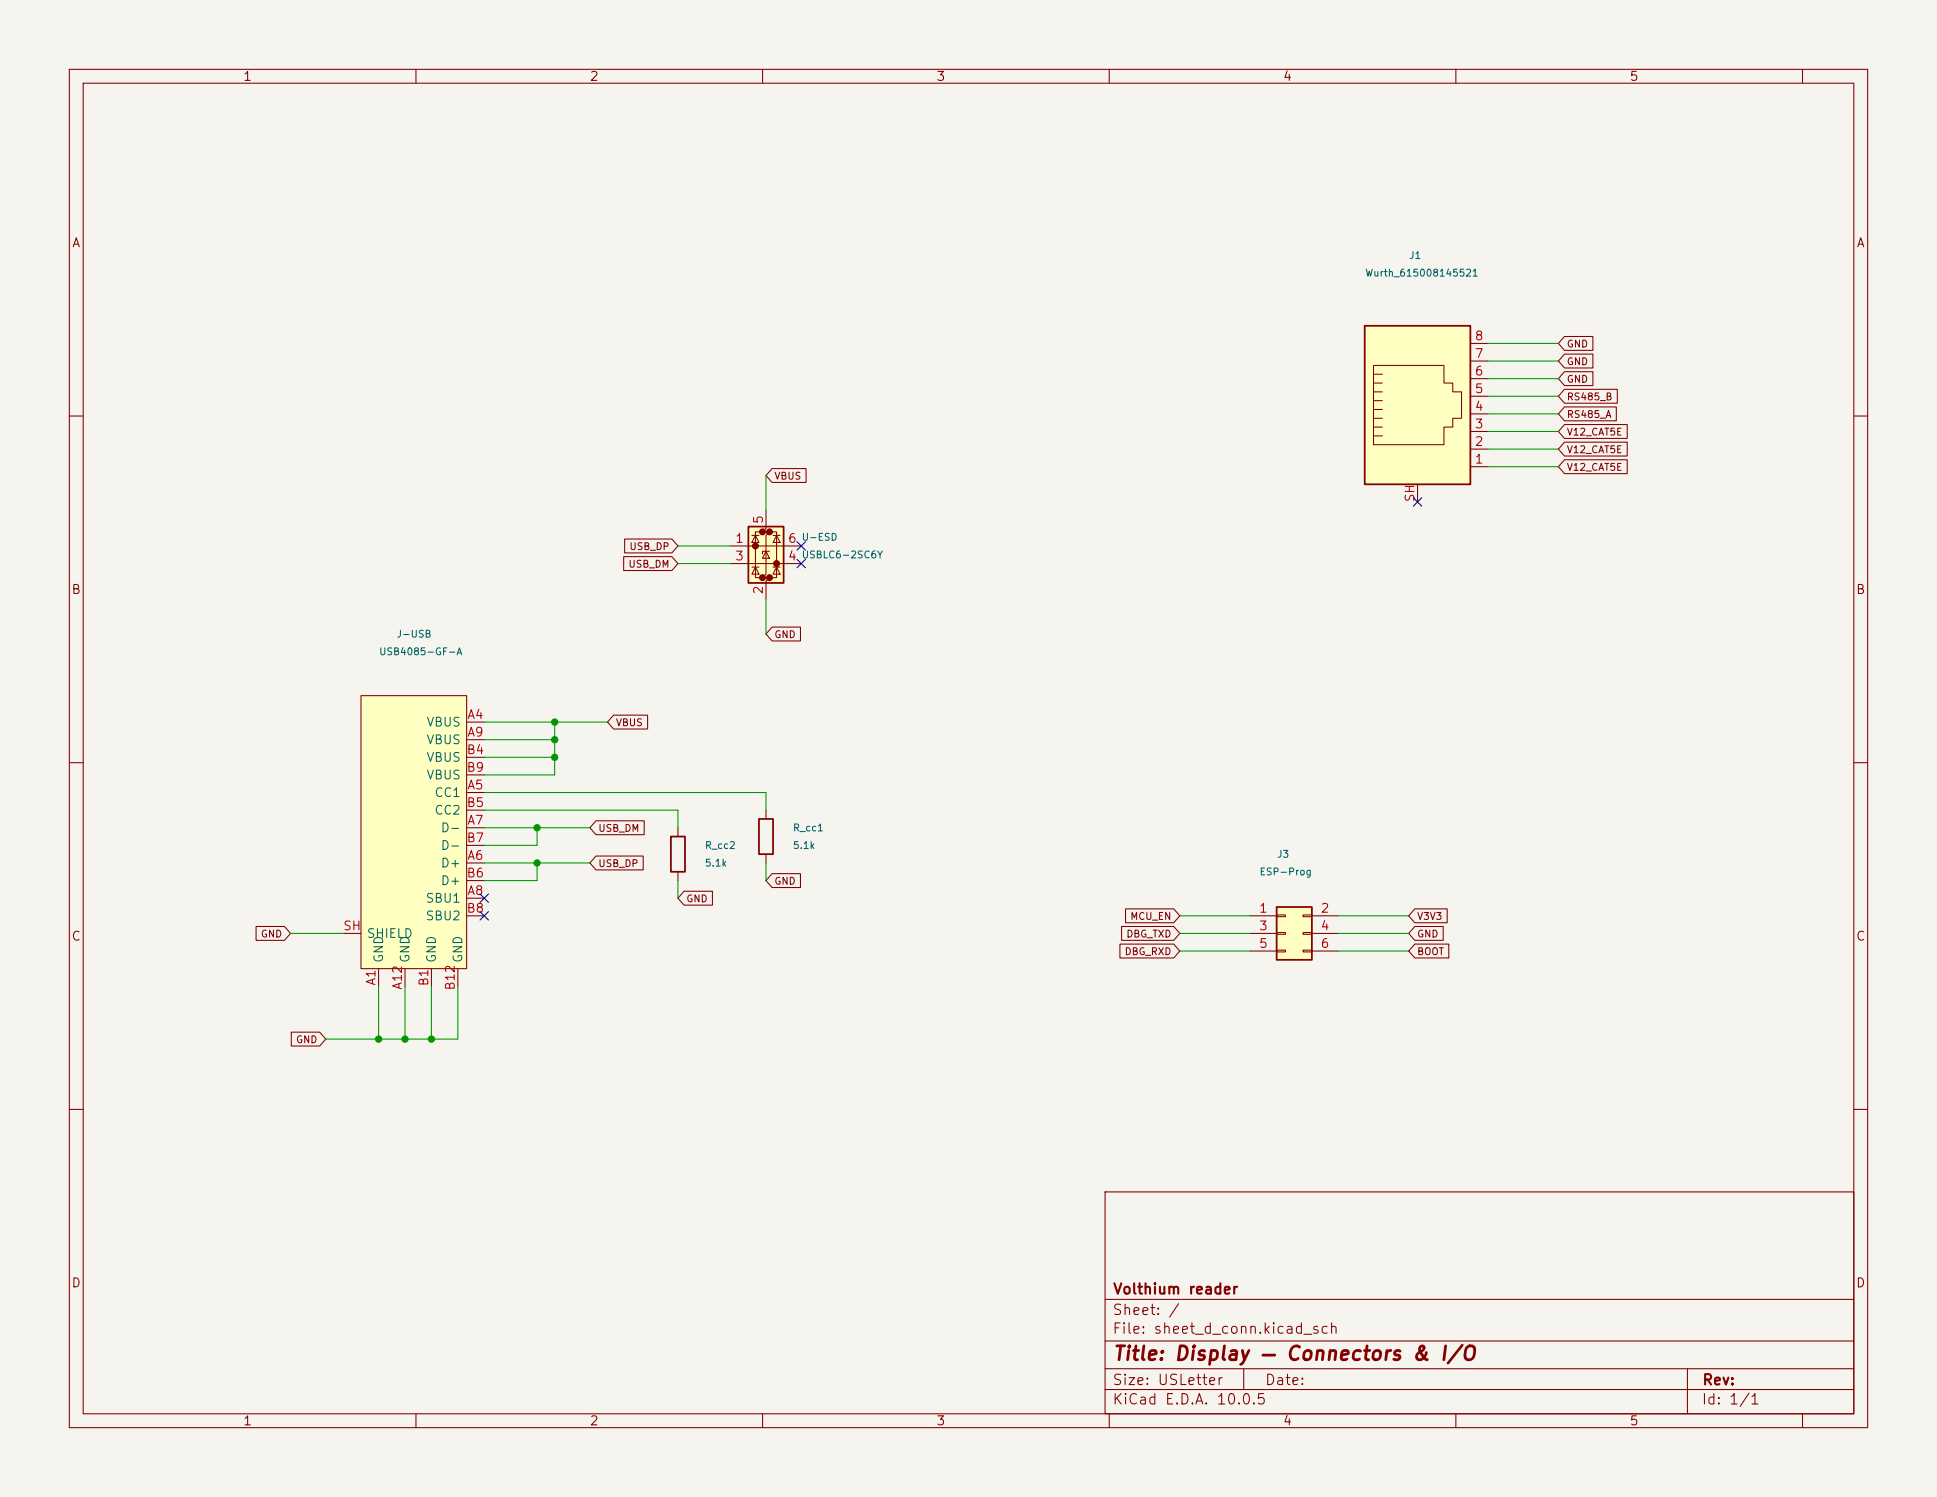
[picture p234: page 1]

Size: USLetter | Rev:
KiCad E.D.A. 10.0.5 | Id: 1/1
