kaanow/volthium_reader/hardware/reviews/visual_inspections/cp2-schematic/display-iter1/reviewer/display_five_sheet_snapshot.pdf

1 | 2 | 3 | 4 | 5

AB

C

D

AB

C

## D Date:

## KiCad E.D.A. 10.0.5

Size: USLetter | Rev: Id: 1/5

# Title: Volthium reader — display-side (root)

## File: volthium_display.kicad_sch

## Sheet: /

## Volthium reader

# Display — Power path

# File: sheet_d_power.kicad_sch

# Display — Connectors & I/O

# File: sheet_d_conn.kicad_sch

# Display — RS-485, e-paper, buttons

# File: sheet_d_periph.kicad_sch

# Display — MCU (ESP32-S3)

# File: sheet_d_mcu.kicad_sch

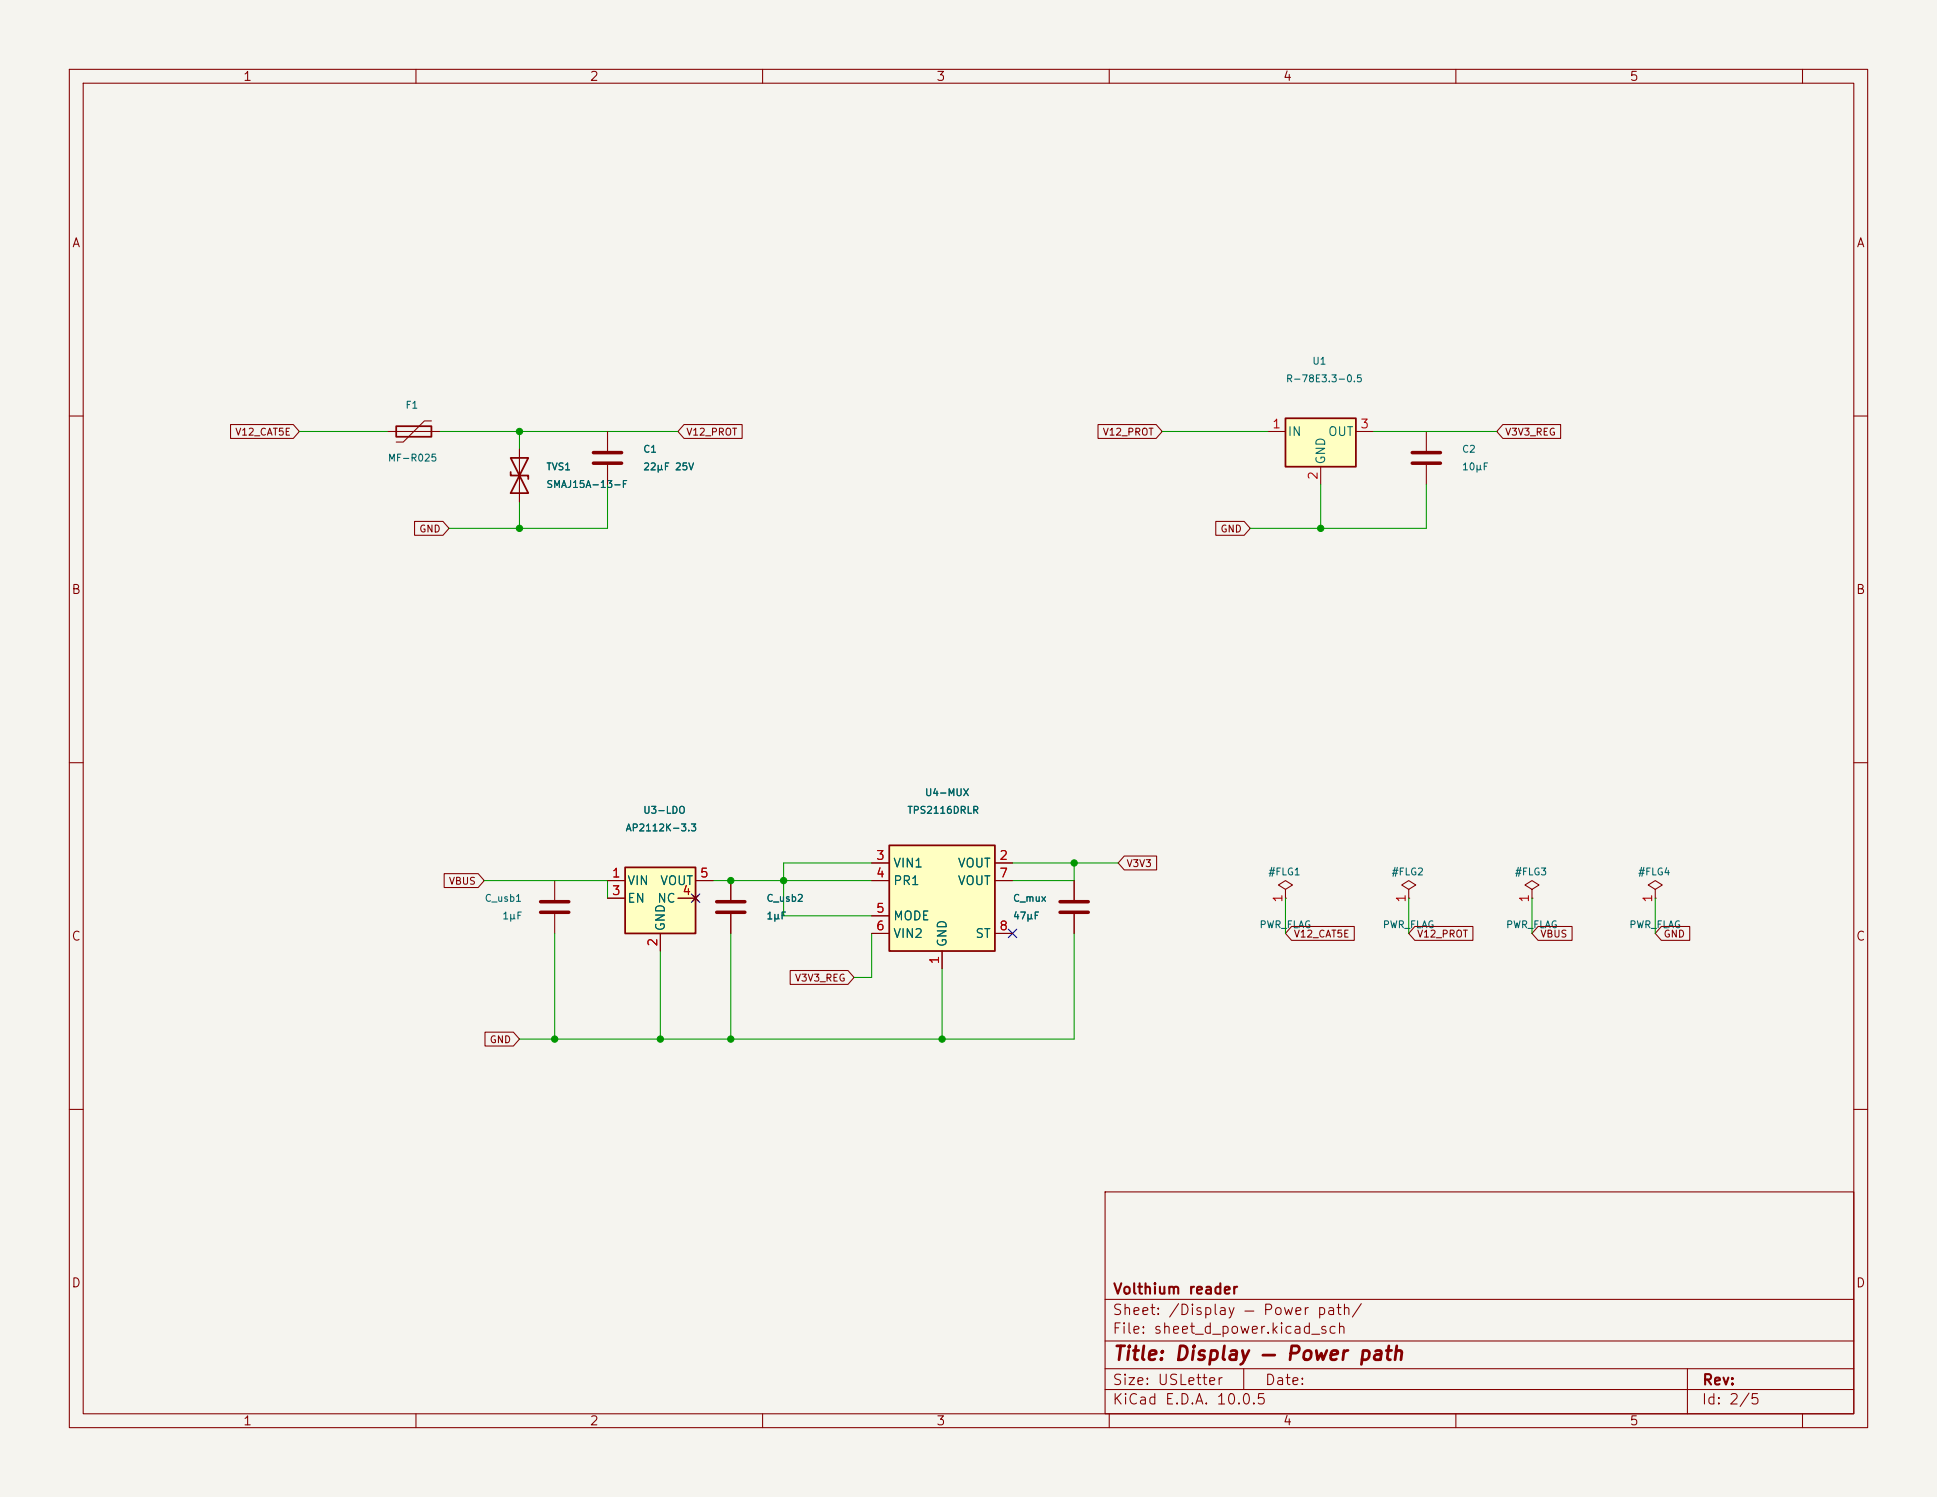
[picture p235: page 2]
D Date:; TVS1; SMAJ15A-13-F; VOUT 7 GND; VOUT 2; VIN1 3 PR1 4 MODE 5; VIN2 6; U4-MUX; TPS2116DRLR; C_usb2; 1µF VIN 1; GND; VOUT 5; U3-LDO; C_usb1; C_mux 47µF; #FLG2 PWR_FLAG; #FLG3 PWR_FLAG; #FLG4 PWR_FLAG; 2 OUT 3; #FLG1 PWR_FLAG; V12_PROT V3V3_REG; VBUS; VBUS GND; V12_CAT5E; V12_PROT; V3V3_REG U3-LDO; AP2112K-3.3 VIN 1; TPS2116DRLR VOUT 7 GND

Volthium reader
Sheet: /Display — Power path/
File: sheet_d_power.kicad_sch
Title: Display — Power path

A 6 B

# V3V3 GND

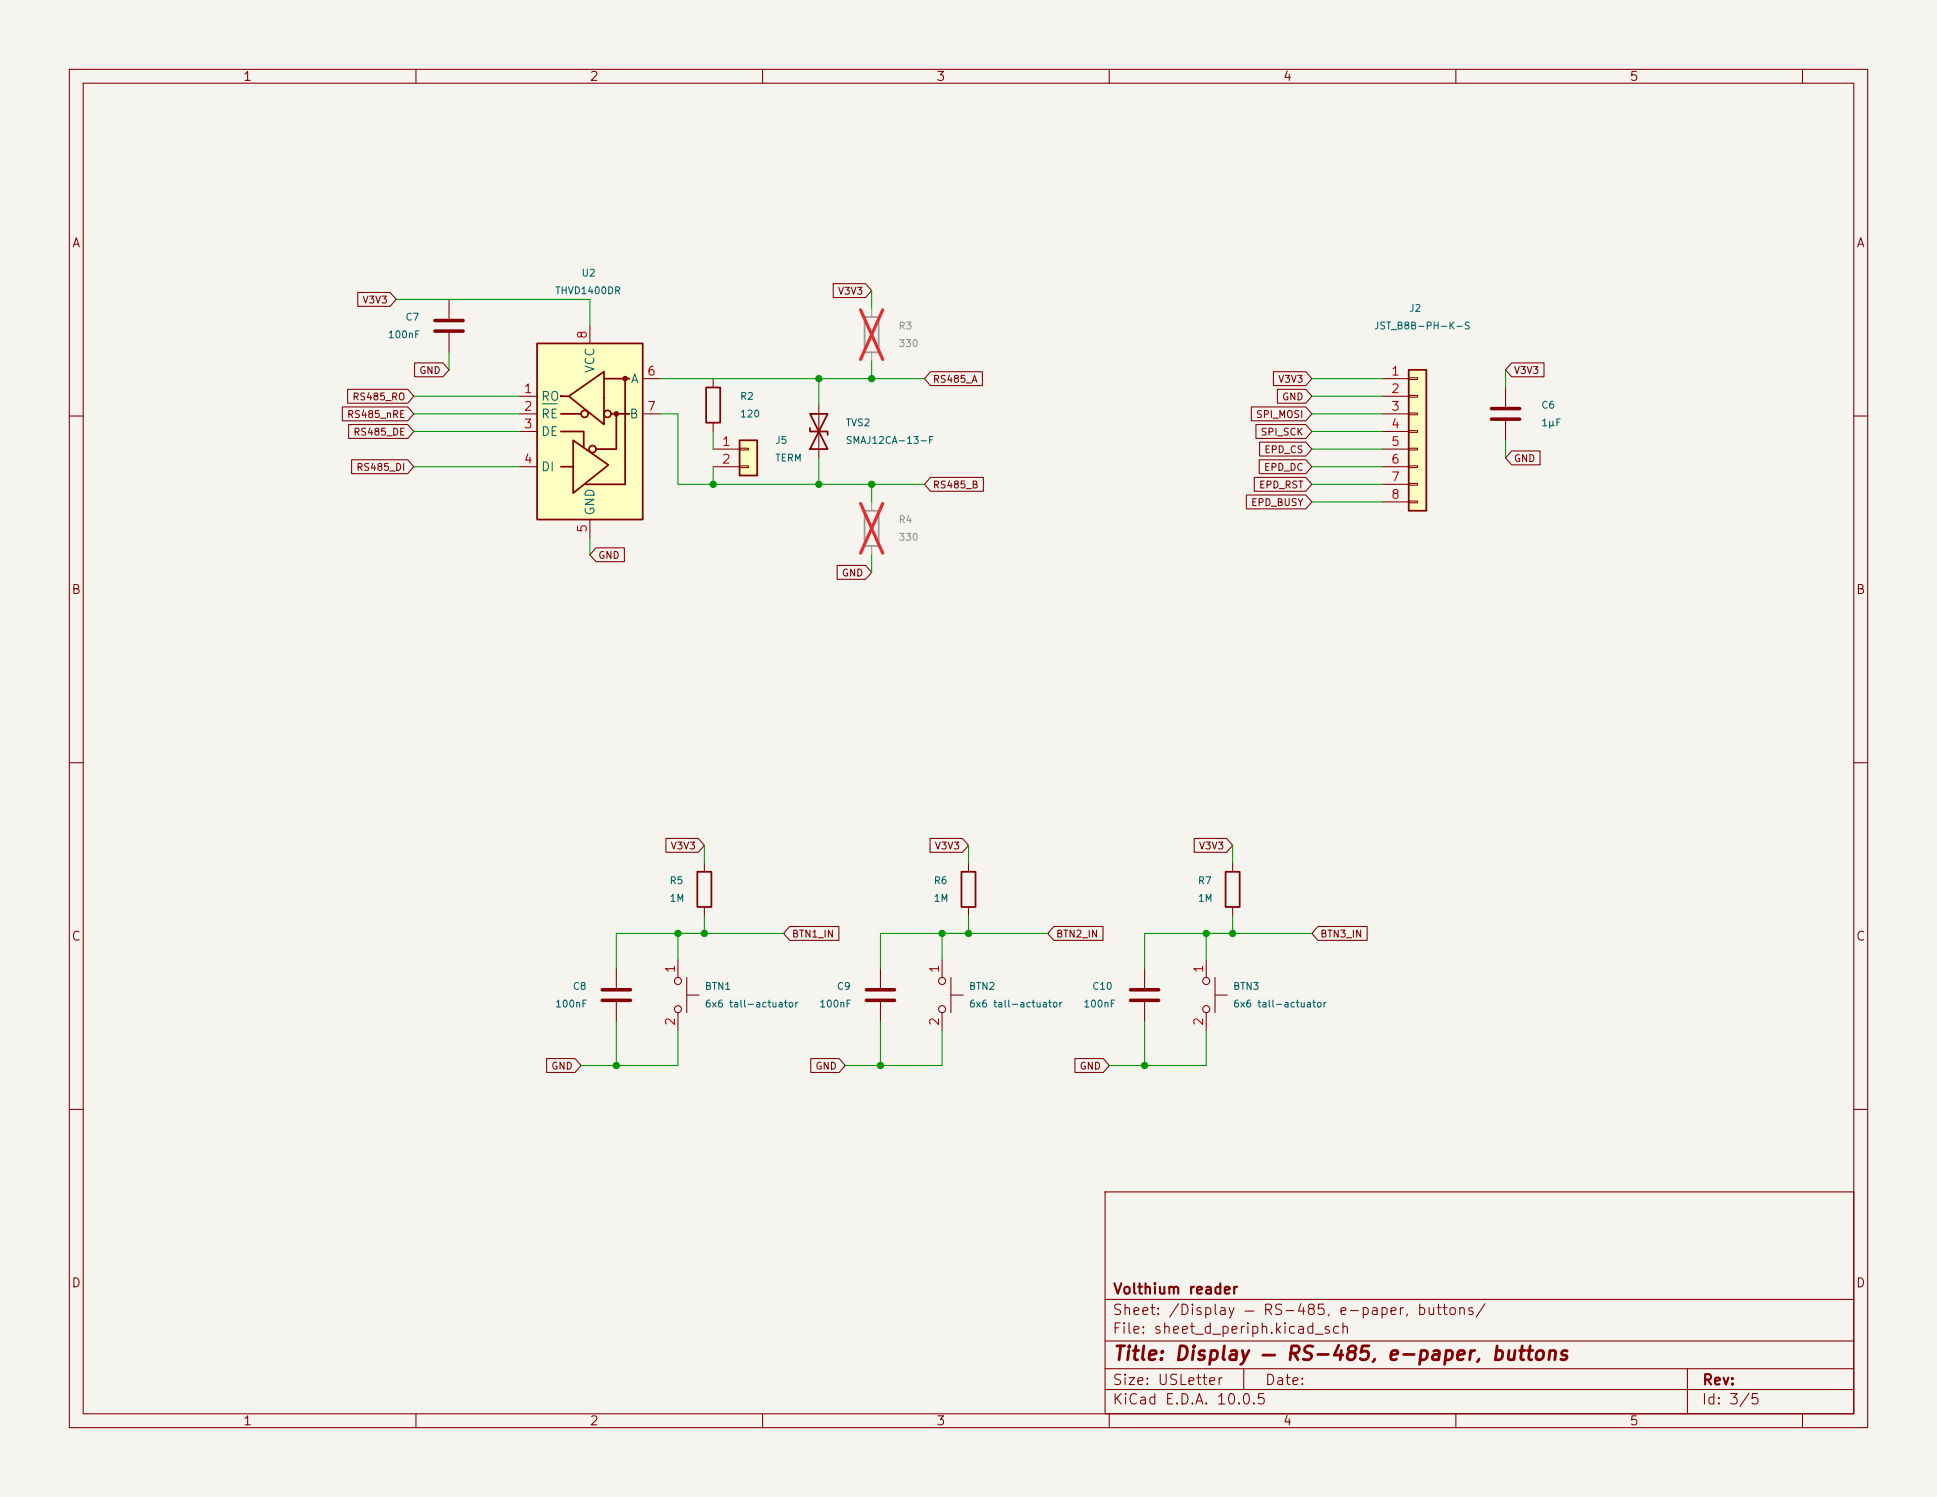
[picture p236: page 3]

Volthium reader
Sheet: /Display — RS-485, e-paper, buttons/
File: sheet_d_periph.kicad_sch
Title: Display — RS-485, e-paper, buttons

8 SH

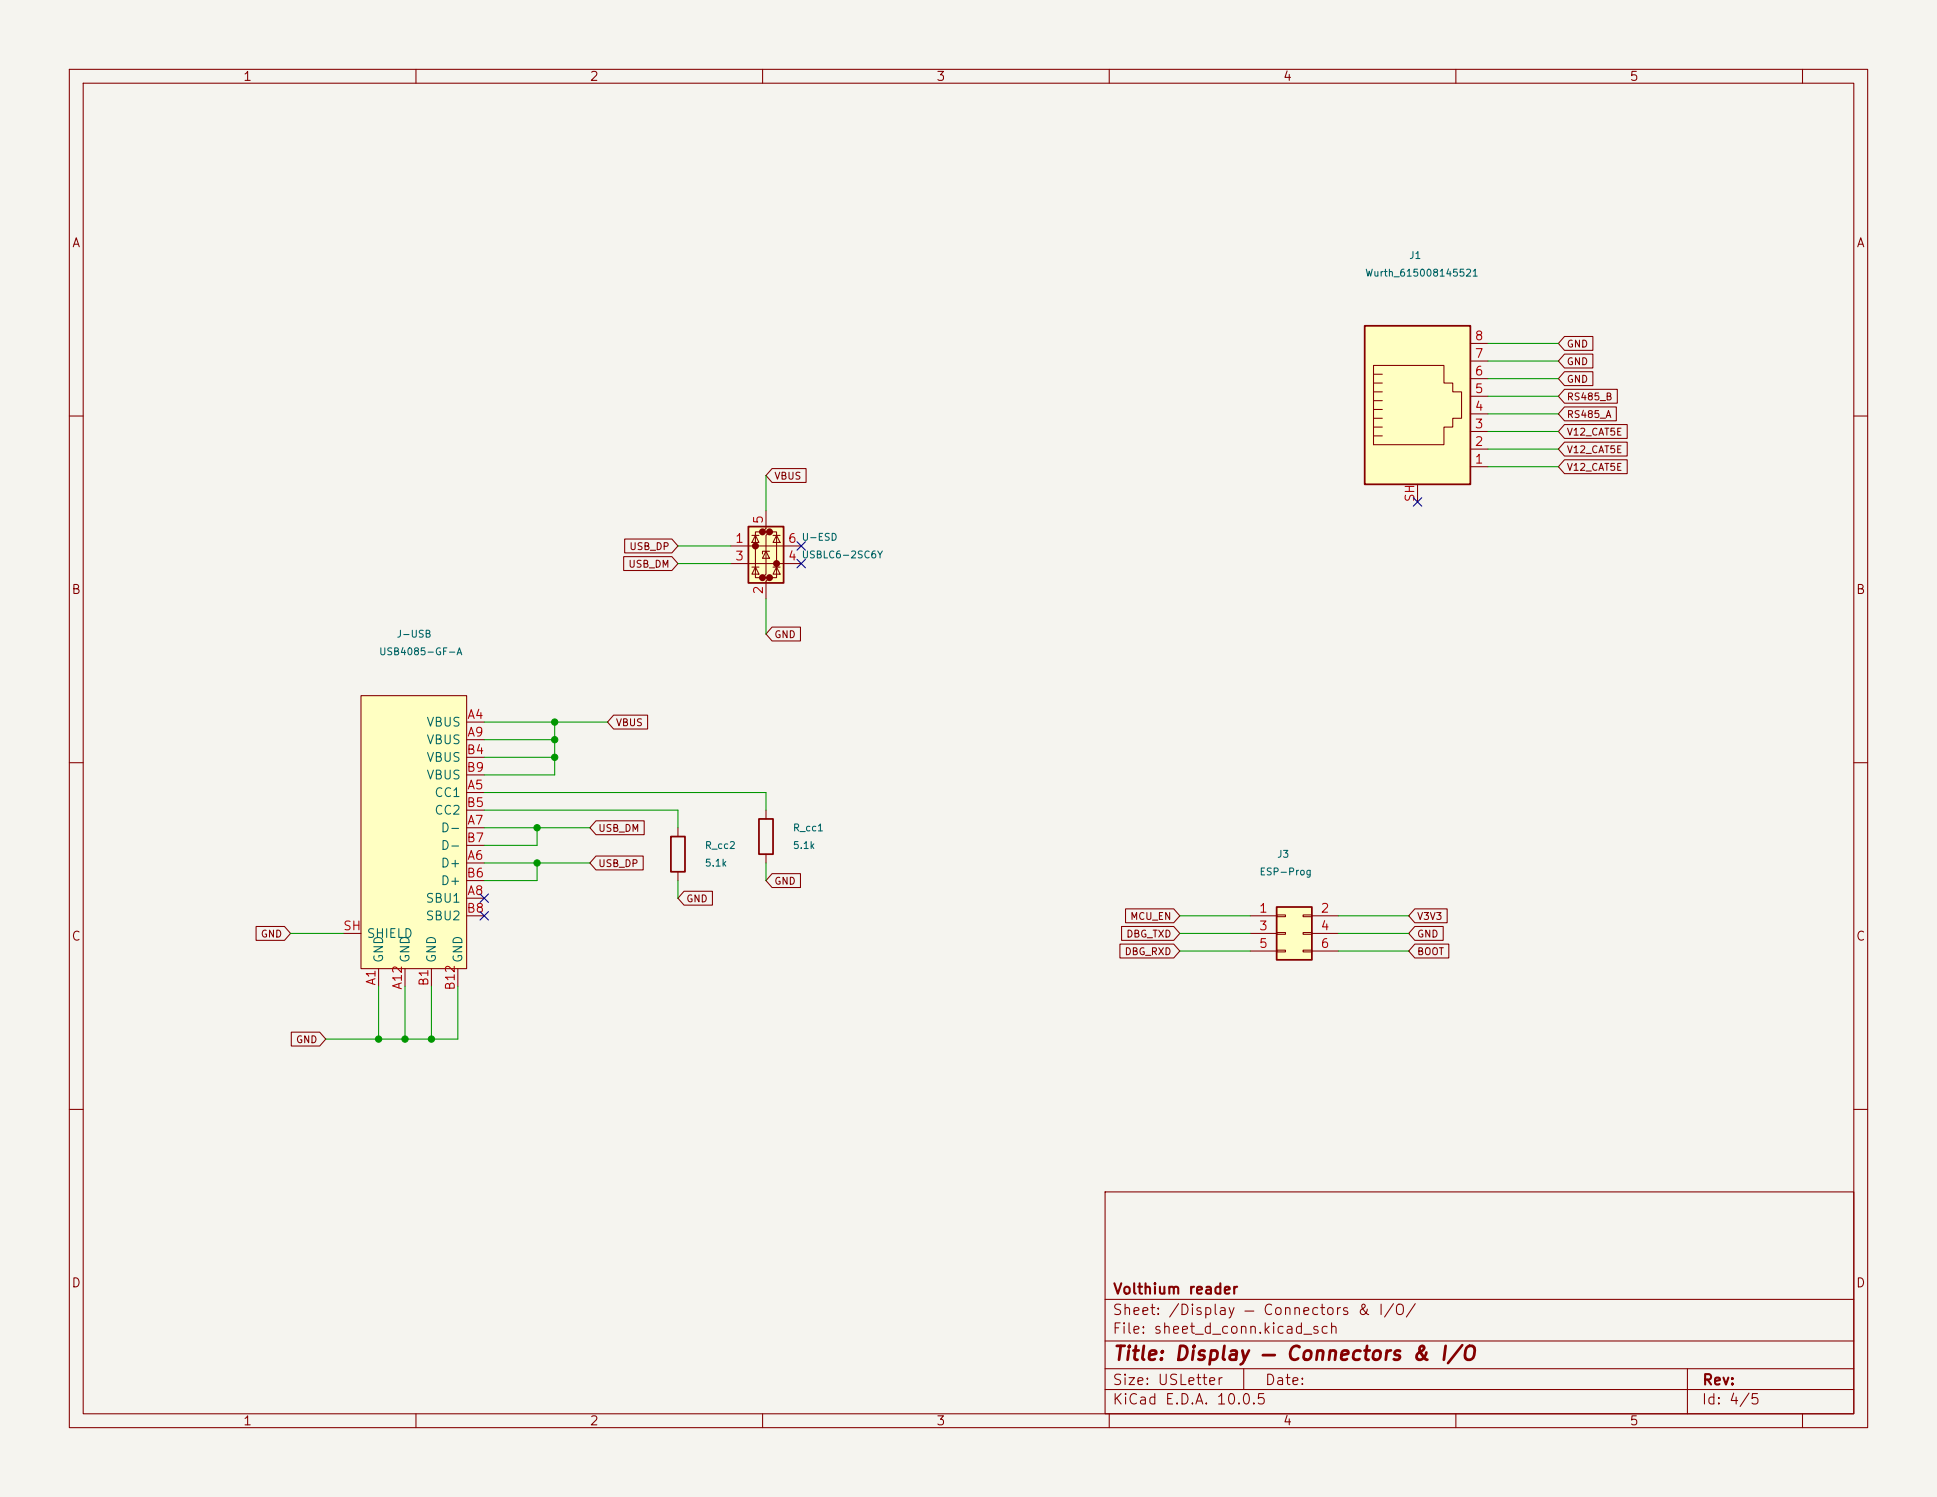
[picture p237: page 4]
D Date:; J1 Wurth_615008145521 GND A1; VBUS A4 CC1 A5 D+ A6 D- A7; SBU1 A8; VBUS A9 GND A12; GND B1; VBUS B4 CC2 B5 D+ B6 D- B7; SBU2 B8; VBUS B9 GND B12; SHIELD SH; J-USB USB4085-GF-A; ESP-Prog 1; 6 U-ESD USBLC6-2SC6Y R_cc2; 5.1k GND; DBG_TXD; GND; V12_CAT5E GND; V3V3 BOOT; V12_CAT5E; V12_CAT5E RS485_A RS485_B; GND MCU_EN; DBG_RXD; VBUS; GND USB_DP USB_DM; USB_DP; VBUS USB_DM

Volthium reader
Sheet: /Display — Connectors & I/O/
File: sheet_d_conn.kicad_sch
Title: Display — Connectors & I/O

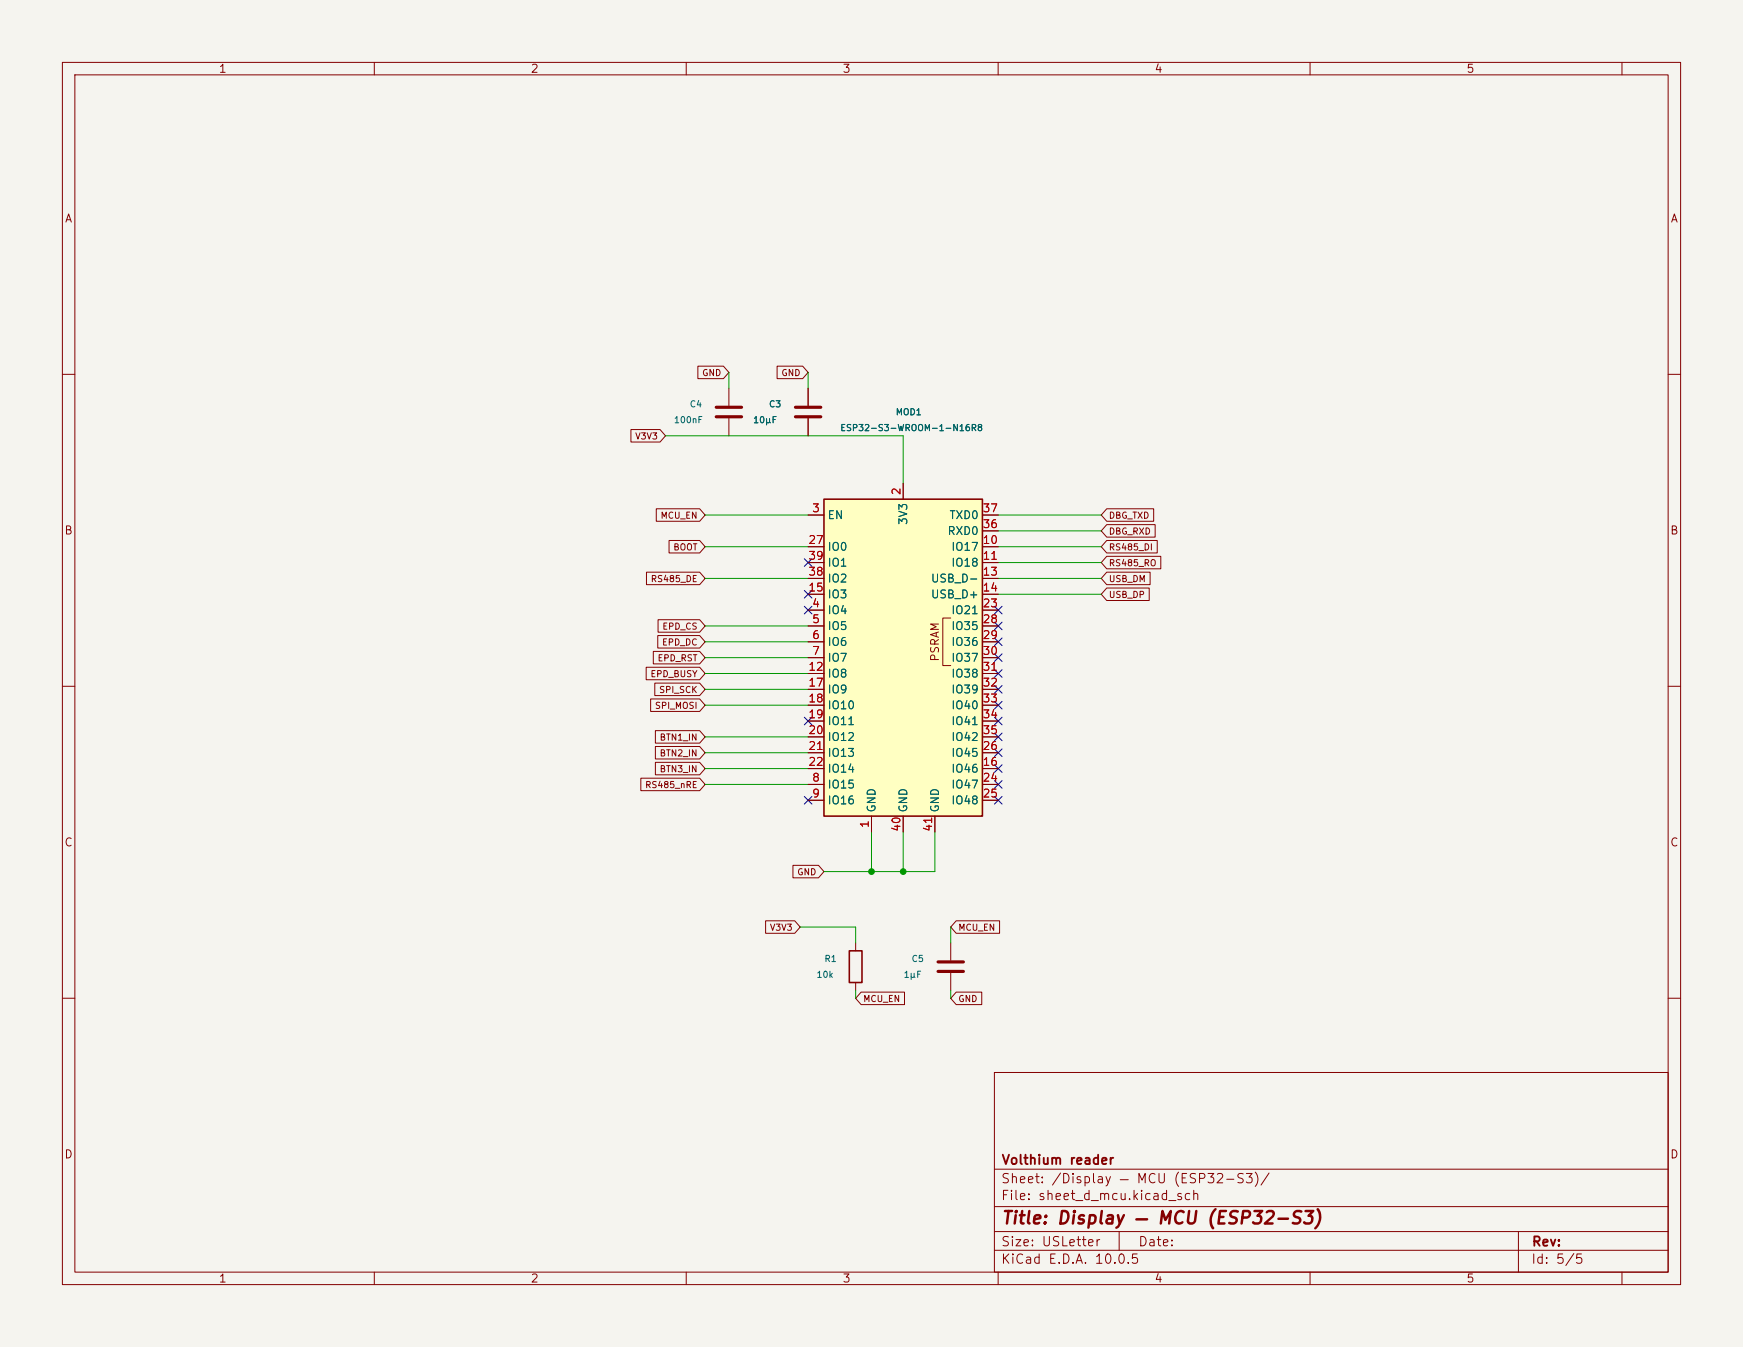
[picture p238: page 5]
D Date:; PSRAM GND; USB_D- 13 USB_D+ 14 IO3 15; IO42 35 RXD0 36 TXD0 37; GND 40; GND 41; MOD1 ESP32-S3-WROOM-1-N16R8 C5; GND; RS485_nRE BTN3_IN; BTN2_IN; BTN1_IN; RS485_DI GND; MCU_EN; EPD_CS; SPI_MOSI RS485_DE SPI_SCK; EPD_BUSY EPD_RST EPD_DC; USB_DM; USB_DP; DBG_TXD; DBG_RXD MCU_EN; BOOT V3V3; MOD1; ESP32-S3-WROOM-1-N16R8 GND

Volthium reader
Sheet: /Display — MCU (ESP32-S3)/
File: sheet_d_mcu.kicad_sch
Title: Display — MCU (ESP32-S3)
