kaanow/volthium_reader/hardware/reviews/visual_inspections/cp2-schematic/iter2/reviewer/battery_schematic.pdf

Battery — USB maintenance power

Battery — Isolated RS-485 read (ch.1)

Battery — Isolated RS-485 read (ch.2)

Volthium reader
Sheet: /
File: volthium_reader.kicad_sch
Title: Volthium reader — battery-side (root)

Size: USLetter | Rev:
KiCad E.D.A. 10.0.5 | Id: 1/9


Sheet: /Battery — Power path/
File: sheet_power.kicad_sch
Title: Battery — Power path



isoPower (ADM2587E fig 35) BUS PROTECTION - PROVISIONING (ALL DNP, F36/F44)

L11 = the ONLY GND2_DCDC1-to-ISO_BUS_GND1 tie

Volthium reader
Sheet: /Battery — Isolated RS-485 read (ch.1)/
File: sheet_isors485_1.kicad_sch
Title: Battery — Isolated RS-485 read (ch.1)


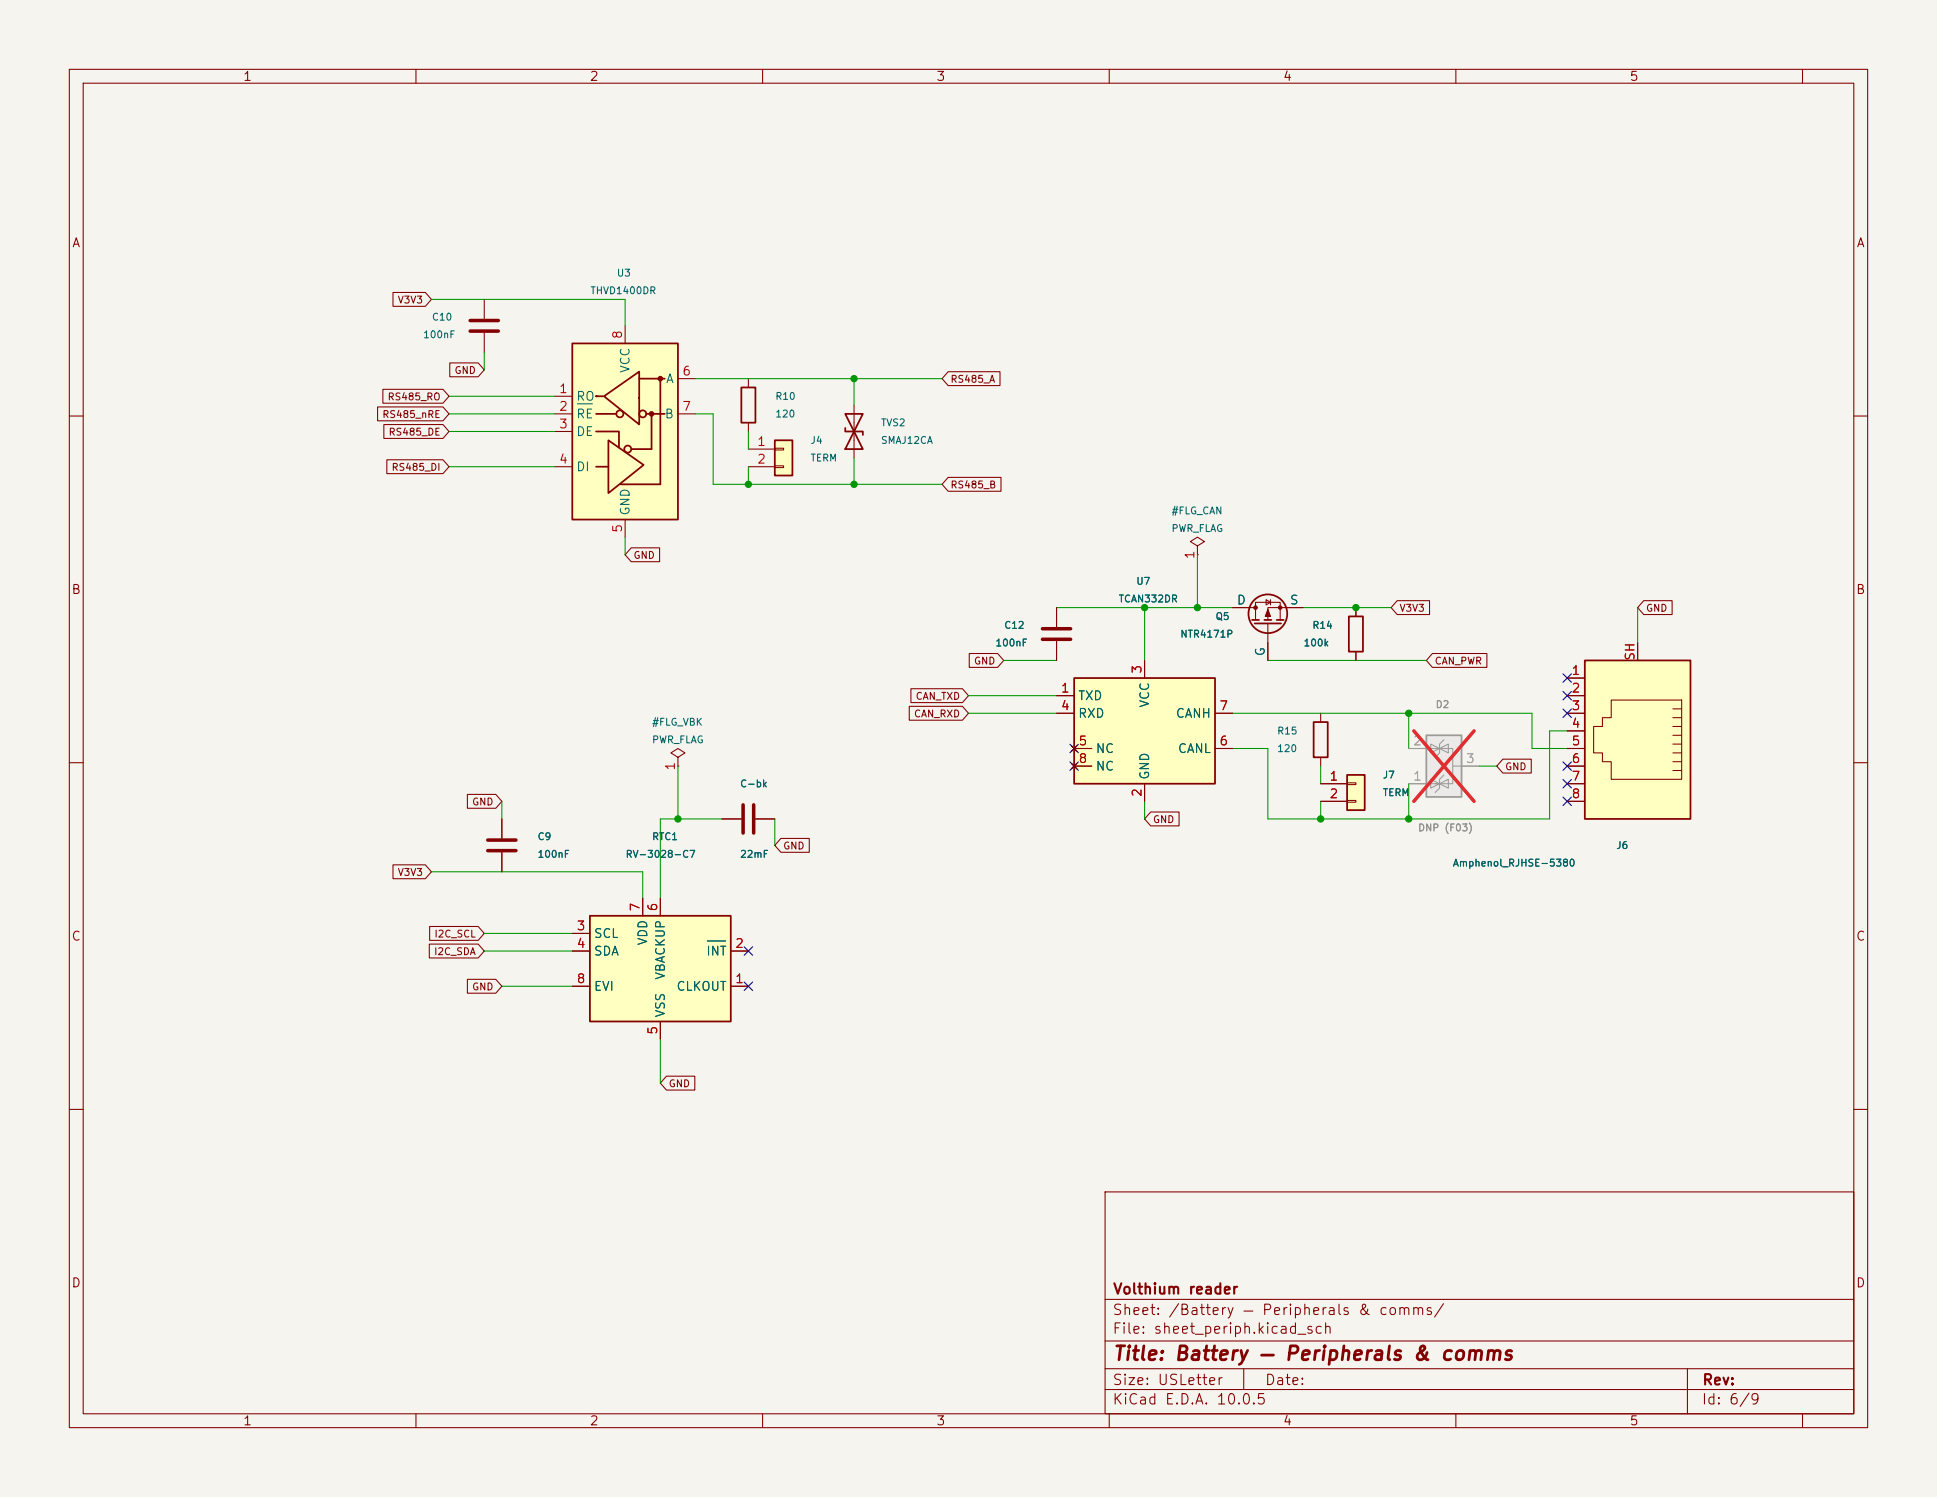
[picture p248: page 6]

3 RXD 4 NC 5 CANL 6 CANH 7 NC 8

Sheet: /Battery — Peripherals & comms/
File: sheet_periph.kicad_sch
Title: Battery — Peripherals & comms


Volthium reader
Sheet: /Battery — USB maintenance power/
File: sheet_usb.kicad_sch
Title: Battery — USB maintenance power


isoPower (ADM2587E fig 35) BUS PROTECTION - PROVISIONING (ALL DNP, F36/F44)

L13 = the ONLY GND2_DCDC2-to-ISO_BUS_GND2 tie

Volthium reader
Sheet: /Battery — Isolated RS-485 read (ch.2)/
File: sheet_isors485_2.kicad_sch
Title: Battery — Isolated RS-485 read (ch.2)

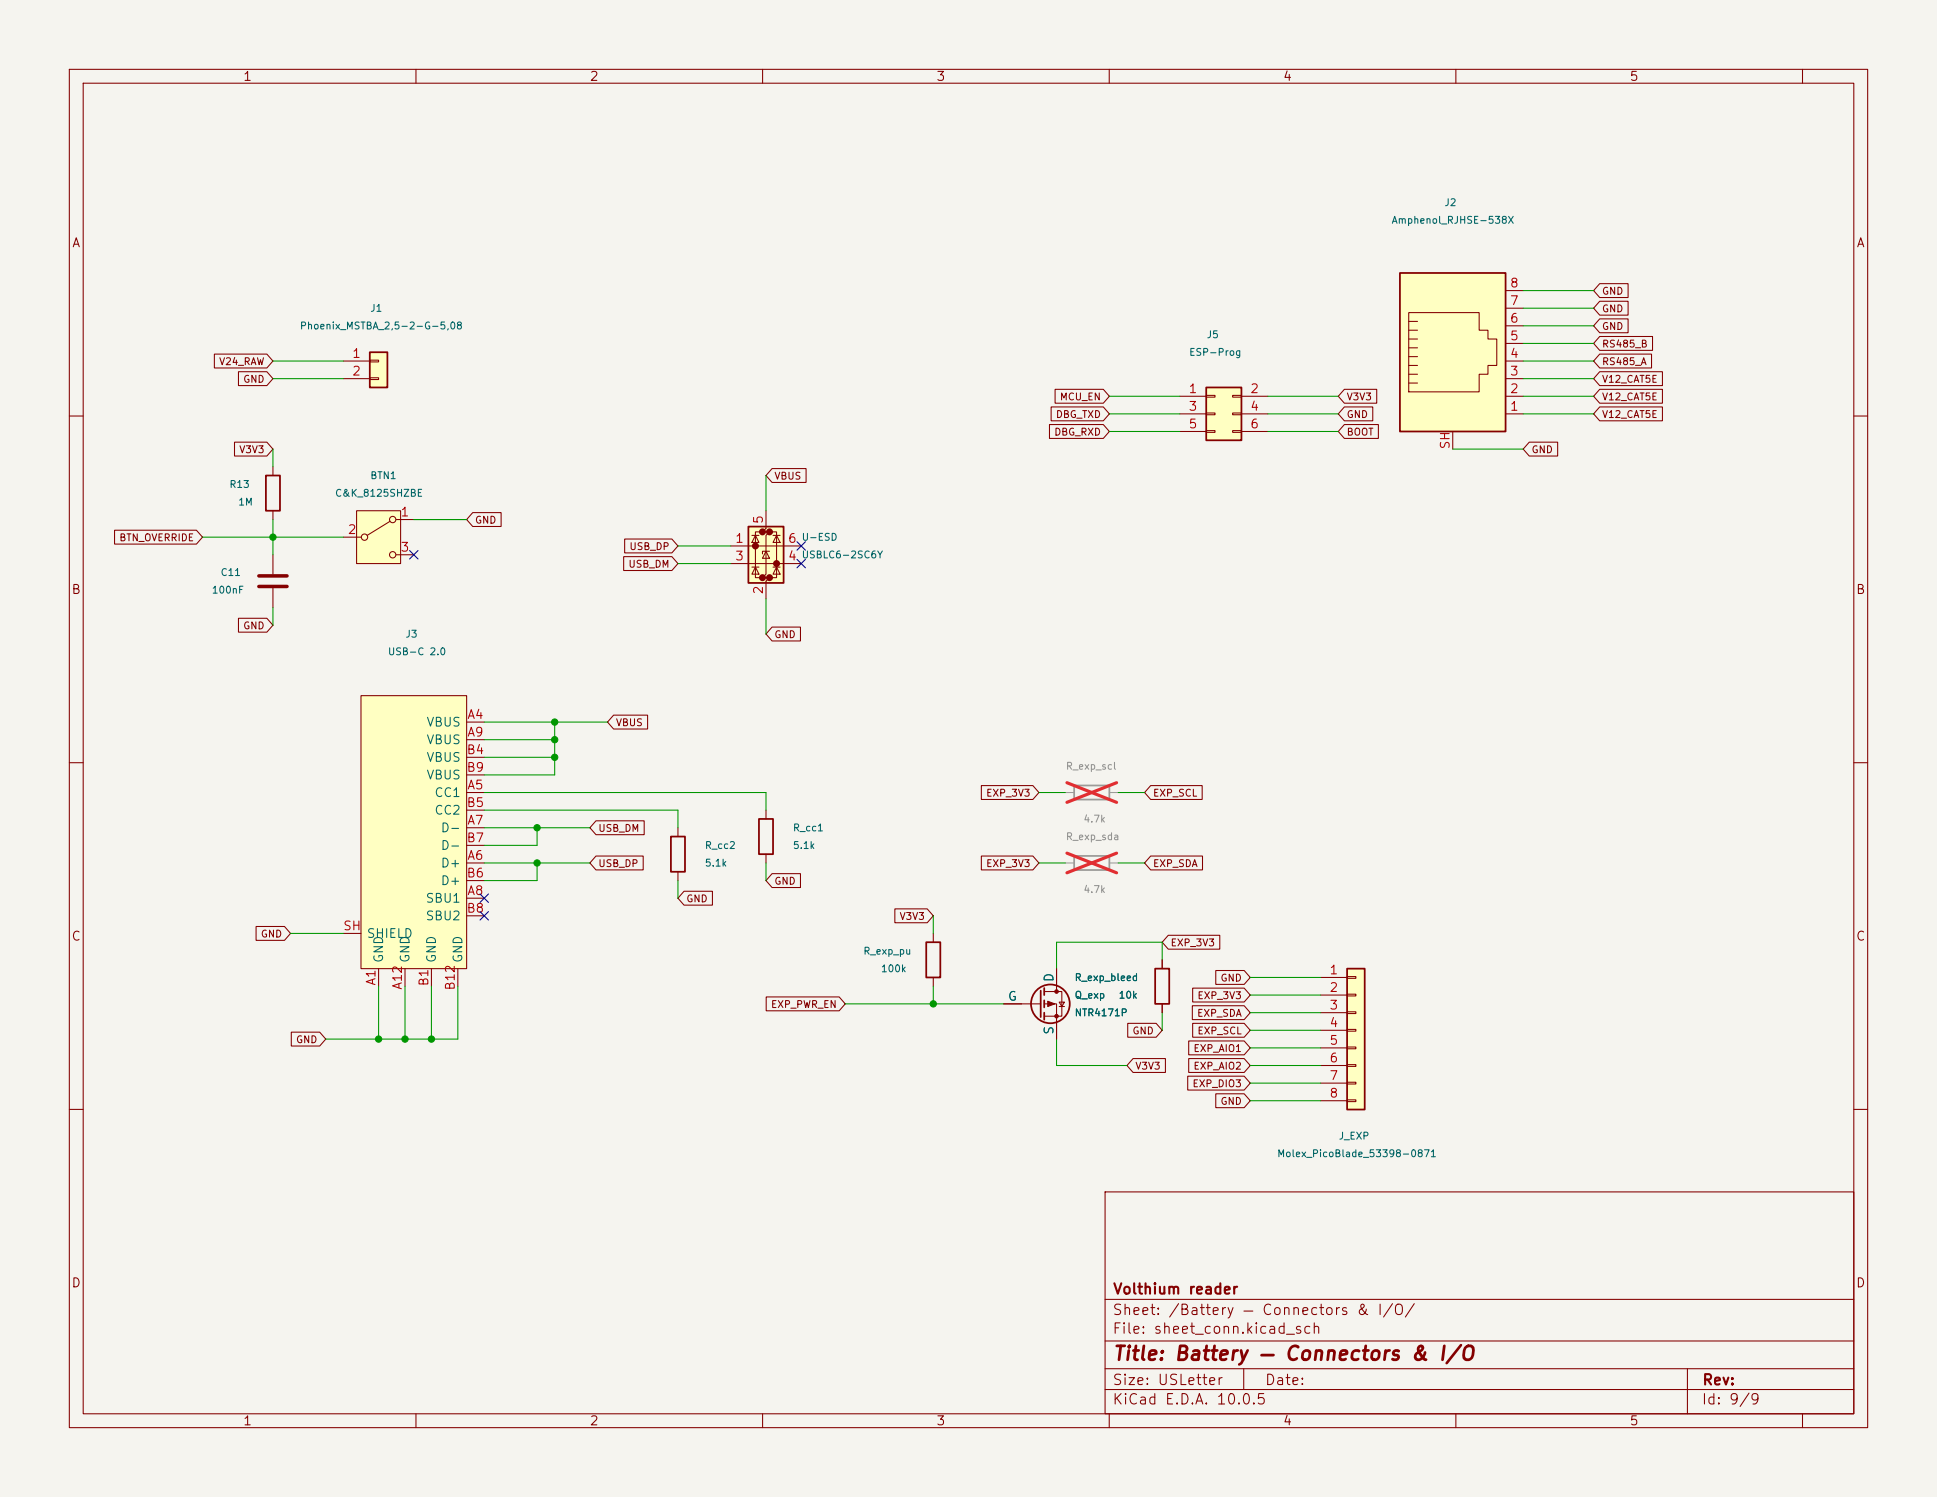
[picture p249: page 9]
