kaanow/volthium_reader/hardware/reviews/visual_inspections/cp_schematic_cleanup/iter49/snapshots/battery_side_schematic.pdf

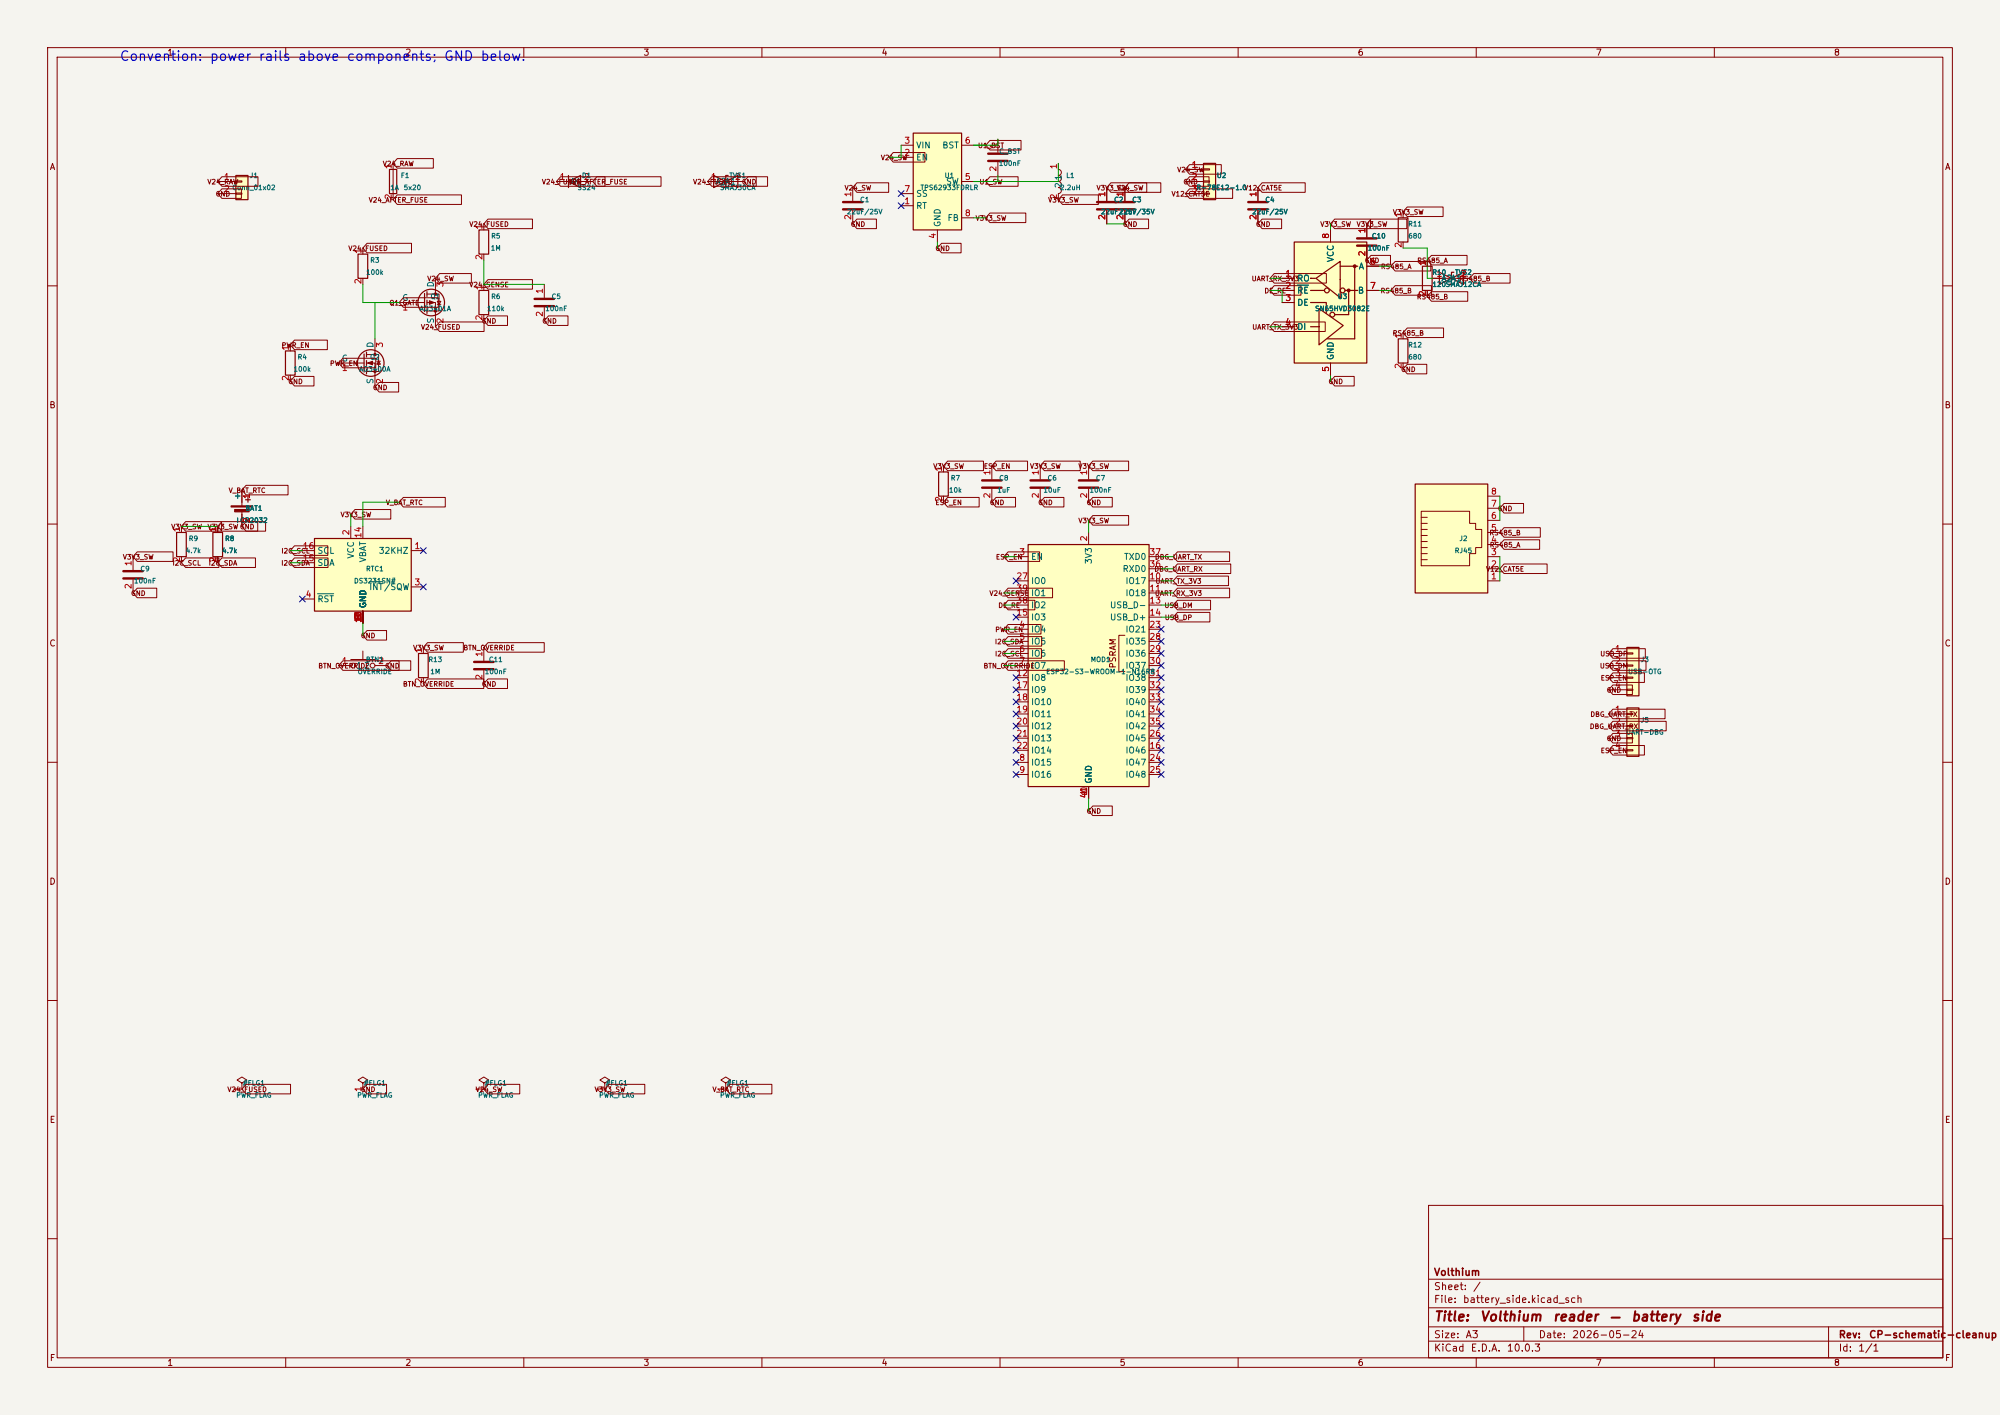
[picture p250: page 1]

Volthium
Sheet: /
File: battery_side.kicad_sch
Title: Volthium reader — battery side

F Date: 2026-05-24

KiCad E.D.A. 10.0.3 | Id: 1/1
