kaanow/volthium_reader/hardware/reviews/visual_inspections/cp_schematic_cleanup/iter49/snapshots/display_side_schematic.pdf

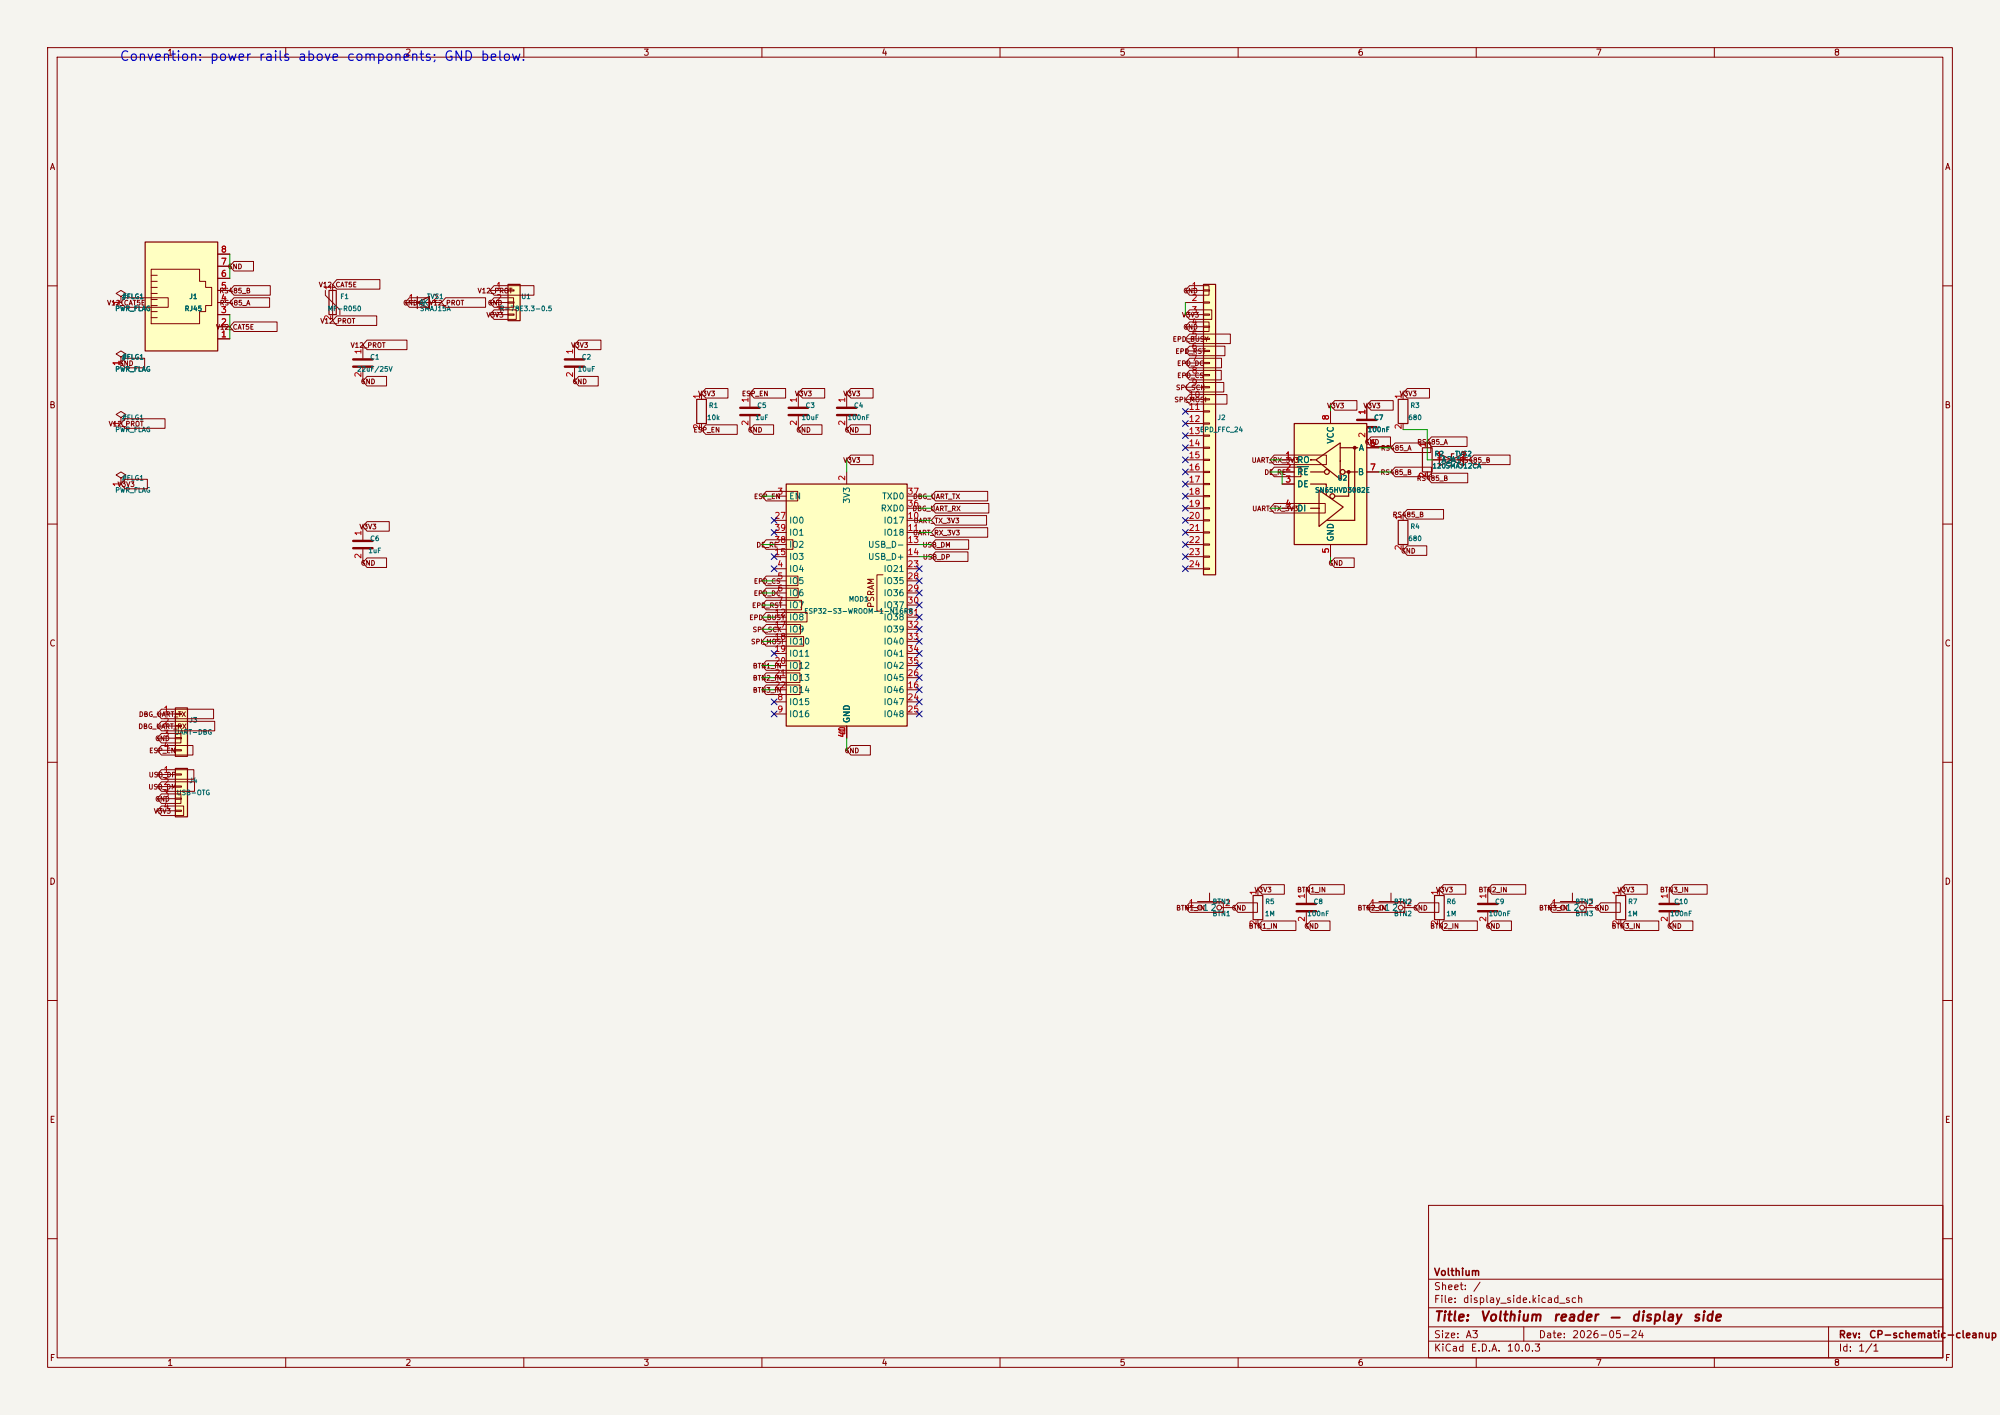
[picture p251: page 1]

Convention: power rails above components; GND below. #FLG1 PWR_FLAG 1

Volthium
Sheet: /
File: display_side.kicad_sch
Title: Volthium reader — display side

F Date: 2026-05-24

KiCad E.D.A. 10.0.3 | Id: 1/1
