kaanow/volthium_reader/hardware/reviews/visual_inspections/cp_schematic_cleanup/iter55/snapshots/display_side_schematic.pdf

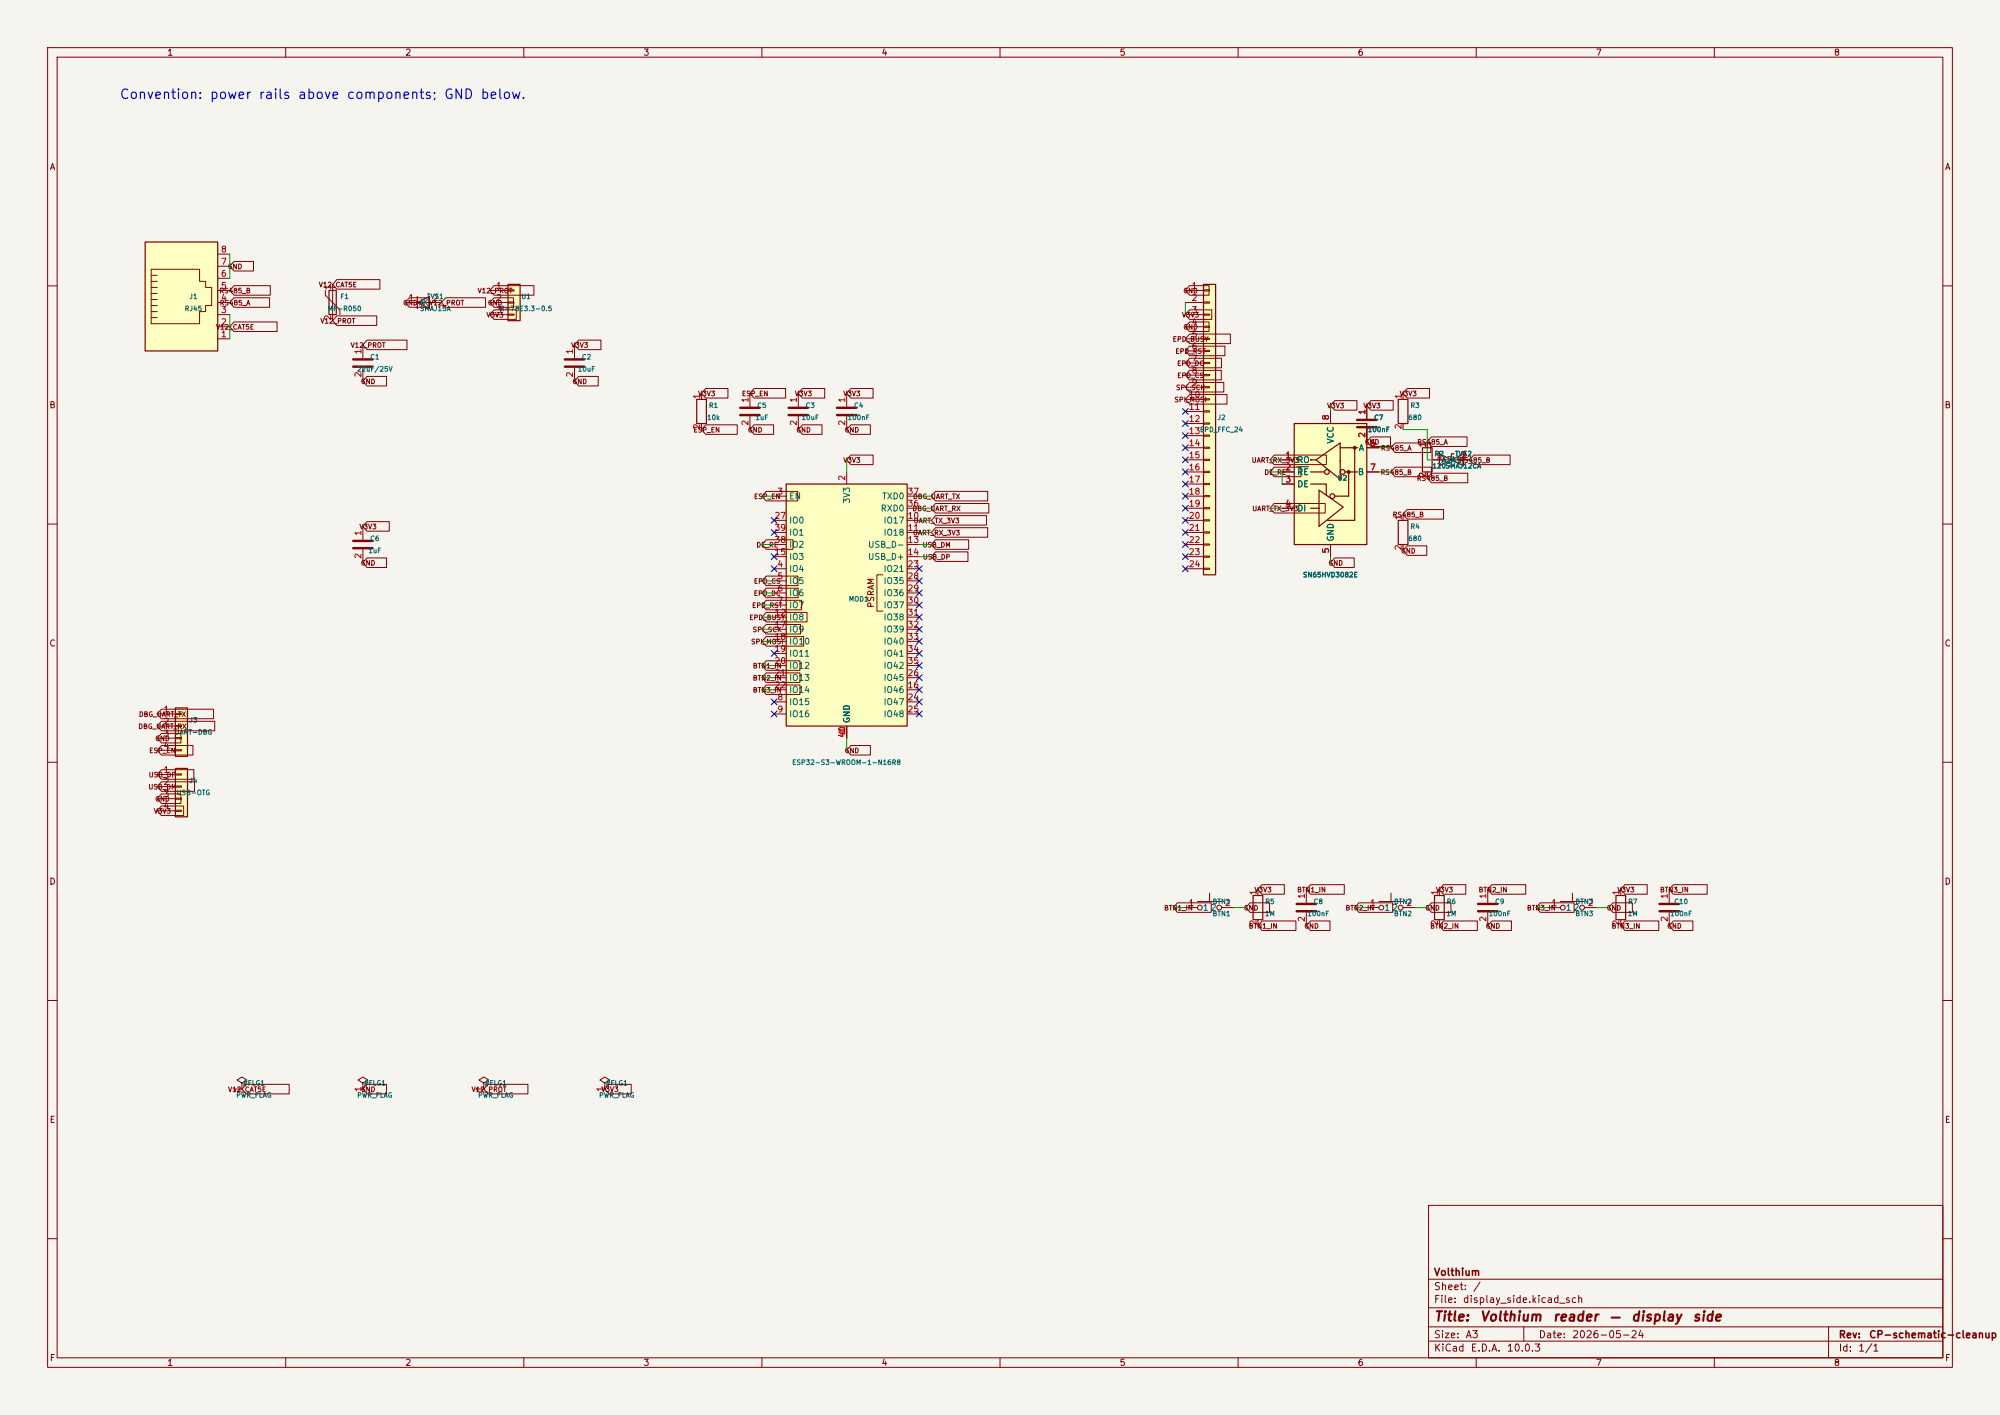
[picture p252: page 1]

EPD_RST SPI_MOSI Convention: power rails above components; GND below.

Volthium
Sheet: /
File: display_side.kicad_sch
Title: Volthium reader — display side

F Date: 2026-05-24

KiCad E.D.A. 10.0.3 | Id: 1/1
