kaanow/volthium_reader/hardware/reviews/visual_inspections/cp2-schematic/display-iter2/reviewer/g9/cp2-schematic/iter6/reviewer/snapshots/display_schematic.pdf

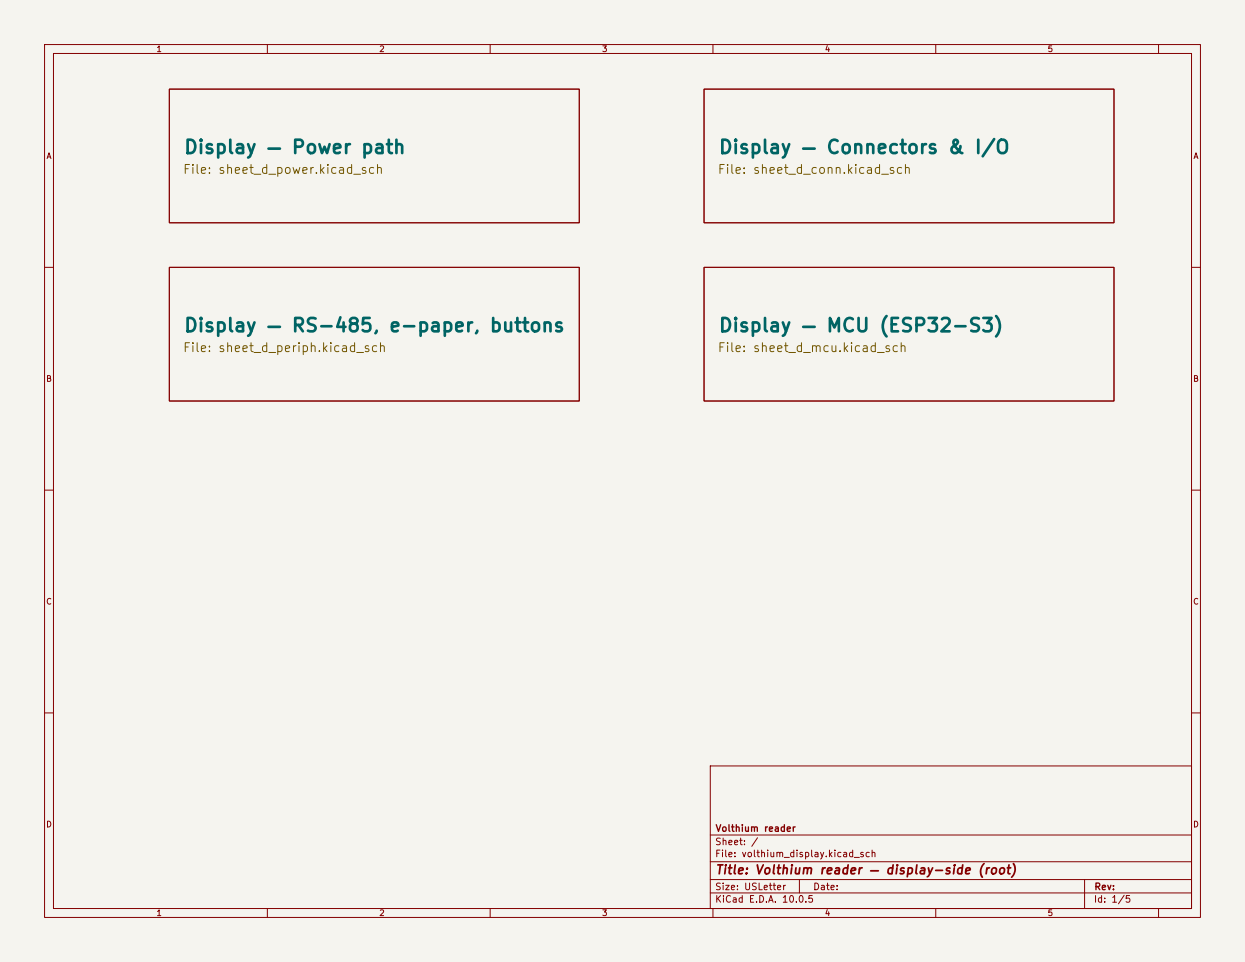
[picture p255: page 1]

Display — RS-485, e-paper, buttons

Volthium reader
Sheet: /
File: volthium_display.kicad_sch
Title: Volthium reader — display-side (root)

Size: USLetter | Rev:
KiCad E.D.A. 10.0.5 | Id: 1/5

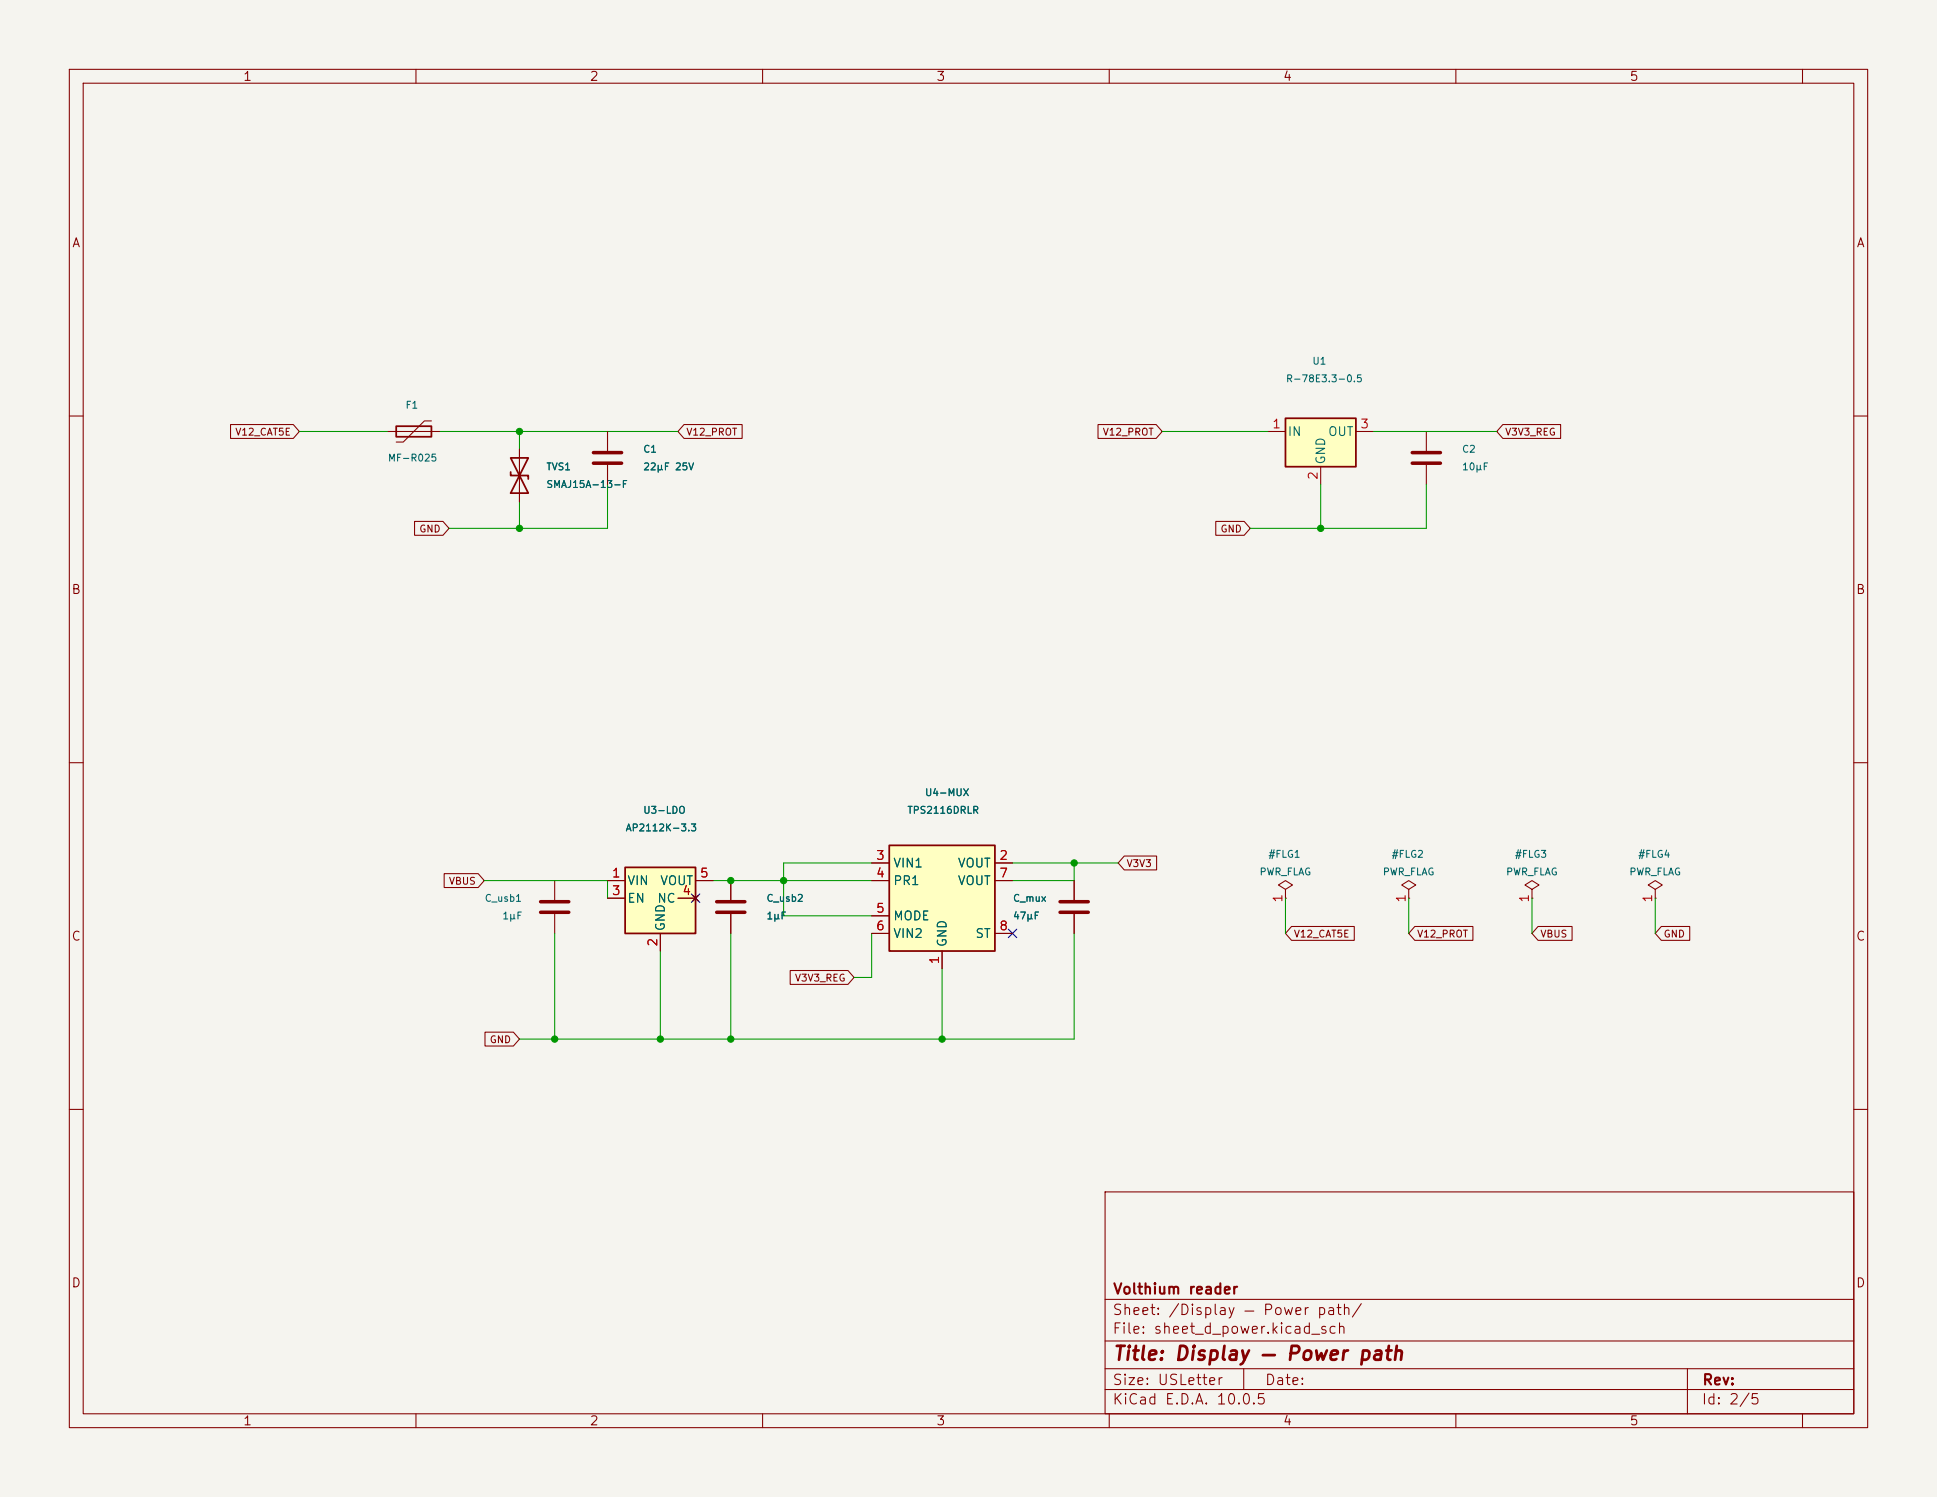
[picture p256: page 2]

Volthium reader
Sheet: /Display — Power path/
File: sheet_d_power.kicad_sch
Title: Display — Power path


Volthium reader
Sheet: /Display — RS-485, e-paper, buttons/
File: sheet_d_periph.kicad_sch
Title: Display — RS-485, e-paper, buttons
