kaanow/volthium_reader/hardware/kicad/schematic/build/sheet_conn.kicad_sch

## KiCad design hardware/kicad/schematic/build/sheet_conn.kicad_sch (2026-08-05)

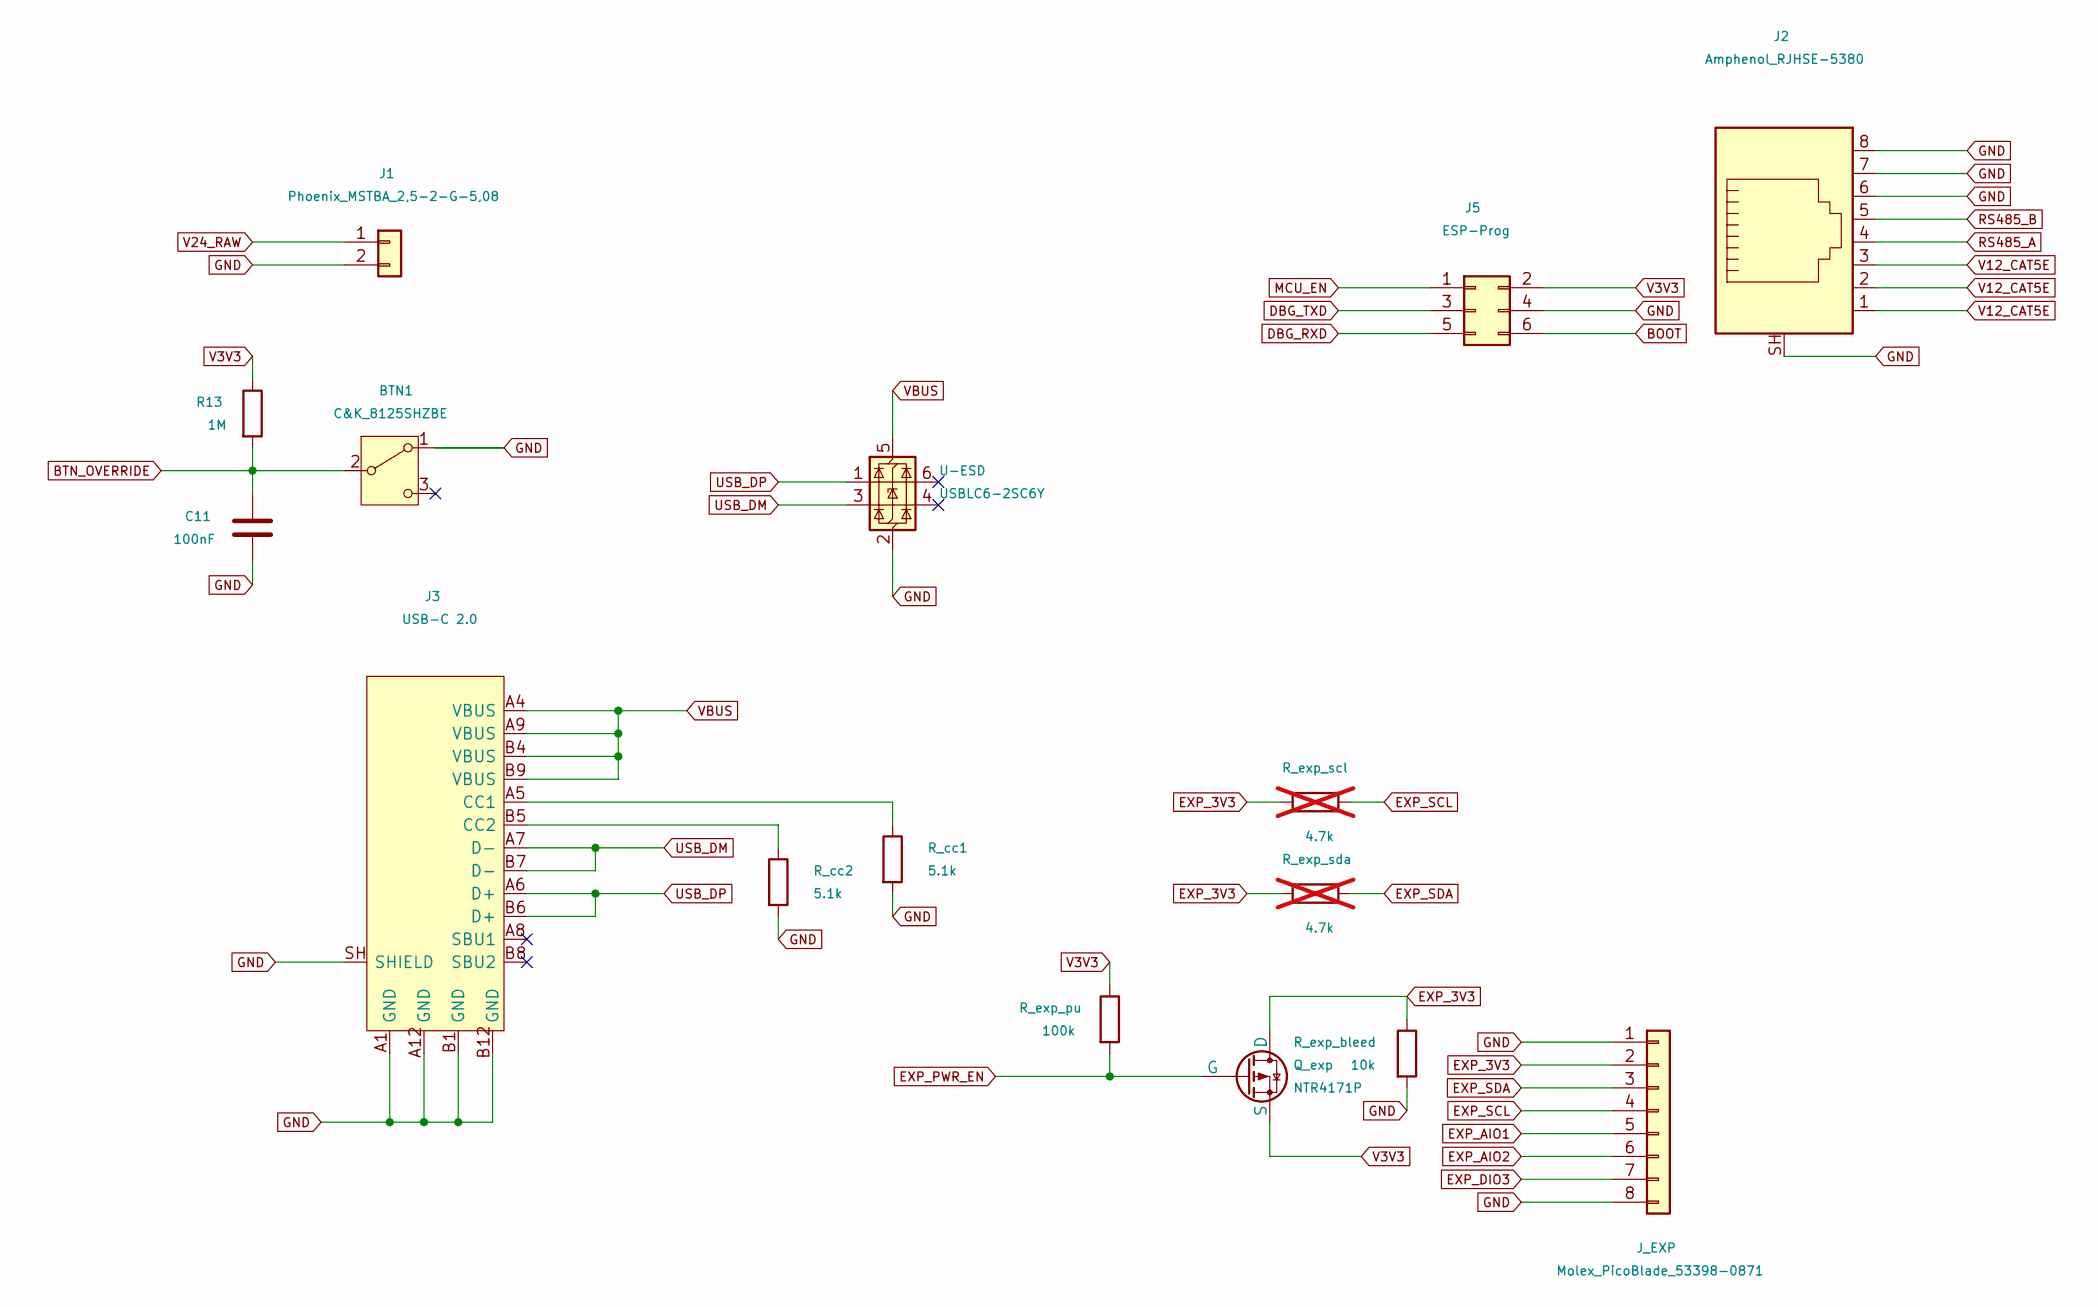
[picture p258: schematic sheet_conn.kicad_sch]

Parts:
BTN1: C&K_8125SHZBE; PinHeader_1x03_P2.54mm_Vertical
C11: 100nF; C_0603_1608Metric
J1: Phoenix_MSTBA_2,5-2-G-5,08; PhoenixContact_MSTBA_2,5_2-G-5,08_1x02_P5.08mm_Horizontal
J2: Amphenol_RJHSE-5380; RJ45_Amphenol_RJHSE5380
J3: USB-C 2.0; USB_C_Receptacle_GCT_USB4085
J5: ESP-Prog; IDC-Header_2x03_P2.54mm_Vertical
J_EXP: Molex_PicoBlade_53398-0871; Molex_PicoBlade_53398-0871_1x08-1MP_P1.25mm_Vertical
Q_exp: NTR4171P; SOT-23
R13: 1M; R_0805_2012Metric
R_cc1, R_cc2: 5.1k; R_0805_2012Metric
R_exp_bleed: 10k; R_0805_2012Metric
R_exp_pu: 100k; R_0805_2012Metric
R_exp_scl: 4.7k; R_0805_2012Metric; not fitted
R_exp_sda: 4.7k; R_0805_2012Metric; not fitted
U-ESD: USBLC6-2SC6Y; SOT-23-6

Connections:
BOOT: J5.6
BTN_OVERRIDE: BTN1.2, C11.1, R13.2
DBG_RXD: J5.5
DBG_TXD: J5.3
EXP_3V3: J_EXP.2, Q_exp.3 (D), R_exp_bleed.1, R_exp_scl.1, R_exp_sda.1
EXP_AIO1: J_EXP.5
EXP_AIO2: J_EXP.6
EXP_DIO3: J_EXP.7
EXP_PWR_EN: Q_exp.1 (G), R_exp_pu.2
EXP_SCL: J_EXP.4, R_exp_scl.2
EXP_SDA: J_EXP.3, R_exp_sda.2
GND: BTN1.1, C11.2, J1.2, J2.6, J2.7, J2.8, J2.SH, J3.A1 (GND), J3.A12 (GND), J3.B1 (GND), J3.B12 (GND), J3.SH (SHIELD), J5.4, J_EXP.1, J_EXP.8, R_cc1.2, R_cc2.2, R_exp_bleed.2, U-ESD.2
MCU_EN: J5.1
unnamed: J3.A5 (CC1), R_cc1.1
unnamed: J3.B5 (CC2), R_cc2.1
RS485_A: J2.4
RS485_B: J2.5
USB_DM: J3.A7 (D-), J3.B7 (D-), U-ESD.3
USB_DP: J3.A6 (D+), J3.B6 (D+), U-ESD.1
V3V3: J5.2, Q_exp.2 (S), R13.1, R_exp_pu.1
V12_CAT5E: J2.1, J2.2, J2.3
V24_RAW: J1.1
VBUS: J3.A4 (VBUS), J3.A9 (VBUS), J3.B4 (VBUS), J3.B9 (VBUS), U-ESD.5
