kaanow/volthium_reader/hardware/kicad/schematic/build/sheet_isors485_1.kicad_sch

## KiCad design hardware/kicad/schematic/build/sheet_isors485_1.kicad_sch (2026-08-05)

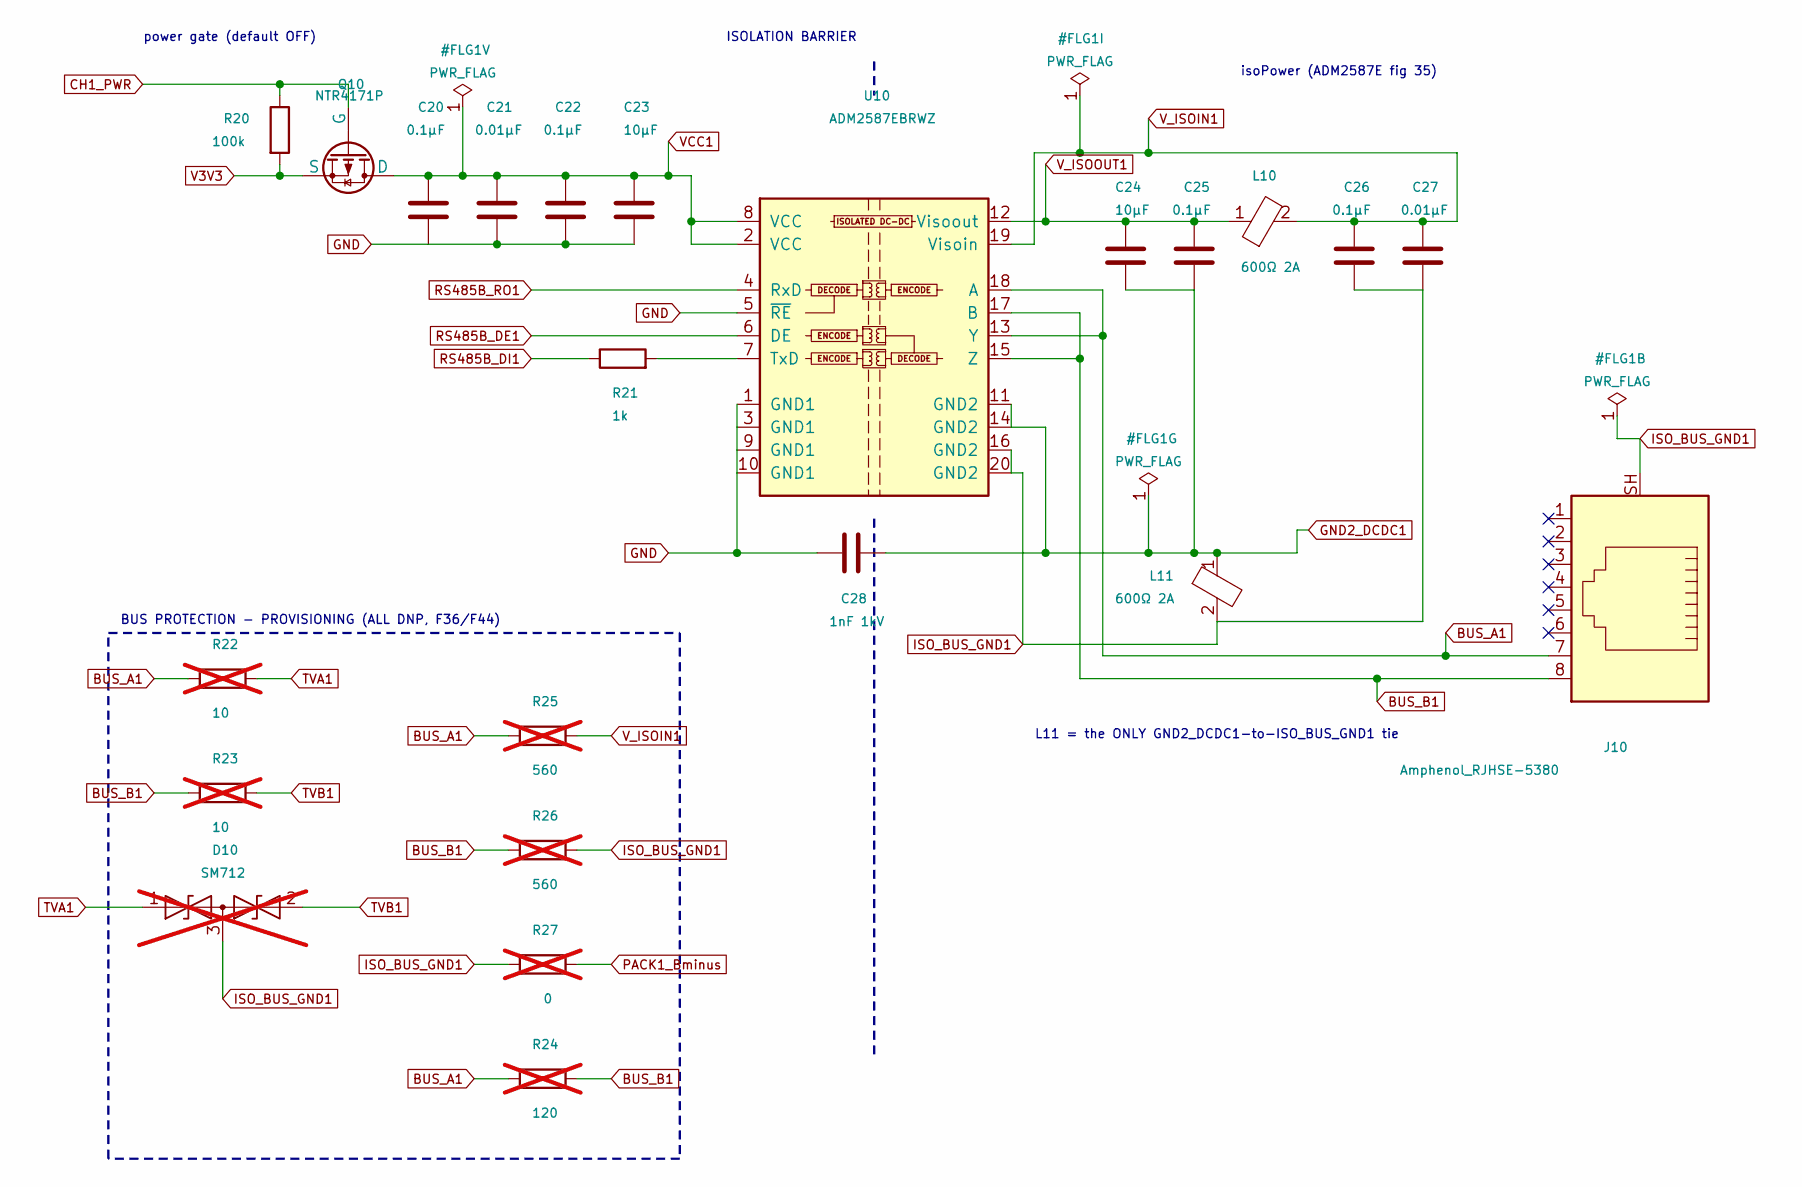
[picture p259: schematic sheet_isors485_1.kicad_sch]

Parts:
C20, C22, C25, C26: 0.1µF; C_0603_1608Metric
C21: 0.01µF; C_0603_1608Metric
C23, C24: 10µF; C_0805_2012Metric
C27: 0.01µF; C_0402_1005Metric
C28: 1nF 1kV; C_1206_3216Metric
D10: SM712; SOT-23; not fitted
J10: Amphenol_RJHSE-5380; RJ45_Amphenol_RJHSE5380
L10, L11: 600Ω 2A; L_0805_2012Metric
Q10: NTR4171P; SOT-23
R20: 100k; R_0805_2012Metric
R21: 1k; R_0603_1608Metric
R22, R23: 10; R_0603_1608Metric; not fitted
R24: 120; R_0805_2012Metric; not fitted
R25, R26: 560; R_0603_1608Metric; not fitted
R27: 0; R_0805_2012Metric; not fitted
U10: ADM2587EBRWZ; SOIC-20W_7.5x12.8mm_P1.27mm

Connections:
BUS_A1: J10.7, R22.1, R24.1, R25.1, U10.13 (Y), U10.18 (A)
BUS_B1: J10.8, R23.1, R24.2, R26.1, U10.15 (Z), U10.17 (B)
CH1_PWR: Q10.1 (G), R20.1
GND: C20.2, C21.2, C22.2, C23.2, C28.1, U10.1 (GND1), U10.3 (GND1), U10.5 (~RE), U10.9 (GND1), U10.10 (GND1)
GND2_DCDC1: C24.2, C25.2, C28.2, L11.1, U10.11 (GND2), U10.14 (GND2)
ISO_BUS_GND1: C26.2, C27.2, D10.3, J10.SH, L11.2, R26.2, R27.1, U10.16 (GND2), U10.20 (GND2)
unnamed: R21.2, U10.7 (TxD)
PACK1_Bminus: R27.2
RS485B_DE1: U10.6 (DE)
RS485B_DI1: R21.1
RS485B_RO1: U10.4 (RxD)
TVA1: D10.1, R22.2
TVB1: D10.2, R23.2
V3V3: Q10.2 (S), R20.2
VCC1: C20.1, C21.1, C22.1, C23.1, Q10.3 (D), U10.2 (VCC), U10.8 (VCC)
V_ISOIN1: C26.1, C27.1, L10.2, R25.2, U10.19 (Visoin)
V_ISOOUT1: C24.1, C25.1, L10.1, U10.12 (Visoout)

Notes on the sheet:
power gate (default OFF)
isoPower (ADM2587E fig 35)
L11 = the ONLY GND2_DCDC1-to-ISO_BUS_GND1 tie
ISOLATION BARRIER
BUS PROTECTION - PROVISIONING (ALL DNP, F36/F44)
