kaanow/volthium_reader/hardware/kicad/schematic/build/sheet_isors485_2.kicad_sch

## KiCad design hardware/kicad/schematic/build/sheet_isors485_2.kicad_sch (2026-08-05)

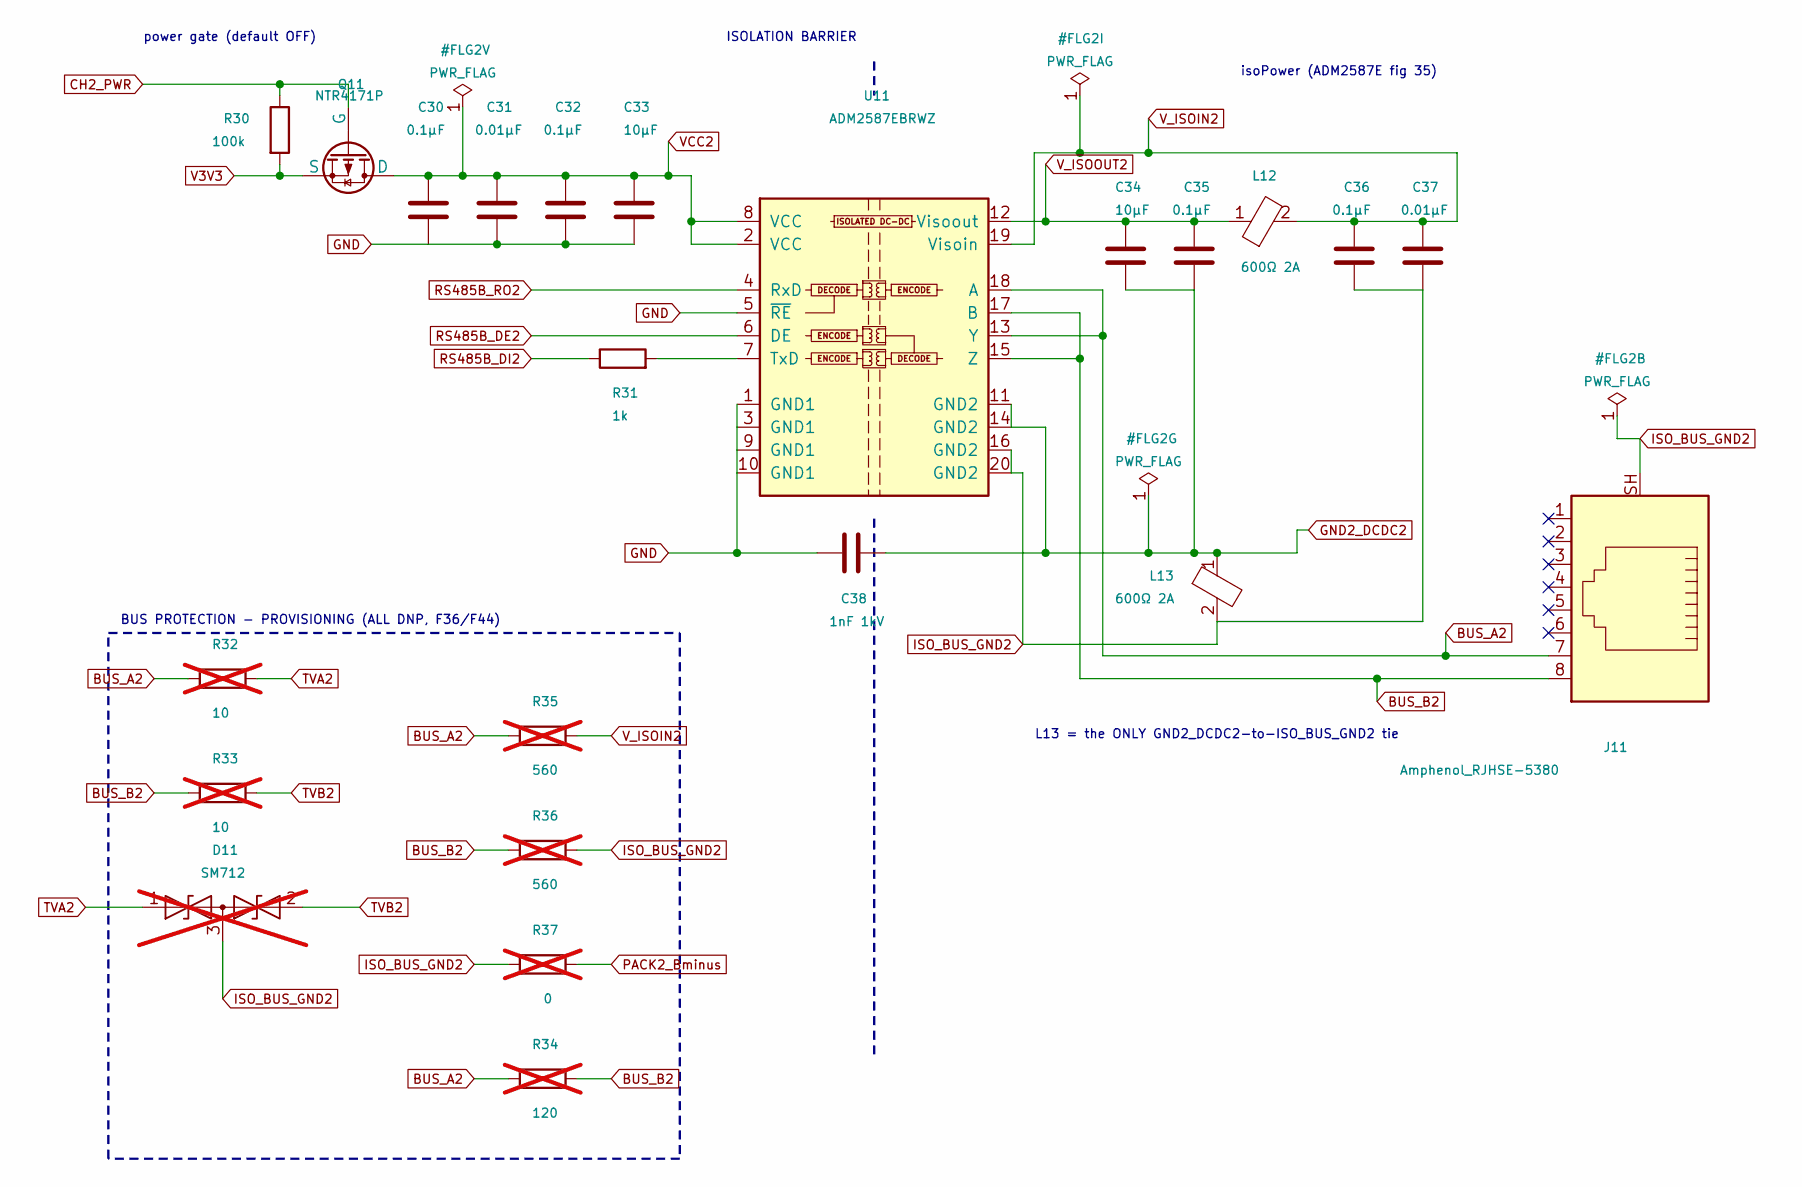
[picture p260: schematic sheet_isors485_2.kicad_sch]

Parts:
C30, C32, C35, C36: 0.1µF; C_0603_1608Metric
C31: 0.01µF; C_0603_1608Metric
C33, C34: 10µF; C_0805_2012Metric
C37: 0.01µF; C_0402_1005Metric
C38: 1nF 1kV; C_1206_3216Metric
D11: SM712; SOT-23; not fitted
J11: Amphenol_RJHSE-5380; RJ45_Amphenol_RJHSE5380
L12, L13: 600Ω 2A; L_0805_2012Metric
Q11: NTR4171P; SOT-23
R30: 100k; R_0805_2012Metric
R31: 1k; R_0603_1608Metric
R32, R33: 10; R_0603_1608Metric; not fitted
R34: 120; R_0805_2012Metric; not fitted
R35, R36: 560; R_0603_1608Metric; not fitted
R37: 0; R_0805_2012Metric; not fitted
U11: ADM2587EBRWZ; SOIC-20W_7.5x12.8mm_P1.27mm

Connections:
BUS_A2: J11.7, R32.1, R34.1, R35.1, U11.13 (Y), U11.18 (A)
BUS_B2: J11.8, R33.1, R34.2, R36.1, U11.15 (Z), U11.17 (B)
CH2_PWR: Q11.1 (G), R30.1
GND: C30.2, C31.2, C32.2, C33.2, C38.1, U11.1 (GND1), U11.3 (GND1), U11.5 (~RE), U11.9 (GND1), U11.10 (GND1)
GND2_DCDC2: C34.2, C35.2, C38.2, L13.1, U11.11 (GND2), U11.14 (GND2)
ISO_BUS_GND2: C36.2, C37.2, D11.3, J11.SH, L13.2, R36.2, R37.1, U11.16 (GND2), U11.20 (GND2)
unnamed: R31.2, U11.7 (TxD)
PACK2_Bminus: R37.2
RS485B_DE2: U11.6 (DE)
RS485B_DI2: R31.1
RS485B_RO2: U11.4 (RxD)
TVA2: D11.1, R32.2
TVB2: D11.2, R33.2
V3V3: Q11.2 (S), R30.2
VCC2: C30.1, C31.1, C32.1, C33.1, Q11.3 (D), U11.2 (VCC), U11.8 (VCC)
V_ISOIN2: C36.1, C37.1, L12.2, R35.2, U11.19 (Visoin)
V_ISOOUT2: C34.1, C35.1, L12.1, U11.12 (Visoout)

Notes on the sheet:
power gate (default OFF)
isoPower (ADM2587E fig 35)
L13 = the ONLY GND2_DCDC2-to-ISO_BUS_GND2 tie
ISOLATION BARRIER
BUS PROTECTION - PROVISIONING (ALL DNP, F36/F44)
