kaanow/volthium_reader/hardware/kicad/schematic/build/sheet_mcu.kicad_sch

## KiCad design hardware/kicad/schematic/build/sheet_mcu.kicad_sch (2026-08-05)

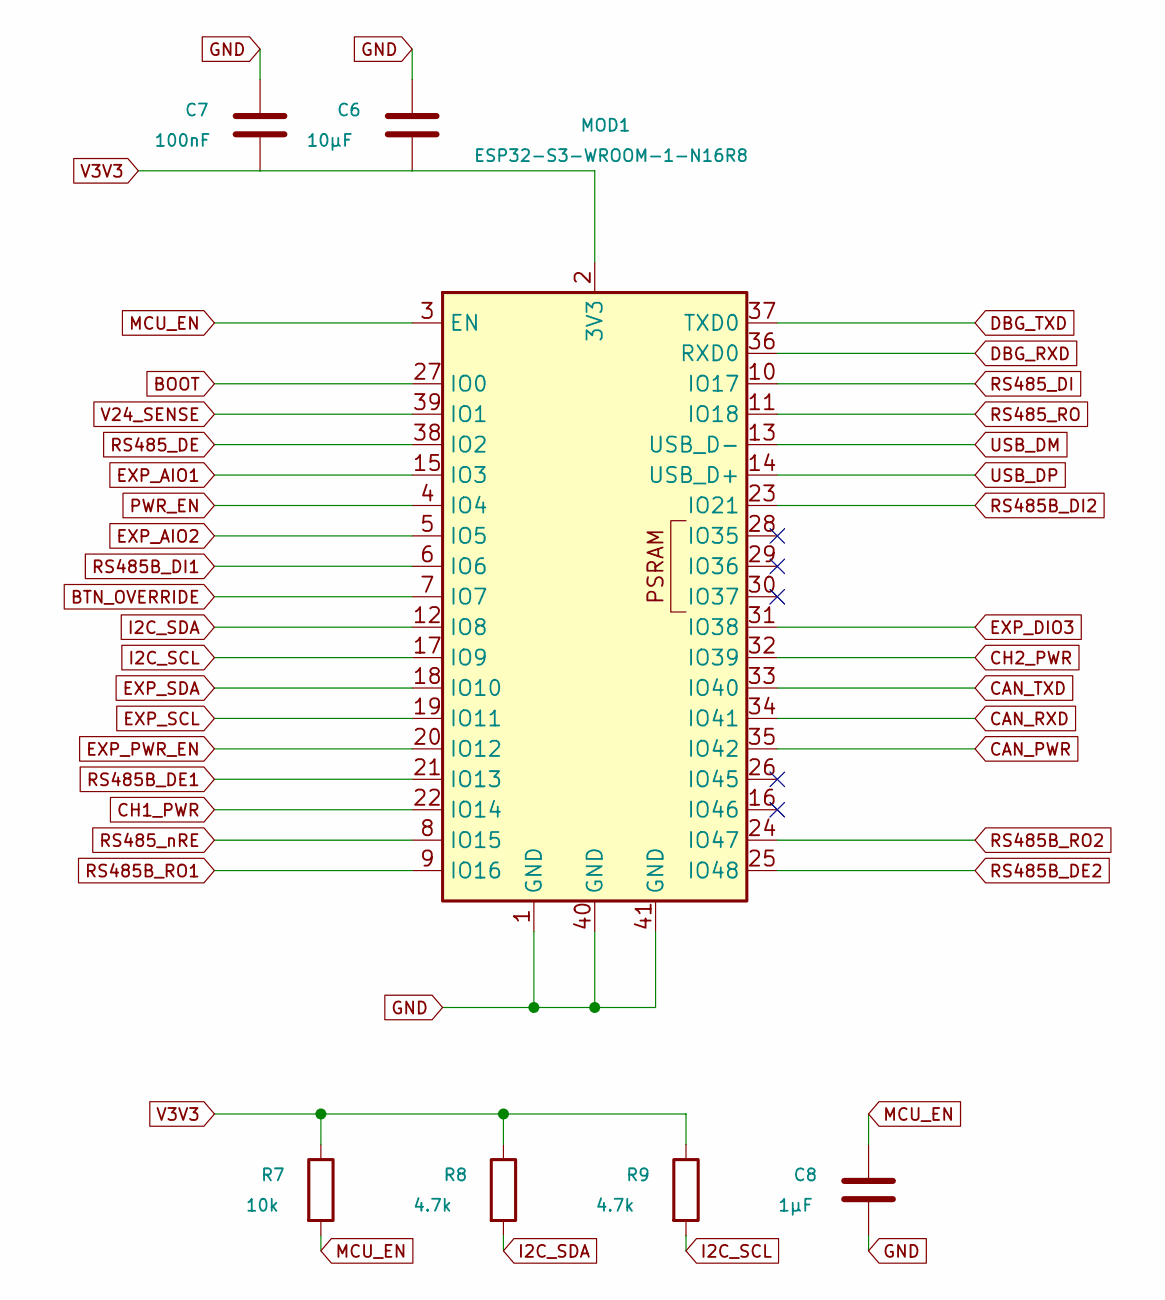
[picture p261: schematic sheet_mcu.kicad_sch]

Parts:
C6: 10µF; C_0805_2012Metric
C7: 100nF; C_0805_2012Metric
C8: 1µF; C_0603_1608Metric
MOD1: ESP32-S3-WROOM-1-N16R8; ESP32-S3-WROOM-1_HSvia0.3
R7: 10k; R_0805_2012Metric
R8, R9: 4.7k; R_0805_2012Metric

Connections:
BOOT: MOD1.27 (IO0)
BTN_OVERRIDE: MOD1.7 (IO7)
CAN_PWR: MOD1.35 (IO42)
CAN_RXD: MOD1.34 (IO41)
CAN_TXD: MOD1.33 (IO40)
CH1_PWR: MOD1.22 (IO14)
CH2_PWR: MOD1.32 (IO39)
DBG_RXD: MOD1.36 (RXD0)
DBG_TXD: MOD1.37 (TXD0)
EXP_AIO1: MOD1.15 (IO3)
EXP_AIO2: MOD1.5 (IO5)
EXP_DIO3: MOD1.31 (IO38)
EXP_PWR_EN: MOD1.20 (IO12)
EXP_SCL: MOD1.19 (IO11)
EXP_SDA: MOD1.18 (IO10)
GND: C6.1, C7.1, C8.2, MOD1.1 (GND), MOD1.40 (GND), MOD1.41 (GND)
I2C_SCL: MOD1.17 (IO9), R9.2
I2C_SDA: MOD1.12 (IO8), R8.2
MCU_EN: C8.1, MOD1.3 (EN), R7.2
PWR_EN: MOD1.4 (IO4)
RS485B_DE1: MOD1.21 (IO13)
RS485B_DE2: MOD1.25 (IO48)
RS485B_DI1: MOD1.6 (IO6)
RS485B_DI2: MOD1.23 (IO21)
RS485B_RO1: MOD1.9 (IO16)
RS485B_RO2: MOD1.24 (IO47)
RS485_DE: MOD1.38 (IO2)
RS485_DI: MOD1.10 (IO17)
RS485_RO: MOD1.11 (IO18)
RS485_nRE: MOD1.8 (IO15)
USB_DM: MOD1.13 (USB_D-)
USB_DP: MOD1.14 (USB_D+)
V3V3: C6.2, C7.2, MOD1.2 (3V3), R7.1, R8.1, R9.1
V24_SENSE: MOD1.39 (IO1)
