kaanow/volthium_reader/hardware/kicad/schematic/build/sheet_periph.kicad_sch

## KiCad design hardware/kicad/schematic/build/sheet_periph.kicad_sch (2026-08-05)

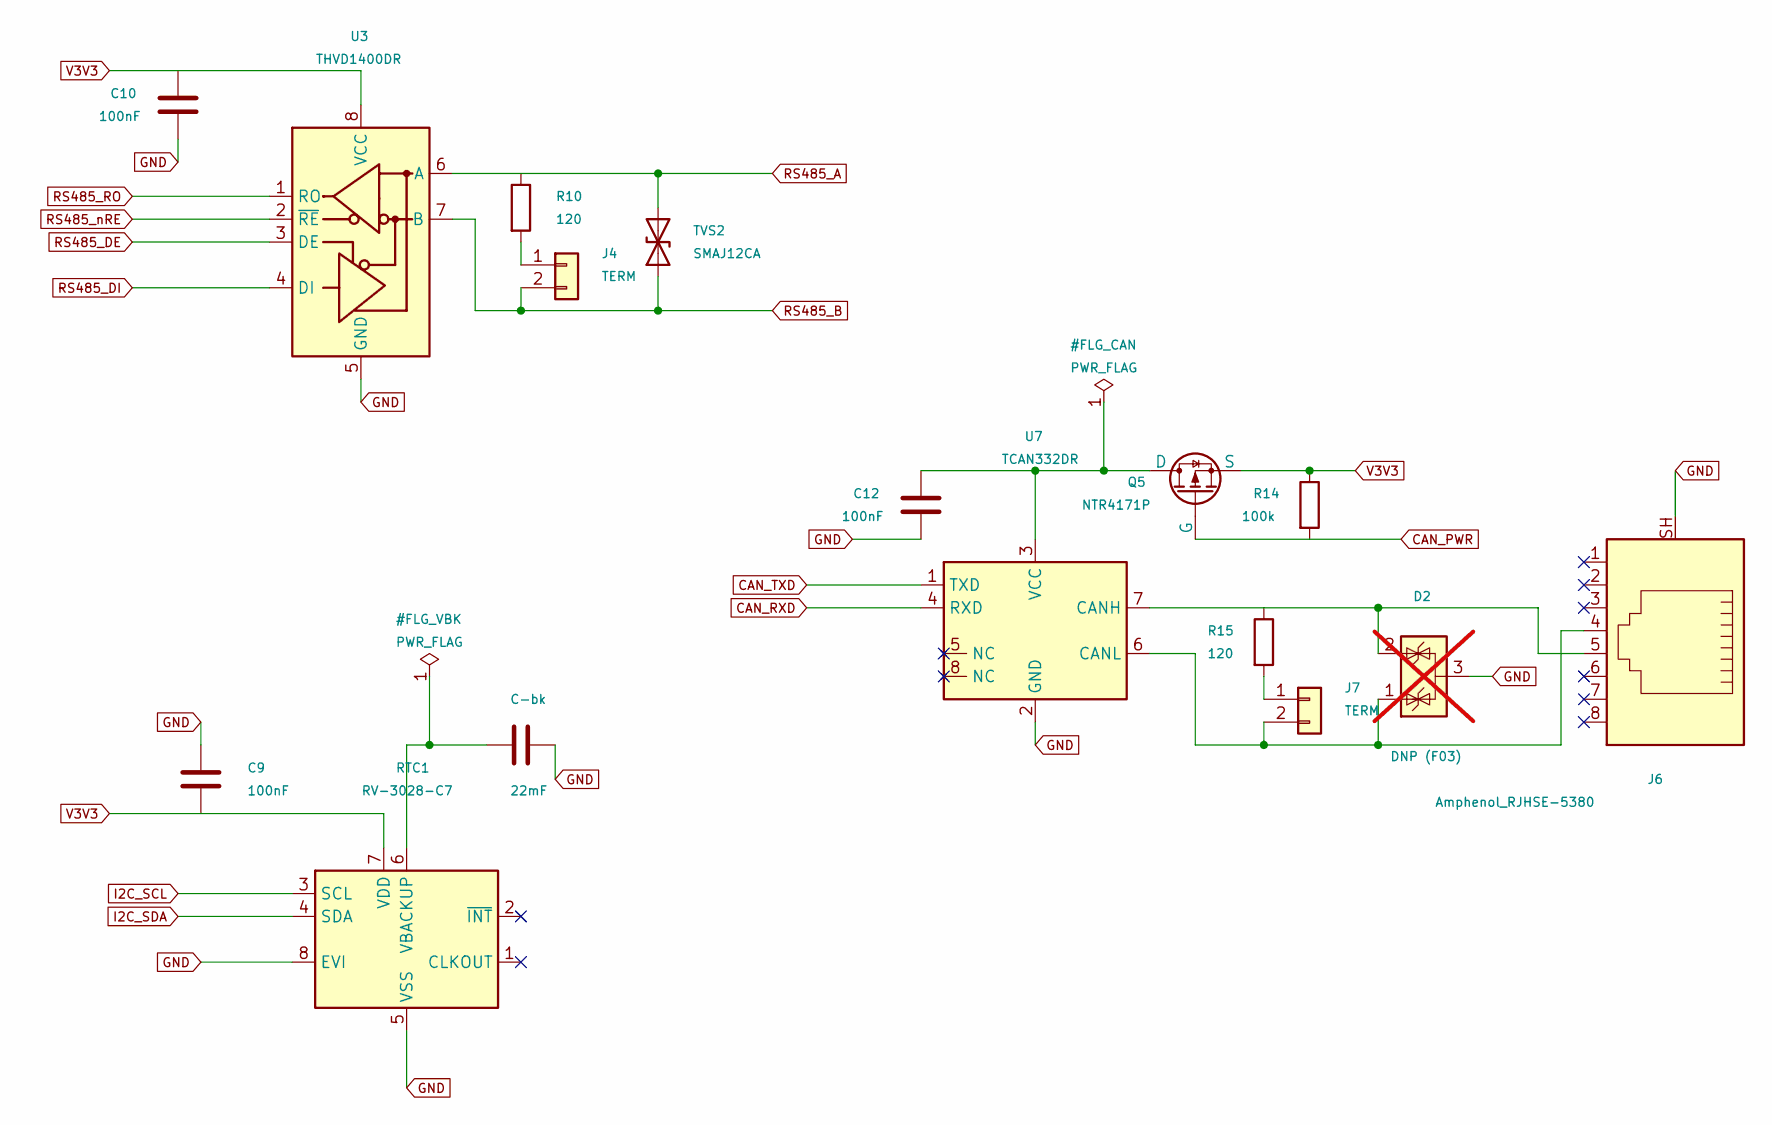
[picture p262: schematic sheet_periph.kicad_sch]

Parts:
C9, C10, C12: 100nF; C_0603_1608Metric
C-bk: 22mF; C_1210_3225Metric
D2: DNP (F03); SOT-23; not fitted
J4, J7: TERM; PinHeader_1x02_P2.54mm_Vertical
J6: Amphenol_RJHSE-5380; RJ45_Amphenol_RJHSE5380
Q5: NTR4171P; SOT-23
R10, R15: 120; R_0805_2012Metric
R14: 100k; R_0805_2012Metric
RTC1: RV-3028-C7; MicroCrystal_C7_SON-8_1.5x3.2mm_P0.9mm
TVS2: SMAJ12CA; D_SMA
U3: THVD1400DR; SOIC-8_3.9x4.9mm_P1.27mm
U7: TCAN332DR; SOIC-8_3.9x4.9mm_P1.27mm

Connections:
CAN_PWR: Q5.1 (G), R14.2
CAN_RXD: U7.4 (RXD)
CAN_TXD: U7.1 (TXD)
GND: C9.1, C10.2, C12.2, C-bk.2, D2.3, J6.SH, RTC1.5 (VSS), RTC1.8 (EVI), U3.5 (GND), U7.2 (GND)
I2C_SCL: RTC1.3 (SCL)
I2C_SDA: RTC1.4 (SDA)
unnamed: C12.1, Q5.3 (D), U7.3 (VCC)
unnamed: C-bk.1, RTC1.6 (VBACKUP)
unnamed: D2.1, J6.4, J7.2, U7.6 (CANL)
unnamed: D2.2, J6.5, R15.1, U7.7 (CANH)
unnamed: J4.1, R10.2
unnamed: J7.1, R15.2
RS485_A: R10.1, TVS2.2 (A2), U3.6 (A)
RS485_B: J4.2, TVS2.1 (A1), U3.7 (B)
RS485_DE: U3.3 (DE)
RS485_DI: U3.4 (DI)
RS485_RO: U3.1 (RO)
RS485_nRE: U3.2 (~RE)
V3V3: C9.2, C10.1, Q5.2 (S), R14.1, RTC1.7 (VDD), U3.8 (VCC)
