kaanow/volthium_reader/hardware/kicad/schematic/build/sheet_power.kicad_sch

## KiCad design hardware/kicad/schematic/build/sheet_power.kicad_sch (2026-08-05)

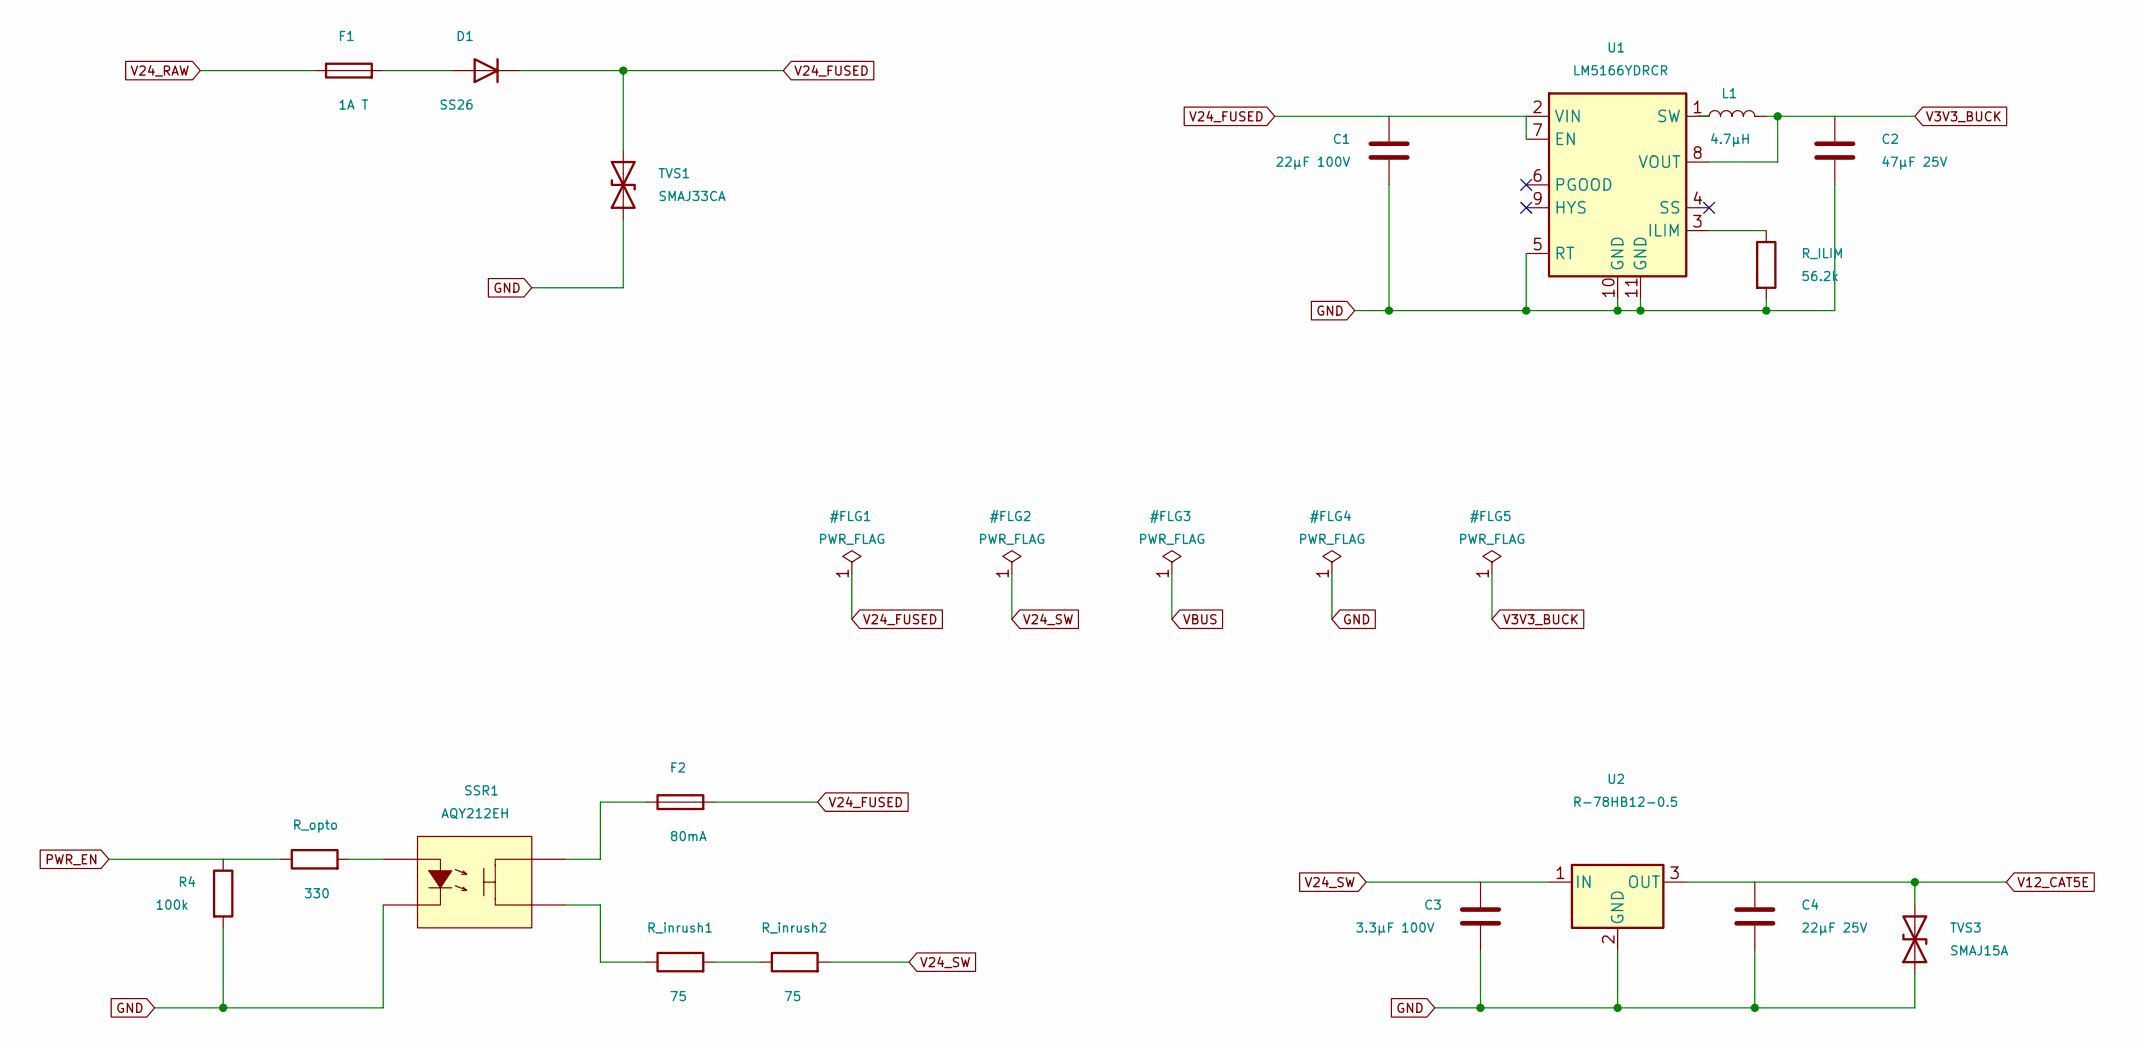
[picture p263: schematic sheet_power.kicad_sch]

Parts:
C1: 22µF 100V; C_1210_3225Metric
C2: 47µF 25V; C_1210_3225Metric
C3: 3.3µF 100V; C_1210_3225Metric
C4: 22µF 25V; C_1210_3225Metric
D1: SS26; D_SMA
F1: 1A T; Fuseholder_Clip-5x20mm_Keystone_3517_Inline_P23.11x6.76mm_D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
F2: 80mA; Fuse_Littelfuse-NANO2-451_453
L1: 4.7µH; L_1210_3225Metric
R4: 100k; R_0805_2012Metric
R_ILIM: 56.2k; R_0805_2012Metric
R_inrush1, R_inrush2: 75; R_1206_3216Metric
R_opto: 330; R_0805_2012Metric
SSR1: AQY212EH; DIP-4_W7.62mm
TVS1: SMAJ33CA; D_SMA
TVS3: SMAJ15A; D_SMA
U1: LM5166YDRCR; Texas_S-PVSON-N10_ThermalVias
U2: R-78HB12-0.5; Converter_DCDC_RECOM_R-78E-0.5_THT

Connections:
GND: C1.2, C2.2, C3.2, C4.2, R4.2, R_ILIM.2, SSR1.2 (K), TVS1.1 (A1), TVS3.1 (A1), U1.5 (RT), U1.10 (GND), U1.11 (GND), U2.2 (GND)
unnamed: D1.2 (A), F1.2
unnamed: F2.1, SSR1.4
unnamed: L1.1, U1.1 (SW)
unnamed: R_ILIM.1, U1.3 (ILIM)
unnamed: R_inrush1.1, SSR1.3
unnamed: R_inrush1.2, R_inrush2.1
unnamed: R_opto.2, SSR1.1 (A)
PWR_EN: R4.1, R_opto.1
V3V3_BUCK: C2.1, L1.2, U1.8 (VOUT)
V12_CAT5E: C4.1, TVS3.2 (A2), U2.3 (OUT)
V24_FUSED: C1.1, D1.1 (K), F2.2, TVS1.2 (A2), U1.2 (VIN), U1.7 (EN)
V24_RAW: F1.1
V24_SW: C3.1, R_inrush2.2, U2.1 (IN)
