kaanow/volthium_reader/hardware/kicad/schematic/build/sheet_super.kicad_sch

## KiCad design hardware/kicad/schematic/build/sheet_super.kicad_sch (2026-08-05)

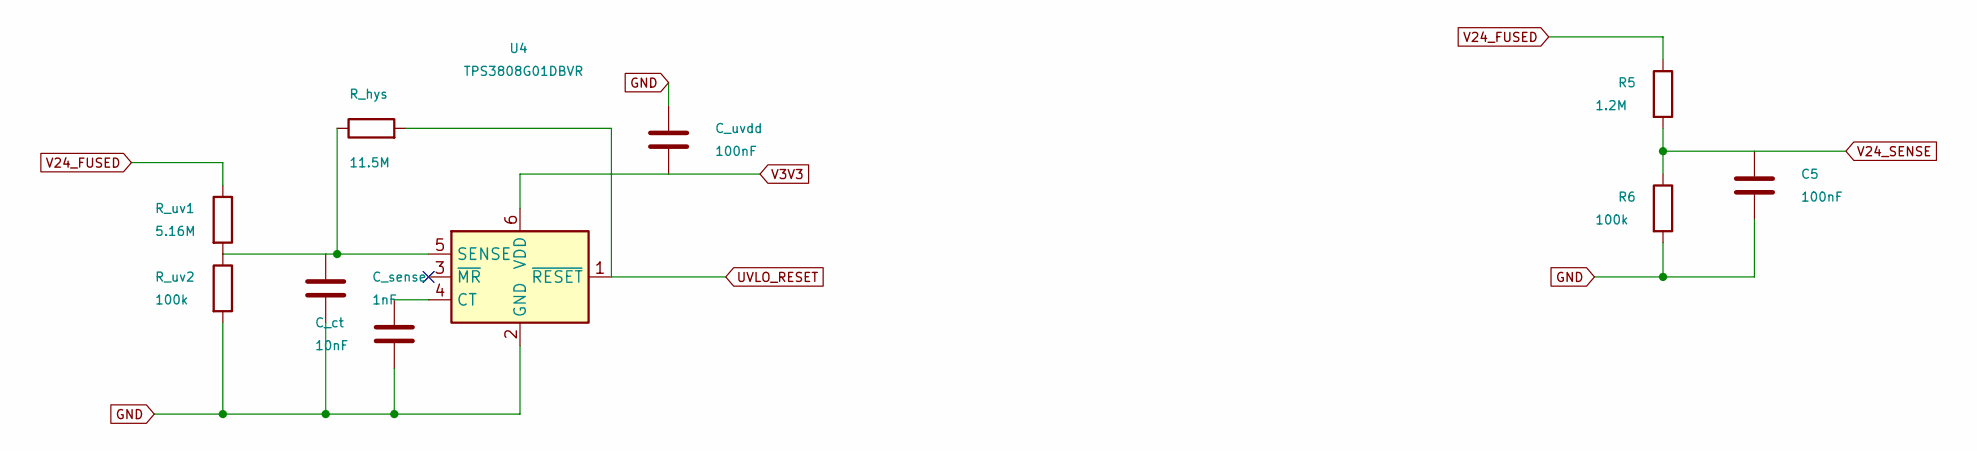
[picture p264: schematic sheet_super.kicad_sch]

Parts:
C5: 100nF; C_0603_1608Metric
C_ct: 10nF; C_0603_1608Metric
C_sense: 1nF; C_0603_1608Metric
C_uvdd: 100nF; C_0603_1608Metric
R5: 1.2M; R_0805_2012Metric
R6: 100k; R_0805_2012Metric
R_hys: 11.5M; R_0805_2012Metric
R_uv1: 5.16M; R_0805_2012Metric
R_uv2: 100k; R_0805_2012Metric
U4: TPS3808G01DBVR; SOT-23-6

Connections:
GND: C5.2, C_ct.2, C_sense.2, C_uvdd.1, R6.2, R_uv2.2, U4.2 (GND)
unnamed: C_ct.1, U4.4 (CT)
unnamed: C_sense.1, R_hys.1, R_uv1.2, R_uv2.1, U4.5 (SENSE)
UVLO_RESET: R_hys.2, U4.1 (~RESET)
V3V3: C_uvdd.2, U4.6 (VDD)
V24_FUSED: R5.1, R_uv1.1
V24_SENSE: C5.1, R5.2, R6.1
