kaanow/volthium_reader/hardware/kicad/schematic/build/sheet_usb.kicad_sch

## KiCad design hardware/kicad/schematic/build/sheet_usb.kicad_sch (2026-08-05)

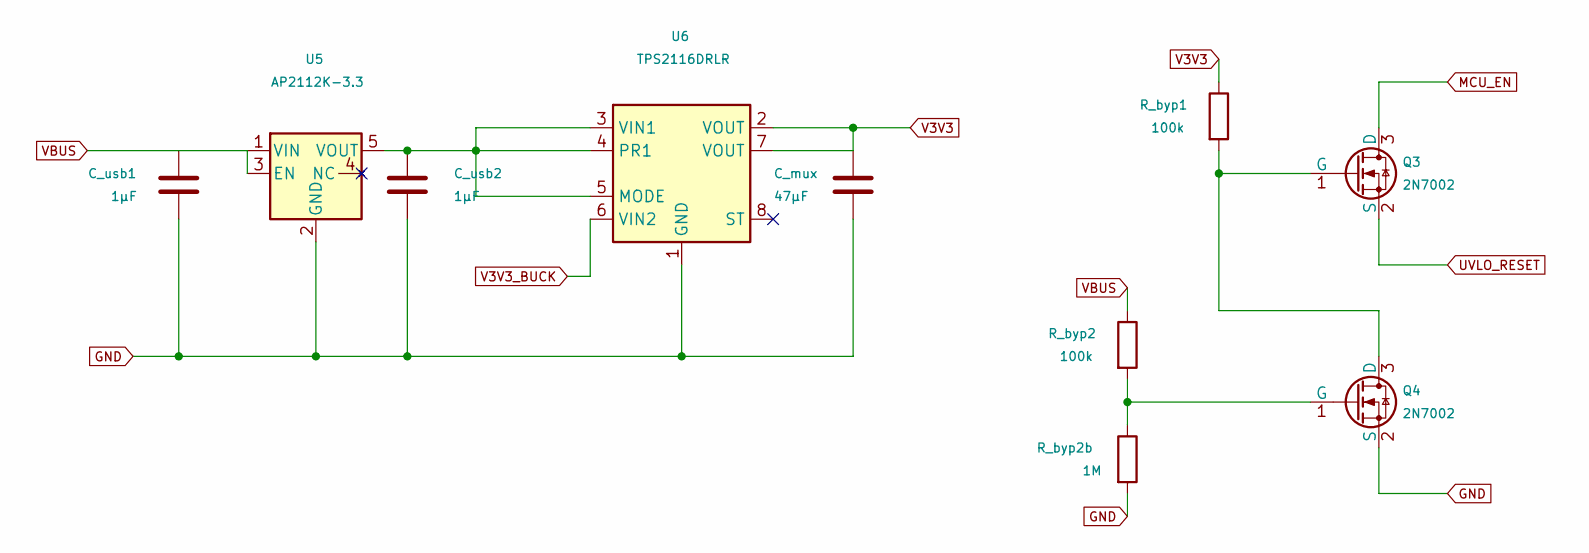
[picture p265: schematic sheet_usb.kicad_sch]

Parts:
C_mux: 47µF; C_0805_2012Metric
C_usb1, C_usb2: 1µF; C_0603_1608Metric
Q3, Q4: 2N7002; SOT-23
R_byp1, R_byp2: 100k; R_0805_2012Metric
R_byp2b: 1M; R_0805_2012Metric
U5: AP2112K-3.3; SOT-23-5
U6: TPS2116DRLR; SOT-583-8

Connections:
GND: C_mux.2, C_usb1.2, C_usb2.2, Q4.2 (S), R_byp2b.2, U5.2 (GND), U6.1 (GND)
MCU_EN: Q3.3 (D)
unnamed: C_usb2.1, U5.5 (VOUT), U6.3 (VIN1), U6.4 (PR1), U6.5 (MODE)
unnamed: Q3.1 (G), Q4.3 (D), R_byp1.2
unnamed: Q4.1 (G), R_byp2.2, R_byp2b.1
UVLO_RESET: Q3.2 (S)
V3V3: C_mux.1, R_byp1.1, U6.2 (VOUT), U6.7 (VOUT)
V3V3_BUCK: U6.6 (VIN2)
VBUS: C_usb1.1, R_byp2.1, U5.1 (VIN), U5.3 (EN)
