kaanow/volthium_reader/hardware/kicad/schematic/build_display/sheet_d_conn.kicad_sch

## KiCad design hardware/kicad/schematic/build_display/sheet_d_conn.kicad_sch (2026-08-05)

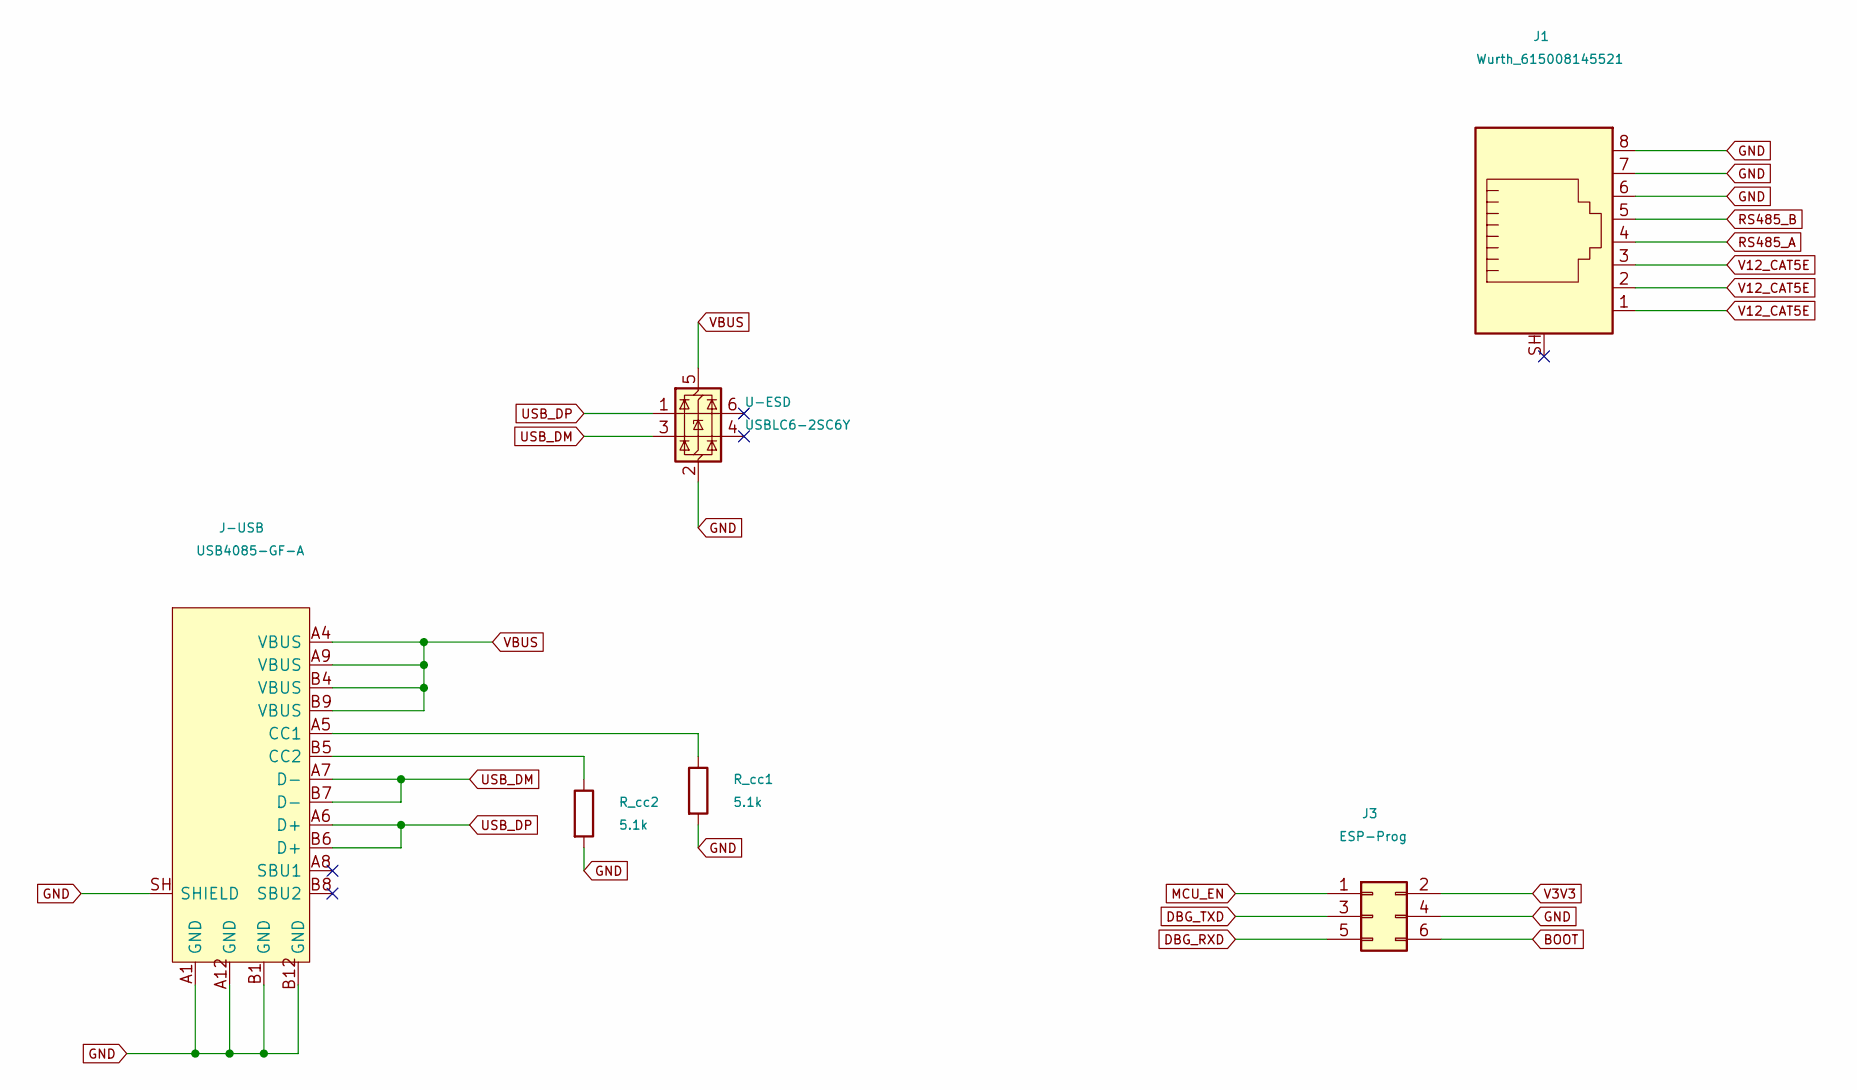
[picture p266: schematic sheet_d_conn.kicad_sch]

Parts:
J1: Wurth_615008145521; J_Wurth_WR-MJ_615008145521
J3: ESP-Prog; IDC-Header_2x03_P2.54mm_Vertical
J-USB: USB4085-GF-A; USB_C_Receptacle_GCT_USB4085
R_cc1, R_cc2: 5.1k; R_0805_2012Metric
U-ESD: USBLC6-2SC6Y; SOT-23-6

Connections:
BOOT: J3.6
DBG_RXD: J3.5
DBG_TXD: J3.3
GND: J1.6, J1.7, J1.8, J3.4, J-USB.A1 (GND), J-USB.A12 (GND), J-USB.B1 (GND), J-USB.B12 (GND), J-USB.SH (SHIELD), R_cc1.2, R_cc2.2, U-ESD.2
MCU_EN: J3.1
unnamed: J-USB.A5 (CC1), R_cc1.1
unnamed: J-USB.B5 (CC2), R_cc2.1
RS485_A: J1.4
RS485_B: J1.5
USB_DM: J-USB.A7 (D-), J-USB.B7 (D-), U-ESD.3
USB_DP: J-USB.A6 (D+), J-USB.B6 (D+), U-ESD.1
V3V3: J3.2
V12_CAT5E: J1.1, J1.2, J1.3
VBUS: J-USB.A4 (VBUS), J-USB.A9 (VBUS), J-USB.B4 (VBUS), J-USB.B9 (VBUS), U-ESD.5
