kaanow/volthium_reader/hardware/kicad/schematic/build_display/sheet_d_mcu.kicad_sch

## KiCad design hardware/kicad/schematic/build_display/sheet_d_mcu.kicad_sch (2026-08-05)

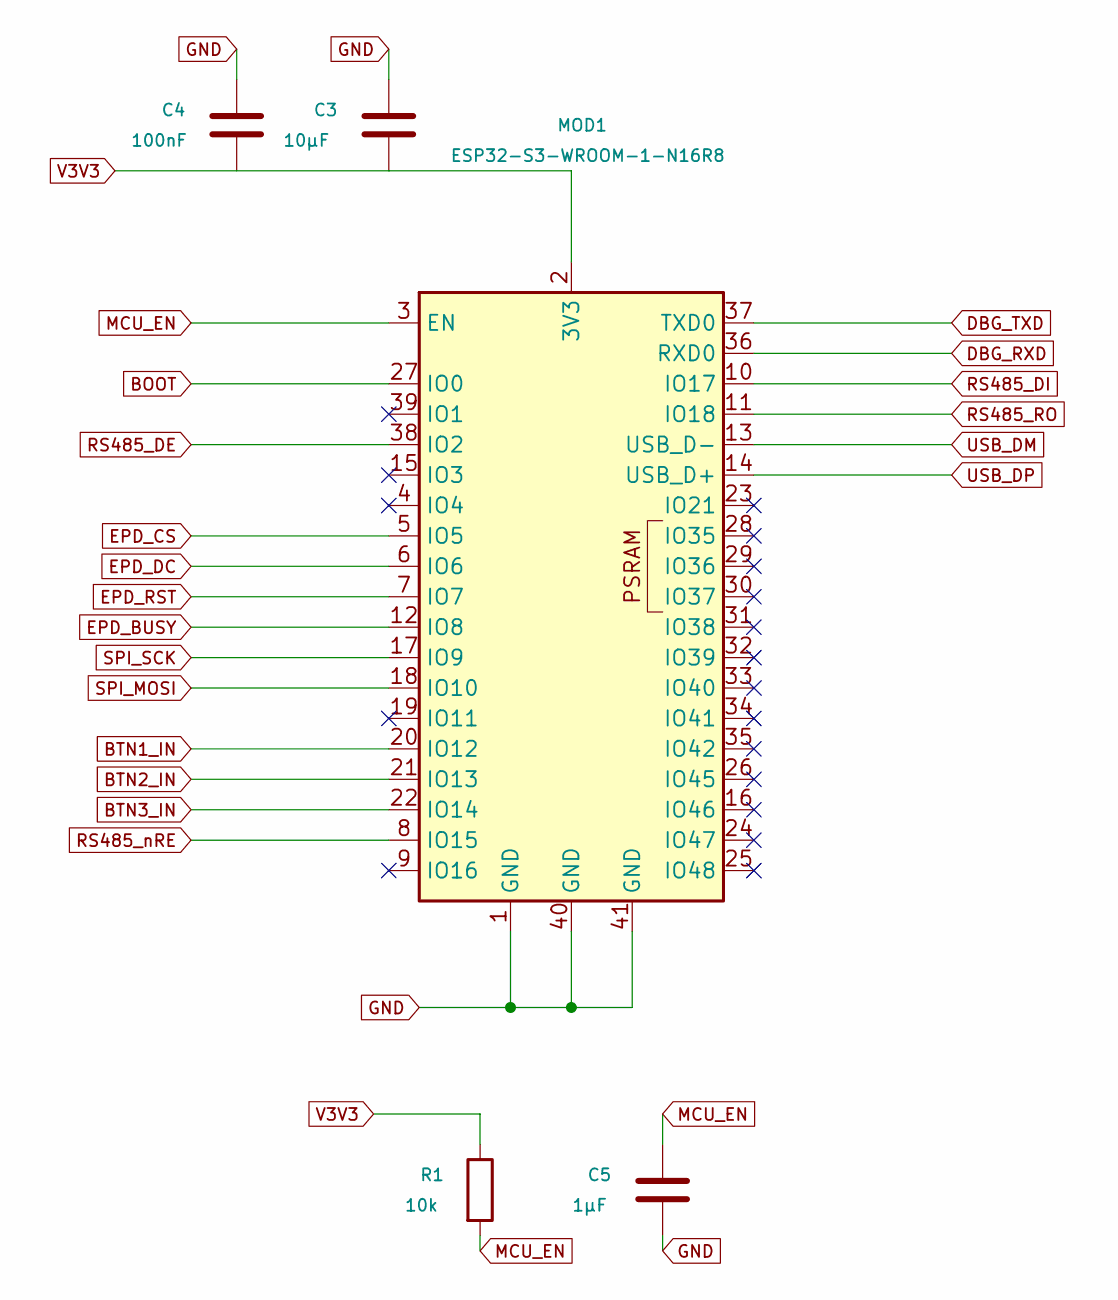
[picture p267: schematic sheet_d_mcu.kicad_sch]

Parts:
C3: 10µF; C_0805_2012Metric
C4: 100nF; C_0603_1608Metric
C5: 1µF; C_0603_1608Metric
MOD1: ESP32-S3-WROOM-1-N16R8; ESP32-S3-WROOM-1_HSvia0.3
R1: 10k; R_0805_2012Metric

Connections:
BOOT: MOD1.27 (IO0)
BTN1_IN: MOD1.20 (IO12)
BTN2_IN: MOD1.21 (IO13)
BTN3_IN: MOD1.22 (IO14)
DBG_RXD: MOD1.36 (RXD0)
DBG_TXD: MOD1.37 (TXD0)
EPD_BUSY: MOD1.12 (IO8)
EPD_CS: MOD1.5 (IO5)
EPD_DC: MOD1.6 (IO6)
EPD_RST: MOD1.7 (IO7)
GND: C3.1, C4.1, C5.2, MOD1.1 (GND), MOD1.40 (GND), MOD1.41 (GND)
MCU_EN: C5.1, MOD1.3 (EN), R1.2
RS485_DE: MOD1.38 (IO2)
RS485_DI: MOD1.10 (IO17)
RS485_RO: MOD1.11 (IO18)
RS485_nRE: MOD1.8 (IO15)
SPI_MOSI: MOD1.18 (IO10)
SPI_SCK: MOD1.17 (IO9)
USB_DM: MOD1.13 (USB_D-)
USB_DP: MOD1.14 (USB_D+)
V3V3: C3.2, C4.2, MOD1.2 (3V3), R1.1
