kaanow/volthium_reader/hardware/kicad/schematic/build_display/sheet_d_periph.kicad_sch

## KiCad design hardware/kicad/schematic/build_display/sheet_d_periph.kicad_sch (2026-08-05)

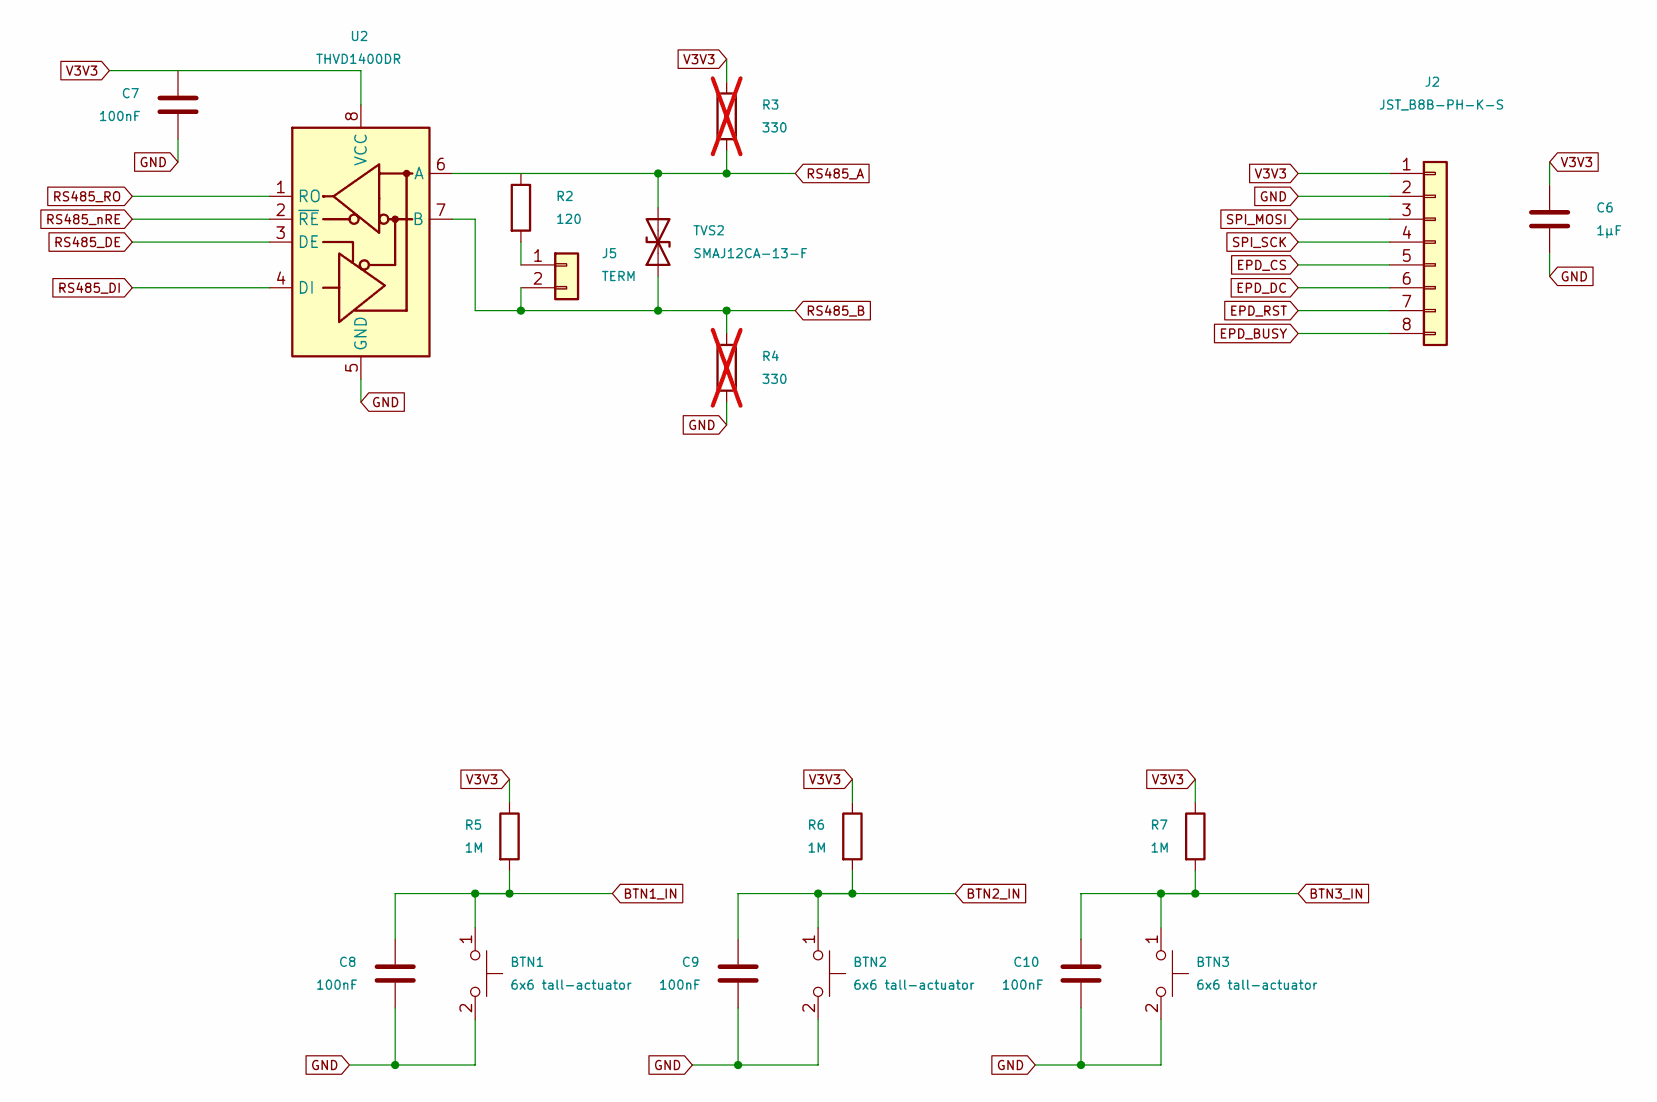
[picture p268: schematic sheet_d_periph.kicad_sch]

Parts:
BTN1, BTN2, BTN3: 6x6 tall-actuator; SW_PUSH_6mm_H13mm
C6: 1µF; C_0603_1608Metric
C7, C8, C9, C10: 100nF; C_0603_1608Metric
J2: JST_B8B-PH-K-S; JST_PH_B8B-PH-K_1x08_P2.00mm_Vertical
J5: TERM; PinHeader_1x02_P2.54mm_Vertical
R2: 120; R_0805_2012Metric
R3, R4: 330; R_0805_2012Metric; not fitted
R5, R6, R7: 1M; R_0805_2012Metric
TVS2: SMAJ12CA-13-F; D_SMA
U2: THVD1400DR; SOIC-8_3.9x4.9mm_P1.27mm

Connections:
BTN1_IN: BTN1.1, C8.1, R5.2
BTN2_IN: BTN2.1, C9.1, R6.2
BTN3_IN: BTN3.1, C10.1, R7.2
EPD_BUSY: J2.8
EPD_CS: J2.5
EPD_DC: J2.6
EPD_RST: J2.7
GND: BTN1.2, BTN2.2, BTN3.2, C6.2, C7.2, C8.2, C9.2, C10.2, J2.2, R4.2, U2.5 (GND)
unnamed: J5.1, R2.2
RS485_A: R2.1, R3.2, TVS2.2 (A2), U2.6 (A)
RS485_B: J5.2, R4.1, TVS2.1 (A1), U2.7 (B)
RS485_DE: U2.3 (DE)
RS485_DI: U2.4 (DI)
RS485_RO: U2.1 (RO)
RS485_nRE: U2.2 (~RE)
SPI_MOSI: J2.3
SPI_SCK: J2.4
V3V3: C6.1, C7.1, J2.1, R3.1, R5.1, R6.1, R7.1, U2.8 (VCC)
