kaanow/volthium_reader/hardware/kicad/schematic/build_display/sheet_d_power.kicad_sch

## KiCad design hardware/kicad/schematic/build_display/sheet_d_power.kicad_sch (2026-08-05)

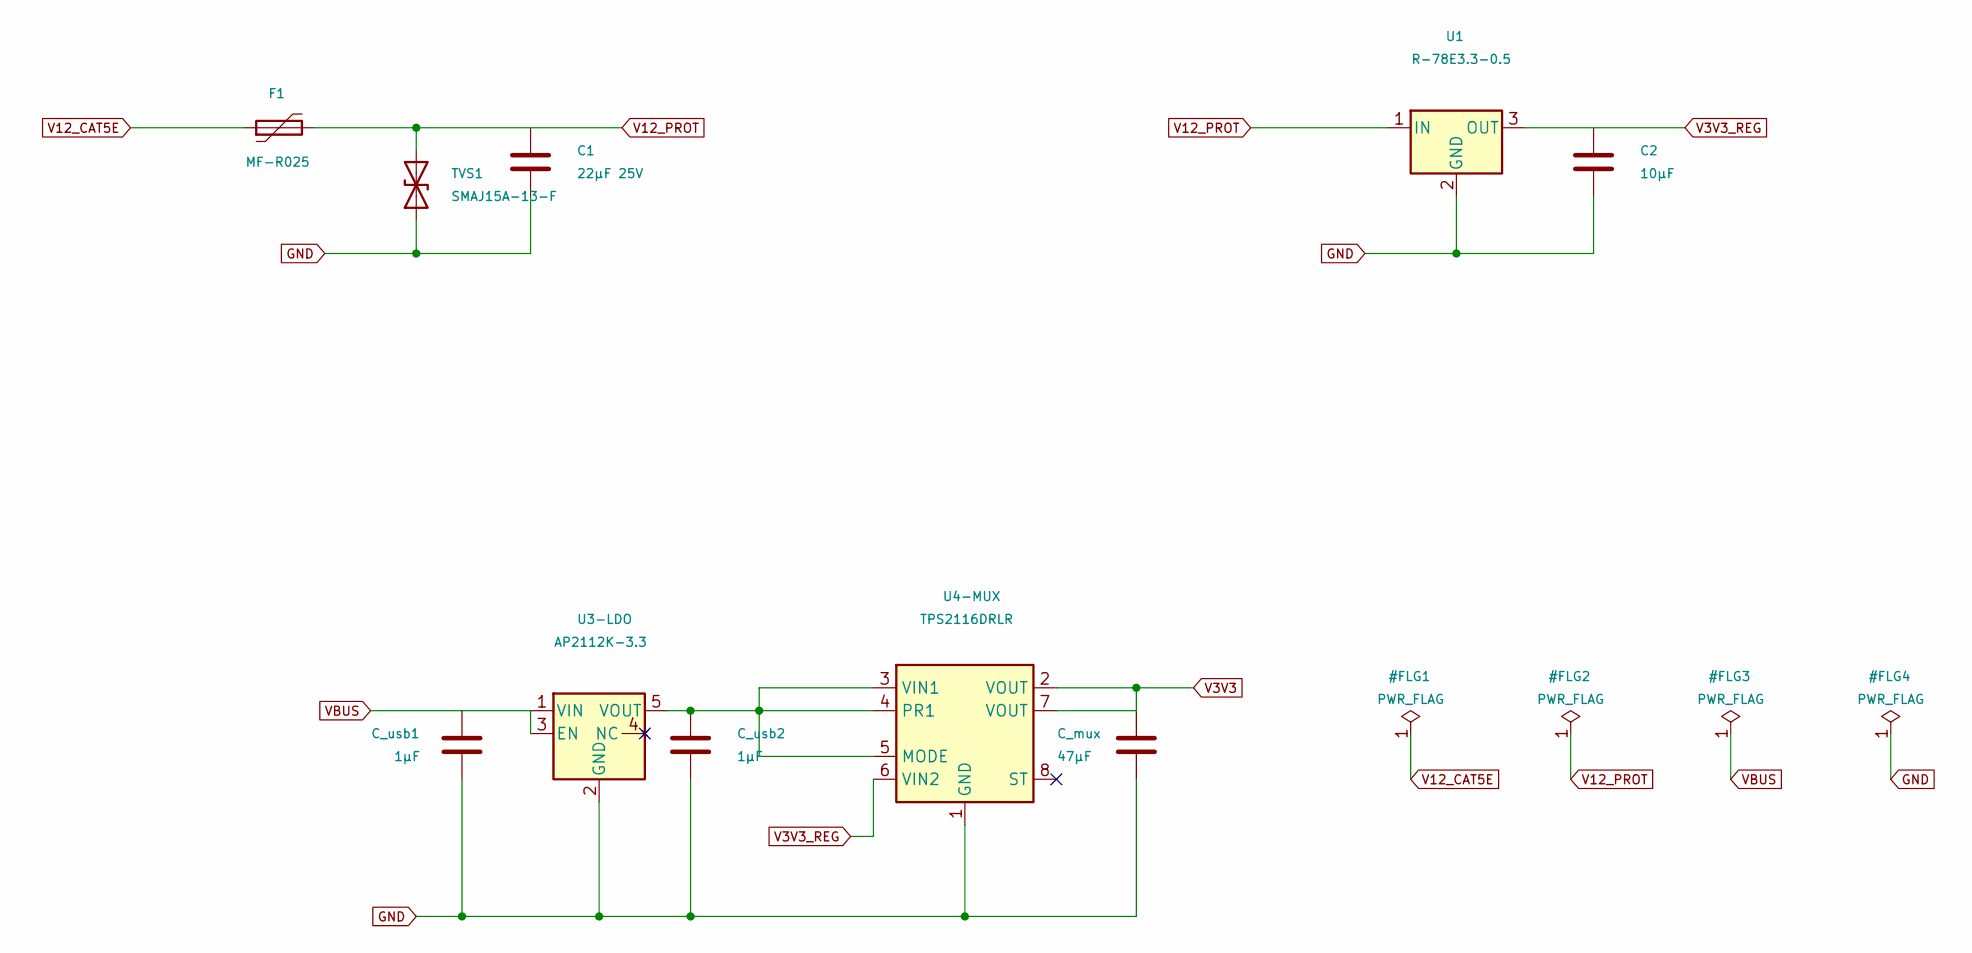
[picture p269: schematic sheet_d_power.kicad_sch]

Parts:
C1: 22µF 25V; C_1210_3225Metric
C2: 10µF; C_0805_2012Metric
C_mux: 47µF; C_0805_2012Metric
C_usb1, C_usb2: 1µF; C_0603_1608Metric
F1: MF-R025; Fuse_Bourns_MF-R025_THT_P5.08mm
TVS1: SMAJ15A-13-F; D_SMA
U1: R-78E3.3-0.5; Converter_DCDC_RECOM_R-78E-0.5_THT
U3-LDO: AP2112K-3.3; SOT-23-5
U4-MUX: TPS2116DRLR; SOT-583-8

Connections:
GND: C1.2, C2.2, C_mux.2, C_usb1.2, C_usb2.2, TVS1.1 (A1), U1.2 (GND), U3-LDO.2 (GND), U4-MUX.1 (GND)
unnamed: C_usb2.1, U3-LDO.5 (VOUT), U4-MUX.3 (VIN1), U4-MUX.4 (PR1), U4-MUX.5 (MODE)
V3V3: C_mux.1, U4-MUX.2 (VOUT), U4-MUX.7 (VOUT)
V3V3_REG: C2.1, U1.3 (OUT), U4-MUX.6 (VIN2)
V12_CAT5E: F1.1
V12_PROT: C1.1, F1.2, TVS1.2 (A2), U1.1 (IN)
VBUS: C_usb1.1, U3-LDO.1 (VIN), U3-LDO.3 (EN)
