kaanow/volthium_reader/volthium/pack.py

"""Two Volthium 12V batteries wired in series → one logical 24V pack."""

from __future__ import annotations

import asyncio
import json
import os
import time
from dataclasses import dataclass, field
from datetime import datetime, timezone
from pathlib import Path
from typing import Optional

from aiobmsble import BMSSample
from aiobmsble.bms.ej_bms import BMS as VolthiumBMS
from bleak import BleakScanner
from bleak.backends.device import BLEDevice


# SC12200G4DPH advertises as "V-12V200Ah-<serial>"
ADV_NAME_PREFIX = "V-12V"


# --- Structured BLE diagnostics ------------------------------------------------
# A per-cycle JSONL trace of everything the radio does: discovery results with
# per-battery RSSI, connect/read/disconnect timings, classified read errors, and
# — most important — the *wedge signature*: a battery that's absent from the
# discovery scan yet still shows a live controller connection. That state is the
# proven failure mode (a leaked BleakClient pins a single-connection BMS so it
# stops advertising; see docs/reliability_failure_modes.md, FM-8). We log it with
# the raw `hcitool con` evidence so a future outage is self-diagnosing rather than
# needing a live operator with bluetoothctl.
#
# The writer uses sealed-segment rotation:
#   - Live file: <path>              (writer appends here)
#   - Sealed:    <path>.NNNN.sealed  (immutable; uploader drains + deletes)
# The uploader never touches the live file so writer and uploader can't race.
# Rotation triggers at 5 MB or after 10 min of accumulation (whichever first),
# so the round-trip Pi → Railway latency is bounded even when the pack is idle.
# HARDWARE-DEP: Pi 3B — default path is a tmpfs (/run/volthium/). Originally
# because the on-board SU16G SD card couldn't sustain the write rate; the
# 2026-07-09 upgrade to a Samsung PRO Endurance 64 GB card removed that
# constraint, but we keep tmpfs because it also gives a clean rotate/upload
# boundary (writer never touches sealed segments, uploader never touches the
# live file, and event logs vanish on reboot — a virtue for privacy).
_REPO_ROOT = Path(__file__).resolve().parents[1]
_EVENT_LOG = Path(
    os.environ.get("VOLTHIUM_BLE_EVENT_LOG", _REPO_ROOT / "data" / "ble_events.jsonl")
)

# Rotation tunables — small enough to keep tmpfs footprint modest, large enough
# that segments amortize the HTTP overhead on the uploader side.
_MAX_SEGMENT_BYTES = 5_000_000     # 5 MB per sealed segment
_MAX_SEGMENT_AGE_S = 600.0         # force rotate every 10 min so latency is bounded
_MAX_SEALED_KEEP = 8               # 8 * 5 MB = 40 MB ceiling if uploader is way behind


class _EventLogWriter:
    """Sealed-segment log writer for BLE diagnostics.

    Instantiate once per process (module-level `_writer` below). All state is
    on the instance so tests can construct fresh writers with a temp path.
    """

    def __init__(
        self,
        log_path: Path,
        max_segment_bytes: int = _MAX_SEGMENT_BYTES,
        max_segment_age_s: float = _MAX_SEGMENT_AGE_S,
        max_sealed_keep: int = _MAX_SEALED_KEEP,
    ) -> None:
        self.log_path = log_path
        self.max_segment_bytes = max_segment_bytes
        self.max_segment_age_s = max_segment_age_s
        self.max_sealed_keep = max_sealed_keep
        self._fh = None
        self._size = 0
        self._opened_at = 0.0
        self._next_seq: Optional[int] = None

    def write_line(self, line: str) -> None:
        """Append one JSONL line; may trigger rotation. Never raises — the
        read loop must survive a broken diagnostics pipeline."""
        try:
            if self._fh is None:
                self._open()
            assert self._fh is not None
            self._fh.write(line)
            self._fh.flush()
            self._size += len(line.encode("utf-8"))
            now = time.monotonic()
            over_size = self._size >= self.max_segment_bytes
            aged_out = (
                self._size > 0
                and (now - self._opened_at) >= self.max_segment_age_s
            )
            if over_size or aged_out:
                self._rotate()
        except Exception:
            # Diagnostics must never propagate — try to recover on next call.
            try:
                if self._fh is not None:
                    self._fh.close()
            except Exception:
                pass
            self._fh = None

    def _open(self) -> None:
        self.log_path.parent.mkdir(parents=True, exist_ok=True)
        self._fh = self.log_path.open("a")
        try:
            self._size = self.log_path.stat().st_size
        except OSError:
            self._size = 0
        self._opened_at = time.monotonic()
        # Inherit the age of pre-existing content. Without this, a crash-looping
        # process resets the age clock every respawn and the age-based rotation
        # NEVER fires — which is exactly how 14 h of wedge diagnostics sat
        # unshipped on the Pi during the 2026-07-12/13 outage (each 5-min-lived
        # process thought its segment was 0 minutes old). Age = now minus the
        # first line's `ts`, so the 10-min latency bound holds across restarts.
        if self._size > 0:
            age = self._first_line_age_s()
            if age is not None and age > 0:
                self._opened_at = time.monotonic() - age
        if self._next_seq is None:
            self._next_seq = self._discover_next_seq()
        # If we're opening onto an already-oversized or already-aged-out live
        # file (e.g. previous process died before it could rotate), seal it
        # right away — then reopen so the caller's pending write still lands
        # (rotate leaves _fh None for the normal in-loop path).
        if self._size >= self.max_segment_bytes or (
            self._size > 0
            and (time.monotonic() - self._opened_at) >= self.max_segment_age_s
        ):
            self._rotate()
            self._fh = self.log_path.open("a")

    def _first_line_age_s(self) -> Optional[float]:
        """Age in seconds of the oldest event in the live file, from its `ts`
        field. Best-effort — None if the line is unreadable/unparseable."""
        try:
            with self.log_path.open("r") as f:
                first = f.readline()
            ts = json.loads(first).get("ts", "")
            dt = datetime.fromisoformat(str(ts).replace("Z", "+00:00"))
            age = (datetime.now(timezone.utc) - dt).total_seconds()
            # Clamp to sanity: a corrupt/future ts must not produce a bogus age.
            return age if 0 <= age <= 7 * 86400 else None
        except Exception:
            return None

    def close(self) -> None:
        """Close the live file handle without sealing (tests, shutdown).
        The next write_line() reopens transparently."""
        try:
            if self._fh is not None:
                self._fh.close()
        except Exception:
            pass
        finally:
            self._fh = None

    def seal_now(self) -> None:
        """Seal the live segment immediately regardless of size/age, so the
        events uploader can ship it. Called on process exit — a logger that's
        about to die for a wedge restart must not take its evidence with it.
        Never raises."""
        try:
            if self._fh is None:
                try:
                    if not self.log_path.exists() or self.log_path.stat().st_size == 0:
                        return
                except OSError:
                    return
                self._open()
            if self._size > 0:
                self._rotate()
        except Exception:
            pass

    def _discover_next_seq(self) -> int:
        max_seq = 0
        for p in self.log_path.parent.glob(f"{self.log_path.name}.*.sealed"):
            # <base>.NNNN.sealed — take the second-to-last dotted component
            try:
                seq = int(p.name.rsplit(".", 2)[-2])
                max_seq = max(max_seq, seq)
            except (ValueError, IndexError):
                pass
        return max_seq + 1

    def _rotate(self) -> None:
        if self._fh is None:
            return
        try:
            self._fh.close()
        except Exception:
            pass
        self._fh = None
        # Enforce the sealed-file cap: if the uploader is behind, drop the
        # oldest sealed file to make room. Older diagnostics are less useful
        # than dropping the whole pipeline into a wedge state.
        self._enforce_cap()
        # Seal the live file by rename. Uploader never touches sealed files
        # until we've done this, so no race.
        assert self._next_seq is not None
        sealed = self.log_path.parent / f"{self.log_path.name}.{self._next_seq:04d}.sealed"
        try:
            if self.log_path.exists():
                self.log_path.rename(sealed)
        except OSError:
            pass
        self._next_seq += 1
        # Reopen fresh — next write_line() will create the live file if needed.
        self._size = 0
        self._opened_at = time.monotonic()

    def _enforce_cap(self) -> None:
        existing = sorted(self.log_path.parent.glob(f"{self.log_path.name}.*.sealed"))
        while len(existing) >= self.max_sealed_keep:
            try:
                existing[0].unlink()
            except OSError:
                break
            existing = existing[1:]


_writer = _EventLogWriter(_EVENT_LOG)


def _reset_writer_for_tests(path: Path) -> _EventLogWriter:
    """Test helper — swap the module-level writer to a fresh path. Returns
    the new writer so tests can also close/inspect it explicitly. Closes the
    outgoing writer's handle so its temp dir can be deleted (Windows can't
    remove open files)."""
    global _writer
    _writer.close()
    _writer = _EventLogWriter(path)
    return _writer


def seal_event_log() -> None:
    """Seal the live event segment so the uploader ships it now rather than
    on the next rotation. Call before any deliberate process exit."""
    try:
        _writer.seal_now()
    except Exception:
        pass


def _event(event: str, **fields) -> None:
    """Append one structured BLE record as JSON. Best-effort — diagnostics must
    never break the read loop, so every failure here is swallowed."""
    try:
        rec = {
            "ts": datetime.now(timezone.utc)
            .isoformat(timespec="milliseconds")
            .replace("+00:00", "Z"),
            "event": event,
            **fields,
        }
        _writer.write_line(json.dumps(rec, default=str) + "\n")
    except Exception:
        pass


# --- Raw BLE frame capture ------------------------------------------------
# Env-gated: VOLTHIUM_CAPTURE_RAW=1 turns on notify-frame taps in the read
# path, streaming hex-encoded BMS responses through the same _event() log for
# later lab replay. Auto-caps at _CAPTURE_CYCLE_CAP pack cycles per process
# so a long-running logger doesn't drown the pipeline in raw traffic.
#
# NOT a hardware-dependent workaround — this exists to gather samples for
# building an offline BMS simulator. As of 2026-07-09 the corpus at
# `data/simulator/pi-barge_raw_frames.jsonl` (~3.9k frames, ~550 full BMS
# records across both batteries) is sufficient for simulator work, so the
# flag is off in production. Turn it back on temporarily to grow the
# corpus for a specific scenario (e.g. a charging-cycle span). Each process
# restart opens a fresh 30-cycle capture window.
_CAPTURE_CYCLE_CAP = 30
_capture_pack_cycles = 0


def _capture_active() -> bool:
    return (
        os.environ.get("VOLTHIUM_CAPTURE_RAW", "0") == "1"
        and _capture_pack_cycles < _CAPTURE_CYCLE_CAP
    )


class _VolthiumBMSTapped(VolthiumBMS):
    """VolthiumBMS with a raw-frame tap on the notify path.

    Overriding `_notification_handler` gives us the raw bytes as bleak
    delivers them — after HCI reassembly but before aiobmsble decodes into
    a BMSSample. Perfect for lab replay: capture (RX bytes, timing) tuples,
    replay them back into a mock BleakClient to reconstruct a session.
    """
    _raw_addr: str = ""

    def _notification_handler(self, *args, **kwargs):
        try:
            # bleak calls (BleakGATTCharacteristic, bytearray). Be defensive.
            data = args[1] if len(args) > 1 else kwargs.get("data", b"")
            _event(
                "raw_frame",
                address=self._raw_addr,
                direction="rx",
                data_hex=bytes(data).hex(),
                data_len=len(bytes(data)),
            )
        except Exception:
            # A broken tap must never break the read.
            pass
        return super()._notification_handler(*args, **kwargs)


def _make_bms(dev: BLEDevice, address: str, keep_alive: bool = True):
    """Construct the BMS instance for a single read cycle, choosing between
    the tapped and plain classes based on whether raw capture is active."""
    if _capture_active():
        bms = _VolthiumBMSTapped(ble_device=dev, keep_alive=keep_alive)
        bms._raw_addr = address.upper()
        return bms
    return VolthiumBMS(ble_device=dev, keep_alive=keep_alive)


async def _run(cmd: list[str], *, timeout: float = 8.0) -> str:
    """Run a short BlueZ CLI command and return combined stdout/stderr. Used for
    observational connection-state checks (no discovery), so it can't collide
    with the single-adapter scan. Never raises — returns an error marker."""
    try:
        proc = await asyncio.create_subprocess_exec(
            *cmd,
            stdout=asyncio.subprocess.PIPE,
            stderr=asyncio.subprocess.STDOUT,
        )
        out, _ = await asyncio.wait_for(proc.communicate(), timeout=timeout)
        return out.decode(errors="replace")
    except Exception as exc:  # noqa: BLE001 — diagnostics, must not propagate
        return f"<cmd {' '.join(cmd)} failed: {type(exc).__name__}: {exc}>"


async def _connected_targets(targets: set[str]) -> set[str]:
    """Of `targets`, which does the controller currently hold an LE connection
    to? Parses `hcitool con`. A target here that we could NOT discover/read this
    cycle is wedged: pinned by a leaked connection so it can't advertise."""
    out = await _run(["hcitool", "con"])
    up = out.upper()
    return {t for t in targets if t.upper() in up}


async def _bluez_connected(addr: str) -> Optional[bool]:
    """BlueZ's *managed* view of whether we hold a connection to `addr`
    (`bluetoothctl info` → `Connected: yes/no`). Distinct from
    `_connected_targets` (raw `hcitool con` / controller view): after a
    cancelled read BlueZ can still hold a Device object + connection handle
    even when the controller shows none — the half-open window we suspect
    behind the dormancy onsets (2026-07-19 investigation). A stale
    `Connected=yes` persisting THROUGH a dormancy would be the smoking gun
    that a `Device.Disconnect()` (not an adapter reset) is the graceful cure.
    `None` if the device isn't in BlueZ's object list at all."""
    out = await _run(["bluetoothctl", "info", addr], timeout=6.0)
    for ln in out.splitlines():
        s = ln.strip()
        if s.startswith("Connected:"):
            return s.split(":", 1)[1].strip().lower() == "yes"
    return None


async def _force_disconnect(addr: str) -> str:
    """Best-effort release of a wedged battery's radio from the Pi side. Clears
    a BlueZ-level lingering connection; an in-process leaked client may re-grab
    it (the logger's wedge self-restart is the backstop for that case).

    HARDWARE-DEP: Pi 3B — this exists because BlueZ leaks connections after
    certain error paths. A cleaner BT stack (e.g. NimBLE on an ESP32 or a
    dedicated USB dongle with a modern controller) wouldn't need this ladder.
    """
    return (await _run(["bluetoothctl", "disconnect", addr], timeout=15.0)).strip()


# Bounds for one battery read. The read is capped so a hung GATT exchange can't
# park a live connection; the disconnect is capped AND verified because
# aiobmsble's disconnect() (basebms.py) has no timeout and silently swallows
# BleakError, while keep_alive=True leaves the link open after a read — together
# the exact recipe that leaks a client and wedges a single-connection BMS (FM-8).
# These were originally conservative because the on-board BCM43438 combo
# chip's HCI transport drops frames under Wi-Fi coexistence pressure (dozens
# of `Frame reassembly failed (-84)` in dmesg per bad session). Since
# 2026-07-09 the reader has been pinned to the TP-Link UB500 dongle
# (RTL8761B on its own USB controller — no Wi-Fi coexistence), so these
# could tighten to ~5 s / ~3 s. Left as-is for headroom against random
# BlueZ hiccups; revisit if we ever want faster per-cycle turnaround.
_READ_TIMEOUT = 15.0
_DISCONNECT_TIMEOUT = 10.0


async def _teardown(bms: VolthiumBMS, address: str) -> None:
    """Guarantee a battery's link is released after a read. This is the
    source-level cure for FM-8: no read may ever leave a connection open.

    Four layers:
      1. Bound aiobmsble's disconnect so a hung teardown can't stall the loop.
      2. Also disconnect the raw BleakClient directly. aiobmsble's disconnect
         silently swallows BleakError and has no timeout on the inner
         _client.disconnect() call (see basebms.py::disconnect); an in-flight
         BleakError can leave the client in a state that auto-reconnects the
         moment the external link drops. Calling bleak directly with our own
         timeout — even if aiobmsble already returned — is what actually
         cleans up its internal state.
      3. Verify at the controller level (`hcitool con`) because both of the
         above can lie.
      4. If the link is somehow still up, force it down via BlueZ.
    Never raises — teardown failures are logged, not propagated.
    """
    key = address.upper()
    t0 = time.monotonic()
    disconnect_error: Optional[str] = None
    inner_disconnect_error: Optional[str] = None
    try:
        await asyncio.wait_for(bms.disconnect(), timeout=_DISCONNECT_TIMEOUT)
    except Exception as exc:  # noqa: BLE001 — teardown must never raise into the loop
        disconnect_error = f"{type(exc).__name__}: {exc}"
    # Belt-and-suspenders: also call the raw BleakClient's disconnect. Idempotent
    # in bleak, but critically it clears the client's internal connection state
    # even if aiobmsble's own disconnect silently failed. Without this, the
    # leaked-client-auto-reconnects-after-external-drop path (FM-8's proven
    # failure mode) can still bite us. HARDWARE-DEP: Pi 3B / BlueZ — needed
    # while aiobmsble's disconnect swallows BleakError; on a stack where the
    # library's own disconnect is reliable, this layer becomes redundant.
    try:
        client = getattr(bms, "_client", None)
        if client is not None:
            await asyncio.wait_for(client.disconnect(), timeout=5.0)
    except Exception as exc:  # noqa: BLE001
        inner_disconnect_error = f"{type(exc).__name__}: {exc}"
    forced = False
    still_connected = False
    try:
        if await _connected_targets({key}):
            await _force_disconnect(address)
            forced = True
            still_connected = bool(await _connected_targets({key}))
    except Exception:  # noqa: BLE001 — verification/force is best-effort
        pass
    # Roll-up boolean for downstream analysis — a "clean" disconnect is one
    # where both library-level calls succeeded, no `hcitool con` force was
    # needed, and the controller confirms no lingering connection. We already
    # log every input; this is just the derived answer to "did the release
    # actually work?" so a Railway query can join wedge onsets against the
    # `disconnect_clean` of the preceding cycle without recomputing the logic.
    disconnect_clean = (
        disconnect_error is None
        and inner_disconnect_error is None
        and not forced
        and not still_connected
    )
    _event(
        "teardown",
        address=key,
        teardown_s=round(time.monotonic() - t0, 2),
        disconnect_error=disconnect_error,
        inner_disconnect_error=inner_disconnect_error,
        forced=forced,
        still_connected=still_connected,
        disconnect_clean=disconnect_clean,
    )


class DiscoveryWedgeError(RuntimeError):
    """Discovery itself failed — classically org.bluez.Error.InProgress, a stuck
    adapter-level discovery session (FM-3). Distinct from a both-batteries-absent
    read failure: this is an adapter/bluetoothd wedge that a process restart will
    NOT clear (it survives across restarts), so the logger must reset the adapter.
    """


async def _default_adapter() -> str:
    """Best-effort name of the BLE controller (e.g. 'hci0') for adapter recovery
    (`hciconfig <hci> reset`). Distinct from the scan/connect adapter selection
    in `_resolve_configured_adapter()` — this one just needs *some* live hci
    name to pass to CLI recovery tools.

    If `VOLTHIUM_ADAPTER` is set and resolved, prefer it: the recovery ladder
    should target the *actual* reader adapter, not whichever one hciconfig
    lists first. Otherwise fall through to the first hci name in `hciconfig`
    output. Ultimate fallback is `hci0`."""
    pinned = await _resolve_configured_adapter()
    if pinned:
        return pinned
    out = await _run(["hciconfig"], timeout=8.0)
    for line in out.splitlines():
        line = line.strip()
        if line.startswith("hci") and ":" in line:
            return line.split(":", 1)[0]
    return "hci0"


# --- Adapter pinning + fallback -------------------------------------------
# `VOLTHIUM_ADAPTER=<mac>` or `=<hci_name>` pins every scan and connect call
# to a specific BLE controller. This matters because bleak/BlueZ picks a
# default adapter by index (usually `hci0`) which is fragile when a machine
# has more than one — e.g. this Pi has both a built-in BCM43438 chip and a
# USB dongle (TP-Link UB500). Their `hci*` numbers even swapped between two
# reboots we observed on 2026-07-09; without pinning, a stray boot could
# route the reader to the flaky internal chip instead of the reliable dongle.
#
# The env vars accept either form:
#   VOLTHIUM_ADAPTER=20:E1:5D:68:30:8B   → resolved to whichever hci owns
#                                          that BD address right now
#   VOLTHIUM_ADAPTER=hci0                → passed straight through
#
# `VOLTHIUM_FALLBACK_ADAPTER` (same forms) names a second-choice controller
# (on the Pi: the internal BCM43438) that the reader switches to WHILE the
# primary is unusable, and automatically switches back off when the primary
# recovers. Degraded but flowing beats a 14-hour outage.
#
# Two lessons from the 2026-07-12/13 outage are baked in here:
#   1. Resolution must verify the adapter with *bluetoothd* (D-Bus), not just
#      `hciconfig` (kernel). After a kernel USB reset the chip can re-enumerate
#      in a state bluetoothd fails to initialize — the kernel lists it, bleak
#      (which talks D-Bus) throws `adapter not found` forever.
#   2. Resolution must be re-verified over time (VERIFY_TTL_S), not cached for
#      the process lifetime — hci indexes change when a dongle re-enumerates.
#
# Unset (macOS dev rig, or a single-adapter Linux box) → the scan/connect
# calls omit the `adapter` kwarg and bleak uses its per-platform default.
_ADAPTER_ENV = "VOLTHIUM_ADAPTER"
_FALLBACK_ADAPTER_ENV = "VOLTHIUM_FALLBACK_ADAPTER"
# VID:PID of the primary adapter's USB dongle, for the replug rung when the
# hci is gone entirely. Default is the TP-Link UB500.
_ADAPTER_USB_ID_ENV = "VOLTHIUM_ADAPTER_USB_ID"
_DEFAULT_ADAPTER_USB_ID = "2357:0604"


def _looks_like_mac(s: str) -> bool:
    """True for `XX:XX:XX:XX:XX:XX` or `XX-XX-XX-XX-XX-XX`, any case."""
    parts = s.replace("-", ":").split(":")
    return len(parts) == 6 and all(
        len(p) == 2 and all(c in "0123456789abcdefABCDEF" for c in p)
        for p in parts
    )


async def _hci_owning_mac(bd_addr: str) -> Optional[str]:
    """Return the hci* name whose BD address matches `bd_addr`, by parsing
    `hciconfig`. Case-insensitive. Returns None if not found (or hciconfig
    is unavailable, e.g. on macOS)."""
    target = bd_addr.replace("-", ":").upper()
    out = await _run(["hciconfig"], timeout=5.0)
    current_hci: Optional[str] = None
    for line in out.splitlines():
        line = line.strip()
        if line.startswith("hci") and ":" in line:
            current_hci = line.split(":", 1)[0]
            continue
        if current_hci and line.upper().startswith("BD ADDRESS:"):
            token = line.split(":", 1)[1].strip().split()[0].upper()
            if token == target:
                return current_hci
    return None


async def _bluez_controllers() -> Optional[set[str]]:
    """BD addresses of the controllers bluetoothd exposes on D-Bus, from
    `bluetoothctl list` — bleak's actual universe of usable adapters. Returns
    None when bluetoothctl is unavailable (macOS dev rig), so callers skip
    the check rather than failing everything."""
    out = await _run(["bluetoothctl", "list"], timeout=5.0)
    if out.startswith("<cmd "):
        return None
    macs: set[str] = set()
    for line in out.splitlines():
        parts = line.split()
        if len(parts) >= 2 and parts[0] == "Controller" and _looks_like_mac(parts[1]):
            macs.add(parts[1].upper())
    return macs


class _AdapterManager:
    """Owns which BLE controller the reader is using right now.

    Responsibilities:
      - Resolve the primary pin (`VOLTHIUM_ADAPTER`) to an hci name, verified
        against BOTH the kernel (`hciconfig`) and bluetoothd (`bluetoothctl
        list`) views. Kernel-only visibility means bleak can't use it.
      - When the primary is unusable, switch to `VOLTHIUM_FALLBACK_ADAPTER`
        (powering it on if needed) so telemetry keeps flowing degraded.
      - Re-verify on a TTL and switch back to the primary automatically the
        moment it's healthy again — then return the fallback to its
        documented steady state (DOWN).
      - While on the fallback, periodically try to *repair* the primary with
        a software USB replug (`maybe_repair_primary`), rate-limited.
    """

    VERIFY_TTL_S = 60.0
    REPLUG_MIN_INTERVAL_S = 600.0

    def __init__(self) -> None:
        self.active: Optional[str] = None       # hci name in use; None = bleak default
        self.active_is_fallback = False
        # None sentinels (not 0.0): time.monotonic() is system uptime on
        # Linux, so a freshly booted Pi has small values and a 0.0 sentinel
        # would make the first minutes look "already verified/attempted".
        self._verified_at: Optional[float] = None
        self._last_replug_at: Optional[float] = None
        self._pin_fail_reported = False         # one adapter_pin_failed per streak
        self._last_emitted: Optional[tuple] = None  # (hci, is_fallback) last announced
        self._lock: Optional[asyncio.Lock] = None

    def invalidate(self) -> None:
        """Force a fresh resolution on the next call — used after any recovery
        action, because hci indexes change when a dongle re-enumerates."""
        self._verified_at = None

    def _cache_fresh(self) -> bool:
        return (
            self._verified_at is not None
            and (time.monotonic() - self._verified_at) < self.VERIFY_TTL_S
        )

    async def resolve(self) -> Optional[str]:
        raw_primary = os.environ.get(_ADAPTER_ENV, "").strip()
        if not raw_primary:
            return None  # unpinned (macOS dev rig) — bleak default
        if self._cache_fresh():
            return self.active
        if self._lock is None:
            self._lock = asyncio.Lock()
        async with self._lock:
            if self._cache_fresh():
                return self.active
            return await self._resolve_locked(raw_primary)

    async def _resolve_locked(self, raw_primary: str) -> Optional[str]:
        hci, why = await self._probe(raw_primary)
        if hci is not None:
            was_fallback = self.active_is_fallback
            self.active, self.active_is_fallback = hci, False
            self._verified_at = time.monotonic()
            self._pin_fail_reported = False
            if self._last_emitted != (hci, False):
                _event(
                    "adapter_restored" if was_fallback else "adapter_pinned",
                    configured=raw_primary,
                    resolved=hci,
                    by="mac" if _looks_like_mac(raw_primary) else "name",
                )
                self._last_emitted = (hci, False)
                if was_fallback:
                    await self._power_down_fallback()
            return hci

        # Primary unusable — report once per streak, then try the fallback.
        if not self._pin_fail_reported:
            self._pin_fail_reported = True
            _event("adapter_pin_failed", configured=raw_primary, reason=why)
        raw_fb = os.environ.get(_FALLBACK_ADAPTER_ENV, "").strip()
        if raw_fb:
            fhci = await self._probe_fallback(raw_fb)
            if fhci is not None:
                self.active, self.active_is_fallback = fhci, True
                self._verified_at = time.monotonic()
                if self._last_emitted != (fhci, True):
                    _event(
                        "adapter_fallback_active",
                        configured=raw_fb,
                        resolved=fhci,
                        primary=raw_primary,
                        primary_fail_reason=why,
                        note=(
                            "reading on the fallback controller while the "
                            "primary is repaired — degraded but flowing"
                        ),
                    )
                    self._last_emitted = (fhci, True)
                return fhci

        # Nothing usable — bleak default. Cache the outcome for a TTL so we
        # don't hammer probes every read cycle while everything is broken.
        _event(
            "adapter_fallback",
            configured=raw_primary,
            pin_failed_reason=why,
            fallback_hci=None,
            fallback_bd_address=None,
            note="no configured adapter usable; bleak default until one returns",
        )
        self.active, self.active_is_fallback = None, False
        self._verified_at = time.monotonic()
        self._last_emitted = (None, False)
        return None

    async def _probe(self, raw: str) -> tuple[Optional[str], str]:
        """(hci, "") when `raw` maps to a controller both the kernel AND
        bluetoothd can see; (None, reason) otherwise."""
        if _looks_like_mac(raw):
            mac = raw.replace("-", ":").upper()
            hci = await _hci_owning_mac(mac)
            if hci is None:
                return None, "no hci with matching BD address"
            controllers = await _bluez_controllers()
            if controllers is not None and mac not in controllers:
                return None, (
                    f"kernel sees {hci} but bluetoothd does not "
                    "(D-Bus adapter object missing — bleak can't use it)"
                )
            return hci, ""
        if raw.startswith("hci"):
            out = await _run(["hciconfig", raw], timeout=5.0)
            if "no such device" in out.lower():
                return None, "no such hci device"
            return raw, ""
        return None, "not a MAC or hci name"

    async def _probe_fallback(self, raw_fb: str) -> Optional[str]:
        """Resolve the fallback controller, powering it on if it's sitting in
        its steady-state DOWN. Returns None if it's unusable too."""
        fhci, _why = await self._probe(raw_fb)
        if fhci is None:
            return None
        if not await _adapter_is_up(fhci):
            await _power_on_adapter(fhci)
            if not await _adapter_is_up(fhci):
                return None
        return fhci

    async def _power_down_fallback(self) -> None:
        """Primary is back — return the fallback controller to its documented
        steady state (DOWN) so its wedge-prone scan state can't confuse BlueZ
        (the internal chip was left UP-and-wedged after the 2026-07-12 episode)."""
        raw_fb = os.environ.get(_FALLBACK_ADAPTER_ENV, "").strip()
        if not raw_fb:
            return
        if _looks_like_mac(raw_fb):
            fhci = await _hci_owning_mac(raw_fb)
        elif raw_fb.startswith("hci"):
            fhci = raw_fb
        else:
            fhci = None
        if fhci and fhci != self.active:
            out = await _run(["sudo", "-n", "hciconfig", fhci, "down"], timeout=10.0)
            _event("fallback_powered_down", hci=fhci, output=out.strip()[:200])

    async def maybe_repair_primary(self) -> Optional[str]:
        """While surviving on the fallback, try to bring the primary back with
        a software USB replug. Rate-limited to one attempt per
        REPLUG_MIN_INTERVAL_S. Returns a description when a replug ran, None
        otherwise. Called every read cycle by the logger — cheap no-op unless
        we're actually degraded and due for an attempt."""
        if not self.active_is_fallback:
            return None
        now = time.monotonic()
        if (
            self._last_replug_at is not None
            and (now - self._last_replug_at) < self.REPLUG_MIN_INTERVAL_S
        ):
            return None
        raw = os.environ.get(_ADAPTER_ENV, "").strip()
        if not raw:
            return None
        # Cheap re-check first — bluetoothd may have recovered it on its own,
        # in which case the next resolve() switches back without a replug.
        hci, _why = await self._probe(raw)
        if hci is not None:
            self.invalidate()
            return None
        self._last_replug_at = now
        action = await replug_usb_adapter()
        self.invalidate()
        return action


_adapter_mgr = _AdapterManager()


def _reset_adapter_state_for_tests() -> _AdapterManager:
    """Swap in a fresh manager (module-level state otherwise leaks between
    tests). Returns it for direct inspection."""
    global _adapter_mgr
    _adapter_mgr = _AdapterManager()
    return _adapter_mgr


async def _resolve_configured_adapter() -> Optional[str]:
    """The adapter the reader should use right now (primary, fallback, or
    None for bleak's default). Kept as a thin wrapper — callers predate the
    manager."""
    return await _adapter_mgr.resolve()


async def maybe_repair_primary() -> Optional[str]:
    """Module-level convenience for the logger loop — see
    _AdapterManager.maybe_repair_primary."""
    return await _adapter_mgr.maybe_repair_primary()


def invalidate_adapter_cache() -> None:
    """Force a fresh adapter resolution on the next scan. The logger calls
    this on every discovery-wedge retry: during the 2026-07-14 21:17 FM-9
    episode the 60 s TTL kept re-latching onto the dead hci2 entry for
    3 minutes after the auto-replug had already produced a healthy adapter
    under a new index — re-probing on every retry closes that window."""
    _adapter_mgr.invalidate()


async def _adapter_kwargs() -> dict:
    """kwargs to splat into bleak scan/connect calls. `{"adapter": "hciN"}`
    when a configured adapter resolved; `{}` otherwise (bleak picks its
    per-platform default — the right thing on macOS)."""
    adapter = await _resolve_configured_adapter()
    return {"adapter": adapter} if adapter else {}


async def _adapter_is_up(hci: str) -> bool:
    """True iff the adapter appears in `hciconfig <hci>` and is not marked
    `DOWN`. Best-effort; a parse failure returns False so we err on the side
    of trying to power it up."""
    out = (await _run(["hciconfig", hci], timeout=5.0)).upper()
    if "NO SUCH DEVICE" in out or hci.upper() not in out:
        return False
    # `DOWN` appears in the status line for a powered-off adapter, `UP` for on.
    if "DOWN" in out:
        return False
    return "UP" in out


async def _power_on_adapter(hci: str) -> str:
    """Bring the adapter up + power it via bluetoothctl. Called after level 1
    or level 2 recovery leaves the controller unpowered — we saw this happen
    live on 2026-07-01 after `systemctl restart bluetooth`.

    Two-step because they cover different failure modes:
      - `hciconfig <hci> up` clears controller-level DOWN state (kernel side)
      - `bluetoothctl power on` sets bluetoothd's managed power flag

    Best-effort; never raises; logs the outcome.
    """
    hci_out = (await _run(["sudo", "-n", "hciconfig", hci, "up"], timeout=15.0)).strip()
    await asyncio.sleep(1.0)
    bt_out = (await _run(["sudo", "-n", "bluetoothctl", "power", "on"], timeout=15.0)).strip()
    _event(
        "adapter_power_on",
        hci=hci,
        hciconfig_up=hci_out[:200],
        bluetoothctl_power=bt_out[:200],
    )
    return f"hciconfig {hci} up; bluetoothctl power on"


# --- USB replug (recovery ladder Level 3) -----------------------------------
# The 2026-07-12/13 outage proved a failure mode no HCI reset or bluetoothd
# restart can fix: the dongle's firmware hangs, the kernel USB-resets it, and
# it re-enumerates in a state bluetoothd can't initialize ("Failed to set
# privacy: Rejected (0x0b)") — kernel-visible, D-Bus-invisible, dead to bleak.
# The only remote cure is a full USB re-enumeration with a fresh firmware
# load, which sysfs `authorized` 0→1 provides (a software unplug/replug).
# Verified live 2026-07-13: readings resumed within seconds.
#
# Scoped strictly to the adapter's own USB device dir — never a hub or any
# other device — so it cannot affect connectivity (the Pi's network is on
# wlan0, not USB, but we don't rely on that).


def _usb_device_dir_for_hci(
    hci: str, base: Path = Path("/sys/class/bluetooth")
) -> Optional[Path]:
    """sysfs USB *device* dir (e.g. .../1-1.5) for a USB-attached hci, by
    following /sys/class/bluetooth/<hci>/device → the USB interface, whose
    parent is the device. None for non-USB adapters or on any error."""
    try:
        real = (base / hci / "device").resolve()
    except OSError:
        return None
    dev = real.parent
    return dev if (dev / "authorized").is_file() else None


def _usb_device_dir_by_id(
    usb_id: str, base: Path = Path("/sys/bus/usb/devices")
) -> Optional[Path]:
    """sysfs USB device dir matching `vid:pid` — the fallback lookup for when
    the dongle is on the bus but its hci is gone entirely."""
    try:
        vid, pid = usb_id.lower().split(":")
    except ValueError:
        return None
    try:
        candidates = list(base.iterdir())
    except OSError:
        return None
    for d in candidates:
        try:
            if (
                (d / "idVendor").read_text().strip().lower() == vid
                and (d / "idProduct").read_text().strip().lower() == pid
                and (d / "authorized").is_file()
            ):
                return d
        except OSError:
            continue
    return None


async def _find_replug_target() -> Optional[Path]:
    """Locate the primary adapter's USB device dir. Prefer following the hci's
    own sysfs link (exact, works when bluetoothd lost the adapter); fall back
    to a VID:PID scan (works when even the hci is gone)."""
    raw = os.environ.get(_ADAPTER_ENV, "").strip()
    if _looks_like_mac(raw):
        hci = await _hci_owning_mac(raw)
        if hci:
            d = _usb_device_dir_for_hci(hci)
            if d is not None:
                return d
    elif raw.startswith("hci"):
        d = _usb_device_dir_for_hci(raw)
        if d is not None:
            return d
    usb_id = os.environ.get(_ADAPTER_USB_ID_ENV, _DEFAULT_ADAPTER_USB_ID)
    return _usb_device_dir_by_id(usb_id)


async def replug_usb_adapter() -> str:
    """Software unplug/replug of the primary USB BLE adapter via its sysfs
    `authorized` toggle — full re-enumeration + fresh firmware load, same
    effect as physically reseating the dongle. Best-effort; never raises;
    emits a `usb_replug` event with the before/after evidence."""
    target = await _find_replug_target()
    if target is None:
        _event(
            "usb_replug",
            ok=False,
            note="no USB device dir found for the primary adapter — "
            "not a USB dongle, or it fell off the bus entirely",
        )
        return "usb replug skipped (no sysfs target)"
    auth = target / "authorized"
    before = await _run(["hciconfig"], timeout=5.0)
    out0 = await _run(["sudo", "-n", "sh", "-c", f"echo 0 > {auth}"], timeout=10.0)
    await asyncio.sleep(2.0)
    out1 = await _run(["sudo", "-n", "sh", "-c", f"echo 1 > {auth}"], timeout=10.0)
    # Re-enumeration + RTL firmware download takes a few seconds; give
    # bluetoothd a moment to register the new controller too.
    await asyncio.sleep(6.0)
    after = await _run(["hciconfig"], timeout=5.0)
    _event(
        "usb_replug",
        ok=True,
        usb_dev=target.name,
        deauthorize=out0.strip()[:150],
        reauthorize=out1.strip()[:150],
        hciconfig_before=before.strip()[:400],
        hciconfig_after=after.strip()[:400],
    )
    _adapter_mgr.invalidate()
    return f"usb replug of {target.name} (authorized 0→1)"


async def _dmesg_bt_tail(
    since_seconds: int = 300, limit: int = 40,
) -> list[str]:
    """Kernel-log tail filtered to lines relevant to a BLE / USB wedge,
    bounded to the last `since_seconds` seconds so a wedge from 2 hours
    ago can't false-positive a classifier check.

    Widened beyond just BT/hci to also catch USB bus events, hub errors,
    power/current spikes, and thermal warnings — any of these can be the
    proximate cause of a chip firmware hang.

    Prefers `journalctl -k` (readable without sudo on Ubuntu, with proper
    time filtering); falls back to `sudo -n dmesg -T` and parses the
    `[Thu Jul 16 …]` timestamps to enforce the same window client-side.
    Best-effort — returns [] on any failure."""
    interesting = (
        "Bluetooth:", "hci0", "hci1", "hci2",
        "usb ", "Resetting usb", "Frame reassembly",
        "reset full-speed", "reset high-speed",
        "over-current", "over-voltage", "under-voltage", "power budget",
        "thermal", "throttl", "hub_port_status",
        "btusb", "brcm",
    )
    # journalctl accepts "N minutes ago" with a space — the earlier form
    # "5min ago" silently failed to parse, sending us to the fallback path
    # which had no time filter.
    minutes = max(1, int(round(since_seconds / 60)))
    since_expr = f"{minutes} minutes ago"
    try:
        out = await _run(
            ["journalctl", "-k", "-q", "--no-pager", f"--since={since_expr}"],
            timeout=3.0,
        )
        if out and "not found" not in out.lower():
            lines = [ln for ln in out.splitlines()
                     if any(tok in ln for tok in interesting)]
            return lines[-limit:]
    except Exception:
        pass
    # Fallback: `dmesg -T` returns everything since boot. Parse the
    # `[Thu Jul 16 18:14:18 2026]` prefix to enforce the window.
    try:
        out = await _run(
            ["sudo", "-n", "dmesg", "-T", "--nopager"], timeout=3.0,
        )
    except Exception:
        return []
    if not out:
        return []
    import re as _re
    import datetime as _dt
    cutoff = _dt.datetime.now() - _dt.timedelta(seconds=since_seconds)
    prefix_re = _re.compile(r"^\[([A-Za-z]{3} [A-Za-z]{3} +\d+ \d+:\d+:\d+ \d+)\]")
    kept = []
    for ln in out.splitlines():
        if not any(tok in ln for tok in interesting):
            continue
        m = prefix_re.match(ln)
        if not m:
            kept.append(ln)  # no parseable timestamp — keep (rare)
            continue
        try:
            ts = _dt.datetime.strptime(m.group(1), "%a %b %d %H:%M:%S %Y")
        except ValueError:
            kept.append(ln)
            continue
        if ts >= cutoff:
            kept.append(ln)
    return kept[-limit:]


async def _hciconfig_snapshot(hci: str) -> dict:
    """Adapter state right now: up/down, powered address, RX/TX counters.
    Blank BD address (00:00:00:00:00:00) or DOWN state is a strong signal
    the chip is not communicating."""
    try:
        out = await _run(["hciconfig", hci], timeout=2.5)
    except Exception as exc:
        return {"error": f"{type(exc).__name__}: {exc}"}
    if not out.strip():
        return {"error": "empty hciconfig output"}
    up = "UP RUNNING" in out.upper()
    down = "DOWN" in out.upper() and not up
    bd = ""
    for ln in out.splitlines():
        s = ln.strip()
        if s.upper().startswith("BD ADDRESS:"):
            bd = s.split(":", 1)[1].strip().split()[0]
            break
    return {
        "up": up,
        "down": down,
        "bd_address": bd,
        "bd_null": bd == "00:00:00:00:00:00",
        "raw": out.strip()[:500],
    }


async def _bluetoothctl_snapshot() -> str:
    """`bluetoothctl show` — Powered/Discovering/UUIDs of the default
    controller. `Discovering: yes` while the reader thinks it's not scanning
    is the classic BlueZ-state-stuck (FM-3) fingerprint."""
    try:
        out = await _run(["bluetoothctl", "show"], timeout=3.0)
    except Exception as exc:
        return f"error: {type(exc).__name__}: {exc}"
    return out.strip()[:800]


async def _lsusb_ub500() -> Optional[bool]:
    """True if the UB500 (VID 2357, PID 0604) is currently on the USB bus,
    False if not, None if lsusb failed. Chip-firmware-hang and dongle-fell-off
    look identical up-stack — this splits them apart."""
    try:
        out = await _run(["lsusb", "-d", "2357:0604"], timeout=2.0)
    except Exception:
        return None
    return bool(out.strip())


async def _usb_dongle_stats() -> dict:
    """Sysfs counters for the reader's USB dongle — 'is the USB layer
    accumulating trouble independent of what BlueZ sees?' Located by
    VID:PID `2357:0604` (TP-Link UB500) rather than by bus path so the
    probe survives dongle re-enumeration after a kernel USB reset."""
    out: dict = {"present": False}
    try:
        import os as _os
        base = "/sys/bus/usb/devices"
        for name in _os.listdir(base):
            devpath = f"{base}/{name}"
            try:
                with open(f"{devpath}/idVendor") as f: vid = f.read().strip()
                with open(f"{devpath}/idProduct") as f: pid = f.read().strip()
            except OSError:
                continue
            if vid != "2357" or pid != "0604":
                continue
            out["present"] = True
            out["busid"] = name
            for attr in ("urbnum", "authorized"):
                try:
                    with open(f"{devpath}/{attr}") as f:
                        out[attr] = f.read().strip()
                except OSError:
                    pass
            break
    except Exception as exc:
        out["error"] = f"{type(exc).__name__}: {exc}"
    return out


async def _wifi_stats() -> dict:
    """Sample WiFi link quality + traffic counters. Motivation for Phase 2C
    (Iter 12 hypothesis): if Family C wedges are actually RF blasts on
    the 2.4 GHz band, WiFi metrics should also degrade — retries climb,
    beacon losses spike, signal quality dips. All-passive read; no probe
    packets sent.

    Reads /proc/net/wireless (link quality / signal / discarded counters)
    and /sys/class/net/wlan0/statistics/{tx,rx}_bytes for traffic volume.
    Sudo-free. On non-wireless hosts (e.g. macOS dev rig) returns {}."""
    out: dict = {}
    try:
        with open("/proc/net/wireless") as f:
            content = f.read()
        # Third line onward has data — format is fixed-column ASCII:
        #   wlan0: 0000  70.  -40.  -256  0  0  0  0  0  0
        # Fields: iface status link level noise
        #         nwid crypt frag retry misc missed_beacon
        for line in content.splitlines()[2:]:
            parts = line.split()
            if not parts or not parts[0].endswith(":"):
                continue
            iface = parts[0].rstrip(":")
            try:
                out[iface] = {
                    "link_quality": float(parts[2].rstrip(".")),
                    "signal_dbm": float(parts[3].rstrip(".")),
                    "noise_dbm": float(parts[4].rstrip(".")),
                    "disc_retry": int(parts[8]),
                    "missed_beacon": int(parts[10]),
                }
            except (ValueError, IndexError):
                continue
            # Traffic volume for this interface
            try:
                with open(f"/sys/class/net/{iface}/statistics/tx_bytes") as fx:
                    out[iface]["tx_bytes"] = int(fx.read().strip())
                with open(f"/sys/class/net/{iface}/statistics/rx_bytes") as fx:
                    out[iface]["rx_bytes"] = int(fx.read().strip())
            except OSError:
                pass
    except OSError:
        return out
    except Exception as exc:
        out["error"] = f"{type(exc).__name__}: {exc}"
    return out


async def _power_and_thermal() -> dict:
    """Sample the Pi's throttled register and SoC temperature. The throttled
    register is a bit-mask that latches under-voltage / freq-cap / temp-cap
    events — an exact source-of-truth "did the PSU sag?" answer that we can't
    get from dmesg alone. Non-zero on a wedge is diagnostic gold: it says the
    USB dongle was probably brownout-hung, not firmware-hung."""
    out = {"throttled_hex": None, "throttled_flags": [], "soc_temp_c": None}
    try:
        raw = (await _run(["vcgencmd", "get_throttled"], timeout=2.0)).strip()
        if "=" in raw:
            hexv = raw.split("=", 1)[1].strip()
            out["throttled_hex"] = hexv
            try:
                bits = int(hexv, 16)
            except ValueError:
                bits = 0
            # Per Pi documentation:
            #   bit  0: under-voltage detected NOW
            #   bit  1: arm freq capped NOW
            #   bit  2: currently throttled
            #   bit  3: soft temp limit active NOW
            #   bit 16: under-voltage has occurred since boot
            #   bit 17: arm freq cap has occurred since boot
            #   bit 18: throttling has occurred since boot
            #   bit 19: soft temp limit has occurred since boot
            flag_names = {
                0: "under_voltage_now",
                1: "freq_capped_now",
                2: "throttled_now",
                3: "soft_temp_limit_now",
                16: "under_voltage_since_boot",
                17: "freq_capped_since_boot",
                18: "throttled_since_boot",
                19: "soft_temp_limit_since_boot",
            }
            out["throttled_flags"] = [
                n for b, n in flag_names.items() if bits & (1 << b)
            ]
    except Exception:
        pass
    try:
        with open("/sys/class/thermal/thermal_zone0/temp") as f:
            out["soc_temp_c"] = int(f.read().strip()) / 1000.0
    except Exception:
        pass
    return out


def _classify_wedge(
    reason: str,
    dmesg: list[str],
    hci_state: dict,
    bctl: str,
    ub500_present: Optional[bool],
    pinned_in_kernel: Optional[str] = None,
    pinned_in_bluez: Optional[bool] = None,
    ambient_peers_silent: Optional[bool] = None,
) -> str:
    """Heuristic layer label for the wedge. The raw fields are the source of
    truth; this string is a triage shortcut for the runbook and dashboards.

    Order matters — most specific evidence first, so a chip hang that also
    causes a "not found" up-stack still classifies as chip-layer.

    The ambient-peers-silent check runs FIRST when available (see Iter 12,
    2026-07-17T01:14): if the independent radio on hci1 also can't hear the
    batteries, this can't be an hci0/BlueZ/our-stack problem — the wedge
    is peer-side or environmental, and the label needs to say so plainly
    so the recovery ladder skips destructive rungs (see log.py gating)."""
    if ambient_peers_silent is True:
        return "peer_silent_ambient_corroborated"
    dm = "\n".join(dmesg)
    if "Resetting usb device" in dm or "reset full-speed" in dm:
        return "kernel_usb_reset_chip_hung"
    if "tx timeout" in dm or "Frame reassembly failed" in dm:
        return "chip_firmware_hci_unresponsive"
    # FM-11: scans complete but hear zero advertisements from any device —
    # the chip's RX path died while its command path still answers, so no
    # dmesg noise and no errors. The reason string carries the diagnosis.
    if "receiver deaf" in reason:
        return "adapter_rx_deaf"
    if ub500_present is False:
        return "ub500_dongle_missing_from_usb"
    # Direct kernel-vs-D-Bus comparison — the 2026-07-12/13 signature: the
    # kernel lists the pinned adapter but bluetoothd never initialized it, so
    # bleak throws `adapter not found` while hciconfig looks perfectly healthy.
    # Cured by a USB replug (recovery Level 3), not by HCI/bluetoothd resets.
    if pinned_in_kernel and pinned_in_bluez is False:
        return "bluez_adapter_object_missing"
    if hci_state.get("bd_null") or (hci_state.get("down") and not hci_state.get("up")):
        return "adapter_down_or_bd_null"
    if "Discovering: yes" in bctl:
        return "bluez_discovery_state_stuck"
    if "InProgress" in reason or "org.bluez.Error.InProgress" in reason:
        return "bluez_discovery_state_stuck"
    if "adapter" in reason.lower() and "not found" in reason.lower():
        return "bluez_adapter_object_missing"
    if "TimeoutError" in reason and hci_state.get("up") and ub500_present:
        return "bms_peer_not_responding"
    return "unclassified"


async def _collect_stack_evidence(
    reason: str, peers: Optional[set[str]] = None,
    is_wedge: bool = False,
) -> dict:
    """Fan out to every layer's state probe in parallel and return one
    normalized evidence dict. Shared by wedge and health snapshots so they
    speak identical JSON — analysis tooling can treat both event kinds the
    same way and just look at the `event` field to know why it fired.

    `peers` is the set of target BLE addresses (batteries). When supplied,
    we consult the ambient scanner's visibility state so classification
    can distinguish "hci0 alone can't see them" (Family B) from "neither
    radio can see them" (peer-silent / environmental)."""
    hci = await _default_adapter()
    (dmesg, hci_state, bctl, ub500, hcicon, ptherm,
     bluez_macs, usb_stats, wifi) = await asyncio.gather(
        _dmesg_bt_tail(),
        _hciconfig_snapshot(hci),
        _bluetoothctl_snapshot(),
        _lsusb_ub500(),
        _run(["hcitool", "con"], timeout=2.0),
        _power_and_thermal(),
        _bluez_controllers(),
        _usb_dongle_stats(),
        _wifi_stats(),
        return_exceptions=True,
    )
    dmesg = dmesg if isinstance(dmesg, list) else []
    hci_state = hci_state if isinstance(hci_state, dict) else {"error": str(hci_state)}
    bctl = bctl if isinstance(bctl, str) else str(bctl)
    hcicon = hcicon if isinstance(hcicon, str) else str(hcicon)
    ptherm = ptherm if isinstance(ptherm, dict) else {}
    bluez_macs = bluez_macs if isinstance(bluez_macs, (set, type(None))) else None
    usb_stats = usb_stats if isinstance(usb_stats, dict) else {}
    wifi = wifi if isinstance(wifi, dict) else {}
    # Kernel-vs-D-Bus comparison for the pinned adapter (see _classify_wedge).
    pinned_raw = os.environ.get(_ADAPTER_ENV, "").strip()
    pinned_in_kernel: Optional[str] = None
    pinned_in_bluez: Optional[bool] = None
    if _looks_like_mac(pinned_raw):
        mac = pinned_raw.replace("-", ":").upper()
        try:
            pinned_in_kernel = await _hci_owning_mac(mac)
        except Exception:
            pinned_in_kernel = None
        if bluez_macs is not None:
            pinned_in_bluez = mac in bluez_macs
    # Ambient second-opinion: does the fallback radio also see the peers
    # missing? Only signal when the caller told us who the peers are AND
    # the ambient scanner has been running long enough to have real data.
    ambient_peers_silent: Optional[bool] = None
    ambient_visibility: Optional[dict] = None
    if peers:
        ambient_visibility = peer_visibility_via_ambient(peers)
        ambient_peers_silent = ambient_says_peers_silent(peers)
    if is_wedge:
        classification = _classify_wedge(
            reason, dmesg, hci_state, bctl, ub500,
            pinned_in_kernel=pinned_in_kernel,
            pinned_in_bluez=pinned_in_bluez,
            ambient_peers_silent=ambient_peers_silent,
        )
    else:
        # Health snapshots run mid-cycle when reads are healthy — most
        # classifier signals (e.g. `Discovering: yes`) are TRUE-and-normal
        # then, not diagnostic. Only the ambient peer-silent signal
        # (which fires on age > 30 s, well past a normal read window) is
        # a real anomaly for a health event.
        if ambient_peers_silent is True:
            classification = "peer_silent_ambient_corroborated"
        else:
            classification = "healthy"
    # If Pi throttling is currently active, upgrade the classification —
    # any recent under-voltage strongly implies the chip hang was electrical,
    # not firmware. Preserve the original label as a hint field.
    thermal_hint: Optional[str] = None
    if ptherm.get("throttled_flags"):
        if "under_voltage_now" in ptherm["throttled_flags"]:
            thermal_hint = classification
            classification = "power_under_voltage_active"
        elif any(f.endswith("_since_boot") for f in ptherm["throttled_flags"]):
            thermal_hint = "throttling_history_present"
    return {
        "reason": reason[:400],
        "classification": classification,
        "classification_notes": thermal_hint,
        "hci": hci,
        "dmesg_bt_tail": dmesg,
        "hciconfig": hci_state,
        "bluetoothctl_show": bctl,
        "ub500_present": ub500,
        "hcitool_con": hcicon.strip()[:500],
        "power_thermal": ptherm,
        "usb_dongle": usb_stats,
        "wifi": wifi,
        "bluez_controllers": sorted(bluez_macs) if bluez_macs is not None else None,
        "pinned_adapter": pinned_raw or None,
        "pinned_in_kernel": pinned_in_kernel,
        "pinned_in_bluez": pinned_in_bluez,
        "active_adapter": _adapter_mgr.active,
        "on_fallback_adapter": _adapter_mgr.active_is_fallback,
        "ambient_peers_silent": ambient_peers_silent,
        "ambient_peer_ages_s": ambient_visibility,
        # Burst-window tagging: a wedge within ~60 s of an ambient burst
        # may have been provoked by the burst's own discovery session
        # (the cross-adapter InProgress stressor). Analysis should count
        # such wedges separately from the steady-state tally.
        "recent_burst_age_s": recent_burst_age_s(),
        "ambient_mode": ambient_mode(),
    }


async def snapshot_stack(
    reason: str, level: int, peers: Optional[set[str]] = None,
) -> None:
    """Gather every layer's state at the moment of a wedge and emit one
    `wedge_snapshot` event containing all of it. Called from every code path
    where the reader gives up on a read cycle — the recovery ladder rungs AND
    the "neither battery found" streak — so nothing that hurts operational
    data quality goes undiagnosed.

    Pass `peers` (the battery BLE addresses) to enable ambient-scanner
    corroboration: the snapshot then carries `ambient_peers_silent` +
    `ambient_peer_ages_s`, and the classifier promotes to
    `peer_silent_ambient_corroborated` when both radios agree the peers
    aren't advertising.

    All probes run in parallel with tight timeouts so the snapshot itself
    can't stall the loop for more than ~3 s in the worst case."""
    evidence = await _collect_stack_evidence(reason, peers=peers, is_wedge=True)
    _event("wedge_snapshot", recovery_level=level, **evidence)


async def emit_stack_health(
    reason: str = "periodic", peers: Optional[set[str]] = None,
) -> None:
    """Emit a `stack_health` event with the same evidence a wedge would
    capture. Fires on a slow cadence (~every 5 min) whether or not anything
    is wrong — the point is to establish a baseline so a future incident
    has "healthy state" to diff against, and so under-voltage becomes
    visible the moment it starts rather than only when it breaks reads."""
    evidence = await _collect_stack_evidence(reason, peers=peers, is_wedge=False)
    _event("stack_health", **evidence)


# --- Ambient advertising scanner (Phase 1 of the wedge-causation dig) -----
# Rationale in docs/investigations/2026-07-16-bt-wedge-causation.md.
#
# When enabled via VOLTHIUM_AMBIENT_ADAPTER, we run a continuous BLE scan on
# a *second* adapter (the internal BT chip on this Pi 3B) filtered to our
# target battery MACs. Every AMBIENT_WINDOW_S we emit an ambient_advertising
# event describing what that independent radio heard in the window —
# per-battery adv packet count, last RSSI, seconds since last seen.
#
# This is the coarsest-grained way to answer "when hci0 says 'batteries
# missing', are the batteries actually silent or is hci0 the problem?"
# without touching the reader path or introducing any new traffic to the
# BMS. It observes the exact same air the reader is trying to use, from a
# radio the reader isn't touching.
AMBIENT_WINDOW_S = 10.0
_AMBIENT_ADAPTER_ENV = "VOLTHIUM_AMBIENT_ADAPTER"
# Mode selector: "continuous" (the original always-on second radio) or
# "burst" (adapter stays powered down; ambient_burst_check() brings it up
# on demand for ~AMBIENT_BURST_S when a recovery decision needs a second
# opinion, then powers it back down). Burst mode exists because starting
# a discovery session on the ambient adapter while the reader adapter has
# one running is itself a demonstrated InProgress-wedge trigger (4/4
# logger restarts with continuous ambient wedged within 22 s — see the
# 2026-07-16 investigation doc). On-demand bursts shrink that exposure to
# the moments where the answer actually changes what we do.
_AMBIENT_MODE_ENV = "VOLTHIUM_AMBIENT_MODE"
AMBIENT_BURST_S = 12.0

# Cross-module state exposing what the ambient scanner has seen. Written by
# the scanner callback (any adv packet updates the target's last-seen mono
# clock); read by the recovery ladder to decide whether escalating past L1
# would actually help. If ambient says the peers are silent, the wedge is
# not chip/BlueZ/our-stack — escalating won't fix it and can only churn
# adapter state. See docs/investigations/2026-07-16-bt-wedge-causation.md
# Iter 12 for the observation that motivated this.
#
# `None` = scanner never saw this target since process start (or hasn't run).
_ambient_last_seen_mono: dict[str, Optional[float]] = {}

# Monotonic timestamp of the last burst's END, plus a lock so overlapping
# recovery paths can't double-book the burst adapter. Wedges that fire
# within ~60 s of a burst are tagged burst-associated in the snapshot so
# the steady-state wedge tally stays clean (a burst's discovery session is
# itself the cross-adapter stressor under investigation).
_last_burst_end_mono: Optional[float] = None
_last_burst_verdict: Optional[bool] = None
_burst_lock = asyncio.Lock()
# Minimum spacing between real bursts. Recovery paths past their threshold
# re-check every cycle (~30-40 s with backoff); without a cooldown a stuck
# stretch would burst on every cycle, and each burst is itself a discovery-
# session stressor. Within the cooldown, callers get the previous verdict.
AMBIENT_BURST_COOLDOWN_S = 60.0


def ambient_mode() -> str:
    """"off" when no ambient adapter is configured; otherwise the value of
    VOLTHIUM_AMBIENT_MODE ("continuous" default, or "burst")."""
    if not os.environ.get(_AMBIENT_ADAPTER_ENV, "").strip():
        return "off"
    mode = os.environ.get(_AMBIENT_MODE_ENV, "").strip().lower()
    return mode if mode in ("continuous", "burst") else "continuous"


def recent_burst_age_s() -> Optional[float]:
    """Seconds since the last ambient burst finished, or None if no burst
    has run this process. Snapshot consumers use this to tag wedges that
    may have been provoked by the burst's own discovery session."""
    if _last_burst_end_mono is None:
        return None
    return round(time.monotonic() - _last_burst_end_mono, 1)


def peer_visibility_via_ambient(addresses: set[str]) -> dict[str, Optional[float]]:
    """Return {address_upper: age_s or None} for each requested target,
    based on the ambient scanner's independent second-opinion. `None` means
    the ambient scanner has never seen that peer this process (or isn't
    running); numeric age is seconds since the last observed adv packet.

    Callers use this to gate recovery: if all targets show `age_s` older
    than the recent window (say, > 30 s), the batteries are peer-silent
    and escalating adapter recovery on hci0 won't help."""
    now = time.monotonic()
    out: dict[str, Optional[float]] = {}
    for a in addresses:
        key = a.upper()
        seen = _ambient_last_seen_mono.get(key)
        out[key] = round(now - seen, 1) if seen is not None else None
    return out


def ambient_says_peers_silent(
    addresses: set[str], max_age_s: float = 30.0
) -> Optional[bool]:
    """True iff the ambient scanner has been running and has NOT seen ANY
    of `addresses` in the last `max_age_s` seconds. False if any peer was
    seen recently. None if ambient hasn't run / no data — caller should
    fall back to legacy behavior (don't skip recovery under uncertainty)."""
    vis = peer_visibility_via_ambient(addresses)
    if all(age is None for age in vis.values()):
        return None
    # If any peer is fresh, we can't call this peer-silent.
    for age in vis.values():
        if age is not None and age <= max_age_s:
            return False
    # All ages are None (never seen) or > max_age_s (stale).
    # Only call "silent" if at least one target has a stale age (we've seen
    # it before, and it's now late). If ALL are None, we still don't know.
    if any(age is not None for age in vis.values()):
        return True
    return None


async def _resolve_ambient_adapter() -> Optional[str]:
    """Map VOLTHIUM_AMBIENT_ADAPTER (MAC or hci name) to an hci name, or
    None if unset / unresolvable. Same shape as the reader-adapter resolver
    but no caching — the ambient adapter is resolved once per process at
    scanner startup."""
    raw = os.environ.get(_AMBIENT_ADAPTER_ENV, "").strip()
    if not raw:
        return None
    if _looks_like_mac(raw):
        try:
            hci = await _hci_owning_mac(raw)
        except Exception:
            hci = None
        if not hci:
            _event(
                "ambient_scanner_unavailable",
                configured=raw,
                reason="no hci with matching BD address",
            )
            return None
        return hci
    if raw.startswith("hci"):
        return raw
    _event(
        "ambient_scanner_unavailable",
        configured=raw,
        reason="not a MAC or hci name",
    )
    return None


async def _acquire_ambient_adapter() -> Optional[tuple[str, bool]]:
    """Resolve + power the ambient adapter for scanning. Returns
    (hci, was_already_up) or None (with an ambient_scanner_unavailable
    event explaining why). Shared by the continuous loop and burst check."""
    hci = await _resolve_ambient_adapter()
    if not hci:
        return None
    reader_hci = await _resolve_configured_adapter()
    if reader_hci and reader_hci == hci:
        _event(
            "ambient_scanner_unavailable",
            resolved=hci,
            reason="same adapter as reader — refusing to double-book radio",
        )
        return None
    # The AdapterManager keeps the fallback adapter POWERED DOWN when the
    # primary is healthy — good for power / RF, bad for our passive listener.
    # Bring it up (hciconfig up + bluetoothctl power on) before starting.
    # If it can't be powered — internal chip broken, cable pulled, etc. —
    # log and quit; the reader's own operation isn't affected.
    was_up = await _adapter_is_up(hci)
    if not was_up:
        try:
            await _power_on_adapter(hci)
        except Exception as exc:
            _event(
                "ambient_scanner_unavailable",
                resolved=hci,
                reason=f"power-on failed: {type(exc).__name__}: {exc}",
            )
            return None
        # Give bluetoothd a moment to notice the adapter came up.
        await asyncio.sleep(2.0)
    return hci, was_up


async def _start_scanner_with_retry(hci: str, cb) -> Optional[BleakScanner]:
    """Start a BleakScanner on `hci`, retrying once through an hciconfig
    reset on `[org.bluez.Error.InProgress]` (a stale discovery session —
    the sole start blocker seen on kwpi). Returns the started scanner or
    None (with ambient_scanner_* events explaining why)."""
    scanner = BleakScanner(detection_callback=cb, adapter=hci)
    try:
        await scanner.start()
        return scanner
    except Exception as exc:
        first_err = f"{type(exc).__name__}: {exc}"
        if "InProgress" not in first_err:
            _event(
                "ambient_scanner_unavailable",
                resolved=hci,
                reason=f"start failed: {first_err}",
            )
            return None
        _event(
            "ambient_scanner_retrying",
            resolved=hci,
            reason=f"first start failed: {first_err}; resetting hci and retrying",
        )
        try:
            await _run(["sudo", "-n", "hciconfig", hci, "reset"], timeout=15.0)
            await asyncio.sleep(2.0)
            await _power_on_adapter(hci)
            await asyncio.sleep(2.0)
            scanner = BleakScanner(detection_callback=cb, adapter=hci)
            await scanner.start()
            return scanner
        except Exception as exc2:
            _event(
                "ambient_scanner_unavailable",
                resolved=hci,
                reason=(
                    f"start failed twice — first: {first_err}; "
                    f"retry after reset: {type(exc2).__name__}: {exc2}"
                ),
            )
            return None


async def ambient_scanner_loop(targets: set[str]) -> None:
    """Long-running task: passive BLE scan on the ambient adapter, filtered
    to `targets` (uppercase MAC strings), emitting one ambient_advertising
    event per AMBIENT_WINDOW_S. Runs until cancelled.

    No-op in burst mode (ambient_burst_check does on-demand scans instead).
    Refuses to run if the ambient adapter is the same as the reader adapter
    (would double-book the radio), or if resolution fails, or if the scan
    can't start — all diagnostics are logged as ambient_scanner_* events
    so the operator can see why the second-opinion signal is missing."""
    if ambient_mode() == "burst":
        _event(
            "ambient_scanner_unavailable",
            reason="mode=burst — continuous scan disabled; on-demand "
                   "ambient_burst_check only",
        )
        return
    acquired = await _acquire_ambient_adapter()
    if not acquired:
        return
    hci, _ = acquired
    targets_upper = {t.upper() for t in targets}
    # Per-target rolling state — reset per emit window.
    state: dict[str, dict] = {
        t: {"count": 0, "last_rssi": None, "last_seen_mono": None,
            "adv_names": set()}
        for t in targets_upper
    }

    def cb(dev: BLEDevice, adv) -> None:
        key = dev.address.upper()
        if key not in state:
            return
        s = state[key]
        s["count"] += 1
        rssi = getattr(adv, "rssi", None)
        if rssi is not None:
            s["last_rssi"] = rssi
        now_mono = time.monotonic()
        s["last_seen_mono"] = now_mono
        # Publish to the cross-module state for recovery-ladder gating.
        _ambient_last_seen_mono[key] = now_mono
        nm = adv.local_name or dev.name
        if nm:
            s["adv_names"].add(nm)

    scanner = await _start_scanner_with_retry(hci, cb)
    if scanner is None:
        return
    _event(
        "ambient_scanner_started",
        adapter=hci,
        targets=sorted(targets_upper),
        window_s=AMBIENT_WINDOW_S,
    )
    try:
        while True:
            await asyncio.sleep(AMBIENT_WINDOW_S)
            now_mono = time.monotonic()
            snapshot: dict = {}
            for addr, s in state.items():
                age_s: Optional[float] = None
                if s["last_seen_mono"] is not None:
                    age_s = round(now_mono - s["last_seen_mono"], 1)
                snapshot[addr] = {
                    "adv_packets": s["count"],
                    "last_rssi": s["last_rssi"],
                    "age_s": age_s,
                    "adv_names": sorted(s["adv_names"]),
                }
                s["count"] = 0
                s["adv_names"] = set()
            _event(
                "ambient_advertising",
                adapter=hci,
                window_s=AMBIENT_WINDOW_S,
                targets=snapshot,
            )
    except asyncio.CancelledError:
        try:
            await scanner.stop()
        except Exception:
            pass
        raise
    except Exception as exc:
        _event(
            "ambient_scanner_died",
            adapter=hci,
            reason=f"{type(exc).__name__}: {exc}",
        )
        try:
            await scanner.stop()
        except Exception:
            pass


async def ambient_burst_check(
    targets: set[str], trigger: str, duration_s: float = AMBIENT_BURST_S,
) -> Optional[bool]:
    """On-demand second opinion: power up the ambient adapter, scan for
    `duration_s`, report whether any of `targets` is advertising, then
    restore the adapter's prior power state. Emits one `ambient_burst`
    event with the full result.

    Returns the peers-silent verdict:
      False — heard ≥1 adv packet from a target (peers NOT silent;
              whatever the reader's problem is, it's reader-side)
      True  — heard zero target packets but ≥1 packet from other BLE
              devices (this radio provably works; peers really silent)
      None  — heard nothing at all (this radio may itself be deaf — no
              conclusion), or the burst couldn't run

    Timing caveat (see investigation doc): a burst samples the air ~15 s
    AFTER wedge onset, not during it. A short peer dormancy can end before
    the burst starts — a False verdict is weaker evidence than continuous
    ambient's was. True verdicts remain decisive.

    Target sightings also feed `_ambient_last_seen_mono`, so the wedge
    snapshot taken after a burst carries real `ambient_peer_ages_s`."""
    global _last_burst_end_mono, _last_burst_verdict
    if _burst_lock.locked():
        # A burst is already in flight (overlapping recovery paths) —
        # don't stack discovery sessions on the burst adapter.
        return None
    age = recent_burst_age_s()
    if age is not None and age < AMBIENT_BURST_COOLDOWN_S:
        # Within cooldown — reuse the previous verdict rather than adding
        # another discovery session to an already-stressed stack.
        return _last_burst_verdict
    async with _burst_lock:
        acquired = await _acquire_ambient_adapter()
        if not acquired:
            return None
        hci, was_up = acquired
        targets_upper = {t.upper() for t in targets}
        state: dict[str, dict] = {
            t: {"count": 0, "last_rssi": None, "adv_names": set()}
            for t in targets_upper
        }
        other_packets = 0

        def cb(dev: BLEDevice, adv) -> None:
            nonlocal other_packets
            key = dev.address.upper()
            if key not in state:
                other_packets += 1
                return
            s = state[key]
            s["count"] += 1
            rssi = getattr(adv, "rssi", None)
            if rssi is not None:
                s["last_rssi"] = rssi
            _ambient_last_seen_mono[key] = time.monotonic()
            nm = adv.local_name or dev.name
            if nm:
                s["adv_names"].add(nm)

        verdict: Optional[bool] = None
        scanner = await _start_scanner_with_retry(hci, cb)
        if scanner is not None:
            try:
                await asyncio.sleep(duration_s)
            finally:
                try:
                    await scanner.stop()
                except Exception:
                    pass
            target_packets = sum(s["count"] for s in state.values())
            if target_packets > 0:
                verdict = False
            elif other_packets > 0:
                verdict = True
            # else: dead air from everyone — inconclusive (None); mirrors
            # the reader's FM-11 rx-deaf logic.
        # Restore prior power state: if the adapter was down before the
        # burst (its default between bursts), put it back down so the
        # radio isn't left running outside the measurement window.
        if not was_up:
            try:
                await _run(["sudo", "-n", "hciconfig", hci, "down"],
                           timeout=10.0)
            except Exception:
                pass
        _last_burst_end_mono = time.monotonic()
        _last_burst_verdict = verdict
        _event(
            "ambient_burst",
            adapter=hci,
            trigger=trigger[:200],
            duration_s=duration_s,
            adapter_was_up=was_up,
            ran=scanner is not None,
            peers_silent=verdict,
            other_adv_packets=other_packets,
            targets={
                t: {
                    "adv_packets": s["count"],
                    "last_rssi": s["last_rssi"],
                    "adv_names": sorted(s["adv_names"]),
                }
                for t, s in state.items()
            },
        )
        return verdict


async def recover_adapter(level: int) -> str:
    """Escalating adapter recovery for a stuck discovery (FM-3/FM-9) that a
    process restart can't fix.
      level 1 — HCI controller reset (clears a wedged discovery session, fast)
      level 2 — full bluetooth.service restart (the proven heavy hammer —
                verified to clear `Discovering: yes` on 2026-06-30)
      level 3 — software USB replug of the primary dongle (full re-enumeration
                + firmware reload; the only remote cure when the chip came
                back from a kernel USB reset in a state bluetoothd can't
                initialize — the 2026-07-12/13 outage)
    Uses passwordless sudo. Best-effort; logs a structured event; never raises.

    Levels 1-2 can leave the adapter powered off (observed live 2026-07-01
    after a level 2 recovery — the logger then loops on "No powered Bluetooth
    adapters found" until manual intervention). To close that gap the recovery
    verifies the adapter is up afterward and calls `hciconfig <hci> up +
    bluetoothctl power on` if not. Level 3 changes the hci index, so it skips
    that check and instead invalidates the adapter cache (all levels do).

    HARDWARE-DEP: BlueZ / RTL8761B — the entire adapter-recovery ladder exists
    because this platform's BT stack periodically wedges at some layer. On a
    healthier stack this function shouldn't need to exist; when we swap
    hardware, this whole function and its callers in scripts/log.py can go.
    """
    if level >= 3:
        action = await replug_usb_adapter()
        _event("adapter_recovery", level=level, action=action, output="")
        return action
    hci = await _default_adapter()
    if level <= 1:
        action = f"hciconfig {hci} reset"
        out = await _run(["sudo", "-n", "hciconfig", hci, "reset"], timeout=20.0)
        await asyncio.sleep(2.0)  # let the controller re-init before next scan
    else:
        action = "systemctl restart bluetooth"
        out = await _run(
            ["sudo", "-n", "systemctl", "restart", "bluetooth"], timeout=30.0
        )
        await asyncio.sleep(5.0)  # bluetoothd + adapter need a moment to come back
    _event("adapter_recovery", level=level, action=action, output=out.strip()[:500])
    # Verify the adapter came back powered. If not, explicitly bring it up —
    # this is the FM-3 gap we just closed after the 2026-07-01 incident.
    if not await _adapter_is_up(hci):
        power_action = await _power_on_adapter(hci)
        action = f"{action}; {power_action}"
    # hci indexes and D-Bus registration can change under any recovery — make
    # the next read cycle re-resolve rather than trusting a stale pin.
    _adapter_mgr.invalidate()
    return action


# Alarm flags packed into the real-time frame's 2-byte status word (vendor
# protocol rev 1.1, Cmd 0x82). `problem_code` = that word masked to bits 2-11,
# i.e. the ten alarm flags below (bits 0-1 are CING/DING charge/discharge
# activity; bits 12-15 are FET states). Names/meanings are the vendor's.
_ALARM_BITS: tuple[tuple[int, str], ...] = (
    (0x004, "cell_overvoltage"),        # VoltH
    (0x008, "cell_undervoltage"),       # VoltL (over-discharge)
    (0x010, "charge_overcurrent"),      # CurrC
    (0x020, "short_circuit"),           # CurrS
    (0x040, "discharge_overcurrent_1"), # CurrD1
    (0x080, "discharge_overcurrent_2"), # CurrD2
    (0x100, "charge_overtemp"),         # TempCH
    (0x200, "charge_undertemp"),        # TempCL
    (0x400, "discharge_overtemp"),      # TempDH
    (0x800, "discharge_undertemp"),     # TempDL
)


def decode_alarms(problem_code: Optional[int]) -> list[str]:
    """Active alarm flag names from a `problem_code`. Empty list = all clear."""
    if not problem_code:
        return []
    return [name for bit, name in _ALARM_BITS if problem_code & bit]


@dataclass
class BatteryReading:
    """One battery's snapshot. None on any field means the BMS didn't send it."""
    address: str
    name: str
    voltage: Optional[float]          # V (sum of cell voltages)
    current: Optional[float]          # A (positive = charging)
    soc: Optional[float]              # %
    remaining_ah: Optional[float]     # Ah remaining (from cycle_charge)
    temperature: Optional[float]      # °C
    cycles: Optional[int]
    cell_voltages: Optional[list[float]]
    delta_voltage: Optional[float]    # max - min cell V
    charging_fet: Optional[bool]
    discharging_fet: Optional[bool]
    problem_code: Optional[int]
    balancer: Optional[int] = None           # internal cell-balancer status word
    heater: Optional[bool] = None            # BMS heater active
    design_capacity: Optional[int] = None    # BMS's configured nameplate Ah
    alarms: list[str] = field(default_factory=list)  # active alarm flags

    @property
    def label(self) -> str:
        """Glanceable battery ID — last two digits of the BMS serial.

        'V-12V200AH-0533' → '33', 'V-12V200AH-0667' → '67'. Falls back to
        last 4 chars of the BLE address if the name isn't structured as
        expected.
        """
        if self.name and "-" in self.name:
            tail = self.name.rsplit("-", 1)[1]
            if tail and tail[-2:].isdigit():
                return tail[-2:]
        return self.address[-4:] if self.address else "??"

    @classmethod
    def from_sample(cls, address: str, name: str, s: BMSSample) -> "BatteryReading":
        return cls(
            address=address,
            name=name,
            voltage=s.get("voltage"),
            current=s.get("current"),
            soc=s.get("battery_level"),
            remaining_ah=s.get("cycle_charge"),
            temperature=(s["temp_values"][0] if s.get("temp_values") else None),
            cycles=s.get("cycles"),
            cell_voltages=s.get("cell_voltages"),
            delta_voltage=s.get("delta_voltage"),
            charging_fet=s.get("chrg_mosfet"),
            discharging_fet=s.get("dischrg_mosfet"),
            problem_code=s.get("problem_code"),
            balancer=s.get("balancer"),
            heater=s.get("heater"),
            design_capacity=s.get("design_capacity"),
            alarms=decode_alarms(s.get("problem_code")),
        )


@dataclass
class PackReading:
    """Combined view of two batteries in series.

    In a series pack the same current flows through both batteries, but each
    cell-group can drift in SOC. For runtime estimation the worst battery
    bounds the pack:
      - charging is finished when the FIRST battery hits 100%
      - discharging is finished when the FIRST battery hits the floor SOC
    """
    a: BatteryReading
    b: BatteryReading
    # Addresses detected wedged this cycle: absent from discovery but still
    # holding a controller connection (leaked-link signature). The logger uses
    # this to escalate to a self-restart — the proven cure — when a force-
    # disconnect won't free an in-process leaked client.
    wedged: list[str] = field(default_factory=list)

    @property
    def pack_voltage(self) -> Optional[float]:
        if self.a.voltage is None or self.b.voltage is None:
            return None
        return self.a.voltage + self.b.voltage

    @property
    def pack_current(self) -> Optional[float]:
        # Series → same current. Average to suppress per-BMS noise.
        vals = [x for x in (self.a.current, self.b.current) if x is not None]
        return sum(vals) / len(vals) if vals else None

    @property
    def pack_power(self) -> Optional[float]:
        if self.pack_voltage is None or self.pack_current is None:
            return None
        return self.pack_voltage * self.pack_current

    @property
    def avg_soc(self) -> Optional[float]:
        vals = [x for x in (self.a.soc, self.b.soc) if x is not None]
        return sum(vals) / len(vals) if vals else None

    @property
    def min_soc(self) -> Optional[float]:
        vals = [x for x in (self.a.soc, self.b.soc) if x is not None]
        return min(vals) if vals else None

    @property
    def max_soc(self) -> Optional[float]:
        vals = [x for x in (self.a.soc, self.b.soc) if x is not None]
        return max(vals) if vals else None


async def discover_volthium(timeout: float = 8.0) -> list[tuple[BLEDevice, str]]:
    """Return [(BLEDevice, advertised_name)] for every Volthium battery in range."""
    found: dict[str, tuple[BLEDevice, str]] = {}

    def cb(dev: BLEDevice, adv) -> None:
        name = adv.local_name or dev.name or ""
        if name.startswith(ADV_NAME_PREFIX):
            found[dev.address] = (dev, name)

    scanner = BleakScanner(detection_callback=cb, **(await _adapter_kwargs()))
    await scanner.start()
    try:
        await asyncio.sleep(timeout)
    finally:
        await scanner.stop()
    return list(found.values())


async def _read_device(dev: BLEDevice, address: str) -> BatteryReading:
    """Connect to an already-discovered device, read one sample, and ALWAYS
    release the link (bounded + verified — see _teardown / FM-8).

    Uses explicit lifecycle rather than `async with`: the context manager's
    __aexit__ disconnect is unbounded and swallows errors, so a hung/failed
    teardown there leaks the client and wedges the BMS. Here the read is
    time-bounded and teardown runs in `finally` no matter how the read exits
    (success, error, or timeout cancellation).
    """
    key = address.upper()
    t0 = time.monotonic()
    # keep_alive=True so async_update() leaves the link open and WE own teardown.
    # keep_alive=True is a workaround for aiobmsble's unbounded disconnect()
    # path — the swallowed-BleakError bug is upstream, not tied to the BT
    # stack. Now on the UB500 (2026-07-09) but the aiobmsble teardown quirk
    # persists, so we still own the disconnect explicitly.
    bms = _make_bms(dev, address, keep_alive=True)
    read_s: Optional[float] = None
    try:
        sample = await asyncio.wait_for(bms.async_update(), timeout=_READ_TIMEOUT)
        read_s = round(time.monotonic() - t0, 2)
    except Exception as exc:  # noqa: BLE001 — re-raised; logged with timing for triage
        # Capture the connection state AT the instant the read failed — this is
        # the half-open discriminator behind the dormancy onsets (2026-07-19
        # investigation). A read that times out *while still connected*
        # (client_connected=True) can leave the peer half-open: our side drops
        # but the BMS still thinks we're connected, so it stops advertising and
        # goes dark for minutes-to-hours. The later teardown's hcitool check
        # reads "not connected" by then, hiding this window — so we sample it
        # here, at the failure, not after. Best-effort; must not mask the read
        # error being re-raised.
        client_connected: Optional[bool] = None
        hci_connected: Optional[bool] = None
        bluez_connected: Optional[bool] = None
        try:
            c = getattr(bms, "_client", None)
            if c is not None:
                client_connected = bool(c.is_connected)
        except Exception:  # noqa: BLE001
            pass
        try:
            hci_connected = bool(await _connected_targets({key}))
        except Exception:  # noqa: BLE001
            pass
        # The three views can disagree — that disagreement IS the diagnosis:
        #   bleak (client) / controller (hcitool) / bluetoothd (bluez).
        # If bluez shows Connected=yes here while hcitool shows nothing, a
        # Device.Disconnect() is the graceful cure (H2). If all three are
        # False, the handle is already gone at the timeout instant and the
        # fix must be upstream — a graceful close before the cancel (H1).
        try:
            bluez_connected = await _bluez_connected(key)
        except Exception:  # noqa: BLE001
            pass
        _event(
            "read_exception",
            address=key,
            error_type=type(exc).__name__,
            error_str=str(exc),
            elapsed_s=round(time.monotonic() - t0, 2),
            client_connected=client_connected,
            hci_connected=hci_connected,
            bluez_connected=bluez_connected,
        )
        raise
    finally:
        await _teardown(bms, address)
    name = dev.name or ""
    reading = BatteryReading.from_sample(address, name, sample)
    _event(
        "read_ok",
        address=key,
        read_s=read_s,
        total_s=round(time.monotonic() - t0, 2),
        voltage=reading.voltage,
        current=reading.current,
        soc=reading.soc,
        temp=reading.temperature,
        problem_code=reading.problem_code,
    )
    return reading


async def read_battery(address: str, *, timeout: float = 20.0) -> BatteryReading:
    """Connect to one battery by address, read one sample, disconnect."""
    dev = await BleakScanner.find_device_by_address(
        address, timeout=timeout, **(await _adapter_kwargs())
    )
    if dev is None:
        raise RuntimeError(f"battery {address} not found in scan")
    return await _read_device(dev, address)


# Once the FIRST target battery is heard, wait at most this long for the rest
# before returning — so a single dormant battery can't force the full `timeout`
# on every cycle and starve the present battery's scan/read cadence. Observed
# 2026-07-23 (partner-following): A dormant → each cycle waited the full 20 s
# for A → B's effective cadence fell ~3× and B's reads began timing out, then B
# followed A into dormancy. A scan that hears NOTHING still runs the full
# timeout, so FM-11 deaf-receiver detection is unaffected.
_SCAN_SETTLE_GRACE_S = 4.0


async def _discover_addresses(
    addresses: set[str], *, timeout: float = 20.0,
    settle_grace: float = _SCAN_SETTLE_GRACE_S,
) -> tuple[dict[str, BLEDevice], int]:
    """Resolve several addresses to BLEDevices in a *single* discovery scan.

    BlueZ permits only one discovery session per adapter, so two concurrent
    `find_device_by_address` scans collide with org.bluez.Error.InProgress
    (CoreBluetooth tolerates it, which is why this only bites on Linux/Pi).
    One shared scan sidesteps that and returns as soon as every target is
    seen, rather than waiting the full timeout.

    Returns (found, ambient) where `ambient` counts advertisement callbacks
    from ANY device, targets or not. A scan that completes with ambient == 0
    heard literally nothing — the FM-11 deaf-receiver signature (the dongle's
    RX path died after a firmware hang while its command path kept answering,
    so nothing ever throws). Callers use it to escalate the recovery ladder.
    """
    wanted = {a.upper() for a in addresses}
    found: dict[str, BLEDevice] = {}
    rssi: dict[str, int] = {}
    names: dict[str, str] = {}
    packets: dict[str, int] = {}
    ambient = 0
    done = asyncio.Event()
    t0 = time.monotonic()
    first_found_at: Optional[float] = None

    def cb(dev: BLEDevice, adv) -> None:
        nonlocal ambient, first_found_at
        ambient += 1
        key = dev.address.upper()
        if key not in wanted:
            return
        # Track RSSI/adv-name/packet-count every time we hear this battery — the
        # RSSI trend leading into a dropout distinguishes a link-budget fade
        # (signal sags toward the floor) from a clean wedge (cuts out at strong
        # signal). adv.rssi is the per-advertisement value (dev.rssi is deprecated).
        rssi[key] = getattr(adv, "rssi", None)
        nm = (getattr(adv, "local_name", None) or dev.name or "")
        if nm:
            names[key] = nm
        packets[key] = packets.get(key, 0) + 1
        if key not in found:
            found[key] = dev
            if first_found_at is None:
                first_found_at = time.monotonic()
            if wanted <= set(found):
                done.set()

    scanner = BleakScanner(detection_callback=cb, **(await _adapter_kwargs()))
    await scanner.start()
    # Return when every target is seen, OR `settle_grace` after the first is
    # heard, OR at the hard timeout — whichever comes first. This only ever
    # SHORTENS a scan: with all targets present `done` fires exactly as before;
    # with none present `first_found_at` stays None and the full timeout runs
    # (FM-11 deaf-scan detection intact); only the one-present-one-absent case
    # is bounded to first-seen + grace instead of the full timeout.
    deadline = t0 + timeout
    try:
        while True:
            now = time.monotonic()
            if done.is_set() or now >= deadline:
                break
            if first_found_at is not None and (now - first_found_at) >= settle_grace:
                break
            await asyncio.sleep(min(0.1, max(0.0, deadline - now)))
    finally:
        await scanner.stop()
    scan_s = round(time.monotonic() - t0, 2)
    for key in sorted(wanted):
        seen = key in found
        # For a battery we could NOT hear this cycle, probe BlueZ's managed
        # connection state. Logged every dormant cycle, this reconstructs the
        # WHOLE dormancy: a stale `Connected=yes` persisting while the peer is
        # silent is the half-open smoking gun (→ Device.Disconnect() is the
        # cure); `Connected=no` throughout means the handle is gone (firmware
        # wedge → prevention/reconnect). Only probed on a miss, so it adds no
        # latency to healthy cycles. See 2026-07-19 dormancy investigation.
        bluez_conn: Optional[bool] = None
        if not seen:
            try:
                bluez_conn = await _bluez_connected(key)
            except Exception:  # noqa: BLE001
                bluez_conn = None
        _event(
            "scan_result",
            address=key,
            seen=seen,
            rssi=rssi.get(key),
            adv_name=names.get(key),
            adv_packets=packets.get(key, 0),
            ambient_adv=ambient,
            scan_s=scan_s,
            bluez_connected=bluez_conn,
        )
    return found, ambient


def _missing_reading(address: str) -> BatteryReading:
    """Placeholder for a battery that wasn't found / couldn't be read this
    cycle. All telemetry fields are None, so PackReading's properties treat it
    as absent and the CSV/wire/cloud/dashboard render it blank (a dash)."""
    return BatteryReading(
        address=address, name="", voltage=None, current=None, soc=None,
        remaining_ah=None, temperature=None, cycles=None, cell_voltages=None,
        delta_voltage=None, charging_fet=None, discharging_fet=None,
        problem_code=None,
    )


# --- Experiment: persistent per-battery connection (dual-adapter A/B test) ----
# One battery can be read over a HELD connection on a dedicated adapter (default
# hci1) instead of the connect/read/disconnect churn on the primary adapter — a
# within-pack controlled test of "does our churn wedge the BMS?": run one battery
# persistent and the other on/off, compare dormancy. Same-pack series current +
# a role-swap crossover control for battery/adapter asymmetry (2026-07-24 design).
# Gated entirely by the caller passing `prefetched` into read_pack; with the
# feature off, none of this runs and read_pack is byte-for-byte the old path.
_persistent_bms: dict[str, object] = {}       # addr -> held BMS (keep_alive=True)


async def _discover_on(hci: Optional[str], addr: str, timeout: float) -> Optional[BLEDevice]:
    """Single-address discovery on a SPECIFIC adapter (the persistent reader must
    not share the primary adapter's discovery — that shared session is FM-2/FM-3
    territory). Returns the BLEDevice or None."""
    key = addr.upper()
    found: dict[str, BLEDevice] = {}
    done = asyncio.Event()

    def cb(dev: BLEDevice, adv) -> None:
        if dev.address.upper() == key:
            found[key] = dev
            done.set()

    scanner = BleakScanner(detection_callback=cb, **({"adapter": hci} if hci else {}))
    await scanner.start()
    try:
        await asyncio.wait_for(done.wait(), timeout=timeout)
    except asyncio.TimeoutError:
        pass
    finally:
        await scanner.stop()
    return found.get(key)


async def _resolve_persist_adapter(spec: Optional[str]) -> Optional[str]:
    """Map VOLTHIUM_PERSIST_HCI (an hci name OR a BD address — prefer the address
    so a reboot that reindexes adapters still targets the right chip) to a live
    hci index, powering it up if it's down. None => bleak's default adapter.

    NOTE: the chosen adapter must NOT also be VOLTHIUM_FALLBACK_ADAPTER, or the
    AdapterManager will power it down under the held connection (an ungraceful
    drop — the wedge trigger). The experiment config frees it from fallback duty."""
    if not spec:
        return None
    hci = spec
    if _looks_like_mac(spec):
        hci = await _hci_owning_mac(spec)
        if not hci:
            _event("persist_adapter_unresolved", spec=spec)
            return None
    try:
        if not await _adapter_is_up(hci):
            await _power_on_adapter(hci)
    except Exception:  # noqa: BLE001 — best-effort power-up; discovery will report if still down
        pass
    return hci


async def persistent_read(
    addr: str, hci: Optional[str], *, timeout: float = _READ_TIMEOUT
) -> Optional[BatteryReading]:
    """Read one battery over a HELD connection on `hci`. Connects + caches on the
    first cycle, then reuses the cached client every cycle with NO teardown —
    collapsing thousands of connect/disconnect cycles/day to ~zero. On any read
    failure the link is torn down + evicted so the next cycle reconnects (which
    needs the battery advertising again). Returns None when unreadable — the
    caller logs that as a dormant cycle. Never raises."""
    key = addr.upper()
    bms = _persistent_bms.get(key)
    if bms is None:
        hci = await _resolve_persist_adapter(hci)   # BD-addr -> live hci, powered up
        dev = await _discover_on(hci, key, timeout)
        if dev is None:
            _event("persist_absent", address=key, hci=hci or "default",
                   note="not advertising — cannot (re)connect")
            return None
        bms = _make_bms(dev, key, keep_alive=True)
        _persistent_bms[key] = bms
        _event("persist_connect", address=key, hci=hci or "default")
    t0 = time.monotonic()
    try:
        sample = await asyncio.wait_for(bms.async_update(), timeout=timeout)
    except Exception as exc:  # noqa: BLE001 — one battery's failure must not sink the loop
        _event("persist_read_fail", address=key, hci=hci or "default",
               error_type=type(exc).__name__, error_str=str(exc)[:120],
               elapsed_s=round(time.monotonic() - t0, 2))
        await _persistent_evict(key)          # drop the (possibly stalled) link
        return None
    name = getattr(getattr(bms, "_ble_device", None), "name", "") or ""
    reading = BatteryReading.from_sample(key, name, sample)
    _event("persist_read_ok", address=key, hci=hci or "default",
           read_s=round(time.monotonic() - t0, 2), soc=reading.soc,
           voltage=reading.voltage, problem_code=reading.problem_code)
    return reading


async def _persistent_evict(addr: str) -> None:
    """Tear down + forget the held connection for one battery (best-effort)."""
    bms = _persistent_bms.pop(addr.upper(), None)
    if bms is not None:
        try:
            await _teardown(bms, addr.upper())
        except Exception:  # noqa: BLE001
            pass


async def persistent_shutdown() -> None:
    """Gracefully release every held connection. MUST be called on SIGTERM: a
    routine restart that just exits would drop the held links ungracefully —
    exactly the half-open teardown we hypothesise wedges the BMS. Draining them
    cleanly first is what keeps deploys from wedging the persistent battery."""
    for key in list(_persistent_bms):
        _event("persist_shutdown_disconnect", address=key)
        await _persistent_evict(key)


async def read_pack(
    addr_a: str, addr_b: str, *, timeout: float = 20.0,
    prefetched: Optional[dict] = None,
) -> PackReading:
    """Read both batteries, tolerating a single-battery dropout.

    A single shared discovery resolves both addresses (BlueZ allows only one
    discovery per adapter, so we can't scan for each battery concurrently),
    then the present batteries are read sequentially on the one radio. A missing
    or unreadable battery becomes an all-None placeholder so the *other*
    battery's telemetry still flows to the CSV/cloud/dashboard — PackReading's
    properties are null-safe, and for a series pack the present battery's current
    is the pack current. Raises only if NEITHER battery can be read, so the
    logger still treats a total blackout as a failed cycle (no empty row).
    """
    global _capture_pack_cycles
    # Snapshot the cycle-cap boundary BEFORE reads run — the reads themselves
    # bump _writer through raw_frame events, but we only advance the pack-cycle
    # counter once per read_pack call so the cap counts pack cycles, not batteries.
    capture_was_active = _capture_active()
    # Persistent-reader integration: any address in `prefetched` was read
    # elsewhere (a held connection on a dedicated adapter), so exclude it from
    # THIS adapter's discovery/read/wedge path. Empty/None => classic
    # both-batteries-on-one-adapter behaviour, unchanged.
    pf = {k.upper(): v for k, v in (prefetched or {}).items()}
    to_discover = {a for a in (addr_a, addr_b) if a.upper() not in pf}
    try:
        devs, ambient = (
            await _discover_addresses(to_discover, timeout=timeout)
            if to_discover else ({}, 0)
        )
    except Exception as exc:  # noqa: BLE001 — log then re-raise; keeps FM-3 self-diagnosing
        # A discovery that throws (classically org.bluez.Error.InProgress — a
        # stuck adapter-level discovery session, FM-3) never reaches the per-
        # cycle events below, so record it here. Note this is an adapter/bluetoothd
        # wedge, NOT the connection-leak wedge (FM-8): a process restart won't
        # clear it — it needs an adapter reset (the watchdog's job).
        _event(
            "scan_error",
            error_type=type(exc).__name__,
            error_str=str(exc),
            note="discovery failed (likely stuck adapter discovery, FM-3 — "
            "needs adapter reset, not a process restart)",
        )
        raise DiscoveryWedgeError(f"{type(exc).__name__}: {exc}") from exc
    if to_discover and not devs and ambient == 0:
        # FM-11: the scan ran without error yet heard NOTHING — not the
        # batteries, not the neighbors' gadgets, nothing. A live 2.4 GHz
        # environment is never actually silent for a whole scan window, so
        # this means the receiver is deaf (observed 2026-07-14: RTL8761B
        # firmware hang at 02:33 left the command path answering but RX
        # dead — 52 min of "neither battery found" that no ladder rung
        # caught because nothing threw). Raise the wedge error so the
        # standard ladder escalates: HCI reset → bluetoothd → USB replug
        # (the cure) → process restart.
        _event(
            "scan_deaf",
            note="scan completed but heard zero advertisements from any "
            "device — BLE receiver presumed deaf (FM-11)",
            scan_timeout_s=timeout,
        )
        raise DiscoveryWedgeError(
            "scan heard zero advertisements from any device — "
            "BLE receiver deaf (FM-11)"
        )
    readings: dict[str, Optional[BatteryReading]] = {}
    for addr in (addr_a, addr_b):
        if addr.upper() in pf:
            readings[addr] = pf[addr.upper()]     # read on the dedicated adapter
            continue
        dev = devs.get(addr.upper())
        if dev is None:
            readings[addr] = None
            continue
        try:
            readings[addr] = await _read_device(dev, addr)
        except Exception as exc:  # noqa: BLE001 — one battery's failure must not sink the other
            _event(
                "read_fail",
                address=addr.upper(),
                error_type=type(exc).__name__,
                error_str=str(exc),
                error_repr=repr(exc),
            )
            readings[addr] = None

    # Wedge detection + leak backstop. Any battery we did NOT read this cycle
    # but that the controller still holds a connection to is wedged: a leaked /
    # half-open link is pinning its single-connection BMS so it can't advertise
    # (the proven FM-8 failure). Record the raw evidence, try to free its radio,
    # and surface the address so the logger can escalate to a self-restart (the
    # cure we verified) if a force-disconnect won't shake an in-process leak.
    unread = ({addr_a.upper(), addr_b.upper()} - set(pf)) - {
        addr.upper() for addr, r in readings.items() if r is not None
    }
    wedged: list[str] = []
    if unread:
        connected = await _connected_targets(unread)
        if connected:
            evidence = (await _run(["hcitool", "con"])).strip()
            for addr in sorted(connected):
                wedged.append(addr)
                _event(
                    "wedge_detected",
                    address=addr,
                    note="absent from discovery but controller still connected "
                    "— leaked link pinning the BMS radio (FM-8)",
                    hcitool_con=evidence,
                )
                result = await _force_disconnect(addr)
                _event("force_disconnect", address=addr, result=result)

    # Advance the raw-capture pack-cycle counter (once per read_pack call, not
    # per battery). Emit a boundary marker on the cycle that flips capture off
    # so a downstream consumer can find the end of the sample stream cleanly.
    if capture_was_active:
        _capture_pack_cycles += 1
        if _capture_pack_cycles >= _CAPTURE_CYCLE_CAP:
            _event(
                "raw_capture_exhausted",
                cycles_captured=_capture_pack_cycles,
                cap=_CAPTURE_CYCLE_CAP,
                note="raw capture disabled until next process restart",
            )

    if readings[addr_a] is None and readings[addr_b] is None:
        _event("cycle_done", outcome="both_down", wedged=wedged)
        raise RuntimeError(f"neither battery found in scan (a={addr_a} b={addr_b})")
    _event(
        "cycle_done",
        outcome="ok" if (readings[addr_a] and readings[addr_b]) else "partial",
        a_read=readings[addr_a] is not None,
        b_read=readings[addr_b] is not None,
        wedged=wedged,
    )
    return PackReading(
        a=readings[addr_a] or _missing_reading(addr_a),
        b=readings[addr_b] or _missing_reading(addr_b),
        wedged=wedged,
    )
