kaanow/volthium_reader/volthium/estimator.py

"""Time-to-full / time-to-empty estimator with smoothing."""

from __future__ import annotations

import time
from collections import deque
from dataclasses import dataclass
from datetime import datetime
from typing import Optional, Union

from .pack import PackReading


@dataclass
class Estimate:
    state: str                 # "charging" | "discharging" | "idle" | "full"
    smoothed_current: float    # A, positive = charging
    smoothed_power: float      # W
    minutes_remaining: Optional[float]   # to full (charging) or to floor (discharging)
    target_label: str          # "full" | "10%" | "—"
    displayed_ah: Optional[float] = None  # only populated in hybrid mode


class Estimator:
    """Exponential moving average on current + power, then linear extrapolation.

    Two heuristics worth knowing:
      - We extrapolate against the limiting battery: the *higher* SOC bounds
        charging time, the *lower* SOC bounds discharging time.
      - Anything under |I| ≈ 0.5 A is treated as idle so the time doesn't go
        to ±infinity when the inverter is off and there's no sun.
    """

    def __init__(
        self,
        capacity_ah: float = 200.0,    # per battery; same for a series pack
        floor_soc: float = 10.0,       # % — "empty" floor
        ceiling_soc: float = 95.0,     # % — "full" for time-remaining math.
                                       # 95 % matches LiFePO4 absorption-onset
                                       # and is what we banner "FULL" at.
                                       # The remaining 5 % is CV-taper time
                                       # which is hard to predict linearly.
        idle_current_a: float = 0.5,
        alpha: float = 0.15,           # EMA smoothing — lower = smoother
        window: int = 20,              # also keep a window for diagnostics
        current_calibration: float = 1.0,  # multiplier on reported pack current
                                       # when computing time-to-X.
                                       # Empirical finding on the Barge Inn
                                       # pair: BMS-reported Ah accumulation
                                       # is non-linear vs current — see
                                       # docs/hardware/bms_calibration.md.
                                       # A single multiplier can't capture
                                       # the sign flip between bulk-charge
                                       # (ratio 1.12) and trickle (0.94).
                                       # Use hybrid mode below for the
                                       # right answer.
        use_remaining_ah_anchor: bool = False,
                                       # If True, maintain an internal
                                       # remaining_ah estimator that
                                       # integrates pack_current * dt
                                       # between samples and re-anchors
                                       # to the BMS-reported remaining_ah
                                       # whenever it ticks. This gives
                                       # smooth UI updates while staying
                                       # honest to the BMS's coulomb-
                                       # counting truth. Recommended for
                                       # production firmware.
        anchor_integrator_weight: float = 0.8,
                                       # When the BMS ticks remaining_ah,
                                       # we blend new_displayed_ah =
                                       #   w * integrator + (1-w) * anchor.
                                       # 0.8 = trust integrator 80%,
                                       # use anchor as a slow correction.
                                       # Lower = snap harder to BMS truth.
    ) -> None:
        self.capacity_ah = capacity_ah
        self.floor_soc = floor_soc
        self.ceiling_soc = ceiling_soc
        self.idle_current_a = idle_current_a
        self.alpha = alpha
        self.current_calibration = current_calibration
        self.use_remaining_ah_anchor = use_remaining_ah_anchor
        self.anchor_integrator_weight = anchor_integrator_weight
        self._ema_i: Optional[float] = None
        self._ema_p: Optional[float] = None
        self._recent: deque[float] = deque(maxlen=window)
        # Hybrid-mode state:
        self._displayed_ah: Optional[float] = None
        self._last_anchor_ah: Optional[float] = None
        self._last_ts: Optional[float] = None        # seconds (monotonic or unix)

    def update(
        self,
        reading: PackReading,
        ts: Union[datetime, float, None] = None,
    ) -> Estimate:
        """Step the estimator with a new reading.

        ts: optional timestamp for hybrid-mode time-integration. Accepts
        a datetime, a unix/monotonic float, or None (uses time.monotonic()).
        """
        i = reading.pack_current
        p = reading.pack_power

        if i is None:
            return Estimate("unknown", 0.0, 0.0, None, "—")

        self._ema_i = i if self._ema_i is None else (
            self.alpha * i + (1 - self.alpha) * self._ema_i
        )
        if p is not None:
            self._ema_p = p if self._ema_p is None else (
                self.alpha * p + (1 - self.alpha) * self._ema_p
            )
        self._recent.append(i)

        si = self._ema_i
        sp = self._ema_p or 0.0
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
